MLAB-project/Modules/comm_serial/I2CHUB01A/README.md

[Czech](./README.cs.md)
<!--- module --->
# I2CHUB01A
<!--- Emodule --->

<!--- subtitle ---> I2C (TWI) bus HUB <!--- Esubtitle --->

I2CHUB01A

<!--- description ---> The module allow conecting multiple I2C devices together. It does not consist any configurable IO. It is a simple bus multiplyer.<!--- Edescription --->
