MLAB-project/Modules/human_interface/LEDROBOT/README.cs.md

[English](./README.md)
<!--- module --->
# LEDROBOT
<!--- Emodule --->

<!--- subtitle --->Sloupec LED diod<!--- Esubtitle --->

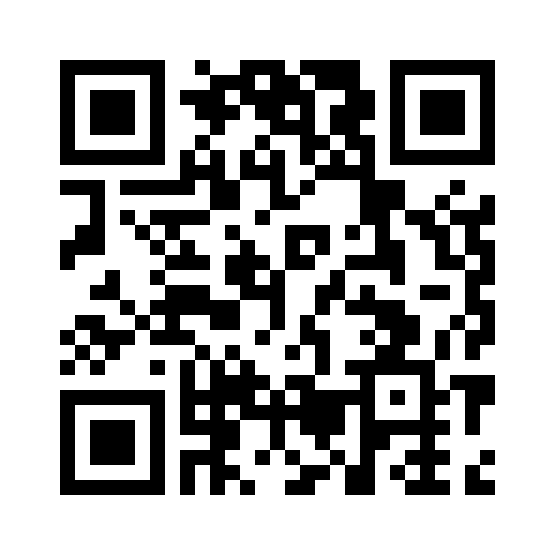
[picture p7: human_interface/LEDROBOT/doc/img/LEDROBOT_QRcode.png]
LEDROBOT


<!--- description --->Modul obsahuje piezo, napětový stabilizátor, vypínač a rozvod 5V napájení.<!--- Edescription --->
