MLAB-project/Modules/human_interface/LEDROBOT/README.md

[Czech](./README.cs.md)
<!--- module --->
# LEDROBOT
<!--- Emodule --->

<!--- subtitle --->Simple robot power control and LED indicator unit <!--- Esubtitle --->

LEDROBOT

<!--- description --->This module contain switch, LEDs, voltage regulator, beeper and 5V power hub.<!--- Edescription --->
