MLAB-project/Modules/power_supply/TPS63000/README.md

[Czech](./README.cs.md)
<!--- module --->
# TPS63000
<!--- Emodule --->

<!--- subtitle ---> UP/DOWN converter <!--- Esubtitle --->

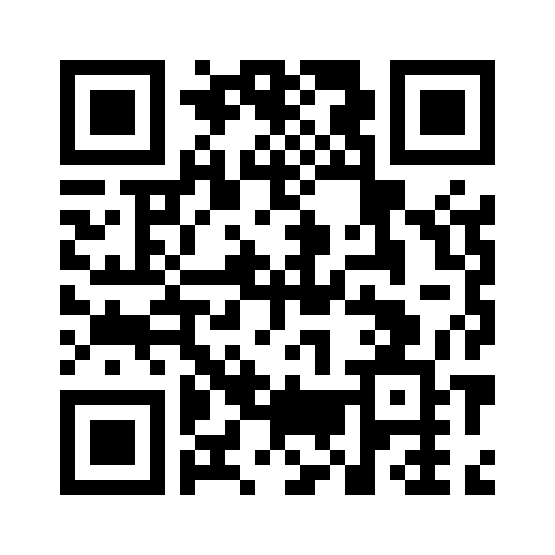
[picture p8: power_supply/TPS63000/doc/img/TPS63000_QRcode.png]
TPS63000


<!--- description ---> High efficiency switched adjustable power unit step-down and step-up in one module.<!--- Edescription --->
