MLAB-project/Modules/power_supply/TPS61200/README.md

[Czech](./README.cs.md)
<!--- module --->
# TPS61200
<!--- Emodule --->

<!--- subtitle ---> UP/DOWN converter <!--- Esubtitle --->

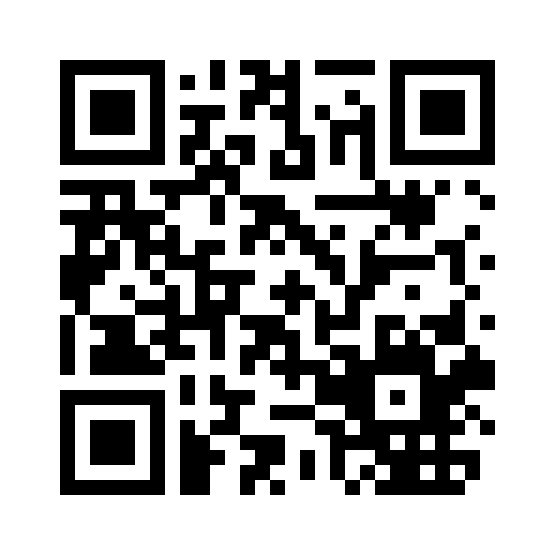
[picture p9: power_supply/TPS61200/doc/img/TPS61200_QRcode.png]
TPS61200


<!--- description ---> Switched adjustable power unit step-down and step-up in one module.<!--- Edescription --->
