MLAB-project/Modules/power_supply/TPS61170/README.md

[Czech](./README.cs.md)
<!--- module --->
# TPS61170
<!--- Emodule --->

<!--- subtitle ---> Step-up converter <!--- Esubtitle --->

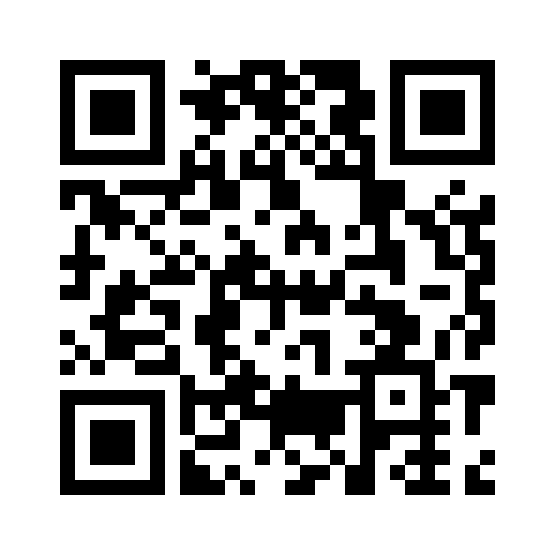
[picture p10: power_supply/TPS61170/doc/img/TPS61170_QRcode.png]
TPS61170


<!--- description ---> Switched adjustable DC/DC power unit.<!--- Edescription --->
