MLAB-project/Modules/power_supply/MAX1797/README.cs.md

[English](./README.md)
<!--- module --->
# MAX1797
<!--- Emodule --->

<!--- subtitle ---> Step-up měnič<!--- Esubtitle --->

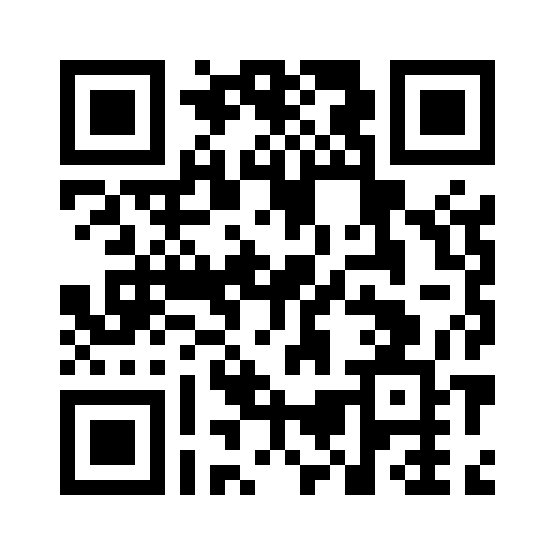
[picture p11: power_supply/MAX1797/doc/img/MAX1797_QRcode.png]
MAX1797


<!--- description ---> Zvyšující spínaný napájecí modul do 5V 1A.<!--- Edescription --->
