MLAB-project/Modules/power_supply/MAX1797/README.md

[Czech](./README.cs.md)
<!--- module --->
# MAX1797
<!--- Emodule --->

<!--- subtitle ---> Step-up converter <!--- Esubtitle --->

MAX1797

<!--- description ---> Switched power unit up to 5V and 1A.<!--- Edescription --->
