MLAB-project/Modules/cpld_fpga/S3AN01A/README.md

<!--- PrjInfo ---> <!--- Please remove this line after manually editing --->
<!--- 00a56be08b96043df9e37d6aff7b6990 --->
<!--- Created:20170112-18:22: ---> 
<!--- Author:Mlab: ---> 
<!--- AuthorEmail:mlab@mlab.cz: ---> 
<!--- Tags:imported: ---> 
<!--- Ust:None: ---> 
<!--- Name:S3AN01A: --->
#S3AN01A 
<!--- LongName --->
Xilinx Spartan 3 XC3S50AN FPGA School Board
<!--- ELongName ---> 

<!--- Lead --->
Replaced by an updated version S3AN01B. <br>

  The school board allows interested people to play with FPGA
  from XILINX. The board contains LED display, some switches
  and push buttons. It has VGA video port, PS/2 ports for
  keyboard and mouse. Because the main chip is not 5V tolerant,
  the board is equipped with 5V tolerant buffers (inputs).
  The board is powered from 5V, internal power supply is included.
  For timing there is one 100MHz crystal oscillator.
<!--- ELead ---> 

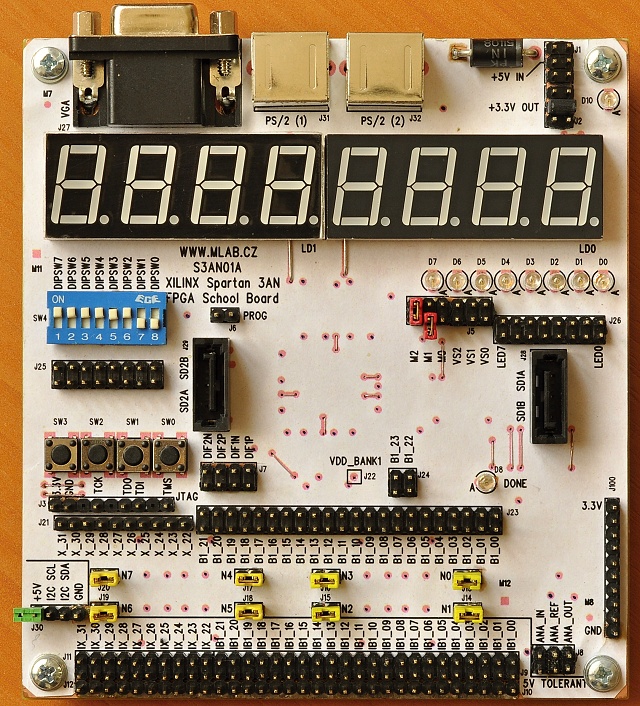
[picture p12: cpld_fpga/S3AN01A/S3AN01A_top_small.jpg]
LeadImg
 

<!--- Description --->
<!--- EDescription --->
<!--- Content --->
<!--- EContent --->
