MLAB-project/Modules/cpld_fpga/S6AN01A/README.md

<!--- PrjInfo ---> <!--- Please remove this line after manually editing --->
<!--- 00a56be08b96043df9e37d6aff7b6990 --->
<!--- Created:20170112-18:22: ---> 
<!--- Author:Mlab: ---> 
<!--- AuthorEmail:mlab@mlab.cz: ---> 
<!--- Tags:imported: ---> 
<!--- Ust:None: ---> 
<!--- Name:S6AN01A: --->
#S6AN01A 
<!--- LongName --->
Xilinx Spartan 6  XC6SLX9T FPGA Developing Board
<!--- ELongName ---> 

<!--- Lead --->
FPGA development module for basic signal and data processing. This breakout board differs from other constructions by high number of differential pairs take out to LVDS or LVPECL connectors.
<!--- ELead ---> 

<!--- Description --->
<!--- EDescription --->
<!--- Content --->
<!--- EContent --->
