MLAB-project/Modules/tdc/GP201A/README.md

<!--- PrjInfo ---> <!--- Please remove this line after manually editing --->
<!--- 00a56be08b96043df9e37d6aff7b6990 --->
<!--- Created:20170112-18:22: ---> 
<!--- Author:Mlab: ---> 
<!--- AuthorEmail:mlab@mlab.cz: ---> 
<!--- Tags:imported: ---> 
<!--- Ust:None: ---> 
<!--- Name:GP201A: --->
#GP201A 
<!--- LongName --->
Basic Time to Digital converter
<!--- ELongName ---> 

<!--- Lead --->
Measure time intervals up to 4us with precision 65ps. Also is capable for measure temperature (with 16bit resolution) if module is connected to temperature sensor such as PT1000.
<!--- ELead ---> 

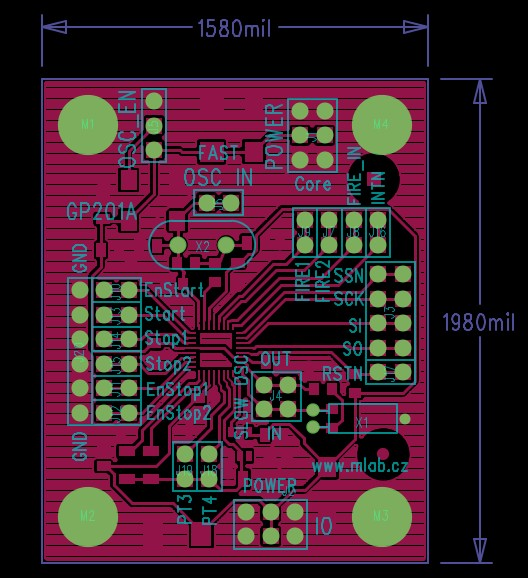
[picture p13: tdc/GP201A/GP201A_top_small.jpg]
LeadImg
 

<!--- Description --->
<!--- EDescription --->
<!--- Content --->
<!--- EContent --->
