MLAB-project/Modules/mechanical/boxes/UNIBOX01A/README.md

<!--- PrjInfo ---> <!--- Please remove this line after manually editing --->
<!--- 00a56be08b96043df9e37d6aff7b6990 --->
<!--- Created:2019-02-25 12:30:32.921918: ---> 
<!--- Author:: ---> 
<!--- AuthorEmail:: ---> 
<!--- Tags:: ---> 
<!--- Ust:: ---> 
<!--- Label --->
<!--- ELabel ---> 
<!--- Name:UNIBOX01A: --->
# UNIBOX01A
<!--- LongName --->
## Permanent device housing box
<!--- ELongName ---> 

<!--- Lead --->
Universal metal module housing box with interchangeable front and back panels. Useful for housing construction of devices created from MLAB modules.
<!--- ELead ---> 

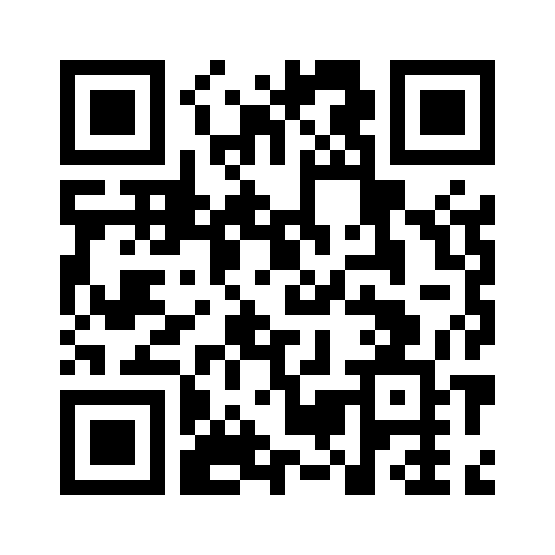
[picture p14: mechanical/boxes/UNIBOX01A/doc/img/UNIBOX01A_QRcode.png]
UNIBOX01A
 

<!--- Description --->
<!--- EDescription --->
<!--- Content --->
<!--- EContent --->
<sub><sup> Generated with [MLABweb](https://github.com/MLAB-project/MLABweb). (2019-02-25)</sup></sub>
