MLAB-project/Modules/mechanical/boxes/UNIBOX03A/README.md

<!--- PrjInfo ---> <!--- Please remove this line after manually editing --->
<!--- 00a56be08b96043df9e37d6aff7b6990 --->
<!--- Created:2019-02-18 14:53:15.430617: ---> 
<!--- Author:: ---> 
<!--- AuthorEmail:: ---> 
<!--- Tags:: ---> 
<!--- Ust:: ---> 
<!--- Label --->
<!--- ELabel ---> 
<!--- Name:UNIBOX03A: --->
# UNIBOX03A
<!--- LongName --->
## ermanent device housing box
<!--- ELongName ---> 

<!--- Lead --->
Universal metal module housing box with interchangeable front and back panels. Useful for housing construction of devices created from MLAB modules. With a pair of sidewalls printable 3D printer. Dimensions 220x160x51.5 mm.
<!--- ELead ---> 

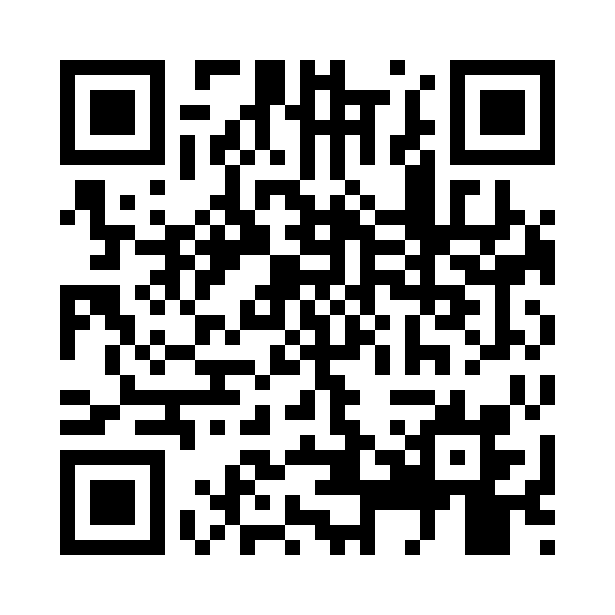
[picture p15: mechanical/boxes/UNIBOX03A/doc/img/UNIBOX03A_QRcode.png]
UNIBOX03A
 

<!--- Description --->
<!--- EDescription --->
<!--- Content --->
<!--- EContent --->
<sub><sup> Generated with [MLABweb](https://github.com/MLAB-project/MLABweb). (2019-02-18)</sup></sub>
