MLAB-project/Modules/mechanical/boxes/UNIBOX04A/README.md

<!--- PrjInfo ---> <!--- Please remove this line after manually editing --->
<!--- 00a56be08b96043df9e37d6aff7b6990 --->
<!--- Created:2019-02-18 14:52:45.538267: ---> 
<!--- Author:: ---> 
<!--- AuthorEmail:: ---> 
<!--- Tags:: ---> 
<!--- Ust:: ---> 
<!--- Label --->
<!--- ELabel ---> 
<!--- Name:UNIBOX04A: --->
# UNIBOX04A
<!--- LongName --->
## ermanent device housing box
<!--- ELongName ---> 

<!--- Lead --->
Universal metal module housing box with interchangeable front and back panels. Useful for housing construction of devices created from MLAB modules. With a pair of sidewalls printable 3D printer. Dimensions 103x120x53 mm.
<!--- ELead ---> 

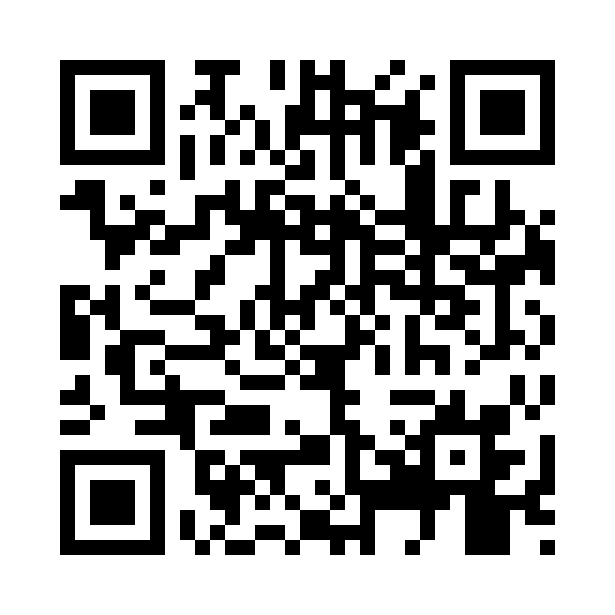
[picture p16: mechanical/boxes/UNIBOX04A/doc/img/UNIBOX04A_QRcode.png]
UNIBOX04A
 

<!--- Description --->
<!--- EDescription --->
<!--- Content --->
<!--- EContent --->
<sub><sup> Generated with [MLABweb](https://github.com/MLAB-project/MLABweb). (2019-02-18)</sup></sub>
