MLAB-project/Modules/mechanical/boxes/UNIBOX04A/README.cs.md

[English](./README.md)
<!--- module --->
# UNIBOX03A
<!--- Emodule --->

<!--- subtitle --->rabička pro permanentní konstrukce<!--- Esubtitle --->

![UNIBOX03A]()

<!--- description --->Univerzální kovová krabička pro zakrytování permanentních konstrukcí z modulů MLAB. S dvojicí tisknutelných bočnic na 3D tiskárně. Rozměry 220x160x51.5 mm. <!--- Edescription --->
