MLAB-project/Modules/mechanical/boxes/BASEBOX01A/README.md

[Czech](./README.cs.md)
<!--- module --->
# BASEBOX01A
<!--- Emodule --->

<!--- subtitle --->3D printable device housing box<!--- Esubtitle --->

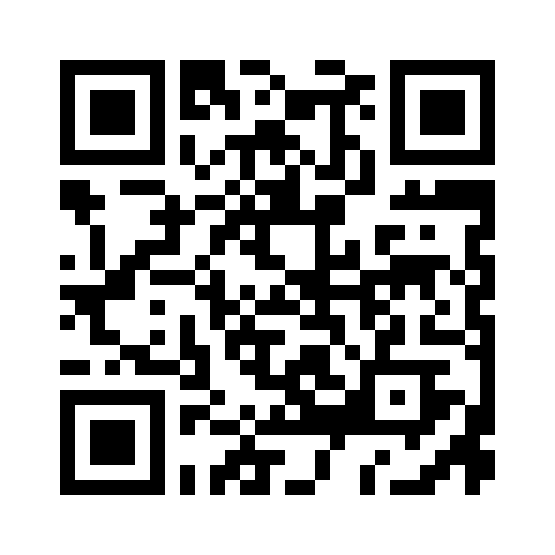
[picture p17: mechanical/boxes/BASEBOX01A/doc/img/BASEBOX01A_QRcode.png]
BASEBOX01A


<!--- description --->The printed plastic parts are sandwiched between standard hole-grid plates which makes the enclosure very rigid. The box sides can be easily customized for individual project needs, or separately exchanged during an instrument development.<!--- Edescription --->
