MLAB-project/Modules/mechanical/boxes/BASEBOX03A/README.md

[Czech](./README.cs.md)
<!--- module --->
# BASEBOX03A
<!--- Emodule --->

<!--- subtitle --->3D printable device housing box<!--- Esubtitle --->

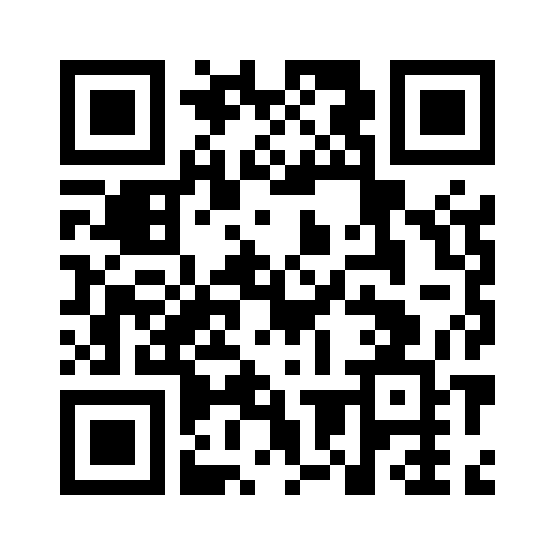
[picture p18: mechanical/boxes/BASEBOX03A/doc/img/BASEBOX03A_QRcode.png]
BASEBOX03A


<!--- description --->The printed plastic parts are sandwiched between standard hole-grid plates which makes the enclosure very rigid. The box sides can be easily customized for individual project needs, or separately exchanged during an instrument development.<!--- Edescription --->
