MLAB-project/Modules/mechanical/boxes/BASEBOX02A/README.md

[Czech](./README.cs.md)
<!--- module --->
# BASEBOX02A
<!--- Emodule --->

<!--- subtitle --->3D printable device housing box<!--- Esubtitle --->

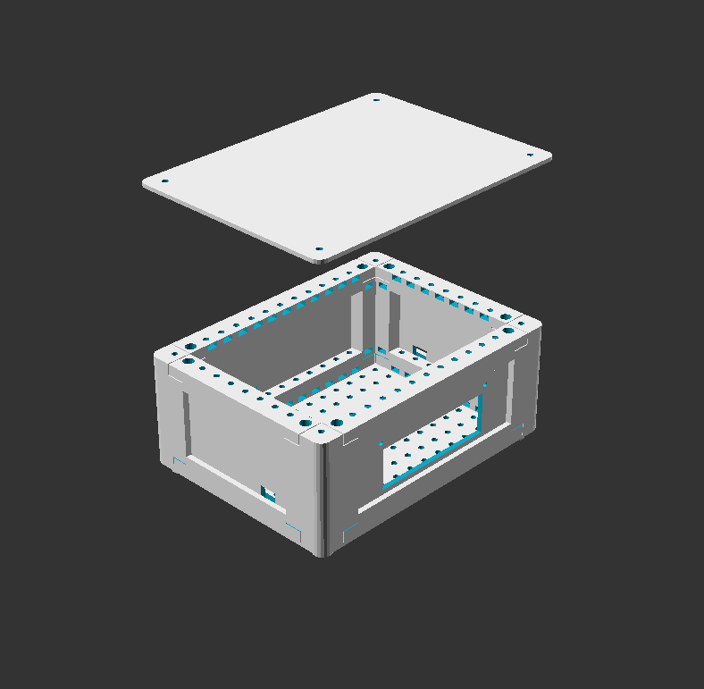
[picture p19: mechanical/boxes/BASEBOX02A/doc/img/Box_view.png]
BASEBOX02A


<!--- description --->The printed plastic parts are sandwiched between standard hole-grid plates which makes the enclosure very rigid. The box sides can be easily customized for individual project needs, or separately exchanged during an instrument development.<!--- Edescription --->
