MLAB-project/Modules/MCU_CPU/ARM/ODROID-XU4/README.md

[Czech](./README.cs.md)
<!--- module --->
# ODROID-XU4
<!--- Emodule --->

<!--- subtitle --->Eight core ARM computer module<!--- Esubtitle --->

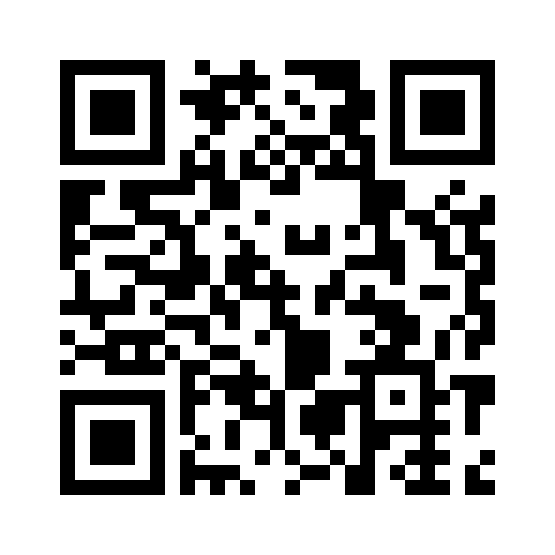
[picture p21: MCU_CPU/ARM/ODROID-XU4/doc/img/ODROID-XU4_QRcode.png]
ODROID-XU4


<!--- description --->Computer module for applications which needs full Linux operating system and lot of computing power. It is suitable for machine control or home automation as example.<!--- Edescription --->
