MLAB-project/Modules/MCU_CPU/ARM/ODROID-C2/README.md

[Czech](./README.cs.md)
<!--- module --->
# ODROID-C2
<!--- Emodule --->

<!--- subtitle --->Four core 64bit ARM computer module<!--- Esubtitle --->

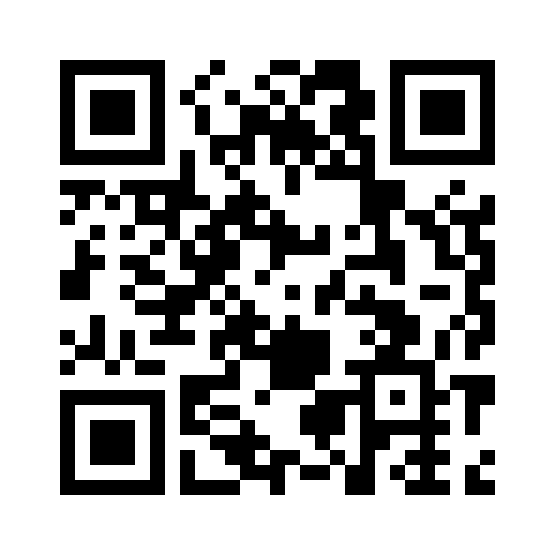
[picture p22: MCU_CPU/ARM/ODROID-C2/doc/img/ODROID-C2_QRcode.png]
ODROID-C2


<!--- description --->Computer module for applications which needs full Linux operating system and lot of computing power. It is suitable for machine control or home automation as example.<!--- Edescription --->
