MLAB-project/Modules/CPLD_FPGA/XILINX_XVC/XVC_FT220X01A/README.md

<!--- PrjInfo ---> <!--- Please remove this line after manually editing --->
<!--- 00a56be08b96043df9e37d6aff7b6990 --->
<!--- Created:20170112-18:22: ---> 
<!--- Author:Mlab: ---> 
<!--- AuthorEmail:mlab@mlab.cz: ---> 
<!--- Tags:imported: ---> 
<!--- Ust:None: ---> 
<!--- Name:XVC_FT220X01A: --->
#XVC_FT220X01A 
<!--- LongName --->
Xilinx Virtual (JTAG) Cable with FTDI FT220X chip
<!--- ELongName ---> 

<!--- Lead --->
XVC JTAG programming cable for downloading and debug projects
  with XILINX FPGA/CPLD device. It is directly supported by ISE
  design software (and Chipscope as well). The design software
  sends commands across network to the computer with this cable
  attached to it and supporting software sends data to JTAG
  interface. This XVC cable is based on a cheap FTDI FT220X chip.
<!--- ELead ---> 

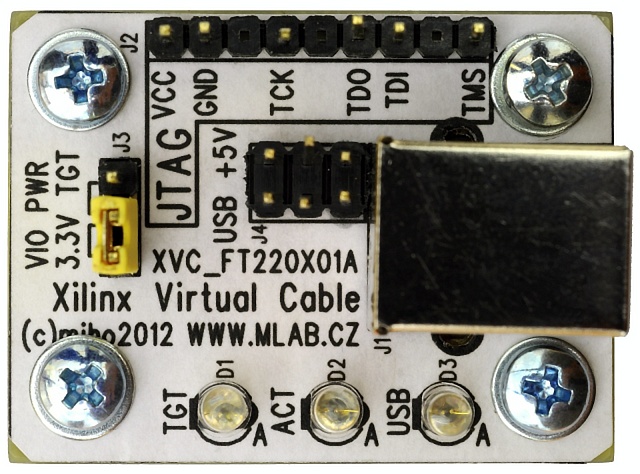
[picture p23: CPLD_FPGA/XILINX_XVC/XVC_FT220X01A/XVC_FT220X01A_Top_Small.JPG]
LeadImg
 

<!--- Description --->
<!--- EDescription --->
<!--- Content --->
<!--- EContent --->
