MLAB-project/Modules/MCU_CPU/ARM/ODROID-U3/README.md

<!--- PrjInfo ---> <!--- Please remove this line after manually editing --->
<!--- 00a56be08b96043df9e37d6aff7b6990 --->
<!--- Created:20170112-18:22: ---> 
<!--- Author:Mlab: ---> 
<!--- AuthorEmail:mlab@mlab.cz: ---> 
<!--- Tags:imported: ---> 
<!--- Ust:[End]: ---> 
<!--- Name:ODROID-U3: --->
#ODROID-U3 
<!--- LongName --->
Four core ARM computer module
<!--- ELongName ---> 

<!--- Lead --->
Computer module for applications which needs full Linux operating system and lot of computing power. It is suitable for machine control or home automation as example.
<!--- ELead ---> 

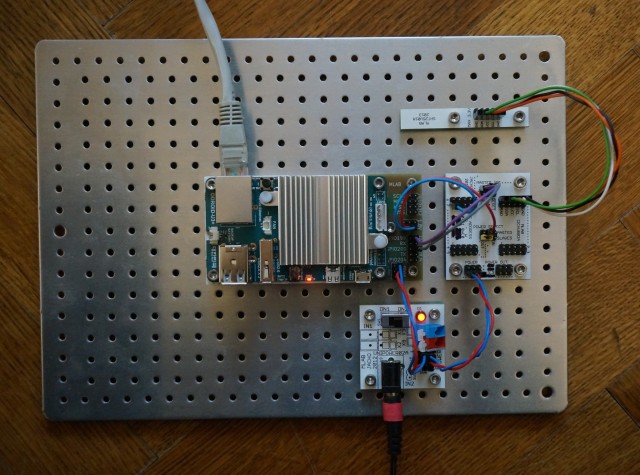
[picture p25: MCU_CPU/ARM/ODROID-U3/ODROIDU3_top_small.jpg]
LeadImg
 

<!--- Description --->
<!--- EDescription --->
<!--- Content --->
<!--- EContent --->
