MLAB-project/Modules/MCU_CPU/ARM/ODroid-X2/README.md

<!--- PrjInfo ---> <!--- Please remove this line after manually editing --->
<!--- 00a56be08b96043df9e37d6aff7b6990 --->
<!--- Created:20170112-18:22: ---> 
<!--- Author:Mlab: ---> 
<!--- AuthorEmail:mlab@mlab.cz: ---> 
<!--- Tags:imported: ---> 
<!--- Ust:[End]: ---> 
<!--- Name:ODroid-X2: --->
#ODroid-X2 
<!--- LongName --->
ARM computer module
<!--- ELongName ---> 

<!--- Lead --->
Computer module for control applications in which computing power is desired. 1.7GHz Quad core ARM Cortex-A9 MPCore, 2GB Memory, Linux operating system.
<!--- ELead ---> 

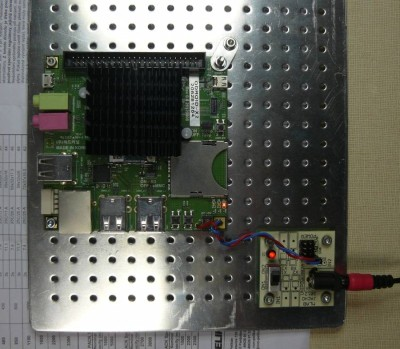
[picture p26: MCU_CPU/ARM/ODroid-X2/ODroid-X2_top_small.jpg]
LeadImg
 

<!--- Description --->
<!--- EDescription --->
<!--- Content --->
<!--- EContent --->
