MLAB-project/Modules/MCU_CPU/ARM/Raspberry/RPi/README.md

<!--- PrjInfo ---> <!--- Please remove this line after manually editing --->
<!--- 00a56be08b96043df9e37d6aff7b6990 --->
<!--- Created:20170112-18:22: ---> 
<!--- Author:Mlab: ---> 
<!--- AuthorEmail:mlab@mlab.cz: ---> 
<!--- Tags:imported: ---> 
<!--- Ust:[End]: ---> 
<!--- Name:RPi: --->
#RPi 
<!--- LongName --->
Raspberry Pi MLAB assimilation
<!--- ELongName ---> 

<!--- Lead --->
Documents and design files describing a mothod how to use classic Raspberries Pi in MLAB prototyping system.
<!--- ELead ---> 

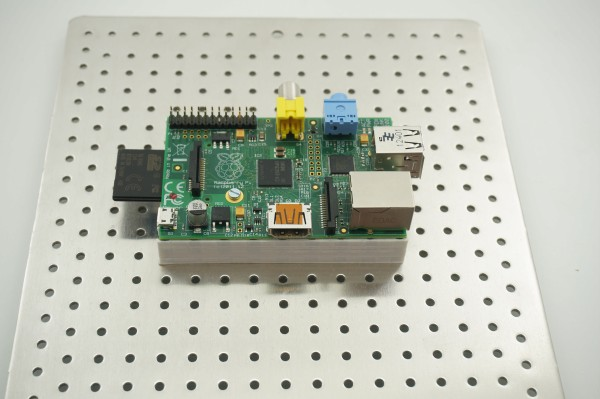
[picture p27: MCU_CPU/ARM/Raspberry/RPi/Raspberry_ALBASE_top_small.jpg]
LeadImg
 

<!--- Description --->
<!--- EDescription --->
<!--- Content --->
<!--- EContent --->
