MLAB-project/Modules/MCU_CPU/ARM/Raspberry/RPi3/README.md

<!--- PrjInfo ---> <!--- Please remove this line after manually editing --->
<!--- 00a56be08b96043df9e37d6aff7b6990 --->
<!--- Created:20170112-18:22: ---> 
<!--- Author:Mlab: ---> 
<!--- AuthorEmail:mlab@mlab.cz: ---> 
<!--- Tags:imported: ---> 
<!--- Ust:[End]: ---> 
<!--- Name:RPi3: --->
#RPi3 
<!--- LongName --->
Raspberry Pi 3 MLAB assimilation
<!--- ELongName ---> 

<!--- Lead --->
Documents and design files describing a mothod how to use classic Raspberry Pi 3 in MLAB prototyping system.
<!--- ELead ---> 

LeadImg 

<!--- Description --->
<!--- EDescription --->
<!--- Content --->
<!--- EContent --->
