MLAB-project/Modules/cpld_fpga/S6AN01A/PrjInfo.txt

[InfoShortDescription.en]
  Xilinx Spartan 6  XC6SLX9T FPGA Developing Board

[InfoShortDescription.cs]
  Vývojový modul s FPGA Xilinx Spartan 6 XC6SLX9T 

[InfoLongDescription.en]
FPGA development module for basic signal and data processing. This breakout board differs from other constructions by high number of differential pairs take out to LVDS or LVPECL connectors. 

[InfoLongDescription.cs]
FPGA vývojová deska pro základní zpracování signálů. Od běžných vývojových desek se odlišuje hlavně zvýšeným množstvím diferenčňích kanálů vyvedených na konektory. 

[End]
