MLAB-project/Modules/CPLD_FPGA/XILINX_XVC/DirInfo.txt

//
// Toto je popisný soubor pro popis obsahu adresáře
//

[InfoShortDescription.en]
  Xilinx Virtual Cable

[InfoShortDescription.cs]
  Xilinx Virtual Cable
  
[InfoLongDescription.en]
  Xilinx Virtual Cable (XVC in short) technology is based on fact
  that the JTAG communication is send across TCP/IP network.
  On the other site there is program which is sending JTAG command
  to the connected interface. Network protocol is documented and
  it is directly supported in ISE and ChipScope development SW.
  So it is easy to integrate own JTAG interface fully integrated
  into development SW.

[InfoLongDescription.cs]
  Xilinx Virtual Cable (ve zkratce XVC) je technologie spočívající
  v tom, že vývojové nástroje přesměrovávají komunikaci s JTAG
  programovacím kabelem přes TCP/IP síť. Na druhé straně sítě
  běží obslužný program, který zajišťuje provádění JTAG příkazů
  prostřednictvím (nějakého) hardwaru připojeného ke vzdálenému systému.
  Síťový protokol je dokumentovaný a jeho podpora je vestavěna
  ve vývojovém balíku ISE pro práci s FPGA a CPLD firmy Xilinx.
  Lze tak snadno realizovat navázání vlastní varianty JTAG rozhraní
  do standardních vývojových nástrojů (ISE i ChipScope).

[SortPreferences]

[End]
