MLAB-project/Modules/MCU_CPU/ARM/DirInfo.txt

//
// Toto je popisný soubor pro popis obsahu adresáře
//

[InfoShortDescription.en]
  Modules for ARM processors

[InfoShortDescription.cs]
  Moduly pro procesory ARM
  
[InfoLongDescription.en]
  Modules for powerful 32-bit Reduced Instruction Set Computer ARM processors.
  
[InfoLongDescription.cs]
  Moduly pro výkonné 32bit RISC procesory ARM.

[SortPreferences]

[End]
