MLAB-project/Modules/power_supply/MAX1797/PrjInfo.txt

//
// Toto je popisný soubor pro popis obsahu adresáře (příklad)
//

[InfoShortDescription.en]
  Step-up converter
  
[InfoShortDescription.cs]
  Step-up měnič

[InfoLongDescription.en]
  Switched power unit up to 5V and 1A.

[InfoLongDescription.cs]
  Zvyšující spínaný napájecí modul do 5V 1A.

[End]
