MLAB-project/Modules/power_supply/TPS61170/PrjInfo.txt

//
// Toto je popisný soubor pro popis obsahu adresáře (příklad)
//

[InfoShortDescription.en]
  Step-up converter
  
[InfoShortDescription.cs]
  Step-up měnič

[InfoLongDescription.en]
  Switched adjustable DC/DC power unit.

[InfoLongDescription.cs]
  Zvyšující DC/DC spínaný napájecí modul.

[End]
