MLAB-project/Modules/power_supply/TPS61200/PrjInfo.txt

//
// Toto je popisný soubor pro popis obsahu adresáře (příklad)
//

[InfoShortDescription.en]
  UP/DOWN converter
  
[InfoShortDescription.cs]
  Zvyšující i znižující měnič

[InfoLongDescription.en]
  Switched adjustable power unit step-down and step-up in one module.

[InfoLongDescription.cs]
  Spínaný napájecí modul automaticky přepíná mezi step-down a step-up režimem.

[End]
