MLAB-project/Modules/power_supply/TPS63000/PrjInfo.txt

//
// Toto je popisný soubor pro popis obsahu adresáře (příklad)
//

[InfoShortDescription.en]
  UP/DOWN converter
  
[InfoShortDescription.cs]
  Zvyšující i znižující měnič

[InfoLongDescription.en]
  High efficiency switched adjustable power unit step-down and step-up in one module.

[InfoLongDescription.cs]
  Vysoce účinný spínaný napájecí modul automaticky přepíná mezi step-down a step-up režimem.

[End]
