MLAB-project/Modules/sensors/MMA6260/PrjInfo.txt

[InfoShortDescription.en]
Simple 2axis analog accelerometer sensor

[InfoShortDescription.cs]
Dvouosý Analogový akcelerometr

[InfoLongDescription.en]

[InfoLongDescription.cs]
Modul dvouosého akcelerometru s analogovým výstupem a integrovaným napěťovým stabilizátorem. Možnost přímého připojení k mikroporocesoru.
[End]
