MLAB-project/Modules/human_interface/LEDROBOT/PrjInfo.txt

//
// This is a project description file.
//

[InfoShortDescription.en]
Simple robot power control and LED indicator unit 
  
[InfoShortDescription.cs]
Sloupec LED diod

[InfoLongDescription.en]
This module contain switch, LEDs, voltage regulator, beeper and 5V power hub.

[InfoLongDescription.cs]
Modul obsahuje piezo, napětový stabilizátor, vypínač a rozvod 5V napájení.

[End]
