MLAB-project/Modules/sensors/barometr/PrjInfo.txt

[InfoShortDescription.en]
Barometric sensor

[InfoShortDescription.cs]
Snímač atmosférického tlaku

[InfoLongDescription.en]

[InfoLongDescription.cs]
Malý digitální barometr s čipem MS5534A.
[End]
