MLAB-project/Modules/sensors/G-metr/PrjInfo.txt

[InfoShortDescription.en]
Simple 1axis analog accelerometer sensor

[InfoShortDescription.cs]
Jednoosý Analogový akcelerometr

[InfoLongDescription.en]

[InfoLongDescription.cs]
Modul alcelerometru s analogovým výstupem napájení 5V. Možnost přímého připojení k mikroporocesoru.
[End]
