MLAB-project/Modules/power_sw/NFET2x2/PrjInfo.txt

//
// This is a project description file.
//

[InfoShortDescription.en]
2x2NFET Power Driver
  
[InfoShortDescription.cs]
2x2NFET výkonový budič

[InfoLongDescription.en]
There are 4 NFETs switching to earth. Inductive load is allowed.

[InfoLongDescription.cs]
Modul slouží jako čtyřnásobný výkonový budič se spínáním do
země. Spínaná zátěž může mít indukční charakter.

[End]
