MLAB-project/Modules/MCU_CPU/PIC/DirInfo.txt

//
// Toto je popisný soubor pro popis obsahu adresáře
//

[InfoShortDescription.en]
  Microchip PIC Processors

[InfoShortDescription.cs]
  Procesory Microchip PIC
  
[InfoLongDescription.en]
  Modules for Microchip PIC Processors. They are low power
  devices.
  
[InfoLongDescription.cs]
  Moduly pro oblíbené procesory PIC od firmy Microchip.
  Procesory PIC se vyznačují nízkou spotřebou.

[SortPreferences]

[End]
