MLAB-project/Modules/Measuring/TTLPROBE01A/info.cs.txt

Logická sonda slouží k zobrazování logických stavů H a L a neurčitého stavu X TTL logiky na třech LED. Logická sonda zobrazuje krátké impulsy na vstupu tak, aby byly viditelné.
