MLAB-project/Modules/MCU_CPU/ARM/ODROID-C2/PrjInfo.txt

[InfoShortDescription.en]
Four core 64bit ARM computer module

[InfoShortDescription.cs]
Počítač se čtyřjádrovým 64bit ARM procesorem

[InfoLongDescription.en]
Computer module for applications which needs full Linux operating system and lot of computing power. It is suitable for machine control or home automation as example.

[InfoLongDescription.cs]
Počítač s nízkou spotřebou vhodný pro kontrolní a řídící aplikace, kde je potřebný velký výpočetní výkon a plnohodnotný operační systém Linux. Je vhodný například pro řízení strojů, nebo automatizaci domácnosti.

[InfoBuyUST]

[End]
