MLAB-project/Modules/MCU_CPU/x86/Galileo/PrjInfo.txt

[InfoShortDescription.en]
Intel Galileo breakout frame

[InfoShortDescription.cs]
Intel Galileo breakout frame

[InfoLongDescription.en]

[InfoLongDescription.cs]

[End]
