MLAB-project/Modules/MCU_CPU/ARM/ODroid-X2/PrjInfo.txt

[InfoShortDescription.en]
ARM computer module

[InfoShortDescription.cs]
Počítač s ARM

[InfoLongDescription.en]
Computer module for control applications in which computing power is desired. 1.7GHz Quad core ARM Cortex-A9 MPCore, 2GB Memory, Linux operating system.
 
[InfoLongDescription.cs]
Počítač s nízkou spotřebou vhodný pro kontrolní a řídící aplikace, kde je potřebný velký výpočetní výkon. Čtyřjádrový ARM Cortex-A9 MPCore 1.7GHz, 2GB operační paměti, Ubuntu.

[InfoBuyUST]

[End]
