MLAB-project/Modules/CPLD_FPGA/XILINX_XVC/XVC_FT220X02A/PrjInfo.txt

//
// Toto je popisný soubor pro popis obsahu adresáře (příklad)
//

[InfoShortDescription.en]
  Xilinx Virtual (JTAG) Cable with FTDI FT220X chip
  
[InfoShortDescription.cs]
  Xilinx Virtual (JTAG) Cable s obvodem FTDI FT220X

[InfoLongDescription.en]
  XVC JTAG programming cable for downloading and debug projects
  with XILINX FPGA/CPLD device. It is directly supported by ISE
  design software (and Chipscope as well). The design software
  sends commands across network to the computer with this cable
  attached to it and supporting software sends data to JTAG
  interface. This XVC cable is based on a cheap FTDI FT220X chip.

[InfoLongDescription.cs]
  XVC JTAG programovací kabel pro nahrávání konfigurace a ladění
  zařízení s obvody FPGA/CPLD firmy XILINX. Návrhový systém ISE
  komunikuje po síti s obslužným programem, který přijaté JTAG
  příkazy odesílá prostřednictvím obvodu FTDI FT220X do obvodu
  XILINX.

[InfoBuyUST]
http://www.ust.cz/shop/product_info.php?products_id=237

[End]
