MLAB-project/Modules/MCU_CPU/ARM/Raspberry/RPi3/PrjInfo.txt

[InfoShortDescription.en]
Raspberry Pi 3 MLAB assimilation

[InfoShortDescription.cs]
Klasický počítač Raspberry Pi 3

[InfoLongDescription.en]
Documents and design files describing a mothod how to use classic Raspberry Pi 3 in MLAB prototyping system.

[InfoLongDescription.cs]
Dokumenty a zdrojové soubory popisující způsob, jak používat klasické Rasperry Pi ve stavebnici MLAB. 

[InfoBuyUST]

[End]
