MLAB-project/Modules/MCU_CPU/ARM/Raspberry/RPi/PrjInfo.txt

[InfoShortDescription.en]
Raspberry Pi MLAB assimilation

[InfoShortDescription.cs]
Klasický počítač Raspberry Pi

[InfoLongDescription.en]
Documents and design files describing a mothod how to use classic Raspberries Pi in MLAB prototyping system.

[InfoLongDescription.cs]
Dokumenty a zdrojové soubory popisující způsob, jak používat klasické Rasperry Pi ve stavebnici MLAB. 

[InfoBuyUST]

[End]
