MLAB-project/Modules/human_interface/LEDROBOT/doc/LEDrobot.cs.pdf

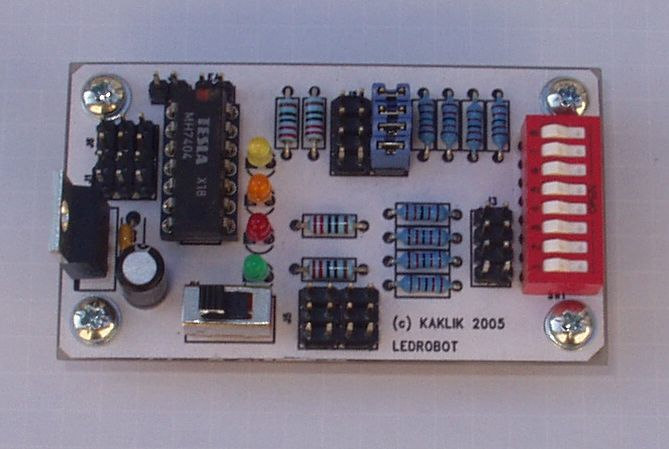
[picture p34: figure]

LEDrobot.doc / 2005-05-31 / kaklik | 1 / 3
LEDrobot | MLAB

### Modul pro napájení a jednoduchou indikaci stavu robota.Umožuje výb-

### r program v procesoru, pipojení piezo reproduktoru a ty

LED diod.

# 1. Technické parametry

Parametr | Hodnota | Poznámka
Napájení | +5V až +12V
Odebíraný proud | Max 1,5 A | Pes stabilizátor.
Vstupní úrovn- | TTL | LED svítí v log. 1
Výstupní úrovn- | TTL
Rozm-ry | 71x41x25mm

LEDrobot | MLAB

# 2. Popis konstrukce

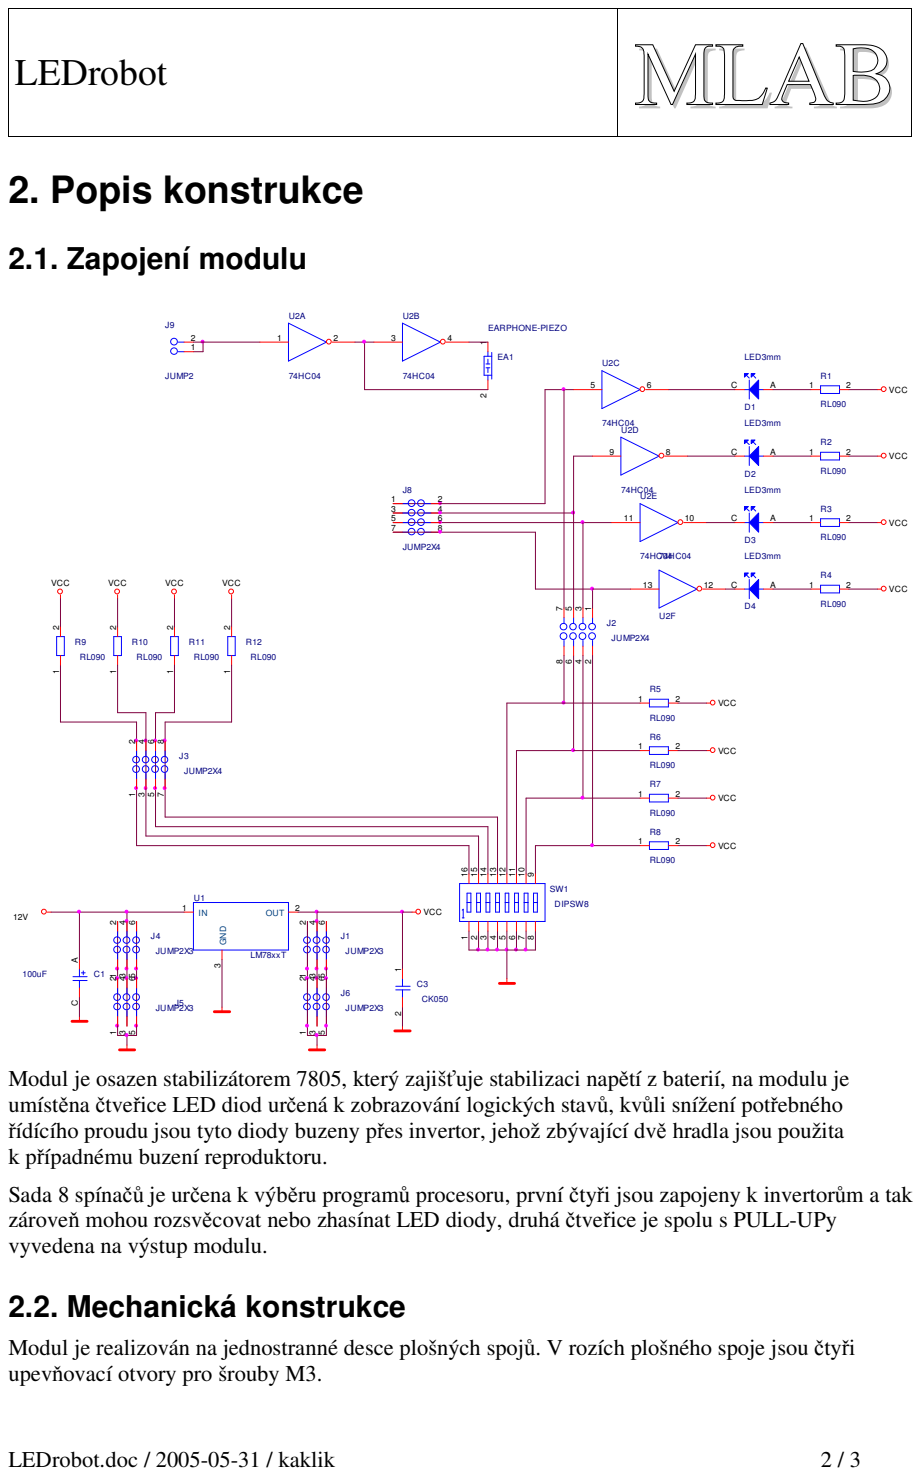
[picture p35: page 2]

Modul je osazen stabilizátorem 7805, který zajišuje stabilizaci nap-
umíst-
ídícího proudu jsou tyto diody buzeny pes invertor, jehož zbývající dv-
k pípadnému buzení reproduktoru.
Sada 8 spína je urena k výb-
zárove mohou rozsv-
vyvedena na výstup modulu.
2.2. Mechanická konstrukce
Modul je realizován na jednostranné desce plošných spoj. V rozích plošného spoje jsou tyi
upevovací otvory pro šrouby M3.

tí z baterií, na modulu je

na tveice LED diod urená k zobrazování logických stav, kvli snížení potebného

ru program procesoru, první tyi jsou zapojeny k invertorm a tak

covat nebo zhasínat LED diody, druhá tveice je spolu s PULL-UPy

LEDrobot | MLAB

# 3. Osazení a oživení

## 3.1. Osazení a seznam souástek

Modul se osazuje standardním zpsobem, od nejnižších souástek po nejvyšší.

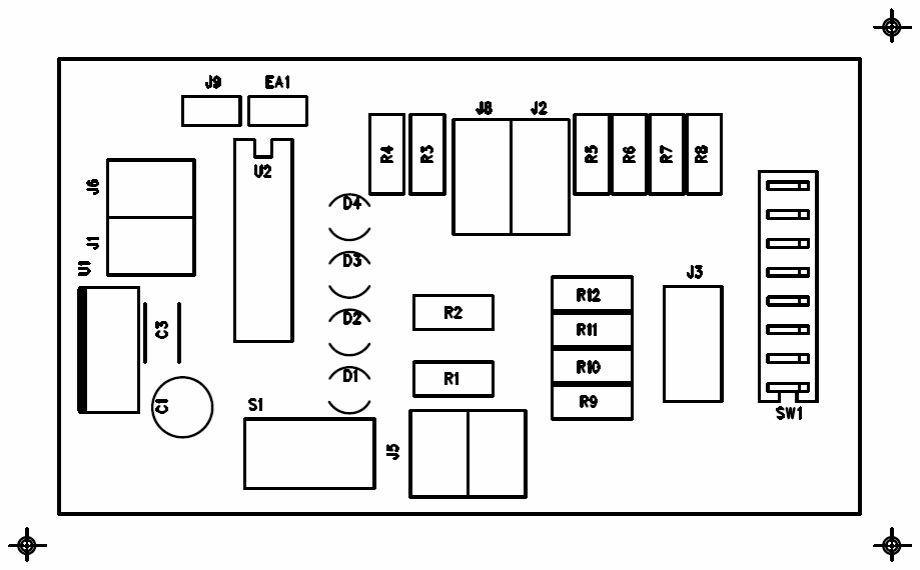
[picture p36: figure]

C1 | 100uF
C3 | 100nF
D1,D2,D3,D4 | LED3mm
EA1 | EARPHONE-PIEZO
J1,J4,J5,J6 | JUMP2X3
J2,J3,J8 | JUMP2X4
J9 | JUMP2
R1,R2,R3,R4,R5,R6,R7,R8, | 22k
R9,R10,R11,R12 | 220
SW1 | DIPSW8
U1 | LM7805
U2 | 74HC04

## 3.2. Oživení

Pokud jsou použity fungující souástky a spoje jsou správn-

provedené bude modul fungovat napoprvé. Pro jistotu je vhodné pi prvním zapnutí použít regulovatelný zdroj a pi postupném zvyšování napájecího nap-

tí zkontrolovat, zda je spoteba v rozumných mezích.
