MLAB-project/Modules/sensors/MMA6260/hw/cam_ama/V1.pdf

C:\PADS Projects\Accelerometer\MMA6260\MMA6260+11173 LDO\V1 (Current screen) Scale=1.00 Mon Jun 18 10:57:34 2007
