MLAB-project/Modules/power_supply/TPS63000/README.cs.md

[English](./README.md)
<!--- module --->
# TPS63000
<!--- Emodule --->

<!--- subtitle ---> Zvyšující i znižující měnič<!--- Esubtitle --->

TPS63000

<!--- description ---> Vysoce účinný spínaný napájecí modul automaticky přepíná mezi step-down a step-up režimem.<!--- Edescription --->
