MLAB-project/Modules/power_supply/TPS61200/README.cs.md

[English](./README.md)
<!--- module --->
# TPS61200
<!--- Emodule --->

<!--- subtitle ---> Zvyšující i znižující měnič<!--- Esubtitle --->

TPS61200

<!--- description ---> Spínaný napájecí modul automaticky přepíná mezi step-down a step-up režimem.<!--- Edescription --->
