MLAB-project/Modules/power_supply/TPS61170/README.cs.md

[English](./README.md)
<!--- module --->
# TPS61170
<!--- Emodule --->

<!--- subtitle ---> Step-up měnič<!--- Esubtitle --->

TPS61170

<!--- description ---> Zvyšující DC/DC spínaný napájecí modul.<!--- Edescription --->
