MLAB-project/Modules/mechanical/boxes/SHTBOX01A/README.md

<!--- PrjInfo ---> <!--- Please remove this line after manually editing --->
<!--- 00a56be08b96043df9e37d6aff7b6990 --->
<!--- Created:2019-02-18 15:01:06.729157: ---> 
<!--- Author:: ---> 
<!--- AuthorEmail:: ---> 
<!--- Tags:: ---> 
<!--- Ust:: ---> 
<!--- Label --->
<!--- ELabel ---> 
<!--- Name:SHTBOX01A: --->
# SHTBOX01A
<!--- LongName --->
## SHTBOX01A
<!--- ELongName ---> 

<!--- Lead --->
None
<!--- ELead ---> 

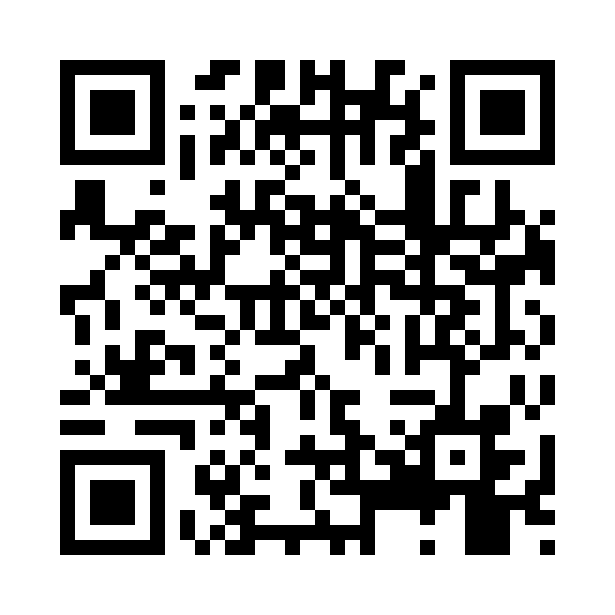
[picture p57: mechanical/boxes/SHTBOX01A/doc/img/SHTBOX01A_QRcode.png]
SHTBOX01A
 

<!--- Description --->
<!--- EDescription --->
<!--- Content --->
<!--- EContent --->
<sub><sup> Generated with [MLABweb](https://github.com/MLAB-project/MLABweb). (2019-02-18)</sup></sub>
