MLAB-project/Modules/mechanical/boxes/UNIBOX01A/README.cs.md

[English](./README.md)
<!--- module --->
# UNIBOX01A
<!--- Emodule --->

<!--- subtitle --->Krabička pro permanentní konstrukce<!--- Esubtitle --->

UNIBOX01A

<!--- description --->Univerzální kovová krabička pro zakrytování permanentních konstrukcí z modulů MLAB. <!--- Edescription --->
