MLAB-project/Modules/mechanical/boxes/BASEBOX01A/README.cs.md

[English](./README.md)
<!--- module --->
# BASEBOX01A
<!--- Emodule --->

<!--- subtitle --->3D tisknutelná krabička pro permanentní konstrukce<!--- Esubtitle --->

BASEBOX01A

<!--- description --->Univerzální krabička tisknutelná 3D tiskárnou pro zakrytování permanentních konstrukcí z modulů MLAB. <!--- Edescription --->
