MLAB-project/Modules/mechanical/boxes/AWSBOX01A/README.cs.md

[English](./README.md)
<!--- module --->
# AWSBOX01A
<!--- Emodule --->

<!--- subtitle --->AWSBOX01A<!--- Esubtitle --->

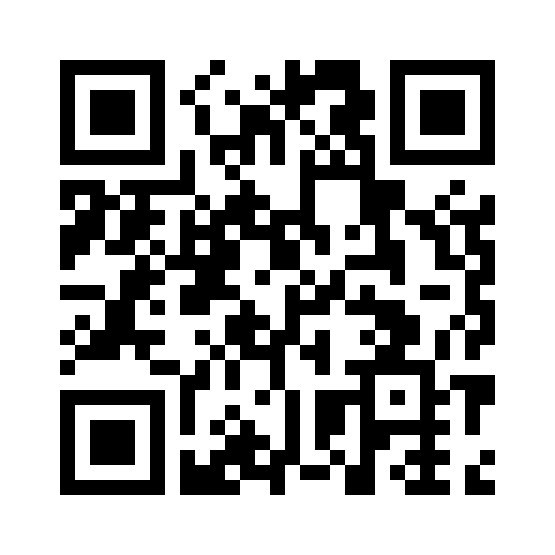
[picture p58: mechanical/boxes/AWSBOX01A/doc/img/AWSBOX01A_QRcode.png]
AWSBOX01A


<!--- description --->None<!--- Edescription --->
