MLAB-project/Modules/mechanical/boxes/BASEBOX03A/README.cs.md

[English](./README.md)
<!--- module --->
# BASEBOX03A
<!--- Emodule --->

<!--- subtitle --->3D tisknutelná krabička pro permanentní konstrukce<!--- Esubtitle --->

BASEBOX03A

<!--- description --->Univerzální krabička tisknutelná 3D tiskárnou pro zakrytování permanentních konstrukcí z modulů MLAB. <!--- Edescription --->
