MLAB-project/Modules/mechanical/boxes/BASEBOX02A/README.cs.md

[English](./README.md)
<!--- module --->
# BASEBOX02A
<!--- Emodule --->

<!--- subtitle --->3D tisknutelná krabička pro permanentní konstrukce<!--- Esubtitle --->

BASEBOX02A

<!--- description --->Univerzální krabička tisknutelná 3D tiskárnou pro zakrytování permanentních konstrukcí z modulů MLAB.<!--- Edescription --->
