MLAB-project/Modules/MCU_CPU/ARM/ODROID-XU4/README.cs.md

[English](./README.md)
<!--- module --->
# ODROID-XU4
<!--- Emodule --->

<!--- subtitle --->Počítač se osmi-jádrovým ARM procesorem<!--- Esubtitle --->

ODROID-XU4

<!--- description --->Počítač s nízkou spotřebou vhodný pro kontrolní a řídící aplikace, kde je potřebný velký výpočetní výkon a plnohodnotný operační systém Linux. Je vhodný například pro řízení strojů, nebo automatizaci domácnosti.<!--- Edescription --->
