MLAB-project/Modules/MCU_CPU/ARM/ODROID-C2/README.cs.md

[English](./README.md)
<!--- module --->
# ODROID-C2
<!--- Emodule --->

<!--- subtitle --->Počítač se čtyřjádrovým 64bit ARM procesorem<!--- Esubtitle --->

ODROID-C2

<!--- description --->Počítač s nízkou spotřebou vhodný pro kontrolní a řídící aplikace, kde je potřebný velký výpočetní výkon a plnohodnotný operační systém Linux. Je vhodný například pro řízení strojů, nebo automatizaci domácnosti.<!--- Edescription --->
