MLAB-project/Modules/MCU_CPU/ARM/ODROID-C1/README.cs.md

[English](./README.md)
<!--- module --->
# ODROID-C1
<!--- Emodule --->

<!--- subtitle --->Počítač se čtyřjádrovým ARM procesorem<!--- Esubtitle --->

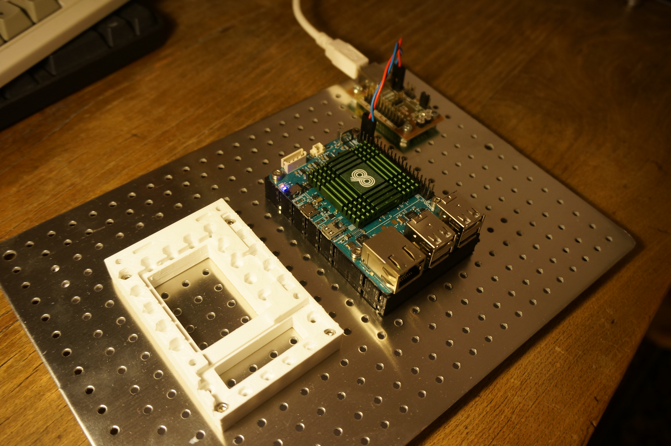
[picture p59: MCU_CPU/ARM/ODROID-C1/doc/img/ODROID-C1_top_big.jpg]
ODROID-C1


<!--- description --->Počítač s nízkou spotřebou vhodný pro kontrolní a řídící aplikace, kde je potřebný velký výpočetní výkon a plnohodnotný operační systém Linux. Je vhodný například pro řízení strojů, nebo automatizaci domácnosti.<!--- Edescription --->
