MLAB-project/Modules/CPLD_FPGA/XILINX_XVC/XVC_SOFTWARE/README.md

<!--- PrjInfo ---> <!--- Please remove this line after manually editing --->
<!--- 00a56be08b96043df9e37d6aff7b6990 --->
<!--- Created:20170112-18:22: ---> 
<!--- Author:Mlab: ---> 
<!--- AuthorEmail:mlab@mlab.cz: ---> 
<!--- Tags:imported: ---> 
<!--- Ust:None: ---> 
<!--- Name:XVC_SOFTWARE: --->
#XVC_SOFTWARE 
<!--- LongName --->
Xilinx Virtual Cable Sofware (program mlab_xvcd)
<!--- ELongName ---> 

<!--- Lead --->
The mlab_xvcd program converts JTAG commands received across TCP/IP 
  network via XVC protocol to outputs of the programming
  cable (module) which is based on FTDI's USB chips like
  popular FT232R, FT220X etc.
  Used XVC protocol is directly supported by XILINX development
  tools (both configuration tool IMPACT and debugging 
  embedded logic analyzer ChipScope Analyzer).
<!--- ELead ---> 

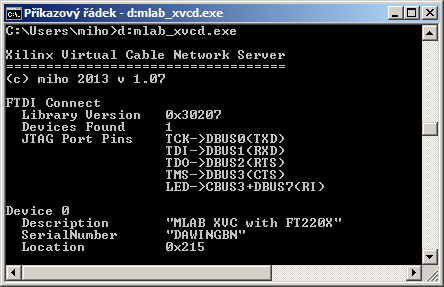
[picture p60: CPLD_FPGA/XILINX_XVC/XVC_SOFTWARE/XVC_SOFTWARE_Small.png]
LeadImg
 

<!--- Description --->
<!--- EDescription --->
<!--- Content --->
<!--- EContent --->
