MLAB-project/Modules/MCU_CPU/AVR/Text_ATosc/README.md

<!--- PrjInfo ---> <!--- Please remove this line after manually editing --->
<!--- 00a56be08b96043df9e37d6aff7b6990 --->
<!--- Created:20170112-18:22: ---> 
<!--- Author:Mlab: ---> 
<!--- AuthorEmail:mlab@mlab.cz: ---> 
<!--- Tags:imported: ---> 
<!--- Ust:None: ---> 
<!--- Name:Text_ATosc: --->
#Text_ATosc 
<!--- LongName --->
External oscillator for ATmega
<!--- ELongName ---> 

<!--- Lead --->
When you have mistakenly switched external oscillator for ATmega 
  processor you can't do anything but connect external oscillator. 
  This is how to unlock locked processor.
<!--- ELead ---> 

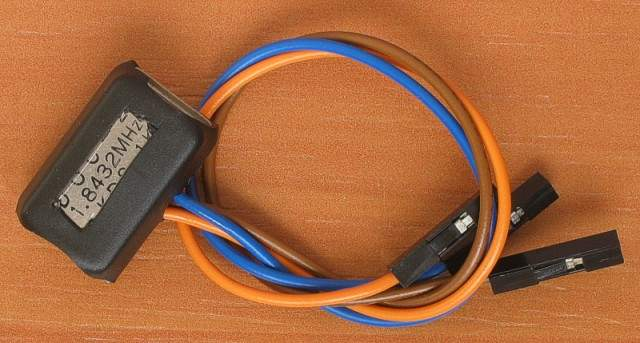
[picture p61: MCU_CPU/AVR/Text_ATosc/Osc_top_small.jpg]
LeadImg
 

<!--- Description --->
<!--- EDescription --->
<!--- Content --->
<!--- EContent --->
