MLAB-project/Modules/MCU_CPU/x86/Galileo/README.md

<!--- PrjInfo ---> <!--- Please remove this line after manually editing --->
<!--- 00a56be08b96043df9e37d6aff7b6990 --->
<!--- Created:20170112-18:22: ---> 
<!--- Author:Mlab: ---> 
<!--- AuthorEmail:mlab@mlab.cz: ---> 
<!--- Tags:imported: ---> 
<!--- Ust:None: ---> 
<!--- Name:Galileo: --->
#Galileo 
<!--- LongName --->
Intel Galileo breakout frame
<!--- ELongName ---> 

<!--- Lead --->

<!--- ELead ---> 

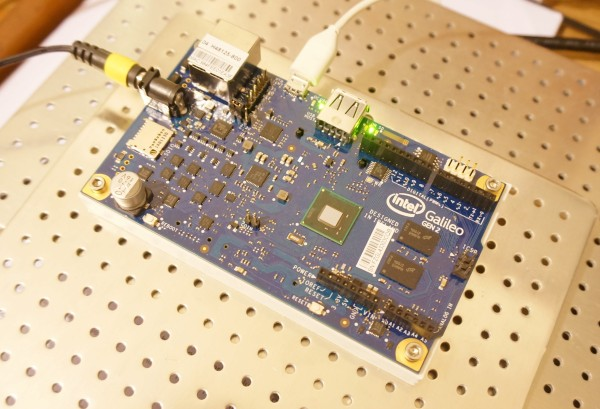
[picture p62: MCU_CPU/x86/Galileo/Intel_Galileo_top_small.jpg]
LeadImg
 

<!--- Description --->
<!--- EDescription --->
<!--- Content --->
<!--- EContent --->
