MLAB-project/Modules/power_supply/TPS61200/sch/TPS61200.pdf

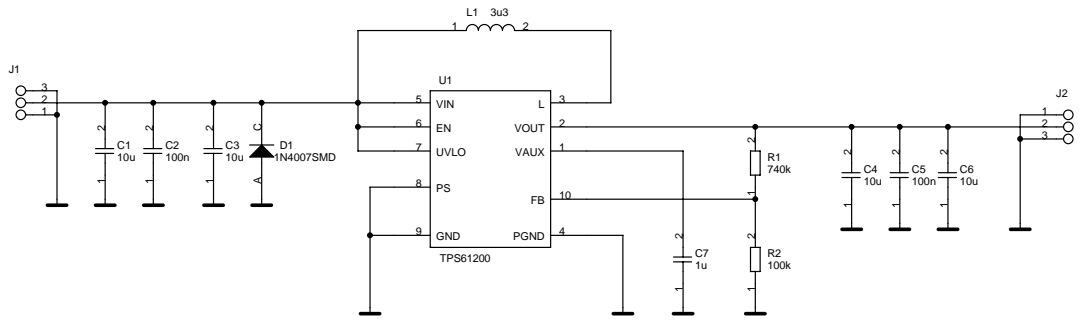
[picture p74: page 1]

Size A4 | Document Number TPS61200 | Rev 1.0

Date: Tuesday, August 18, 2009 | Sheet 1 of 1

E

D

C

B

A

5 | 4 | 3 | 2 | 1
