MLAB-project/Modules/power_supply/TPS63000/sch/TPS63000.pdf

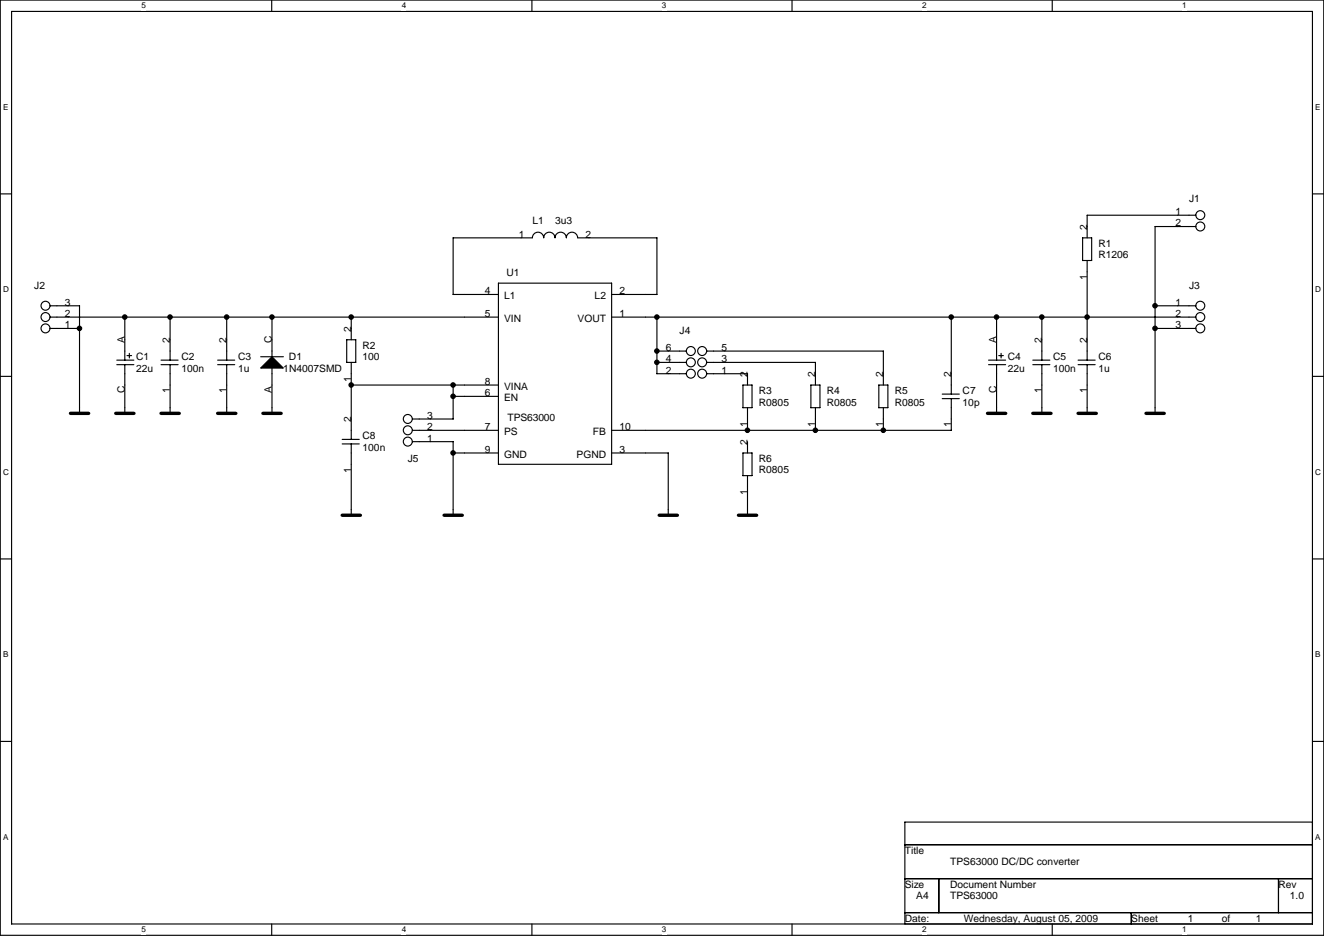
[picture p75: page 1]

Size A4 | Document Number TPS63000 | Rev 1.0

Date: Wednesday, August 05, 2009 | Sheet 1 of 1

E

D

C

B

A

5 | 4 | 3 | 2 | 1
