MLAB-project/Modules/human_interface/LEDROBOT/hw/cam_ama/LEDROBOT_V2_AMA2.pdf

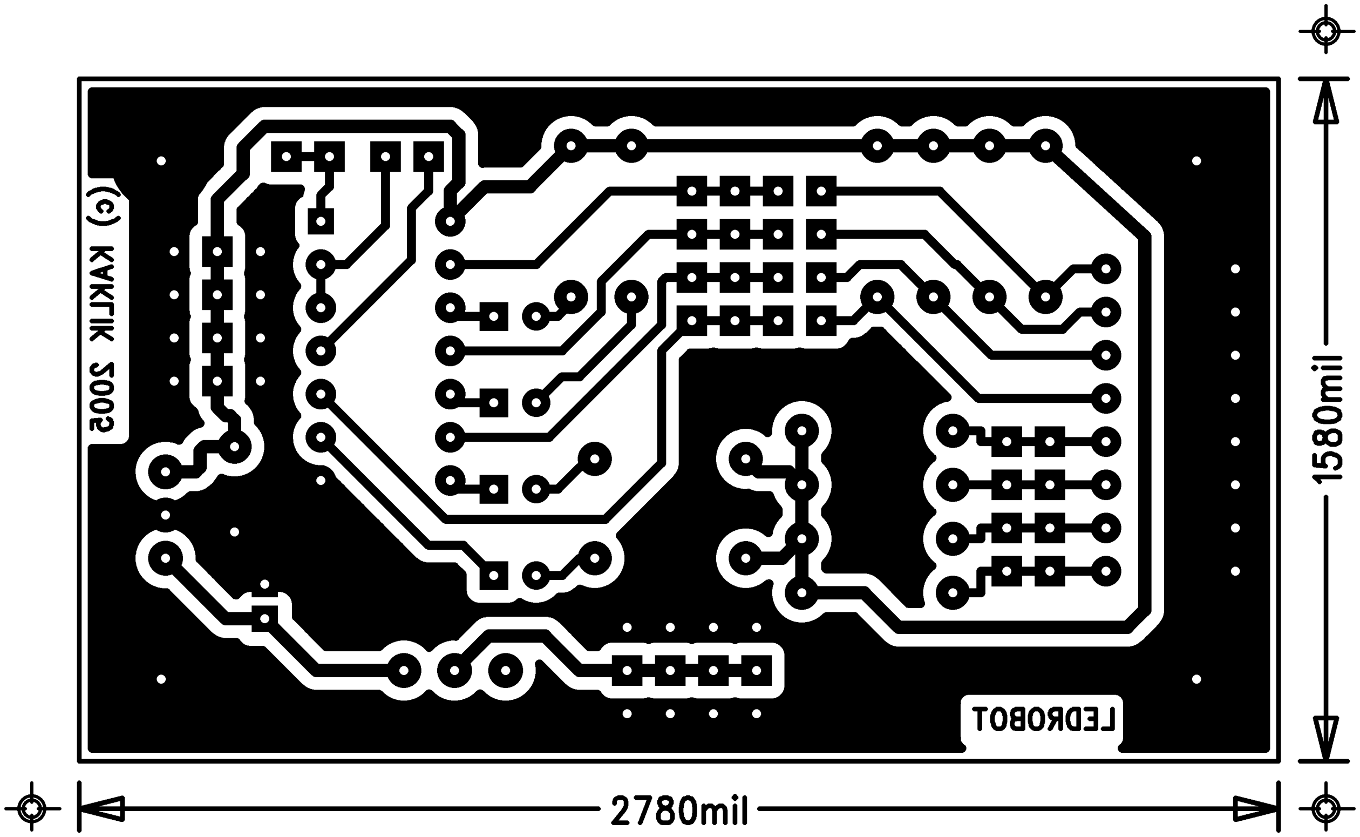
[picture p83: figure]
