MLAB-project/Modules/human_interface/LEDROBOT/hw/cam_ama/LEDROBOT_V2_REAL2.pdf

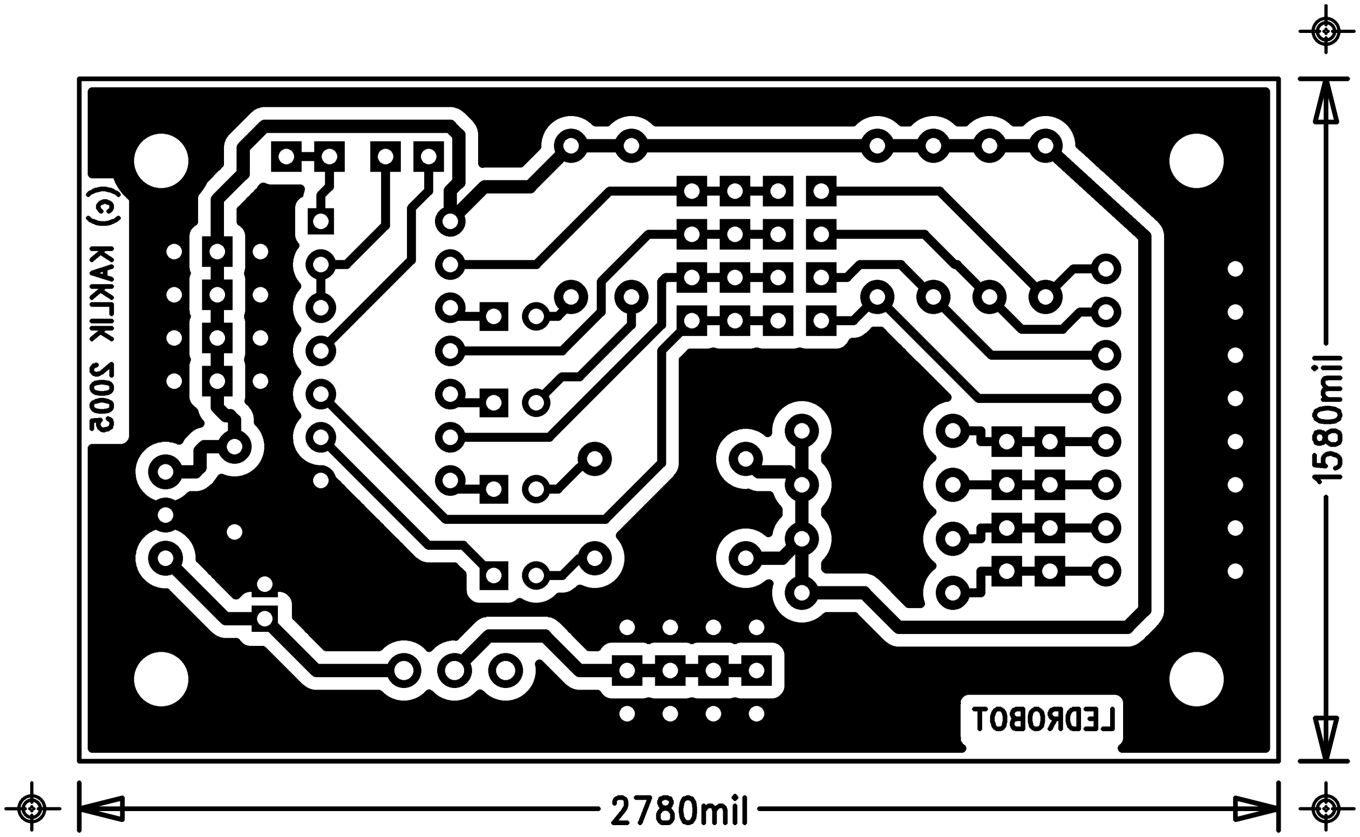
[picture p84: figure]
