MLAB-project/Modules/CPLD_FPGA/DirInfo.txt

//
// Toto je popisný soubor pro popis obsahu adresáře
//

[InfoShortDescription.en]
  Modules with CPLD or FPGA

[InfoShortDescription.cs]
  Moduly s obvody CPLD nebo FPGA
  
[InfoLongDescription.en]
  Modules for work with CPLD (Complex Programmable 
  Logic Devices) or FPGA (Field Programmable Logic).
  CPLDs are bigger brothers of well known GAL devices.
  FPGA chips contain logic and routing resources
  spread across the whole chip.

[InfoLongDescription.cs]
  Moduly pro práci s obvody programovatelné logiky
  CPLD (Complex Logical Devices) nebo FPGA (Field 
  Programmable Logic). Obvody CPLD jsou
  většími bratry obvodů GAL, Obvody FPGA mají
  rozprostřenou logiku a propojení na celém čipu.

[SortPreferences]

[End]
