MLAB-project/Modules/tdc/GP201A/PrjInfo.txt

[InfoShortDescription.en]
Basic Time to Digital converter 

[InfoShortDescription.cs]
Základní časově digitální převodník.

[InfoLongDescription.en]
Measure time intervals up to 4us with precision 65ps. Also is capable for measure temperature (with 16bit resolution) if module is connected to temperature sensor such as PT1000. 

[InfoLongDescription.cs]
Měří časové intervaly do 4us s rozlišeením 65ps. Po připojení teplotního čidla, jako například PT1000 umožňuje také měřit teplotu s 16ti bitovým rozlišením.
[End]
