MLAB-project/Modules/audio/audio_small.jpg

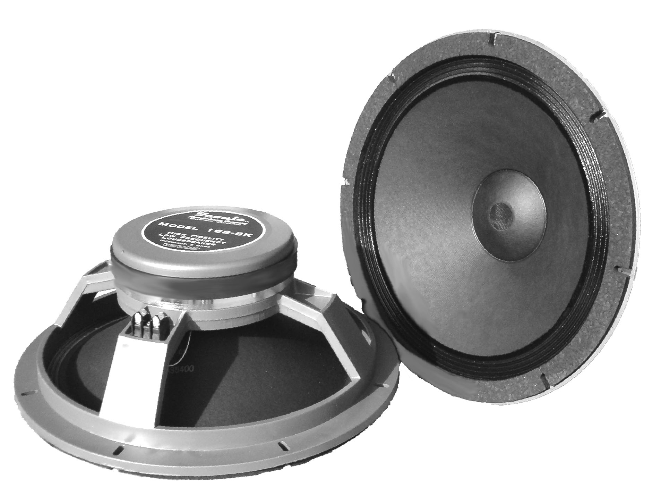
audio/audio_small.jpg
