MLAB-project/Modules/clock/clock_small.jpg

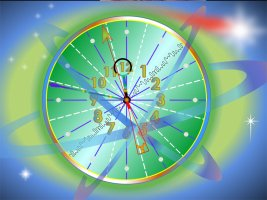
clock/clock_small.jpg
