MLAB-project/Modules/comm_serial/serial_small.jpg

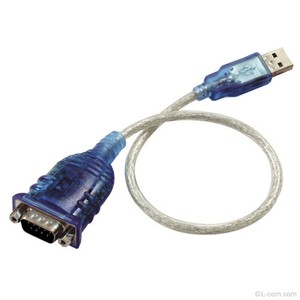
comm_serial/serial_small.jpg
