MLAB-project/Modules/CPLD_FPGA/cpld_small.jpg

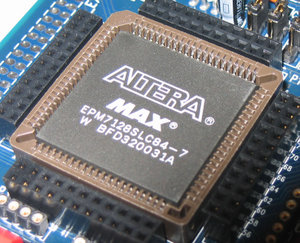
CPLD_FPGA/cpld_small.jpg
