MLAB-project/Modules/CPLD_FPGA/XILINX_XVC/XVC_FT220X01A/doc/html/XVC_FT220X01A.cs_soubory/image002.png

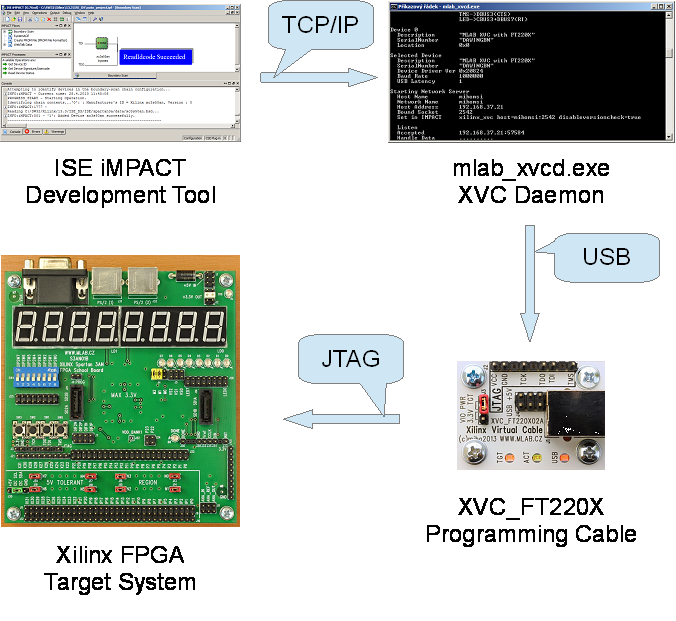
CPLD_FPGA/XILINX_XVC/XVC_FT220X01A/doc/html/XVC_FT220X01A.cs_soubory/image002.png
