MLAB-project/Modules/CPLD_FPGA/XILINX_XVC/XVC_FT220X01A/doc/img/XVC_FT220X01A_Bot_small.jpg

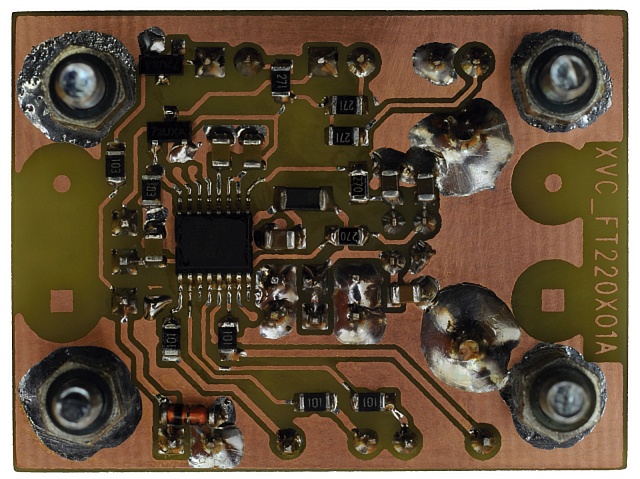
CPLD_FPGA/XILINX_XVC/XVC_FT220X01A/doc/img/XVC_FT220X01A_Bot_small.jpg
