MLAB-project/Modules/CPLD_FPGA/XILINX_XVC/XVC_FT220X02A/doc/html/XVC_FT220X02A.cs_soubory/image005.png

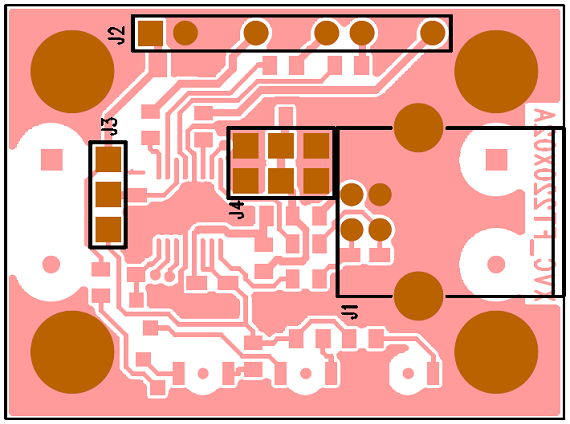
CPLD_FPGA/XILINX_XVC/XVC_FT220X02A/doc/html/XVC_FT220X02A.cs_soubory/image005.png
