MLAB-project/Modules/CPLD_FPGA/XILINX_XVC/XVC_FT220X02A/doc/img/XVC_FT220X02A_Bot_small.jpg

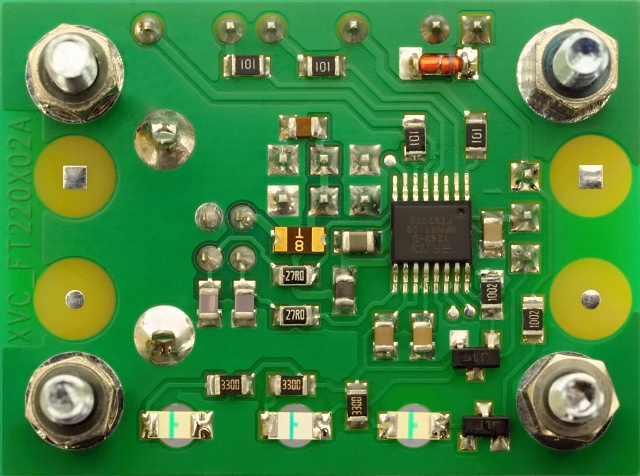
CPLD_FPGA/XILINX_XVC/XVC_FT220X02A/doc/img/XVC_FT220X02A_Bot_small.jpg
