MLAB-project/Modules/human_interface/joystick_small.jpg

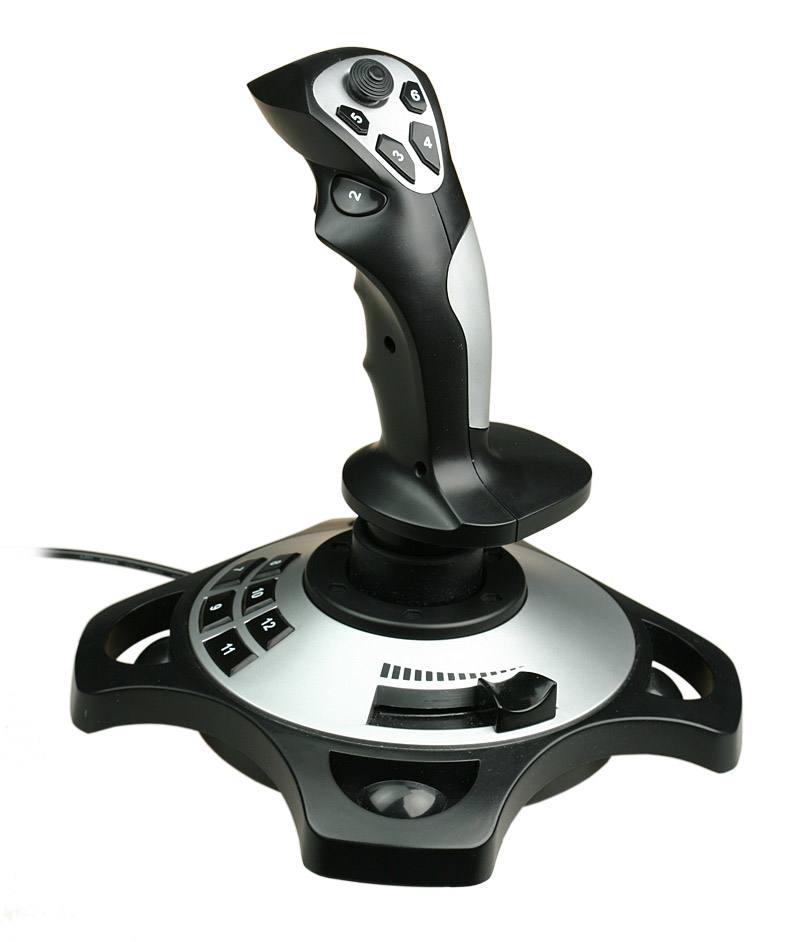
human_interface/joystick_small.jpg
