MLAB-project/Modules/human_interface/LEDROBOT/doc/img/LEDrobot_small.jpg

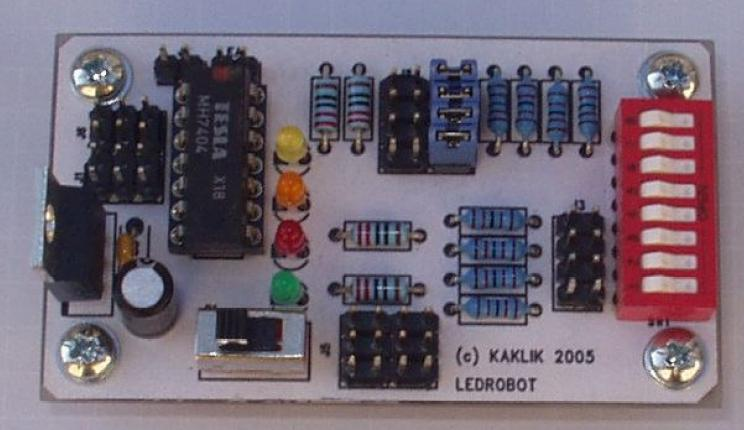
human_interface/LEDROBOT/doc/img/LEDrobot_small.jpg
