MLAB-project/Modules/human_interface/LEDROBOT/doc/src/P5260001.jpg

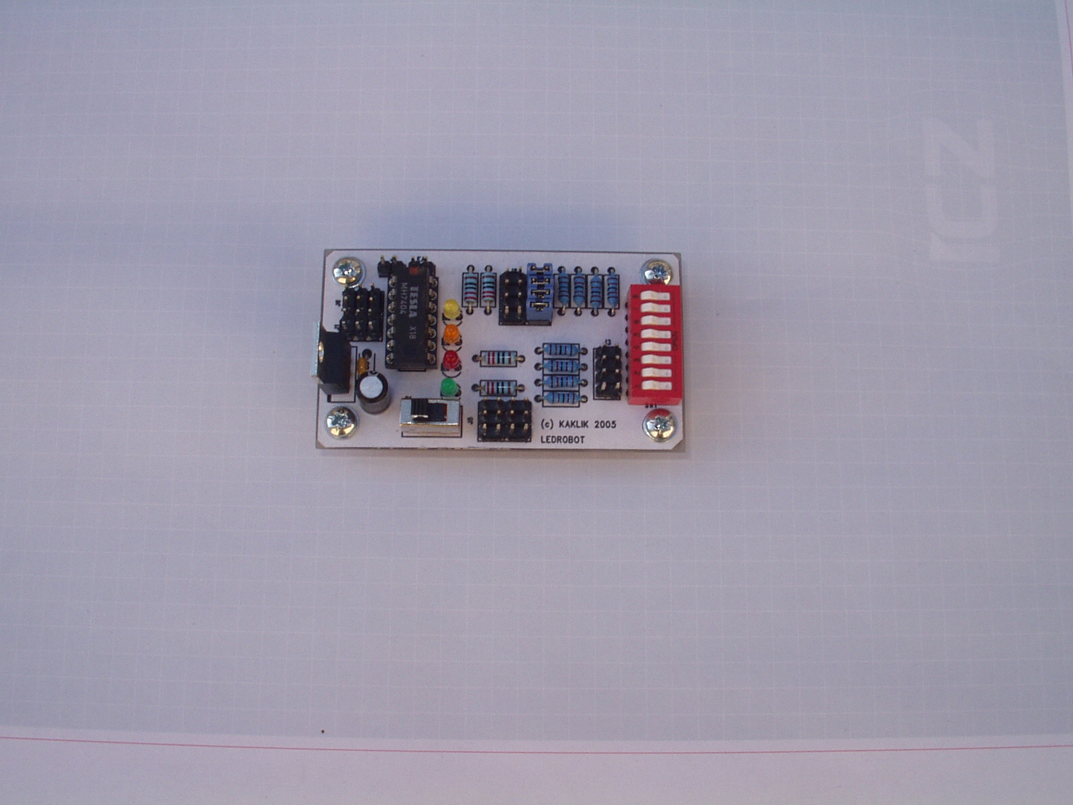
human_interface/LEDROBOT/doc/src/P5260001.jpg
