MLAB-project/Modules/IR/irda_small.jpg

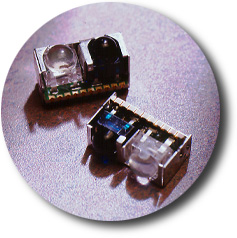
IR/irda_small.jpg
