MLAB-project/Modules/MCU_CPU/ARM/ARM_small.jpg

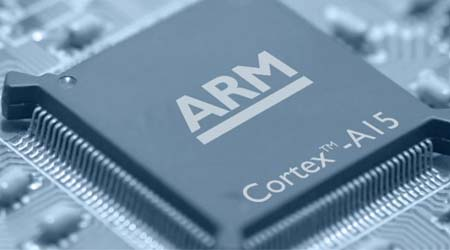
MCU_CPU/ARM/ARM_small.jpg
