MLAB-project/Modules/MCU_CPU/ARM/ODROID-C1/doc/img/flir/FLIR0233.jpg

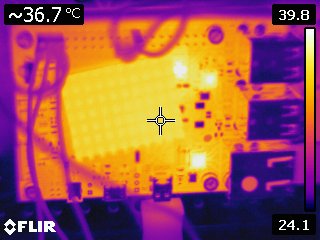
MCU_CPU/ARM/ODROID-C1/doc/img/flir/FLIR0233.jpg
