MLAB-project/Modules/MCU_CPU/ARM/ODROID-C1/doc/img/flir/FLIR0236.jpg

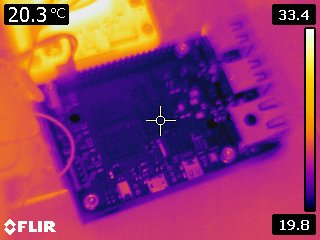
MCU_CPU/ARM/ODROID-C1/doc/img/flir/FLIR0236.jpg
