MLAB-project/Modules/MCU_CPU/ARM/ODROID-C1/doc/img/flir/FLIR0238.jpg

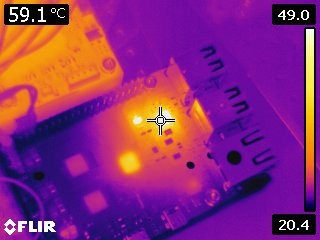
MCU_CPU/ARM/ODROID-C1/doc/img/flir/FLIR0238.jpg
