MLAB-project/Modules/MCU_CPU/ARM/ODROID-U3/doc/img/ODROIDU3_MLAB_adapter_model.png

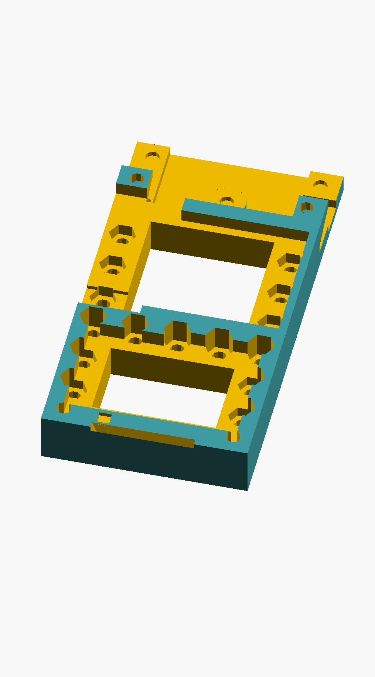
MCU_CPU/ARM/ODROID-U3/doc/img/ODROIDU3_MLAB_adapter_model.png
