MLAB-project/Modules/MCU_CPU/ARM/ODROID-U3/doc/img/ODROIDU3_MLAB_I2C_connection.jpg

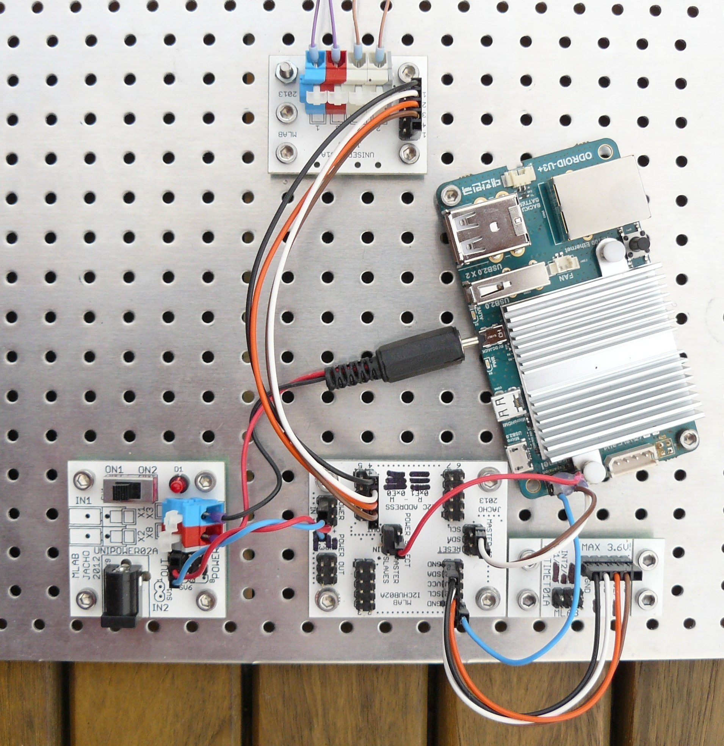
MCU_CPU/ARM/ODROID-U3/doc/img/ODROIDU3_MLAB_I2C_connection.jpg
