MLAB-project/Modules/MCU_CPU/ARM/ODroid-X2/doc/img/ODROID-X2_I2C.jpg

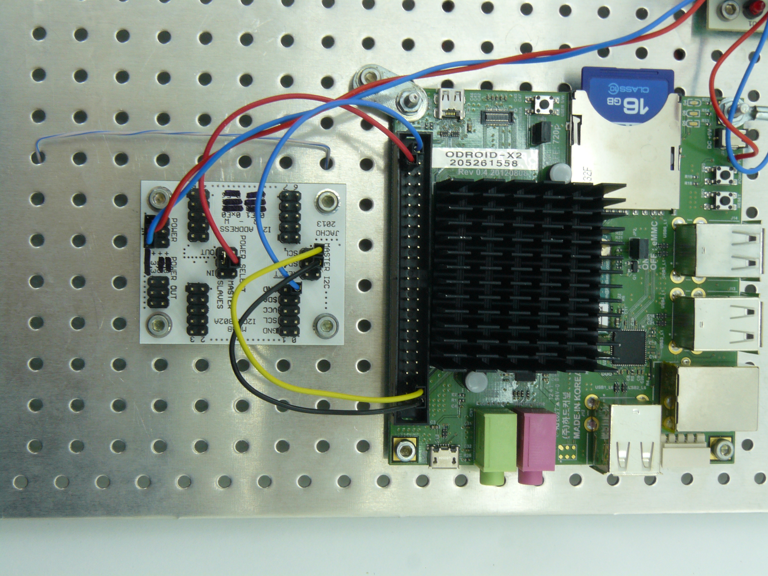
MCU_CPU/ARM/ODroid-X2/doc/img/ODROID-X2_I2C.jpg
