MLAB-project/Modules/MCU_CPU/ARM/ODROID-XU4/doc/img/ODROID-XU4_breakout_frame_big.jpg

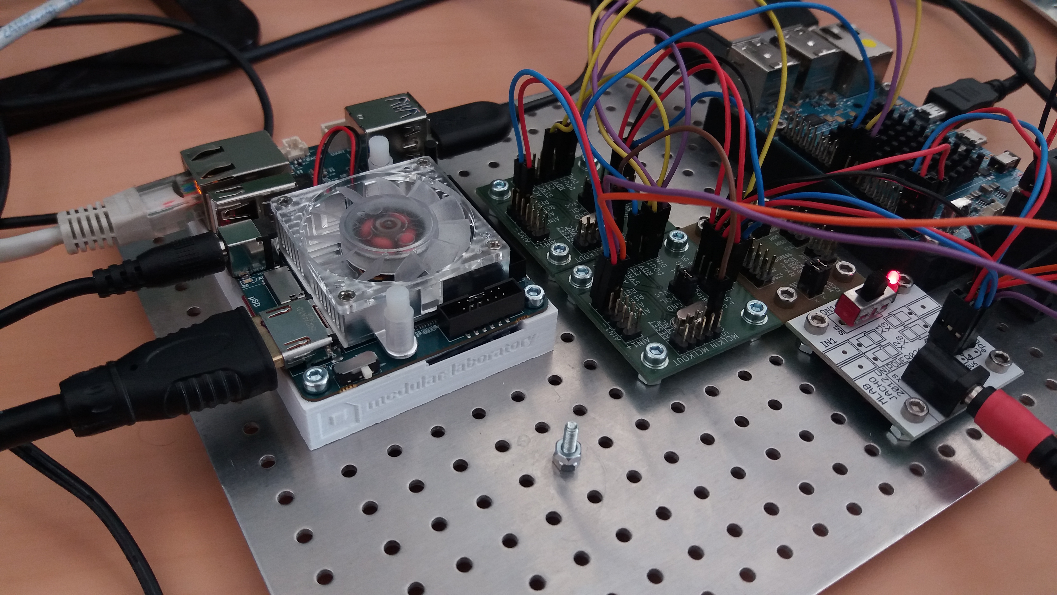
MCU_CPU/ARM/ODROID-XU4/doc/img/ODROID-XU4_breakout_frame_big.jpg
