MLAB-project/Modules/MCU_CPU/ARM/Raspberry/RPi3/doc/img/raspberry_pi_B+.jpg

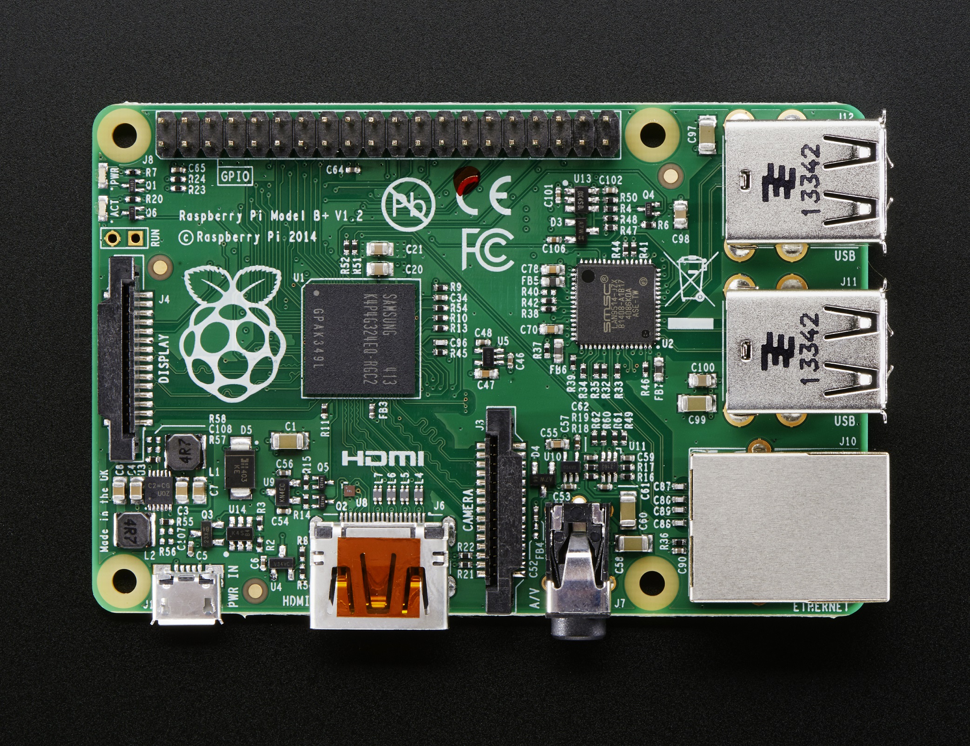
MCU_CPU/ARM/Raspberry/RPi3/doc/img/raspberry_pi_B+.jpg
