MLAB-project/Modules/MCU_CPU/ARM/Raspberry/RPi3/doc/img/raspberry_pi_breakout_frame.png

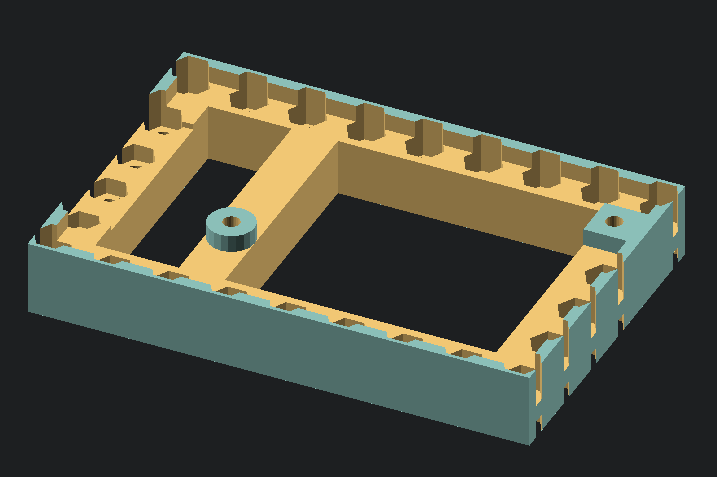
MCU_CPU/ARM/Raspberry/RPi3/doc/img/raspberry_pi_breakout_frame.png
