MLAB-project/Modules/MCU_CPU/AVR/avr_small.jpg

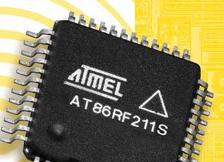
MCU_CPU/AVR/avr_small.jpg
