MLAB-project/Modules/MCU_CPU/AVR/NGW100/doc/img/P1130278.jpg

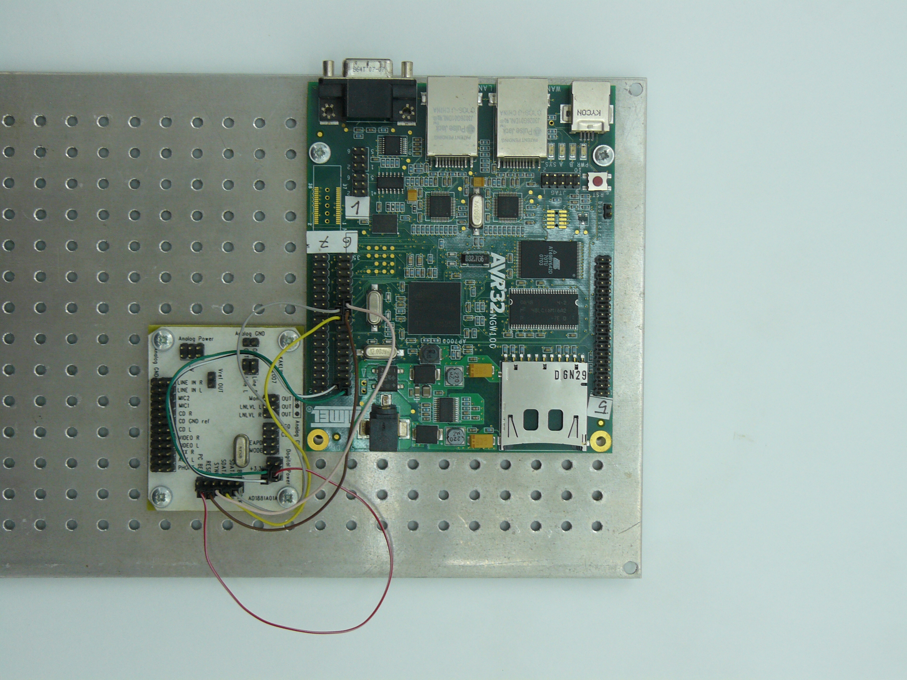
MCU_CPU/AVR/NGW100/doc/img/P1130278.jpg
