MLAB-project/Modules/MCU_CPU/AVR/NGW100/doc/img/P1130279.jpg

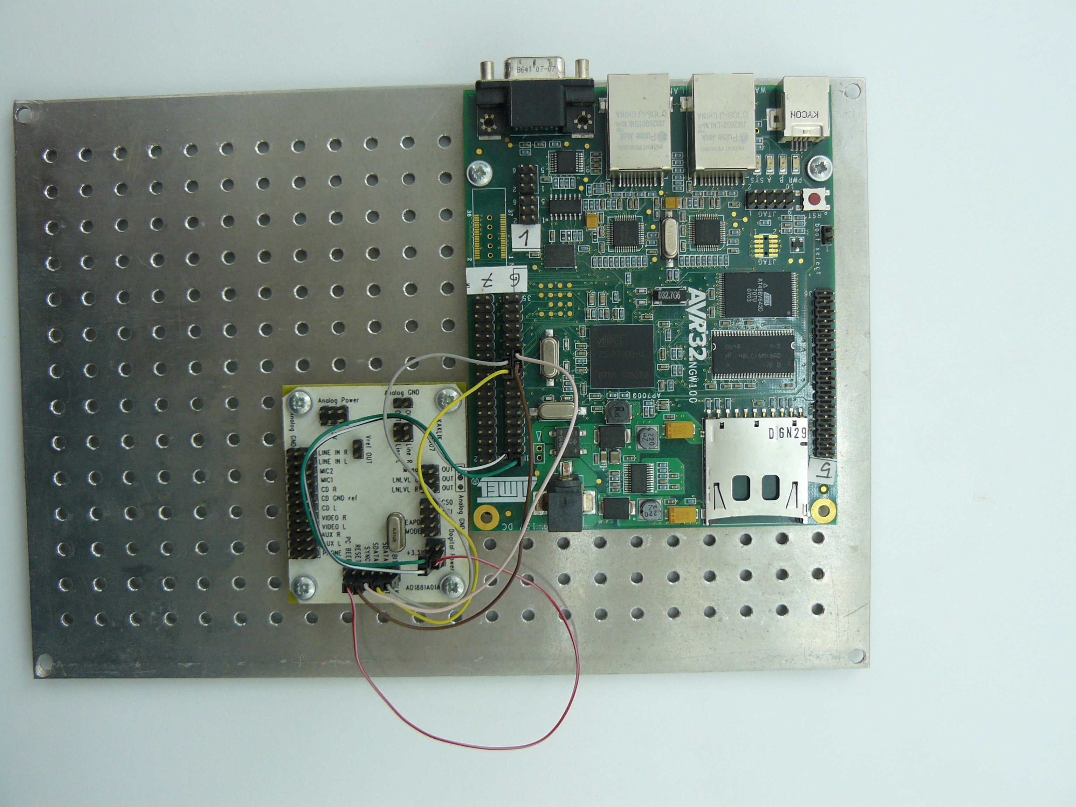
MCU_CPU/AVR/NGW100/doc/img/P1130279.jpg
