MLAB-project/Modules/MCU_CPU/AVR/Text_ATosc/doc/html/OscATmega_files/image002.png

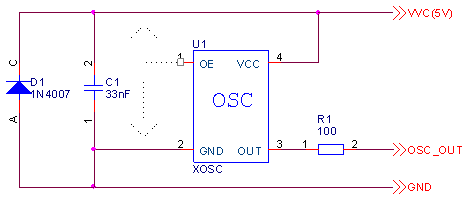
MCU_CPU/AVR/Text_ATosc/doc/html/OscATmega_files/image002.png
