MLAB-project/Modules/MCU_CPU/AVR/Text_ATosc/doc/html/OscATmega_files/image005.jpg

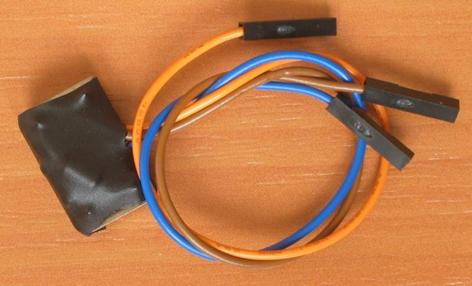
MCU_CPU/AVR/Text_ATosc/doc/html/OscATmega_files/image005.jpg
