MLAB-project/Modules/MCU_CPU/PIC/pic_small.jpg

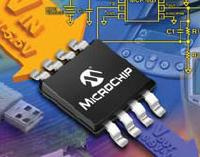
MCU_CPU/PIC/pic_small.jpg
