MLAB-project/Modules/mechanical/boxes/BASEBOX01A/doc/img/Box_bottom_view.png

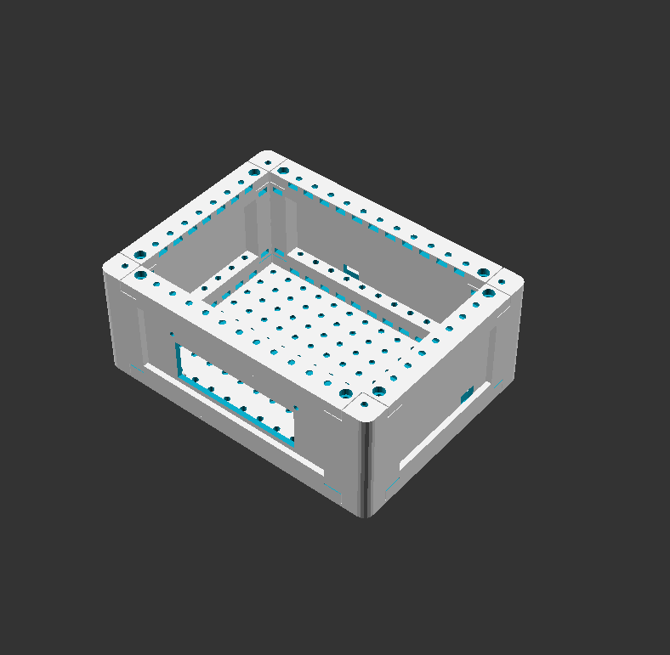
mechanical/boxes/BASEBOX01A/doc/img/Box_bottom_view.png
