MLAB-project/Modules/mechanical/boxes/BASEBOX02A/doc/img/BASEBOX02A_small.png

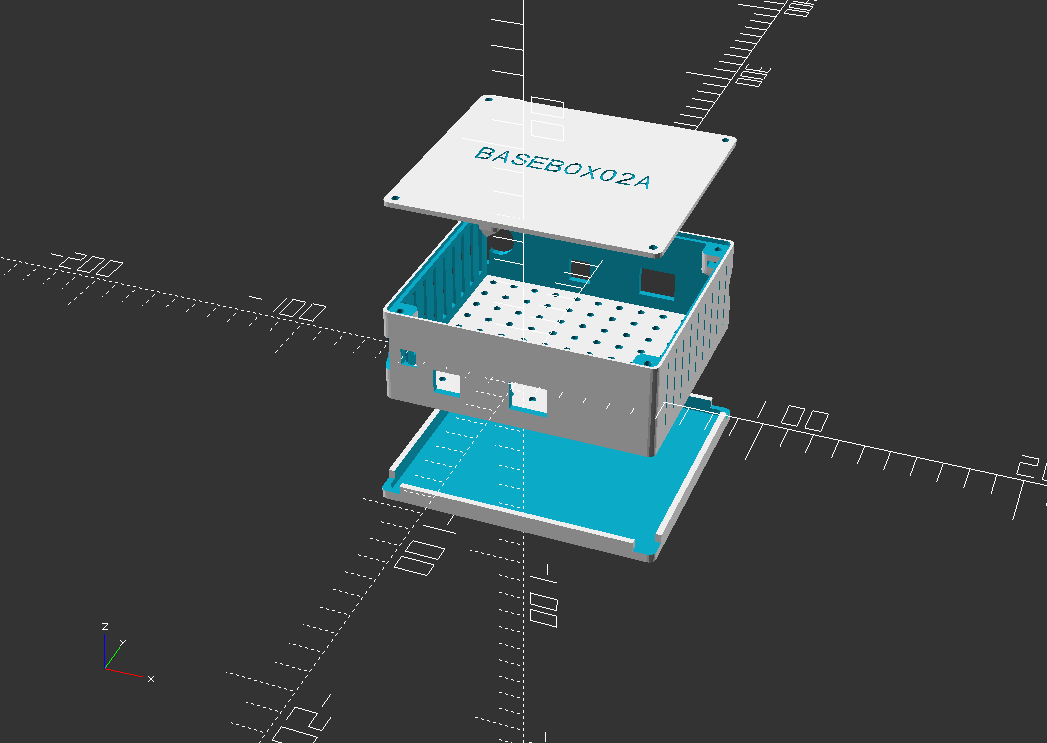
mechanical/boxes/BASEBOX02A/doc/img/BASEBOX02A_small.png
