MLAB-project/Modules/mechanical/boxes/BASEBOX03A/doc/img/BASEBOX03A_small.png

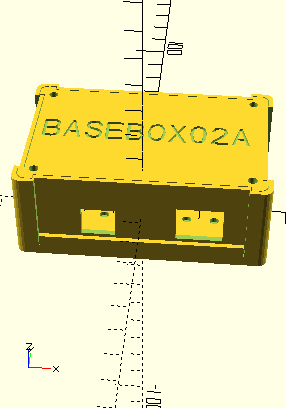
mechanical/boxes/BASEBOX03A/doc/img/BASEBOX03A_small.png
