MLAB-project/Modules/mechanical/boxes/Mechanical_small.jpg

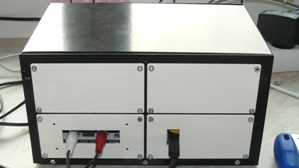
mechanical/boxes/Mechanical_small.jpg
