MLAB-project/Modules/mechanical/boxes/UNIBOX01A/data/Untitled-Scanned-01.jpg

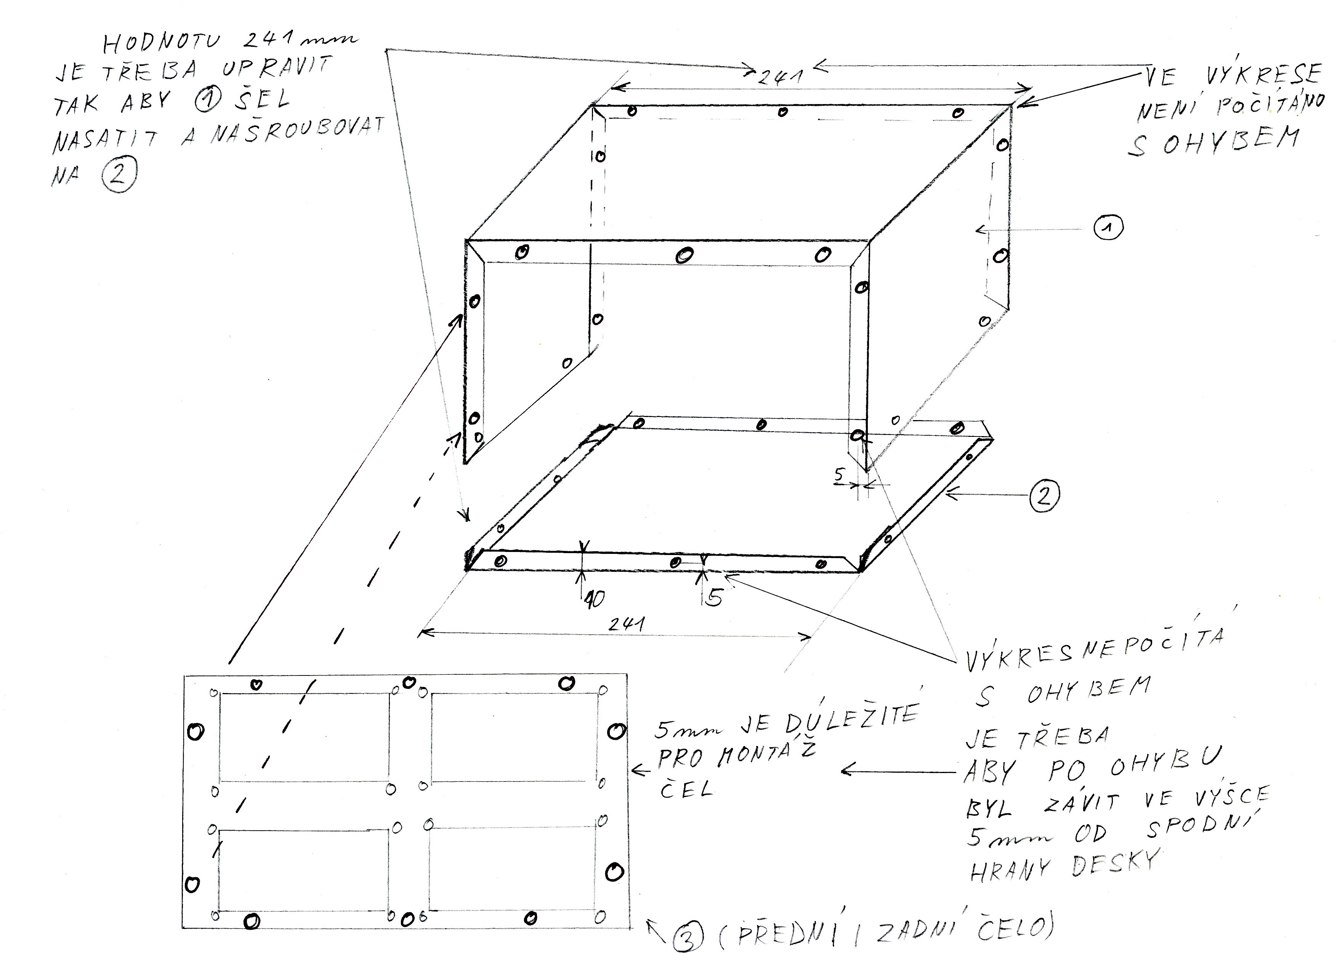
mechanical/boxes/UNIBOX01A/data/Untitled-Scanned-01.jpg
