MLAB-project/Modules/mechanical/boxes/UNIBOX01A/data/Untitled-Scanned-02.jpg

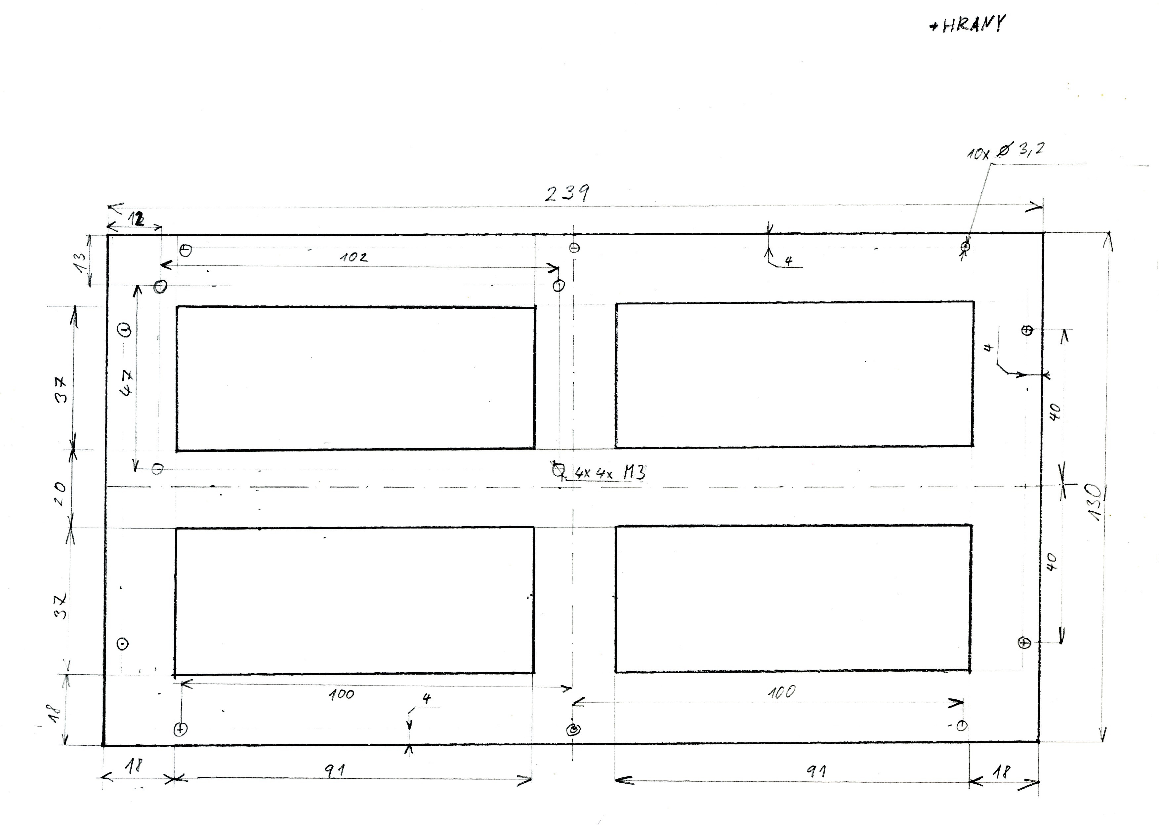
mechanical/boxes/UNIBOX01A/data/Untitled-Scanned-02.jpg
