MLAB-project/Modules/mechanical/boxes/UNIBOX01A/data/Untitled-Scanned-03.jpg

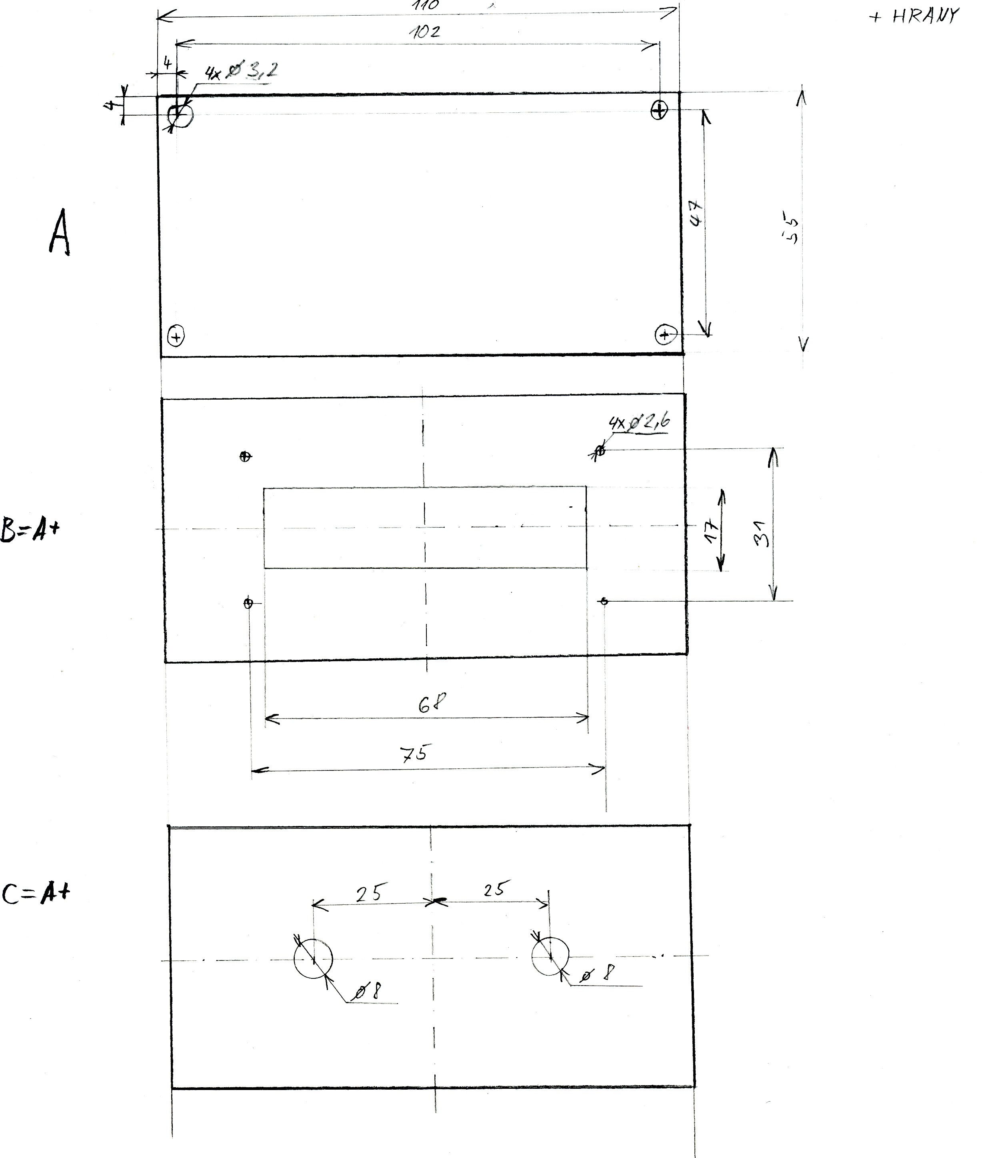
mechanical/boxes/UNIBOX01A/data/Untitled-Scanned-03.jpg
