MLAB-project/Modules/mechanical/boxes/UNIBOX01A/data/Untitled-Scanned-04.jpg

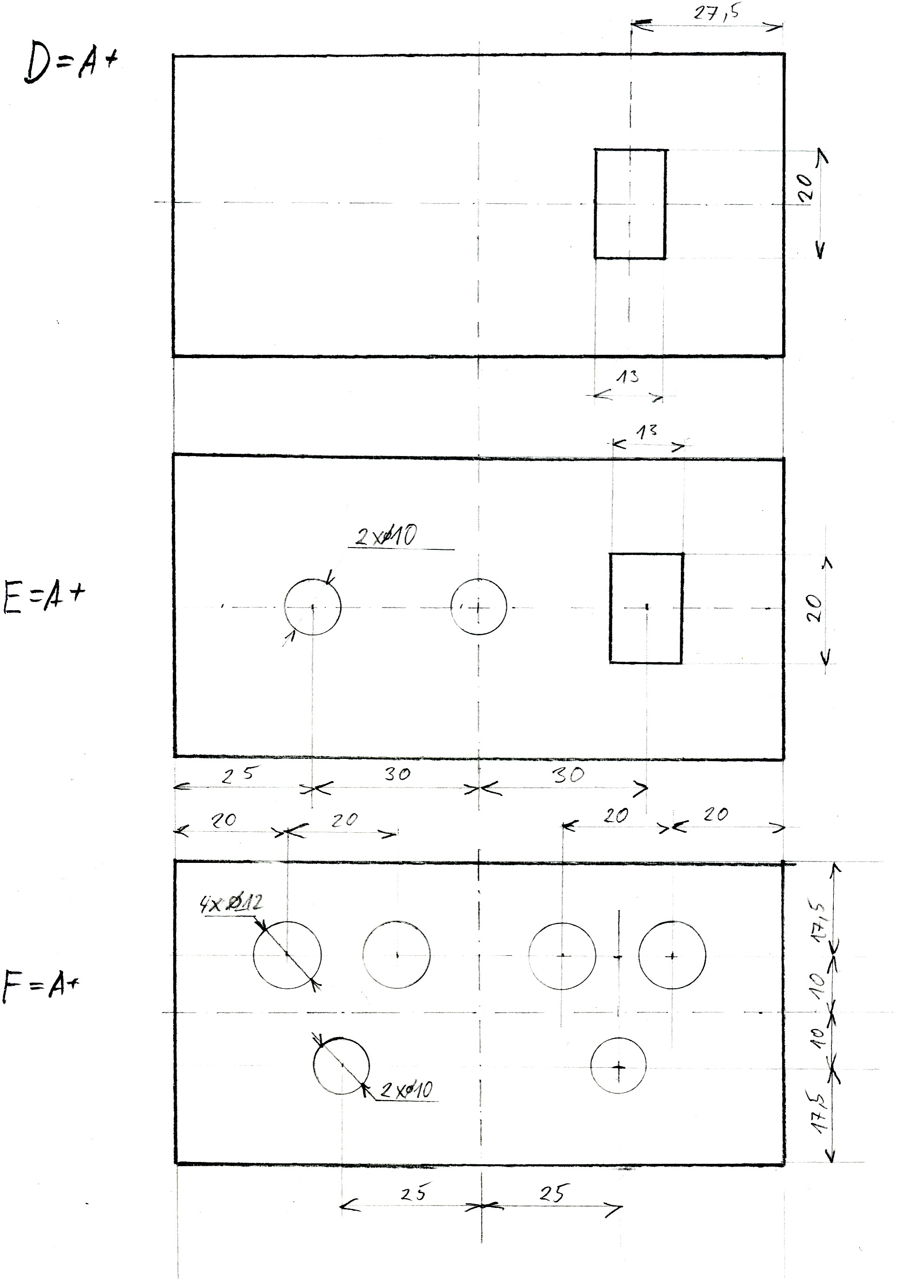
mechanical/boxes/UNIBOX01A/data/Untitled-Scanned-04.jpg
