MLAB-project/Modules/mechanical/boxes/UNIBOX01A/data/Untitled-Scanned-05.jpg

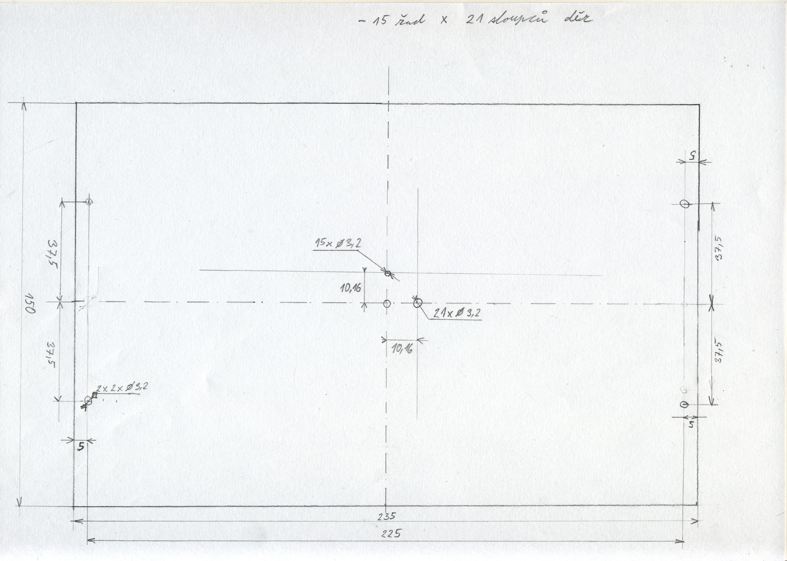
mechanical/boxes/UNIBOX01A/data/Untitled-Scanned-05.jpg
