MLAB-project/Modules/mechanical/boxes/UNIBOX01A/data/Untitled-Scanned-06.jpg

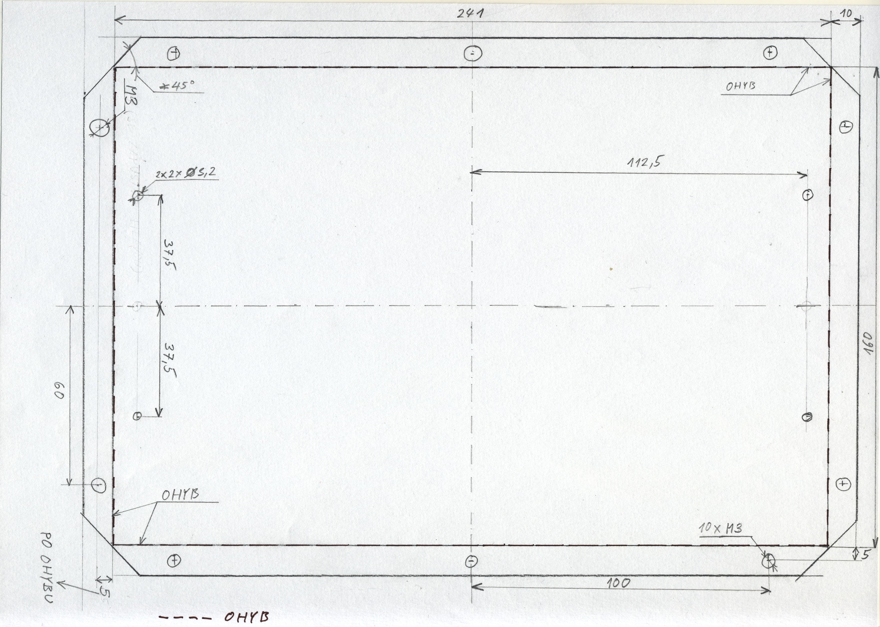
mechanical/boxes/UNIBOX01A/data/Untitled-Scanned-06.jpg
