MLAB-project/Modules/mechanical/boxes/UNIBOX01A/data/Untitled-Scanned-08.jpg

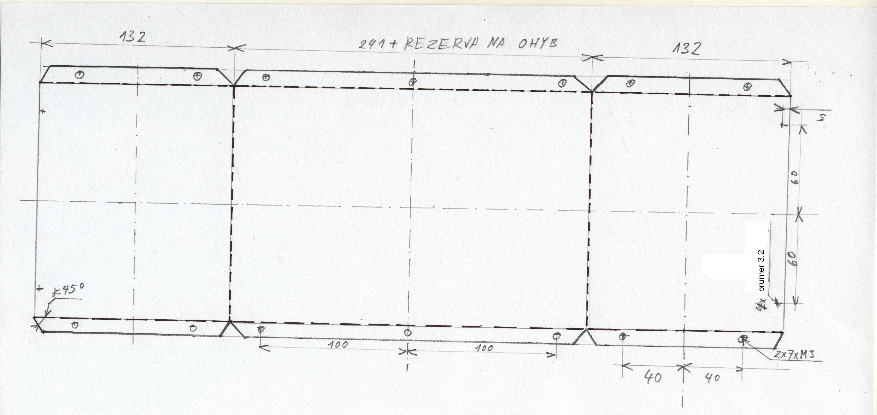
mechanical/boxes/UNIBOX01A/data/Untitled-Scanned-08.jpg
