MLAB-project/Modules/mechanical/boxes/UNIBOX01A/doc/img/UNIBOX01A_big.jpg

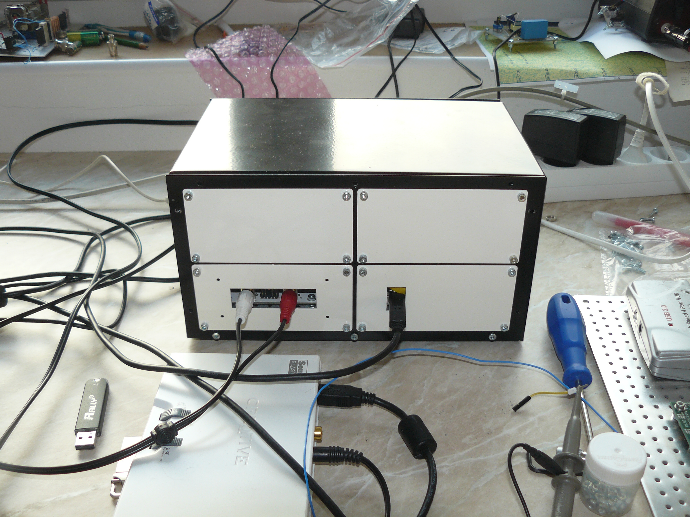
mechanical/boxes/UNIBOX01A/doc/img/UNIBOX01A_big.jpg
