MLAB-project/Modules/mechanical/LCDholder/doc/img/LCD_16x2_panel_small.jpg

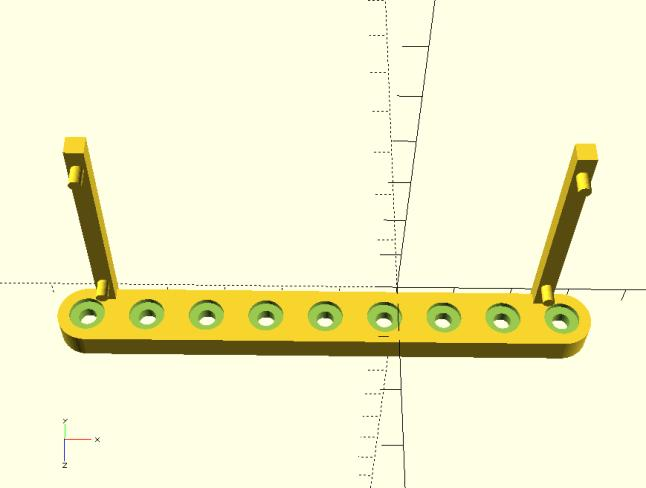
mechanical/LCDholder/doc/img/LCD_16x2_panel_small.jpg
