MLAB-project/Modules/mechanical/PLBASE1113/DOC/img/PLBASE1115_Top_Small.jpg

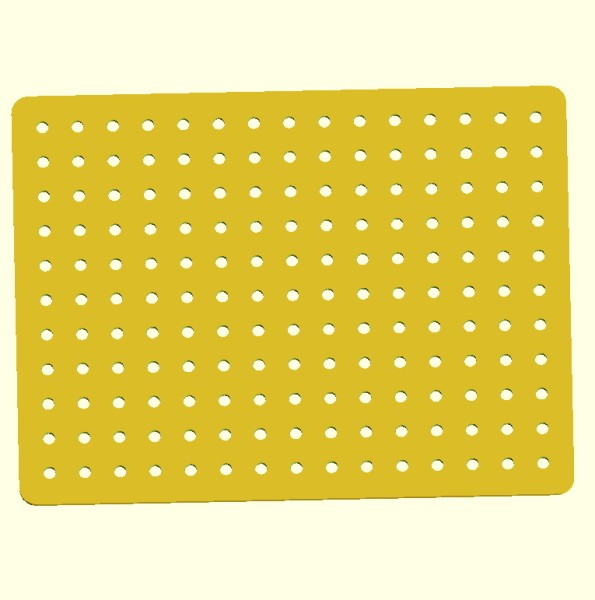
mechanical/PLBASE1113/DOC/img/PLBASE1115_Top_Small.jpg
