MLAB-project/Modules/memory/Memory_small.jpg

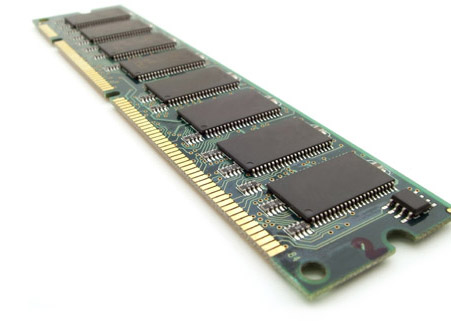
memory/Memory_small.jpg
