MLAB-project/Modules/motor_drivers/IR2302/doc/hb13.png

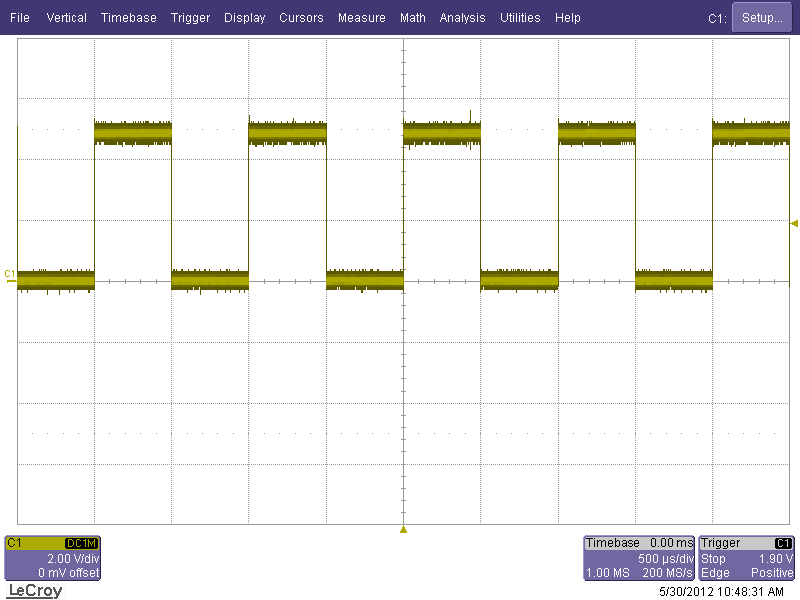
motor_drivers/IR2302/doc/hb13.png
