MLAB-project/Modules/motor_drivers/IR2302/doc/hb14.png

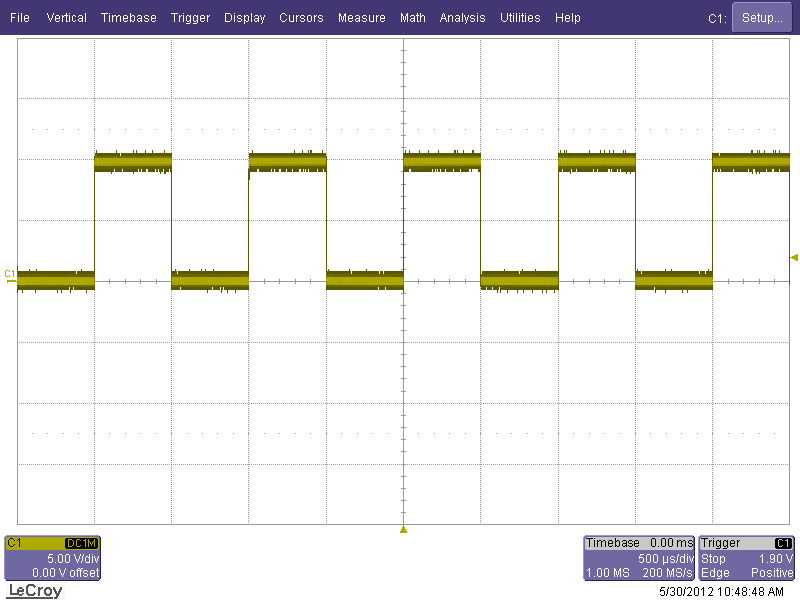
motor_drivers/IR2302/doc/hb14.png
