MLAB-project/Modules/motor_drivers/IR2302/doc/hb36.png

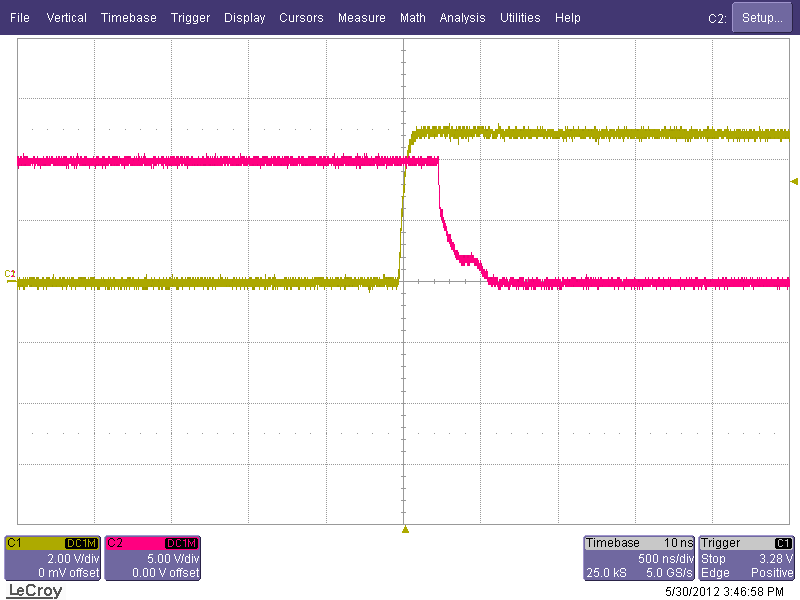
motor_drivers/IR2302/doc/hb36.png
