MLAB-project/Modules/motor_drivers/IR2302/doc/hb37.png

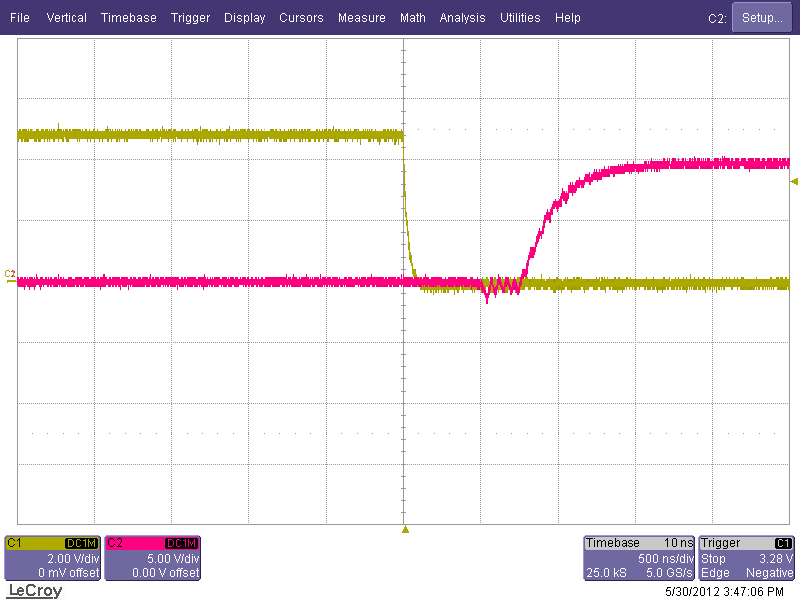
motor_drivers/IR2302/doc/hb37.png
