MLAB-project/Modules/motor_drivers/IR2302/doc/hb41.png

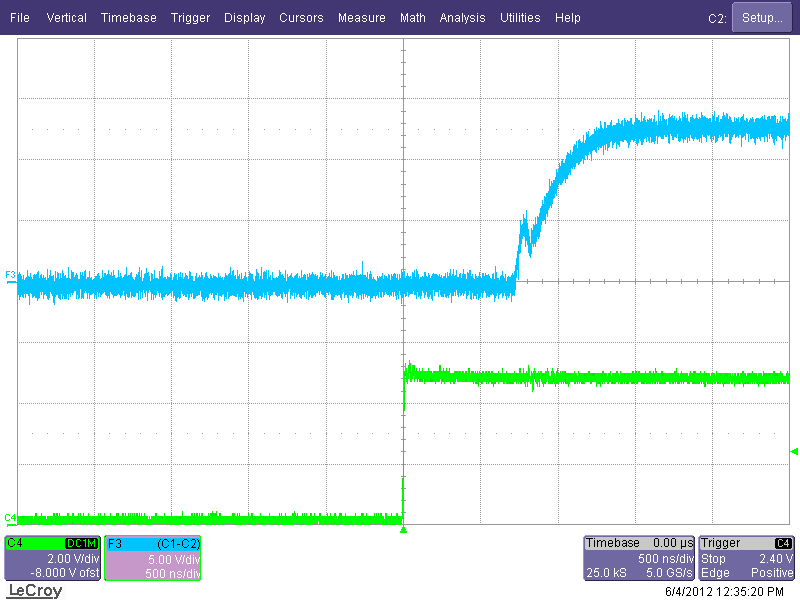
motor_drivers/IR2302/doc/hb41.png
