MLAB-project/Modules/motor_drivers/IR2302/doc/hb42.png

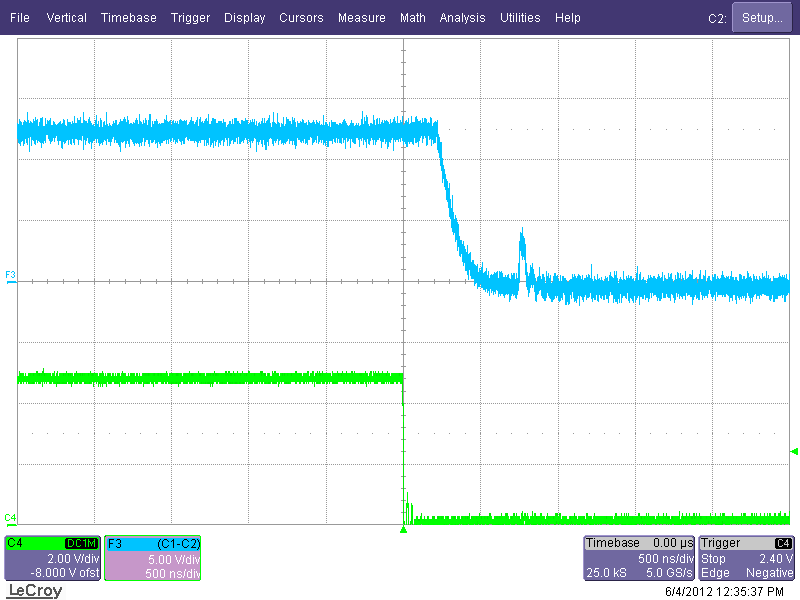
motor_drivers/IR2302/doc/hb42.png
