MLAB-project/Modules/motor_drivers/IR2302/doc/hb43.png

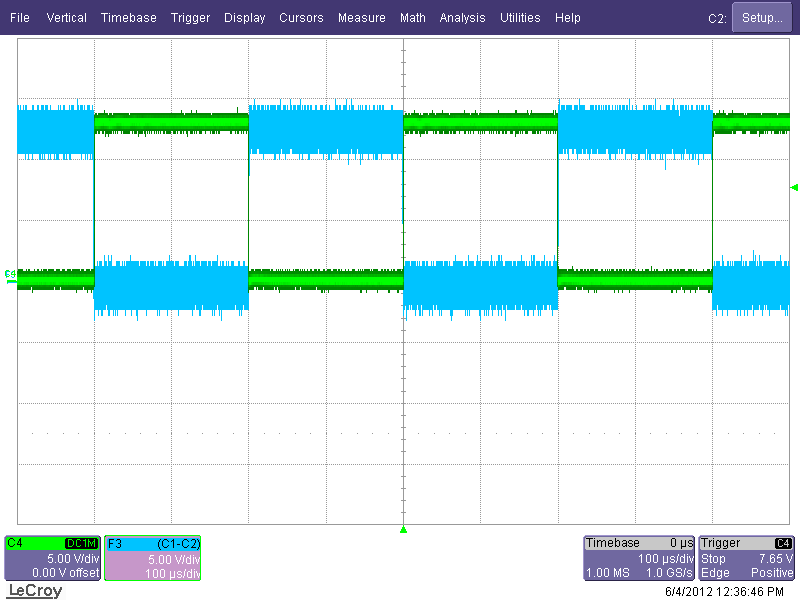
motor_drivers/IR2302/doc/hb43.png
