MLAB-project/Modules/motor_drivers/IR2302/doc/hb44.png

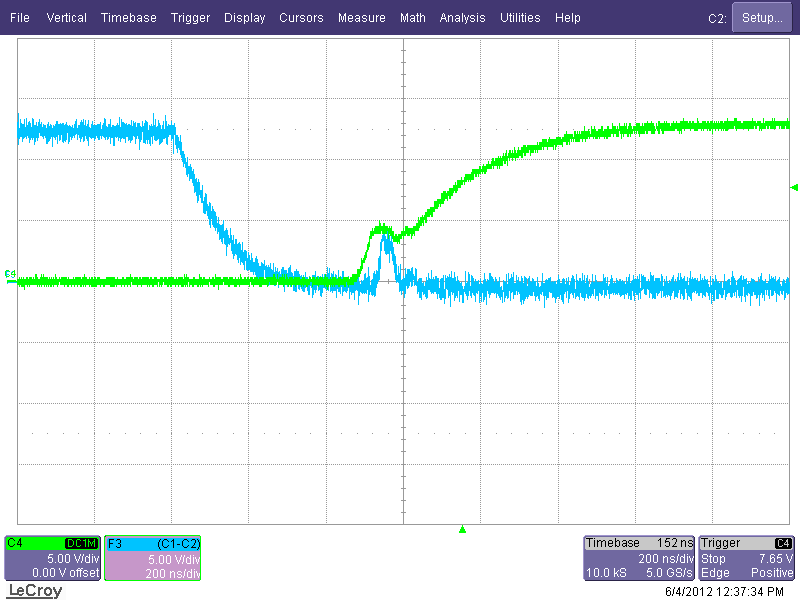
motor_drivers/IR2302/doc/hb44.png
