MLAB-project/Modules/motor_drivers/IR2302/doc/hb45.png

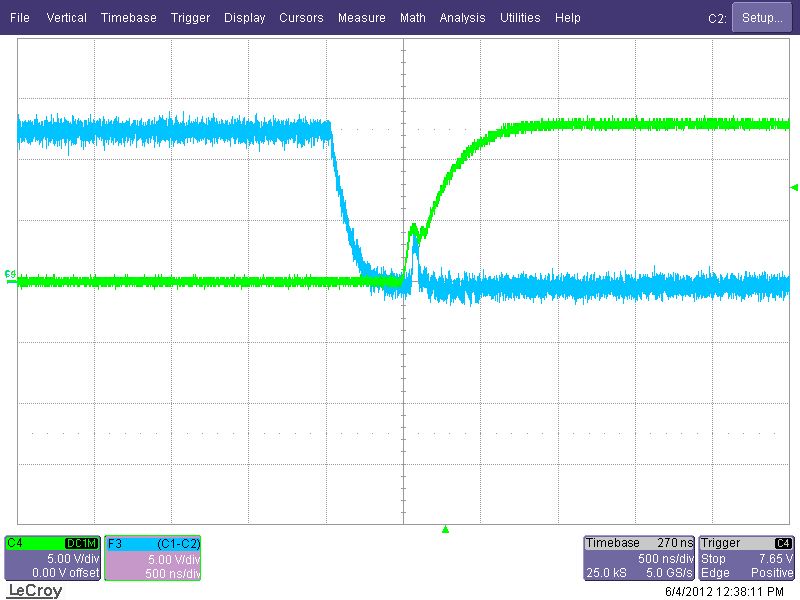
motor_drivers/IR2302/doc/hb45.png
