MLAB-project/Modules/motor_drivers/IR2302/doc/hb46.png

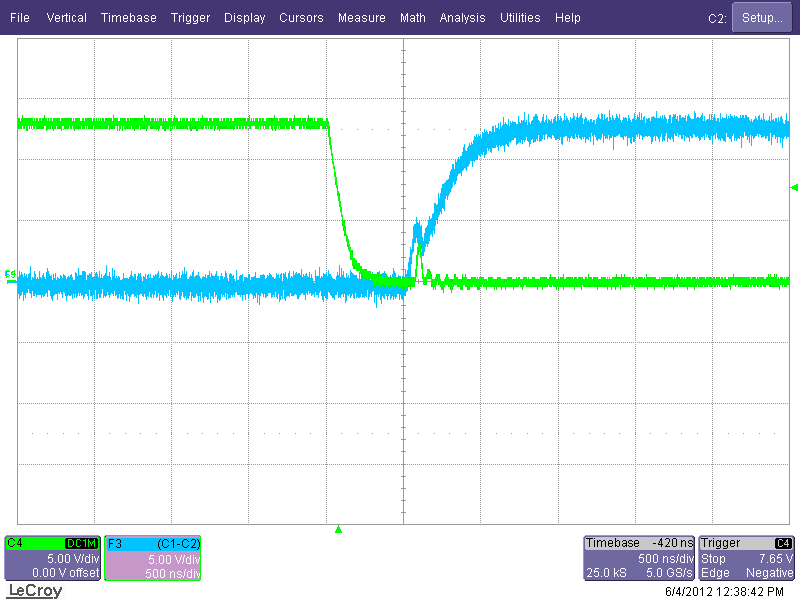
motor_drivers/IR2302/doc/hb46.png
