MLAB-project/Modules/motor_drivers/IR2302/doc/hb47.png

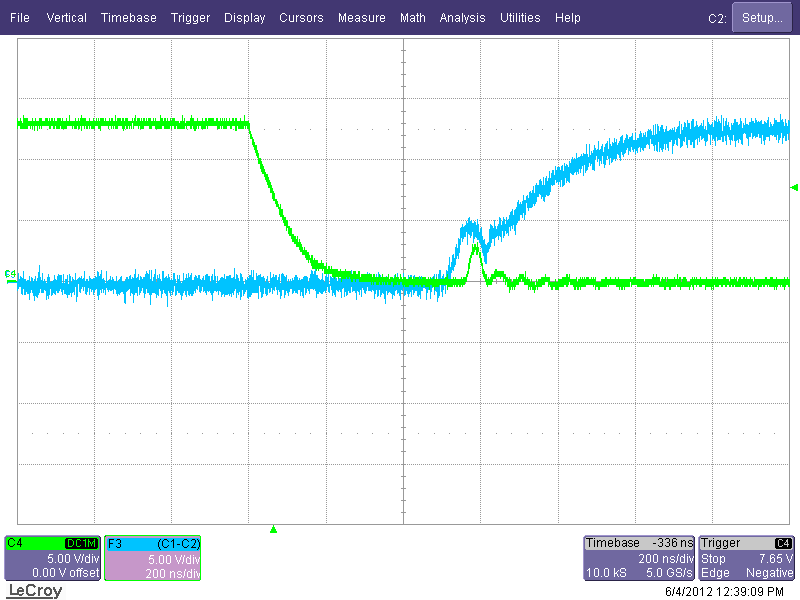
motor_drivers/IR2302/doc/hb47.png
