MLAB-project/Modules/motor_drivers/stepper_small.jpg

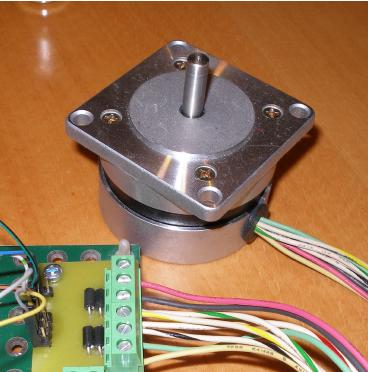
motor_drivers/stepper_small.jpg
