MLAB-project/Modules/op_amps/opamp_small.jpg

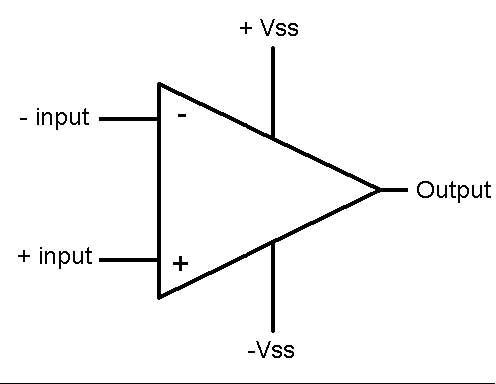
op_amps/opamp_small.jpg
