MLAB-project/Modules/power_supply/Supply_small.jpg

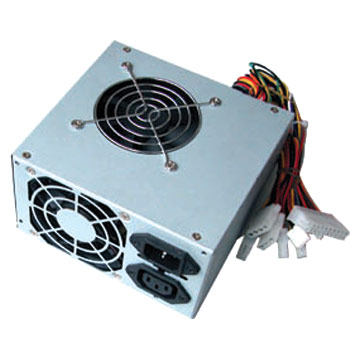
power_supply/Supply_small.jpg
