MLAB-project/Modules/power_sw/fet_small.jpg

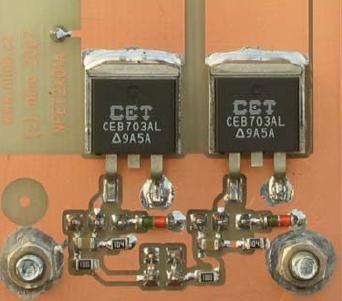
power_sw/fet_small.jpg
