MLAB-project/Modules/power_sw/NFET2x2/doc/img/NFET_small.jpg

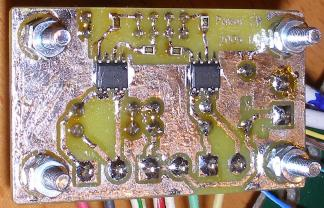
power_sw/NFET2x2/doc/img/NFET_small.jpg
