MLAB-project/Modules/RF/RC_small.jpg

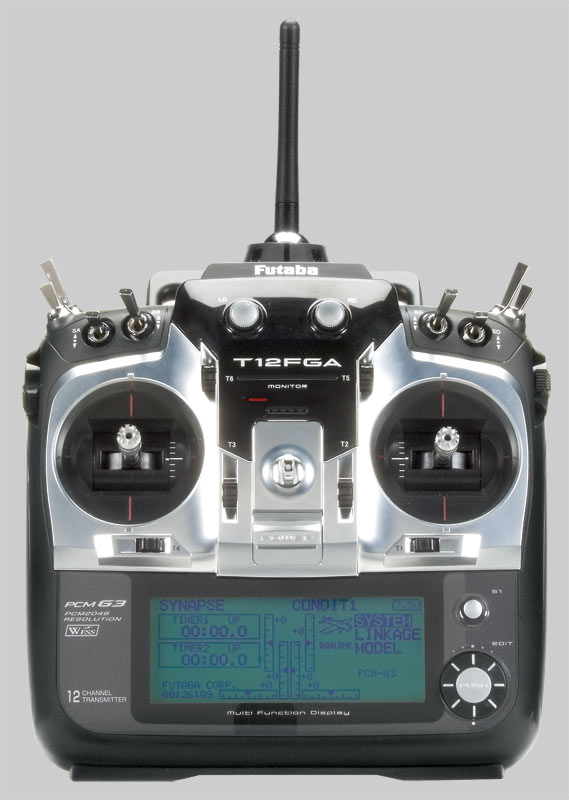
RF/RC_small.jpg
