MLAB-project/Modules/sensors/Sensors_small.jpg

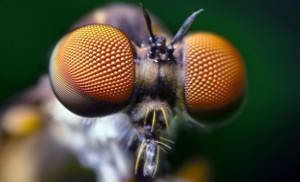
sensors/Sensors_small.jpg
