MLAB-project/Modules/TDC/TDC_small.jpg

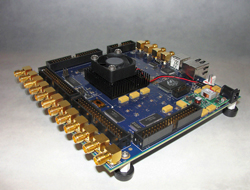
TDC/TDC_small.jpg
