MLAB-project/Modules/translators/TXB0108_small.jpg

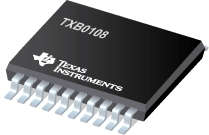
translators/TXB0108_small.jpg
