MLAB-project/Modules/mechanical/LCDholder/cad/LCD_16x2_box.stl

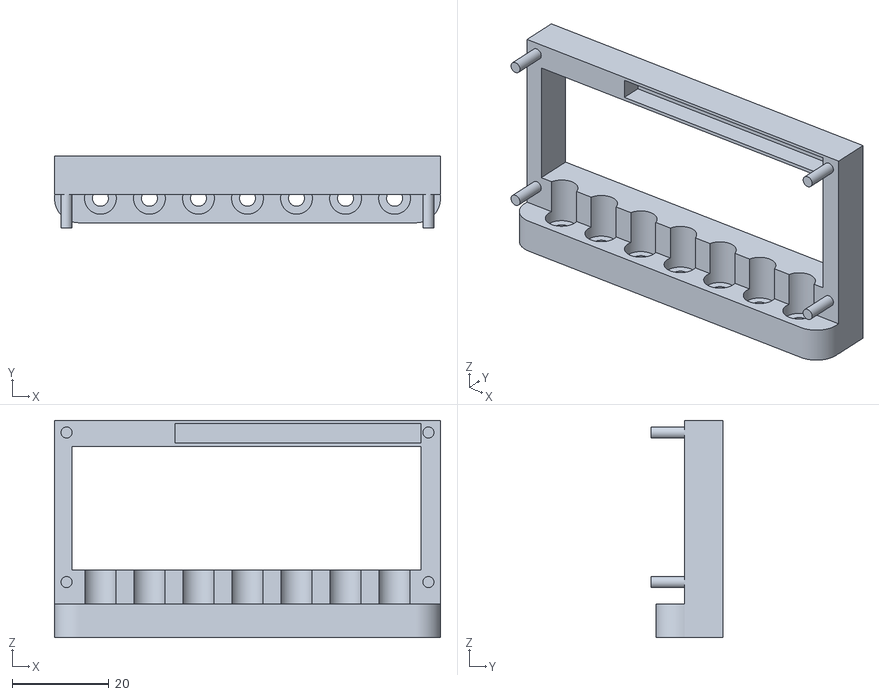
[picture p175: CAD file, 2015-11-15]
mechanical/LCDholder/cad/LCD_16x2_box.stl
80.0 x 15.0 x 45.0
