MLAB-project/Modules/mechanical/PLBASE1113/CAD/PLBASE1113.stl

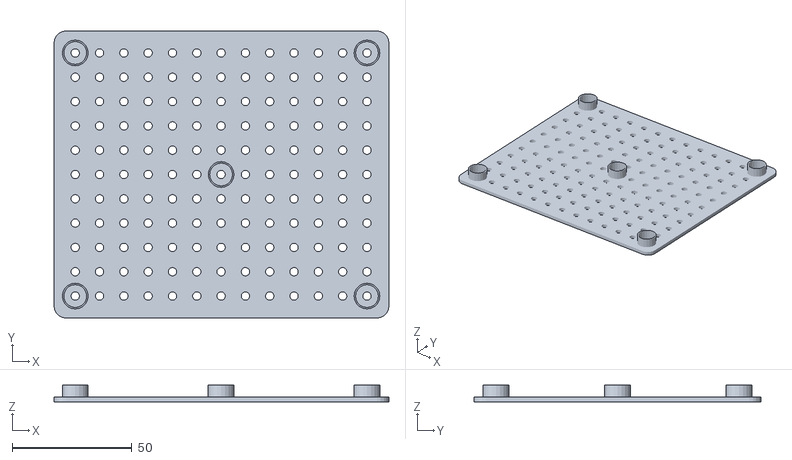
[picture p176: CAD file, 2017-08-24]
mechanical/PLBASE1113/CAD/PLBASE1113.stl
140.0 x 120.0 x 7.00
