MLAB-project/Modules/mechanical/PLBASE1115/CAD/PLBASE1115.stl

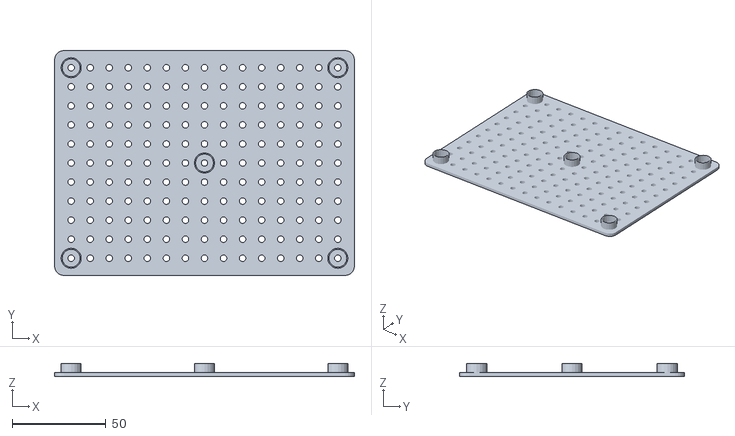
[picture p177: CAD file, 2017-08-24]
mechanical/PLBASE1115/CAD/PLBASE1115.stl
160.0 x 120.0 x 7.00
