MLAB-project/Modules/mechanical/PLBASE1515/cad/PLBASE1515.stl

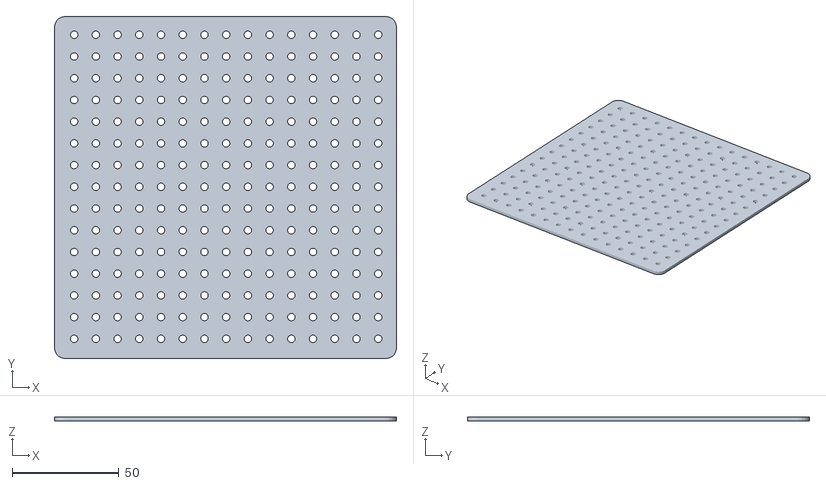
[picture p178: CAD file, 2015-12-07]
mechanical/PLBASE1515/cad/PLBASE1515.stl
160.0 x 160.0 x 2.10
