MLAB-project/Modules/Mechanical/WINDGAUGE02A/AMF/P_WINDGAUGE02A_L01.stl

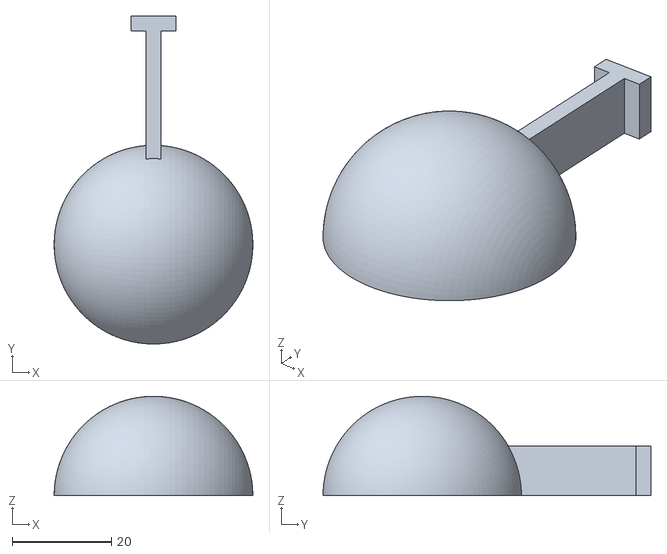
[picture p179: CAD file, 2016-03-07]
Mechanical/WINDGAUGE02A/AMF/P_WINDGAUGE02A_L01.stl
40.0 x 66.0 x 20.0
