MLAB-project/Modules/mechanical/WINDGAUGE03A/amf/WINDGAUGE_R03.stl

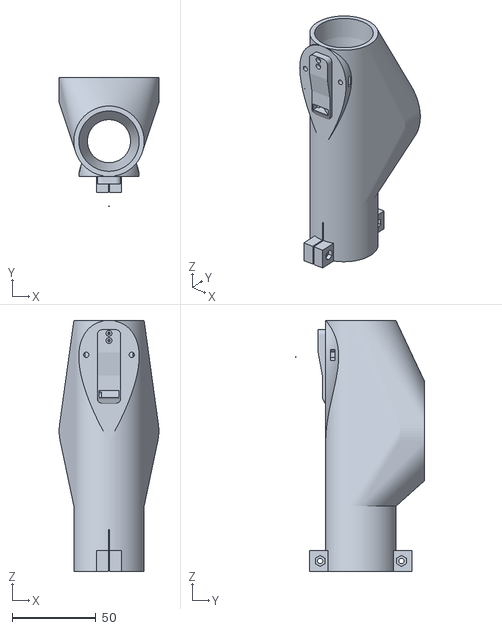
[picture p180: CAD file, 2020-03-23]
mechanical/WINDGAUGE03A/amf/WINDGAUGE_R03.stl
59.6 x 77.0 x 150.0
