MLAB-project/Modules/PowerSupply/TPS63060V01A/CAD/3x4MLAB_frame.stl

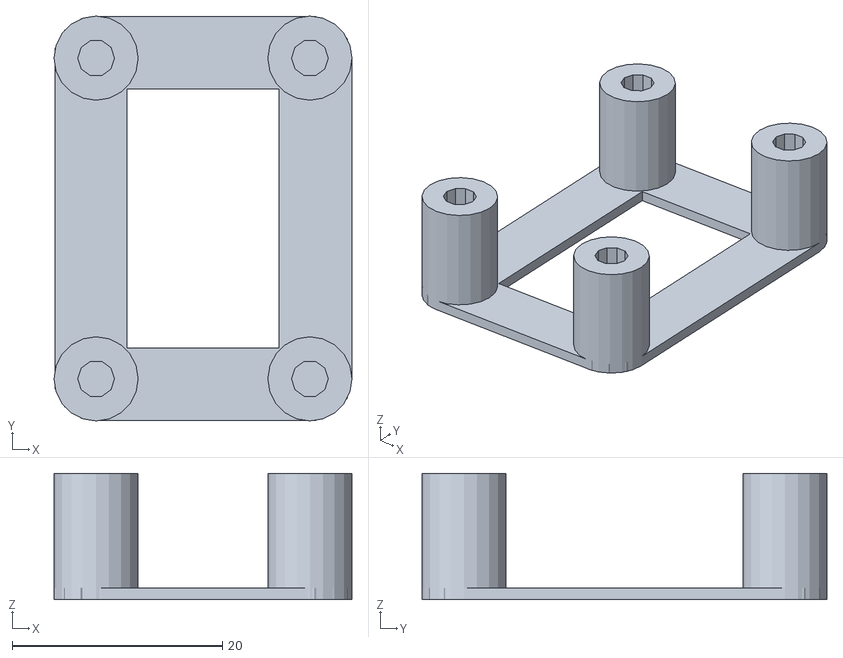
[picture p181: CAD file, 2015-11-26]
PowerSupply/TPS63060V01A/CAD/3x4MLAB_frame.stl
28.3 x 38.5 x 12.0
