MLAB-project/Modules/universal/MESA7I90HD/amf/MESA7I90HD_MLAB_breakout_frame.stl

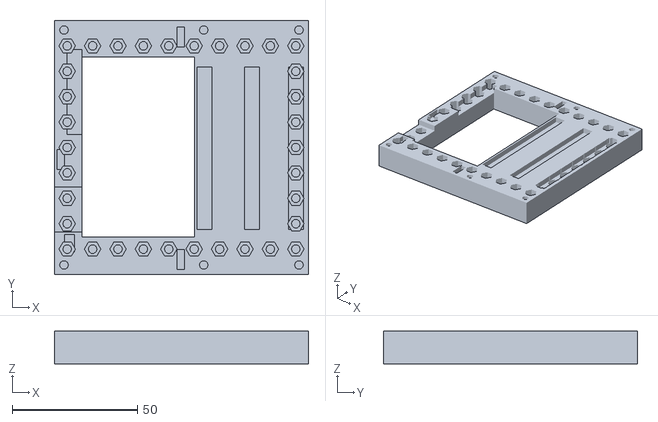
[picture p182: CAD file, 2016-03-07]
universal/MESA7I90HD/amf/MESA7I90HD_MLAB_breakout_frame.stl
101.6 x 101.6 x 13.0
