MLAB-project/Modules/mechanical/boxes/AWSBOX01A/amf/P_AWSBOX01A_D01.stl

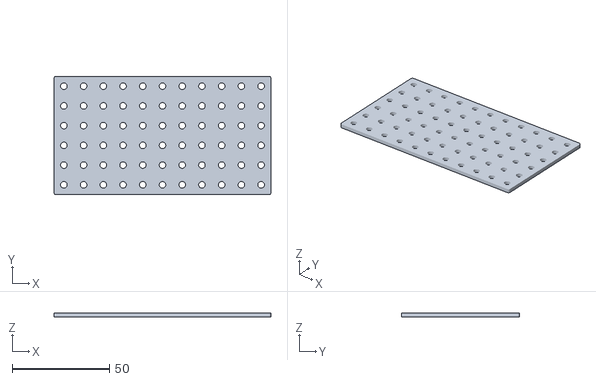
[picture p183: CAD file, 2016-12-23]
mechanical/boxes/AWSBOX01A/amf/P_AWSBOX01A_D01.stl
111.8 x 61.0 x 2.10
