MLAB-project/Modules/mechanical/boxes/BASEBOX02A/amf/BASEBOX02A.stl

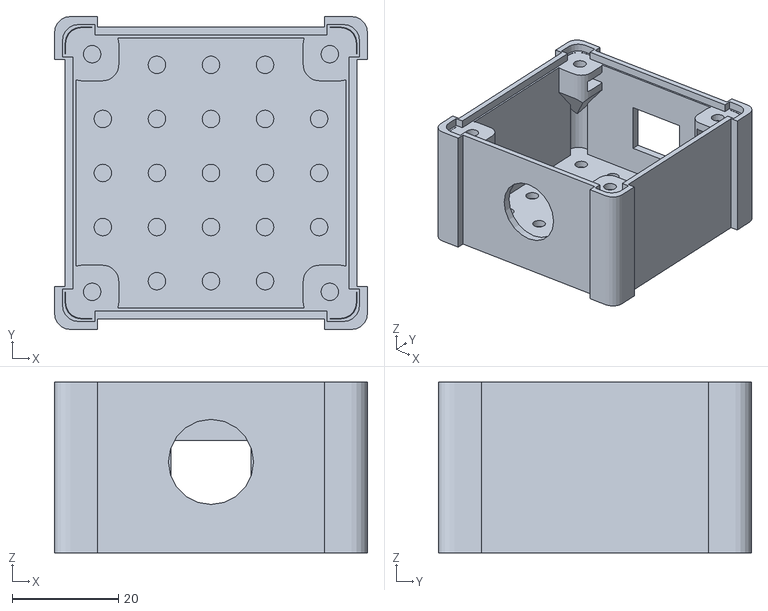
[picture p184: CAD file, 2016-04-14]
mechanical/boxes/BASEBOX02A/amf/BASEBOX02A.stl
58.8 x 58.8 x 32.1
