MLAB-project/Modules/mechanical/boxes/SHTBOX01A/amf/P_SHTBOX01A_D02.stl

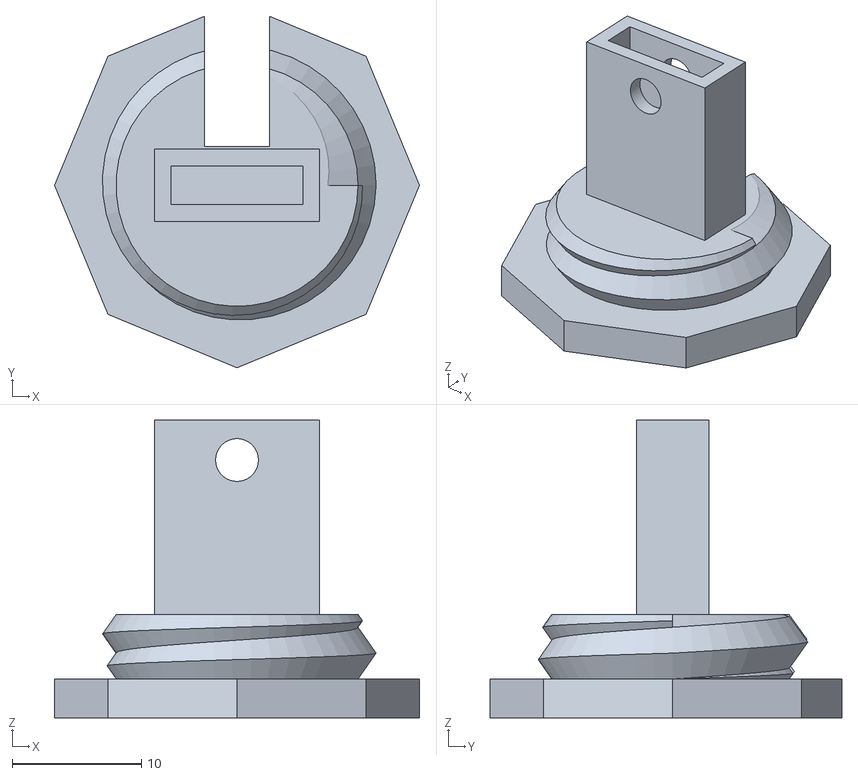
[picture p185: CAD file, 2017-02-09]
mechanical/boxes/SHTBOX01A/amf/P_SHTBOX01A_D02.stl
28.2 x 27.2 x 23.0
