MLAB-project/Modules/mechanical/LCDholder/cad/LCD_16x2_box_modifier.stl

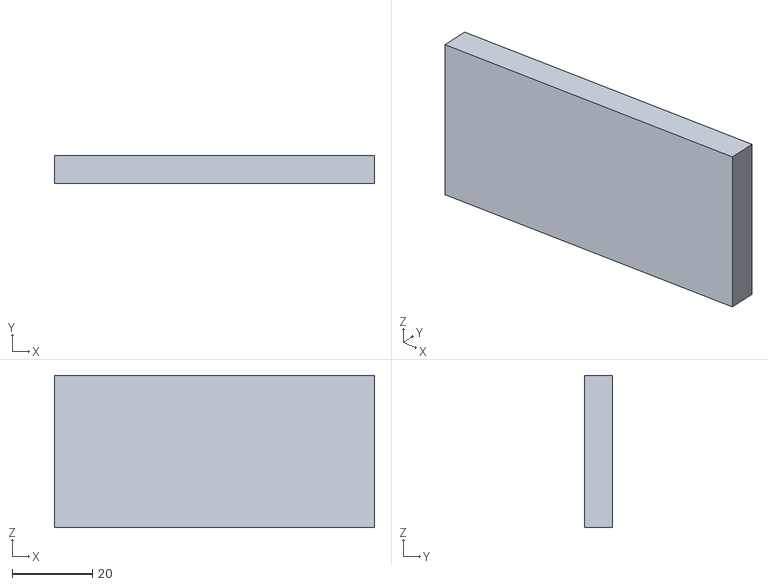
[picture p186: CAD file, 2015-11-15]
mechanical/LCDholder/cad/LCD_16x2_box_modifier.stl
80.0 x 7.00 x 38.0
