MLAB-project/Modules/mechanical/WINDGAUGE03A/amf/P_WINDGAUGE03A_R03.stl

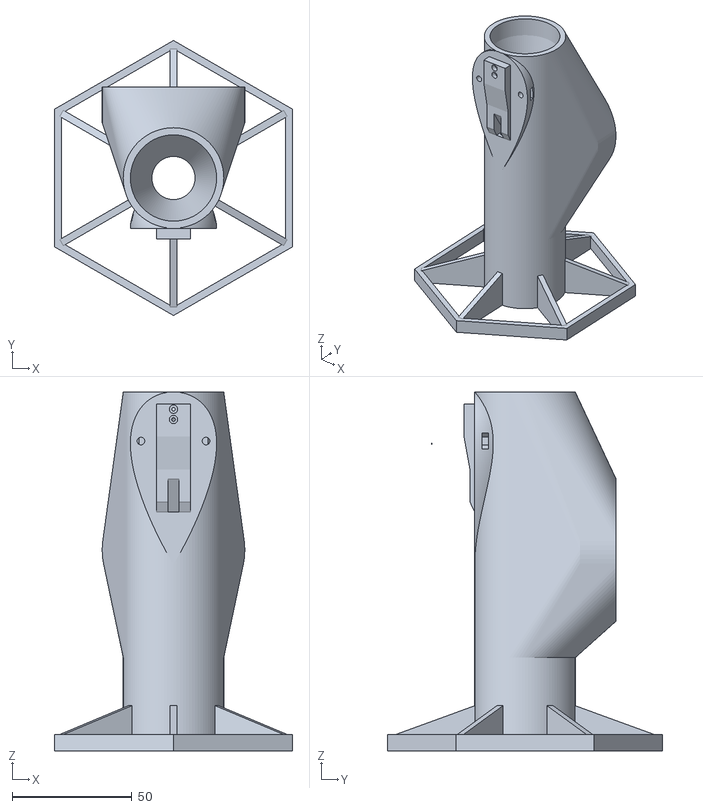
[picture p187: CAD file, 2019-05-01]
mechanical/WINDGAUGE03A/amf/P_WINDGAUGE03A_R03.stl
99.5 x 114.9 x 150.0
