MLAB-project/Modules/mechanical/boxes/AWSBOX01A/amf/P_AWSBOX01A_D02_2.stl

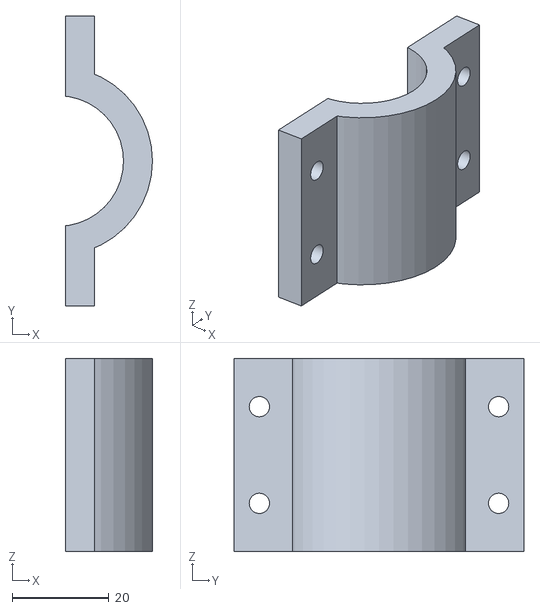
[picture p188: CAD file, 2016-12-23]
mechanical/boxes/AWSBOX01A/amf/P_AWSBOX01A_D02_2.stl
18.0 x 60.0 x 40.0
