MLAB-project/Modules/mechanical/LCDholder/cad/LCD_16x2_panelA.stl

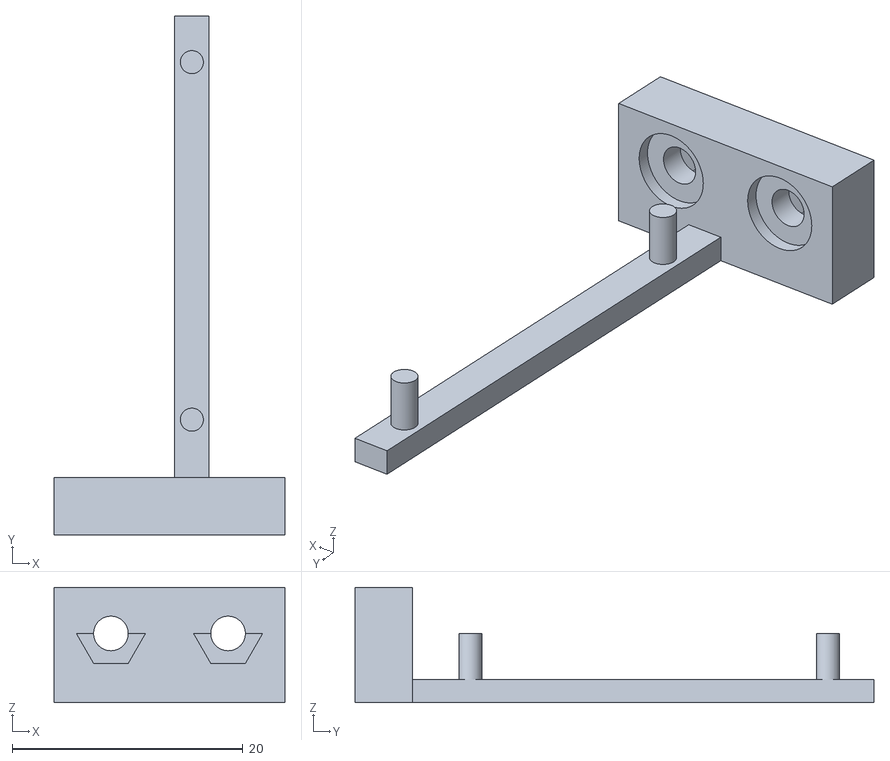
[picture p189: CAD file, 2015-10-07]
mechanical/LCDholder/cad/LCD_16x2_panelA.stl
20.0 x 45.0 x 10.0
