MLAB-project/Modules/mechanical/LCDholder/cad/LCD_16x2_panel.stl

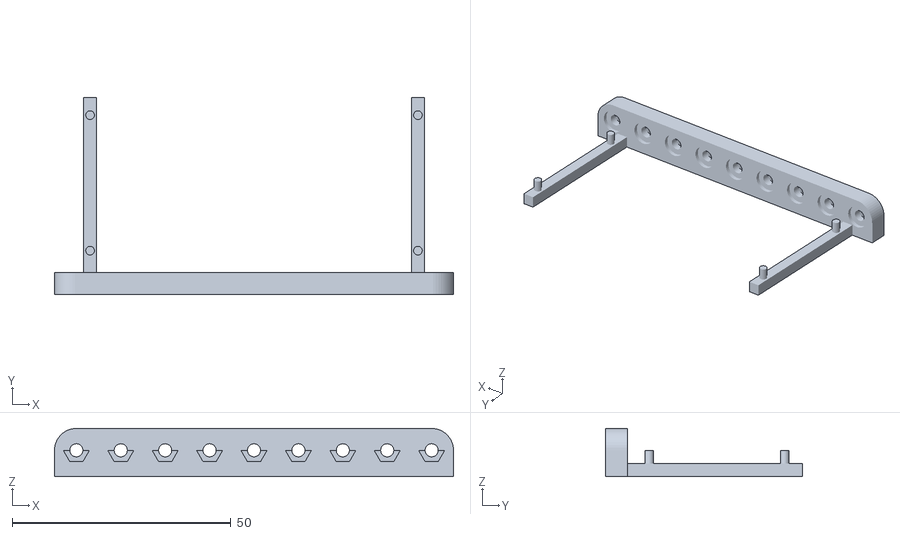
[picture p190: CAD file, 2015-10-07]
mechanical/LCDholder/cad/LCD_16x2_panel.stl
91.3 x 45.0 x 11.0
