MLAB-project/Modules/mechanical/boxes/SHTBOX01A/cad/configuration.scad

$fn=40; // model faces resolution.




S01_sila_materialu=1.3; //sila výztuhy

D05_vyska_drzaku_senzoru=15;
D05_prumer_zavitu=23;
D05_vyska_podstavce=8;
D05_vyska_zavitu=5;
D05_sirka_otvoru_na_kabel=5;

D05_vyska_senzoru= 42; //42


D05_sirka_zuzene_casti=10.8; //vnitřní
D05_vyska_zuzene_casti=16;
D05_vyska_kuzelu=10;


D05_vzdalenost_otvoru_od_hrany=2;
D05_prumer_otvoru=2;
D05_pocet_otvoru=8;













tolerance_zavitu=0.75; //tolerance s poloměru
