MLAB-project/Modules/mechanical/boxes/UNIBOX03A/cad/configuration.scad

//UNIBOX03A
//------------------------------------------------------------
///*

rozmer_x=165;
rozmer_y=51.13;
sila=1.5;

roztec_srouby_x=155.52;
roztec_srouby_y=43.53;
prumer_sroubu=2;
zakulaceni_hrany=5.4;

roztec_der=10.16;
pocet_der_osa_x=15;
