MLAB-project/Modules/mechanical/boxes/UNIBOX04A/cad/configuration.scad

//UNIBOX04A
//------------------------------------------------------------
///*

rozmer_x=103;
rozmer_y=53;
sila=1.5;

roztec_srouby_x=95.02;
roztec_srouby_y=45;
prumer_sroubu=2;
zakulaceni_hrany=5.4;

roztec_der=10.16;
pocet_der_osa_x=8;
