MLAB-project/Modules/mechanical/WINDGAUGE03A/cad/print_data/P_WINDGAUGE01A_R03.scad

$fn=100; // model faces resolution.
include <../configuration.scad>
use <../SRC/WINDGAUGE_R03.scad>

translate([0,0,0])
    WINDGAUGE01A_R03();

            
