MLAB-project/Modules/mechanical/WINDGAUGE03A/cad/print_data/P_WINDGAUGE01A_R04.scad

$fn=100; // model faces resolution.
include <../configuration.scad>

use <../SRC/WINDGAUGE_R04.scad>

//neni potřeba
    translate([0,0,0])
        rotate([0,0, 0])
            WINDGAUGE01A_R04 ();   
