MLAB-project/Modules/mechanical/WINDGAUGE03A/cad/print_data/P_WINDGAUGE01A_S01.scad

$fn=100; // model faces resolution.
include <../configuration.scad>

use <../SRC/WINDGAUGE_S01.scad>


translate([0,0,0])
    WINDGAUGE01A_S01();
