MLAB-project/Modules/mechanical/WINDGAUGE03A/cad/print_data/P_WINDGAUGE01A_S02.scad

$fn=100; // model faces resolution.
include <../configuration.scad>

use <../SRC/WINDGAUGE_S02.scad>
use <../SRC/lib/polyScrewThread_r1.scad>


PI=3.141592;

translate([0,0,S01_vyska])
    rotate([180,0, 0])
        WINDGAUGE01A_S02();   
