MLAB-project/Modules/mechanical/boxes/BASEBOX01A/cad/configuration/otvory_conf.scad

//Konfigurace pro otvory

//1A) - LCD 2x16
//vzdalenost der
vzdalenost_der_x = 75;
vzdalenost_der_y = 31;
prumer_otvoru = 2.7;
prumer_sloupku = 5;

//ramecek LCD
ramecek_x = 72;
ramecek_y = 26;

//vyska ramecku LCD
ramecek_vyska = 5;
