MLAB-project/Modules/tdc/GP201A/TODO.txt

-Zrusit kalibracni odpory na desce a vyvect vsechny na hrebinek.
