MLAB-project/Modules/power_supply/MAX1797/pcb/V1.pdf

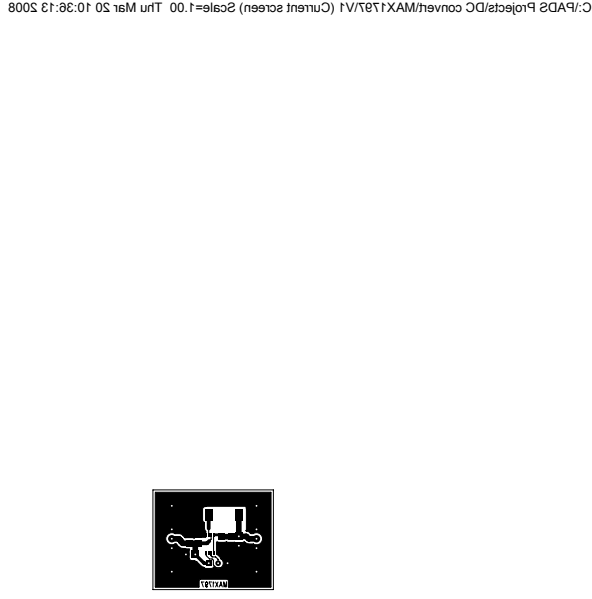
[picture p191: page 1]

C:\PADS Projects\DC convert\MAX1797\V1 (Current screen) Scale=1.00 Thu Mar 20 10:36:13 2008
