MLAB-project/Modules/power_supply/TPS61170/pcb/V2.pdf

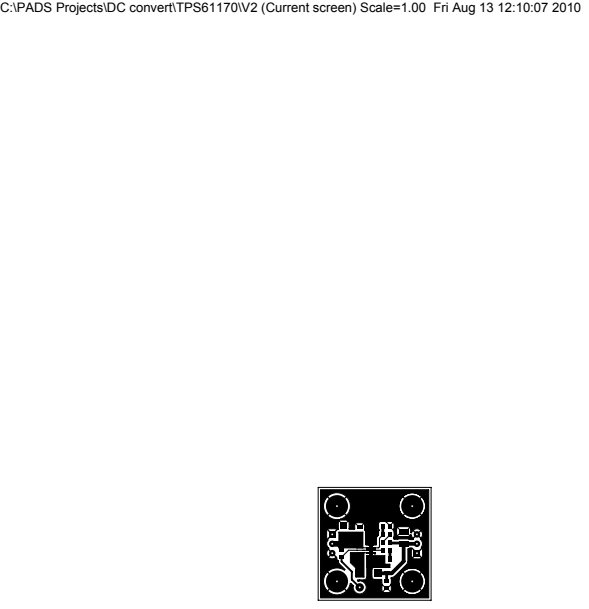
[picture p192: page 1]

C:\PADS Projects\DC convert\TPS61170\V2 (Current screen) Scale=1.00 Fri Aug 13 12:10:07 2010
