MLAB-project/Modules/power_supply/TPS61200/pcb/V2.pdf

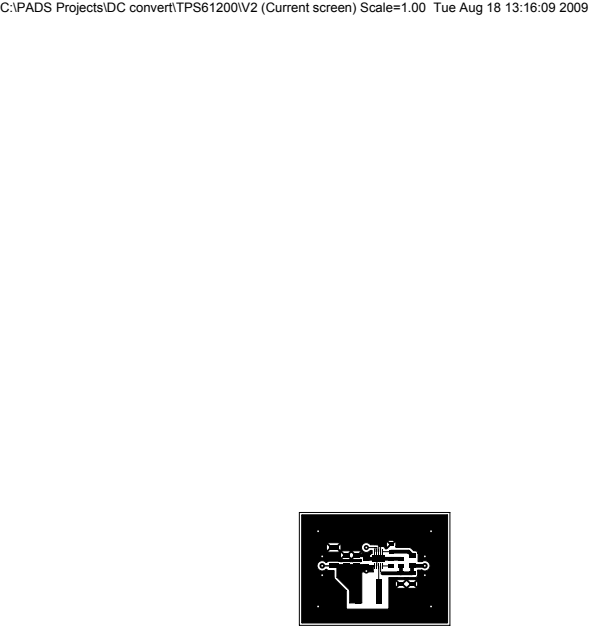
[picture p193: page 1]

C:\PADS Projects\DC convert\TPS61200\V2 (Current screen) Scale=1.00 Tue Aug 18 13:16:09 2009
