MLAB-project/Modules/power_supply/TPS63000/pcb/V2.pdf

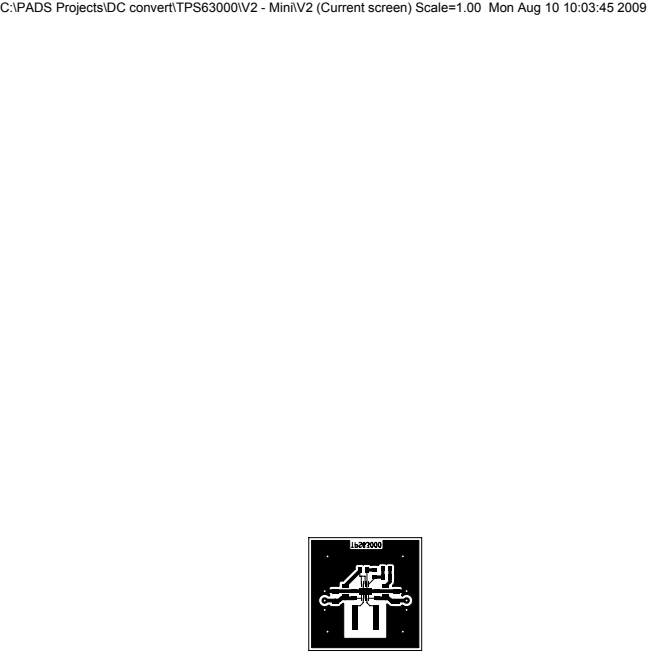
[picture p194: page 1]

C:\PADS Projects\DC convert\TPS63000\V2 - Mini\V2 (Current screen) Scale=1.00 Mon Aug 10 10:03:45 2009
