MLAB-project/Modules/power_sw/NFET2x2/sch/schema.pdf

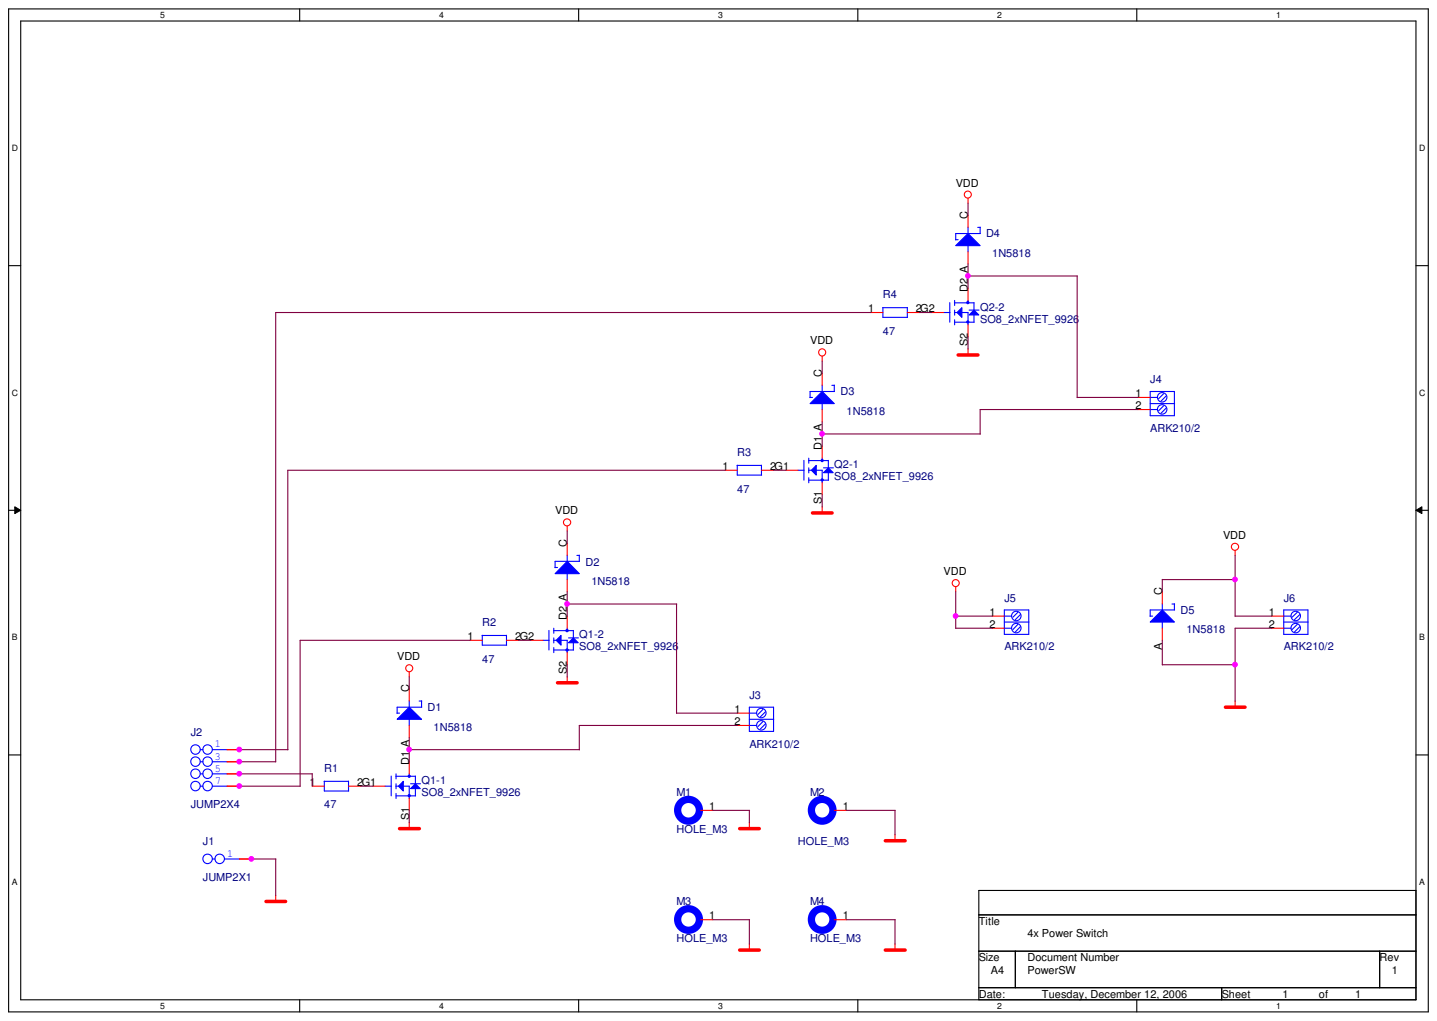
[picture p195: page 1]

Size A4 | Document Number PowerSW | Rev 1

Date: Tuesday, December 12, 2006 | Sheet 1 of 1
