MLAB-project/Modules/human_interface/LEDROBOT/sch/LEDROBOT_SCH.pdf

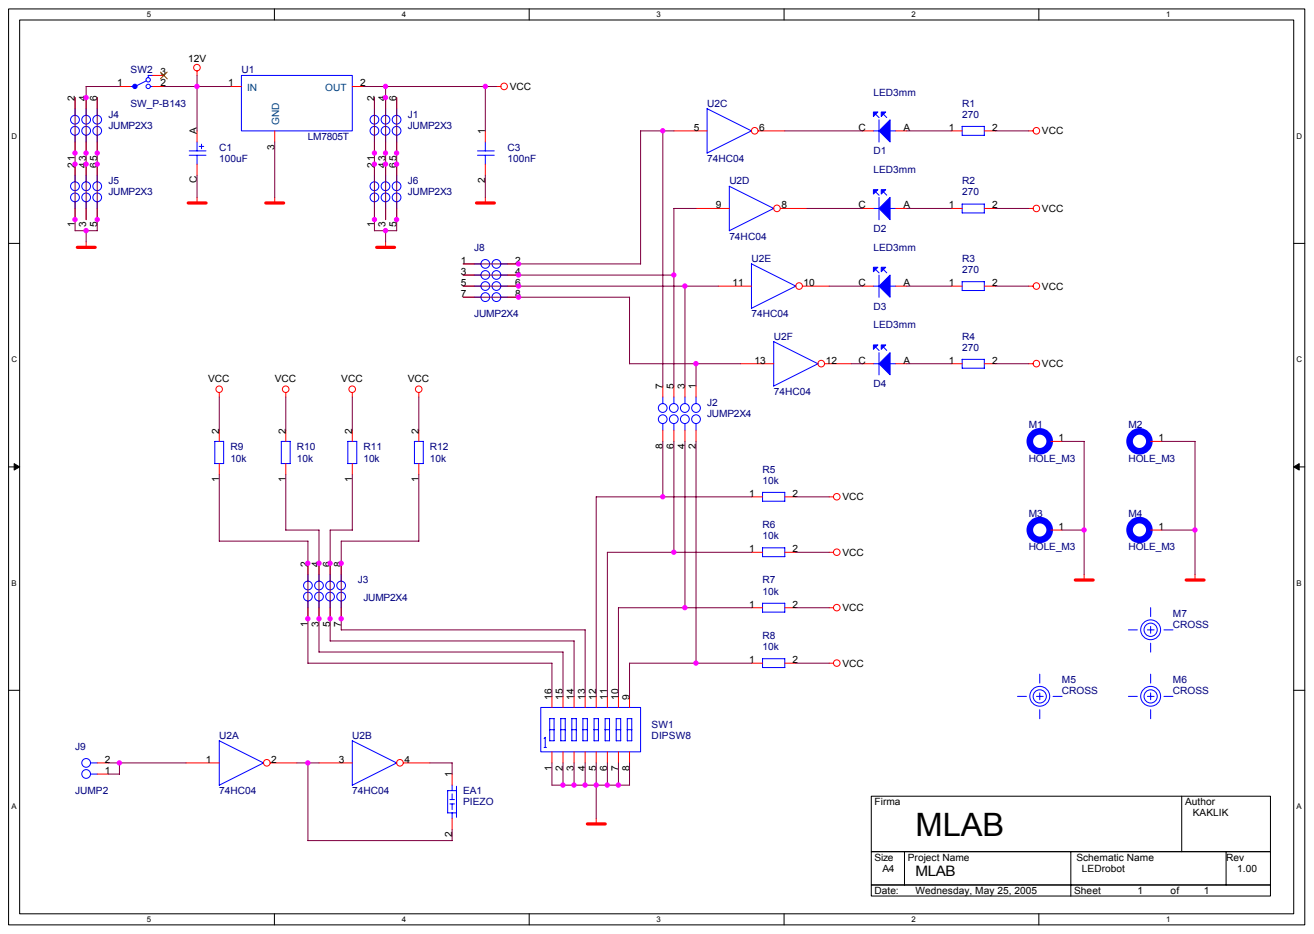
[picture p196: page 1]

12V SW2 U1 3 | | U2C 5 6 | LED3mm R1 270 D1 LED3mm D2 | VCC

Size A4 | Project Name MLAB | Schematic Name LEDrobot | Rev 1.00

Date: Wednesday, May 25, 2005 | | Sheet 1 of 1
