MLAB-project/Modules/sensors/G-metr/sch/Gmetr_sch.pdf

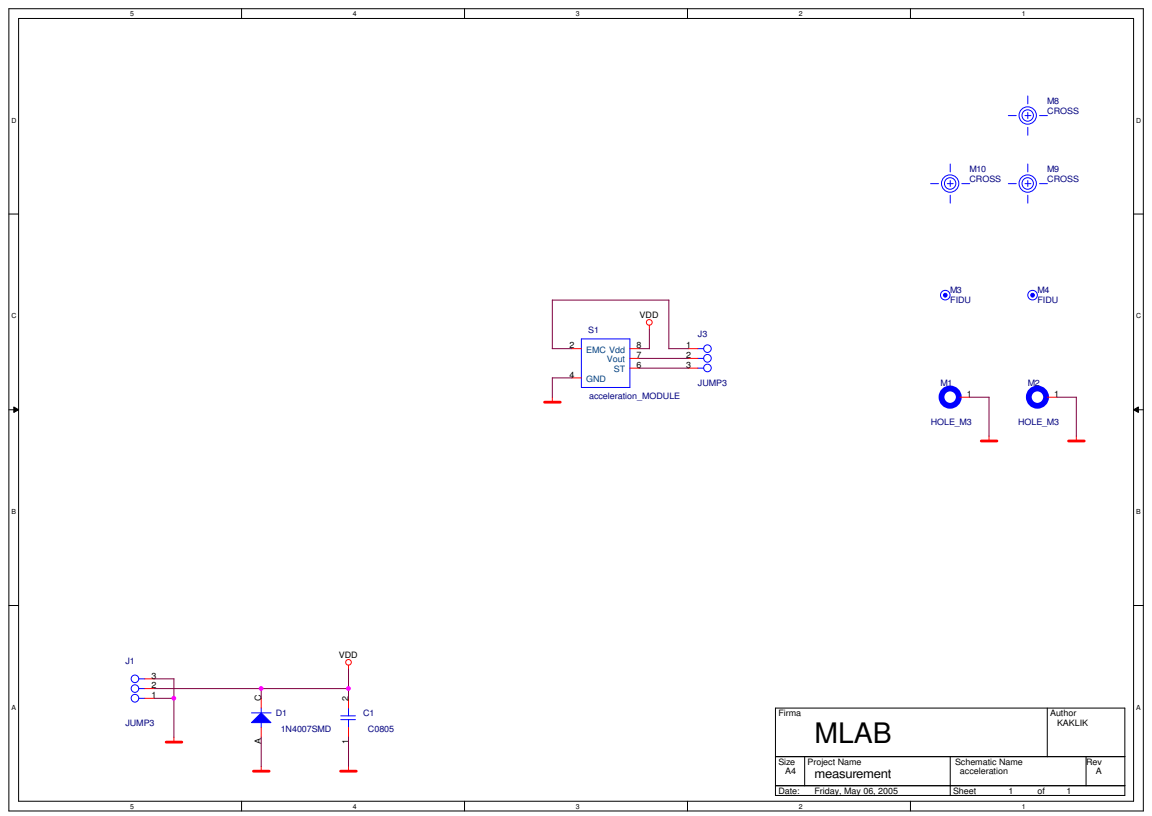
[picture p197: page 1]
VDD; HOLE; M8 CROSS; M3 FIDU; M9 CROSS; D1 1N4007SMD; M4 FIDU; M10 CROSS; JUMP3; acceleration; MODULE; 8 EMC; GND; Vout; Vdd

Firma MLAB | Author KAKLIK

Size A4 | Project Name measurement | Schematic Name acceleration | Rev A

Date: Friday, May 06, 2005 | | Sheet 1 of 1

5 | 4 | 3 | 2 | 1
