MLAB-project/Modules/CPLD_FPGA/XILINX_XVC/XVC_FT220X02A/sch/XVC_FT220X02A_SCH.pdf

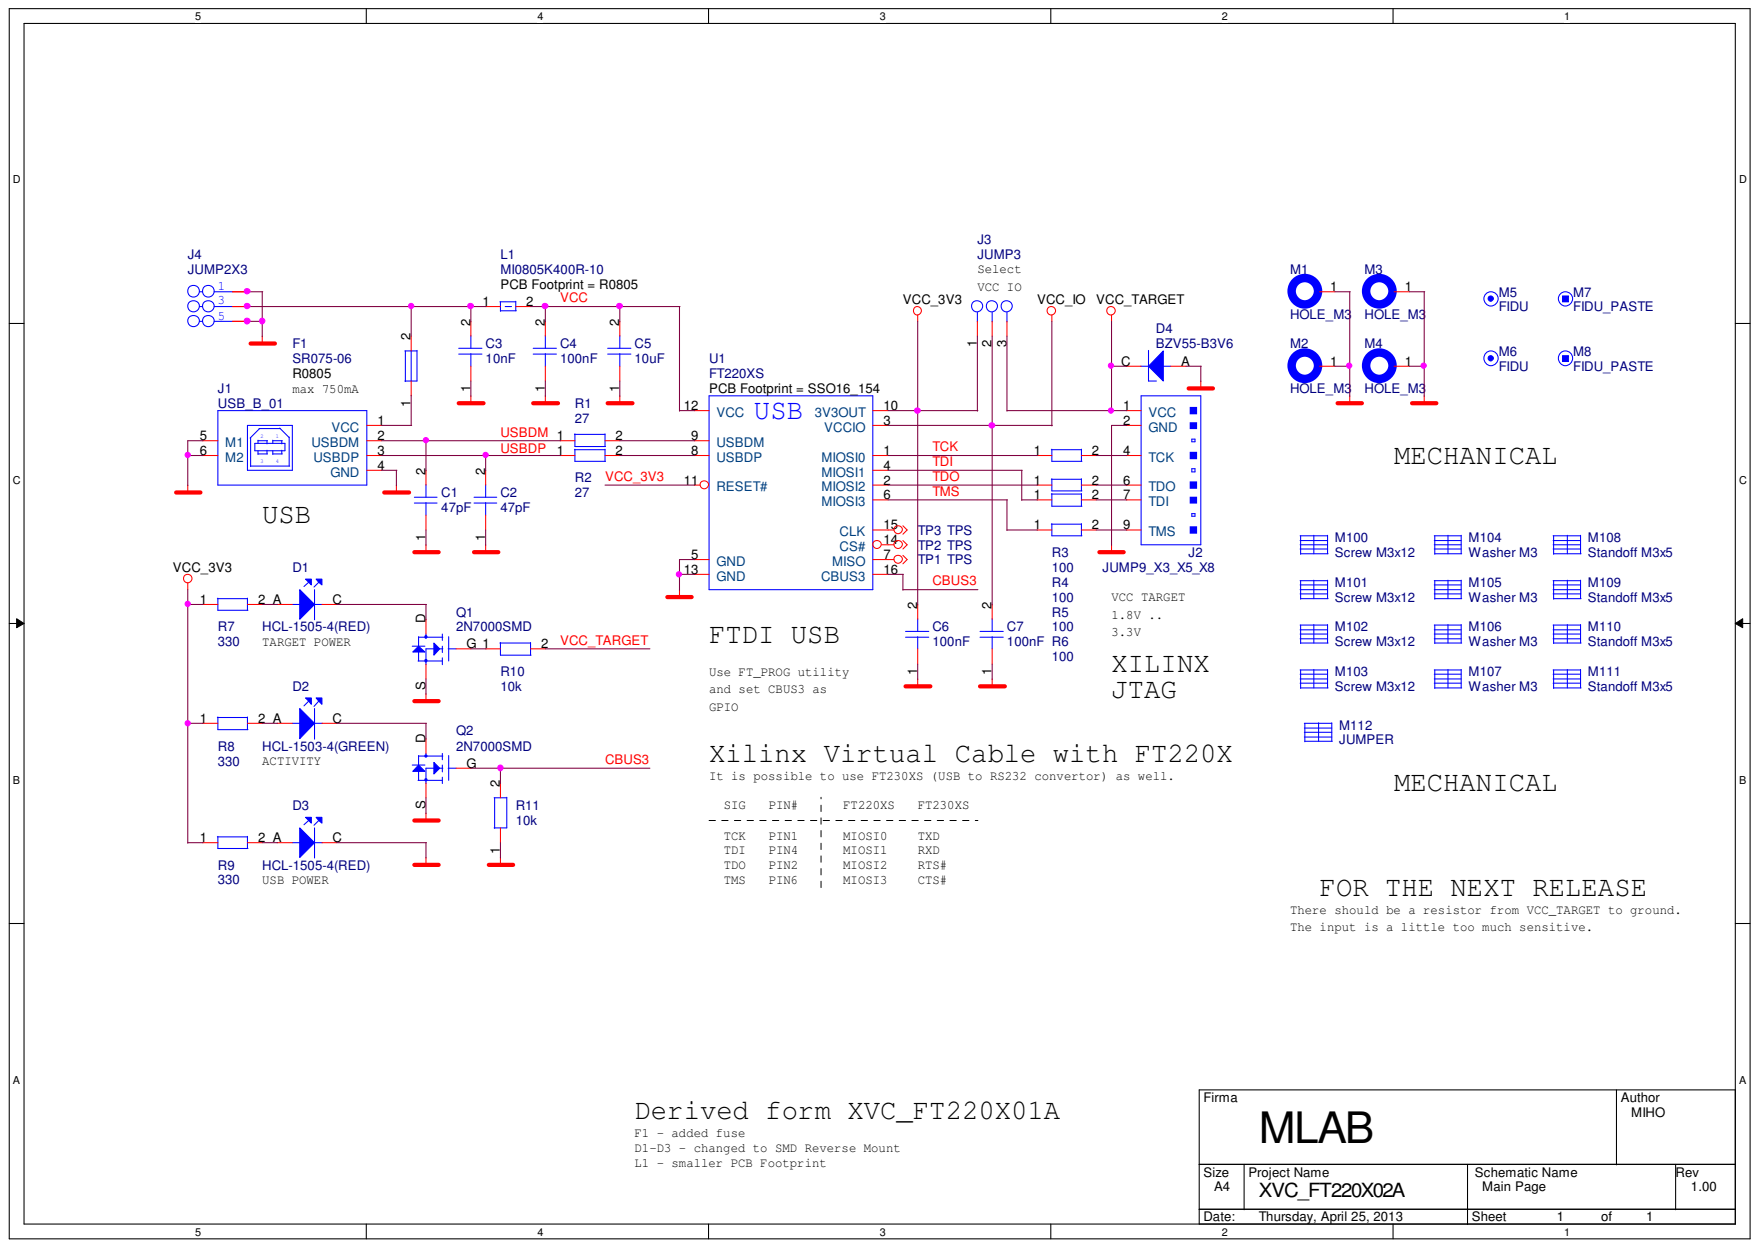
[picture p198: page 1]

1 | TCK | | 4

4 | | 5 | | 4 | TDI | | 6

2 | TDO
6 | TMS | | 1 | | 2 | 7

Use FT_PROG utility
and set CBUS3 as
GPIO
Xilinx Virtual Cable with FT220X

It is possible to use FT230XS (USB to RS232 convertor) as well.

FOR THE NEXT RELEASE

There should be a resistor from VCC_TARGET to ground.
The input is a little too much sensitive.

Firma MLAB | Author MIHO

F1 - added fuse
D1-D3 - changed to SMD Reverse Mount
L1 - smaller PCB Footprint

Size A4 | Project Name XVC_FT220X02A | Schematic Name Main Page | Rev 1.00

Date: Thursday, April 25, 2013 | | Sheet 1 of 1
