MLAB-project/Modules/CPLD_FPGA/XILINX_XVC/XVC_FT220X01A/sch/XVC_FT220X01A_SCH.pdf

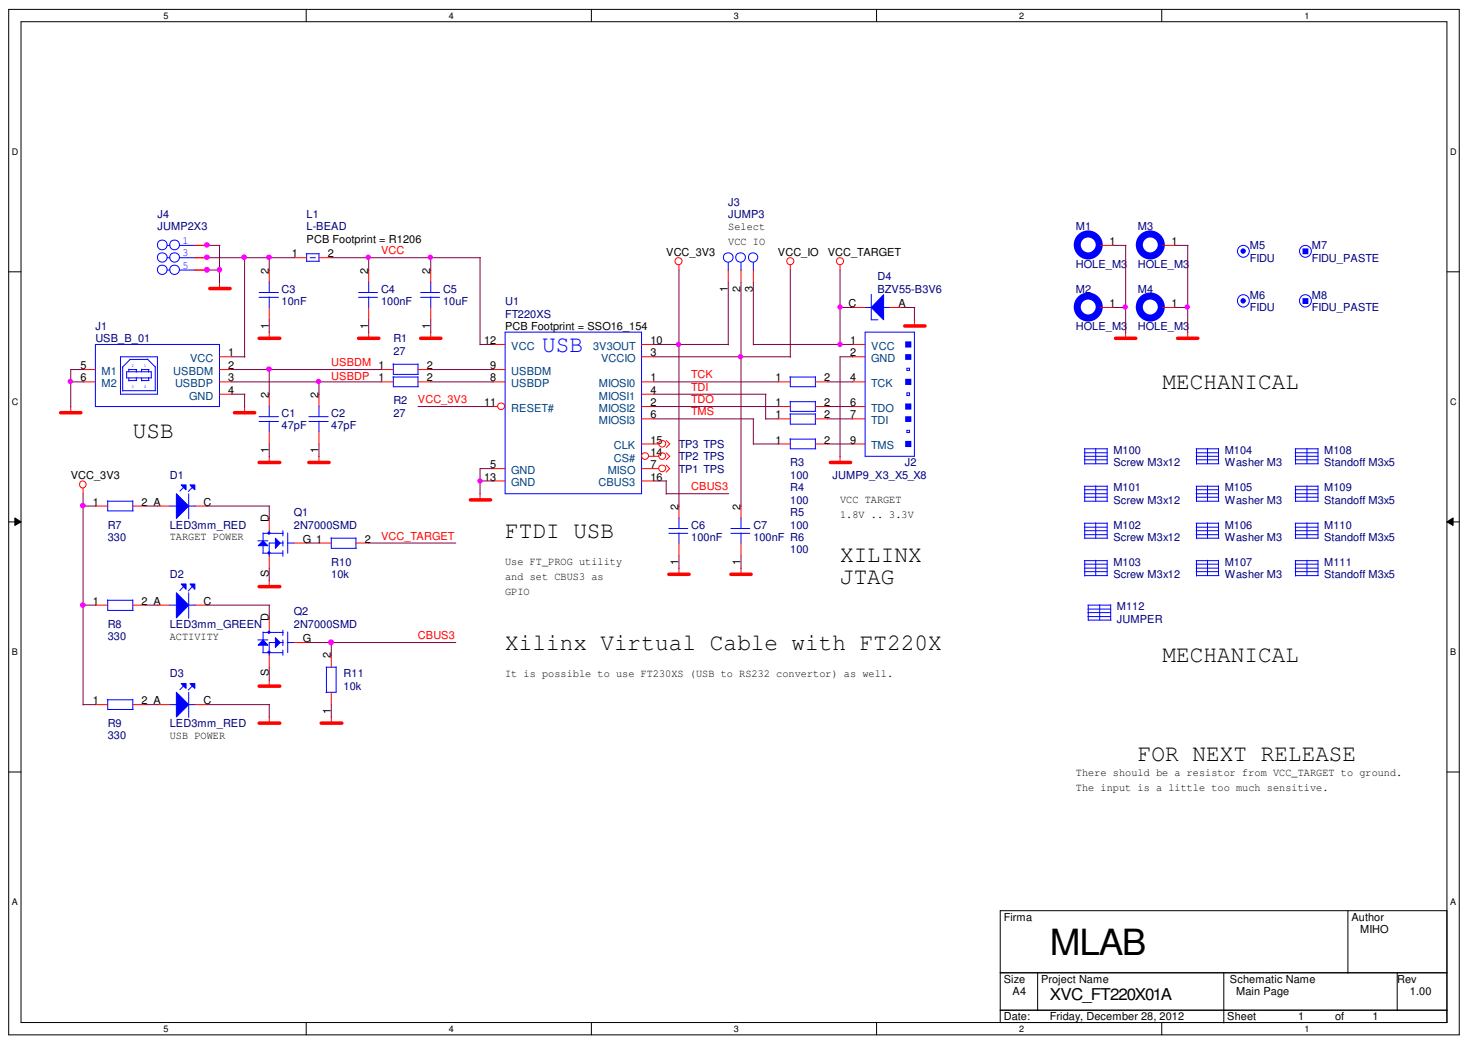
[picture p199: page 1]

4 | | 5 | | 4 | TDI | | 6

2 | TDO
6 | TMS | | 1 | | 2 | 7

Xilinx Virtual Cable with FT220X

It is possible to use FT230XS (USB to RS232 convertor) as well.

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

Firma MLAB | Author MIHO

Size A4 | Project Name XVC_FT220X01A | Schematic Name Main Page | Rev 1.00

Date: Friday, December 28, 2012 | | Sheet 1 of 1
