MLAB-project/Modules/MCU_CPU/ARM/ODroid-X2/sch/Exynos4412CPUMudule_REV0.2.pdf

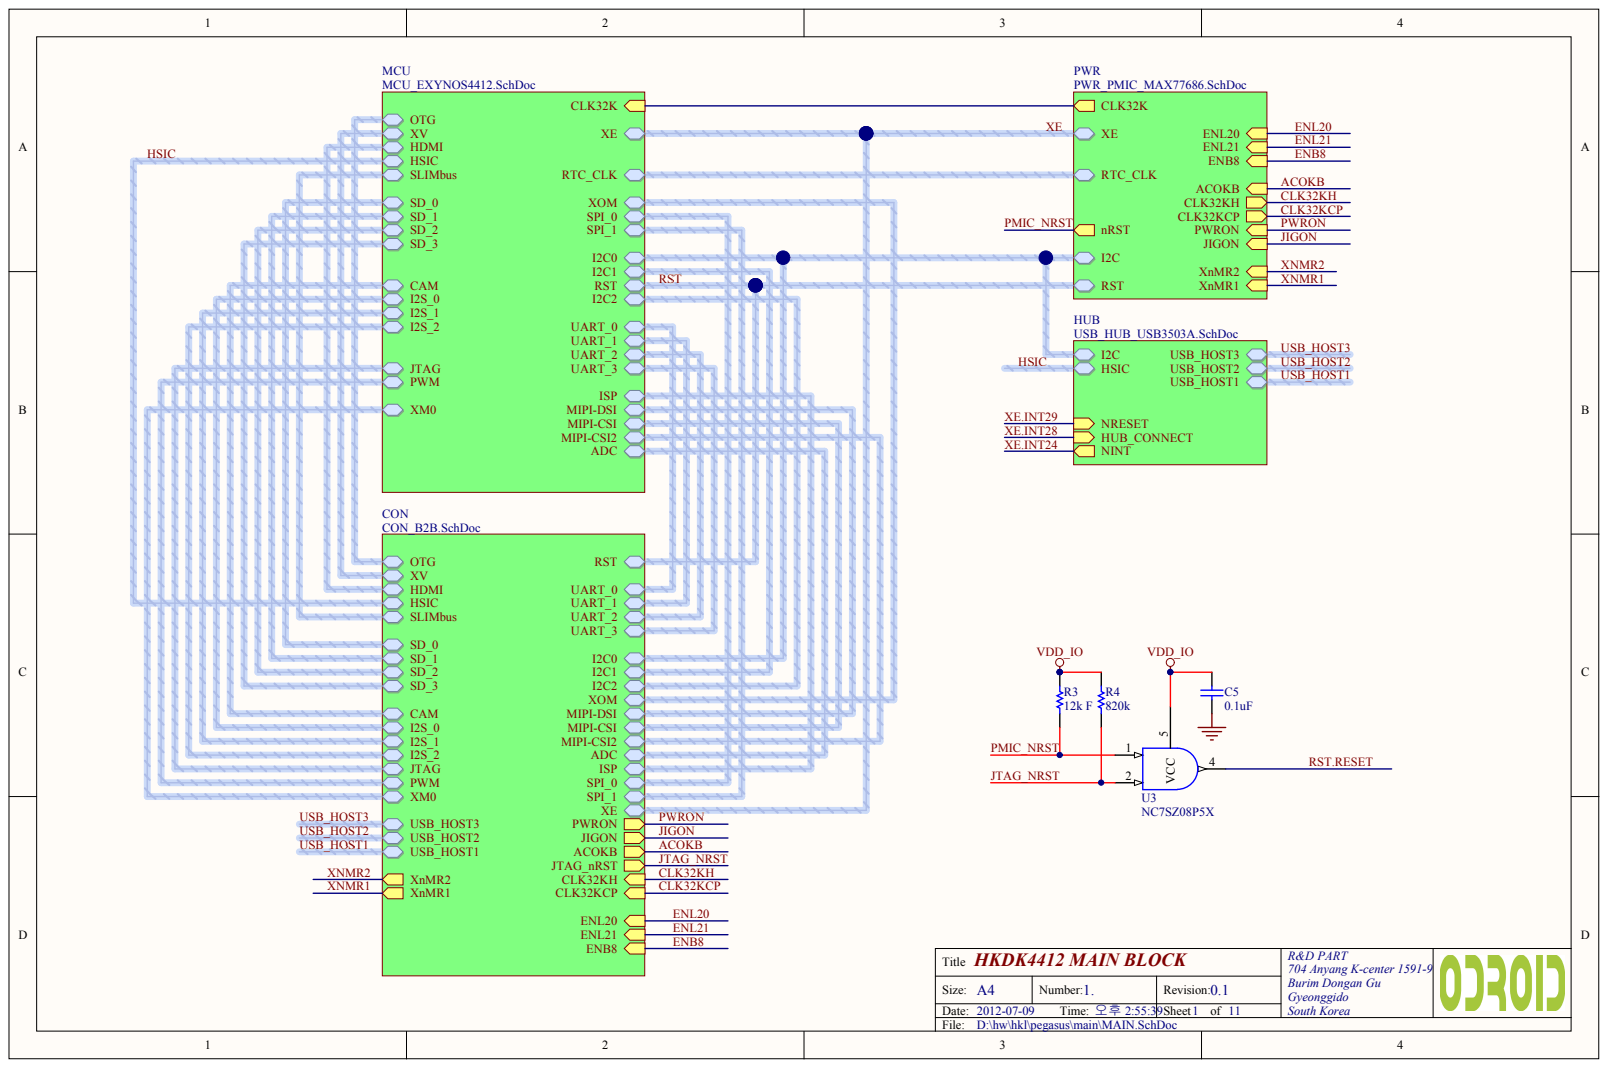
[picture p200: page 1]

HKDK4412 MAIN BLOCK Title | R&D PART 704 Anyang K-center 1591-9 Burim Dongan Gu Gyeonggido South Korea

A4 Size: | 1. 0.1 Number: | Revision:
Date: 2012-07-09 Time: 오후 2:55:39 | | Sheet of 11

D:\hw\hkl\pegasus\main\MAIN.SchDoc

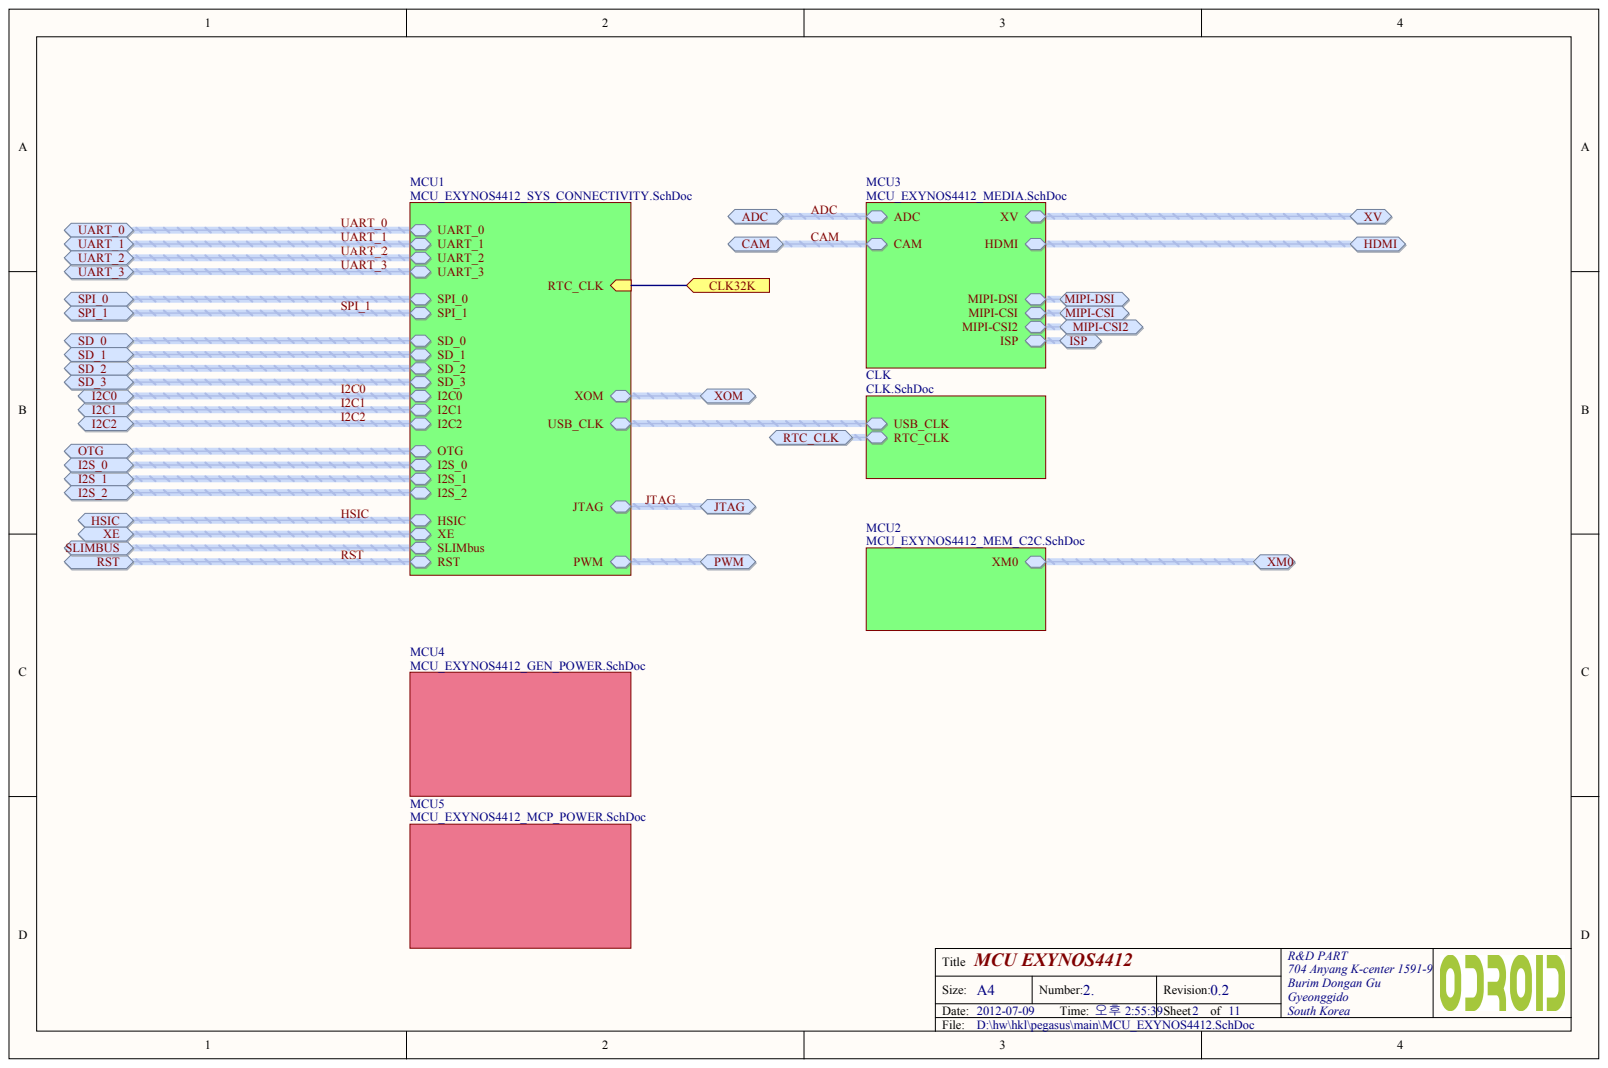
[picture p201: page 2]

MCU EXYNOS4412 Title | R&D PART 704 Anyang K-center 1591-9 Burim Dongan Gu Gyeonggido

A4 Size: | 2. 0.2 Number: | Revision:

2012-07-09 Time: 오후 2:55:39 | | Sheet of

D:\hw\hkl\pegasus\main\MCU_EXYNOS4412.SchDoc

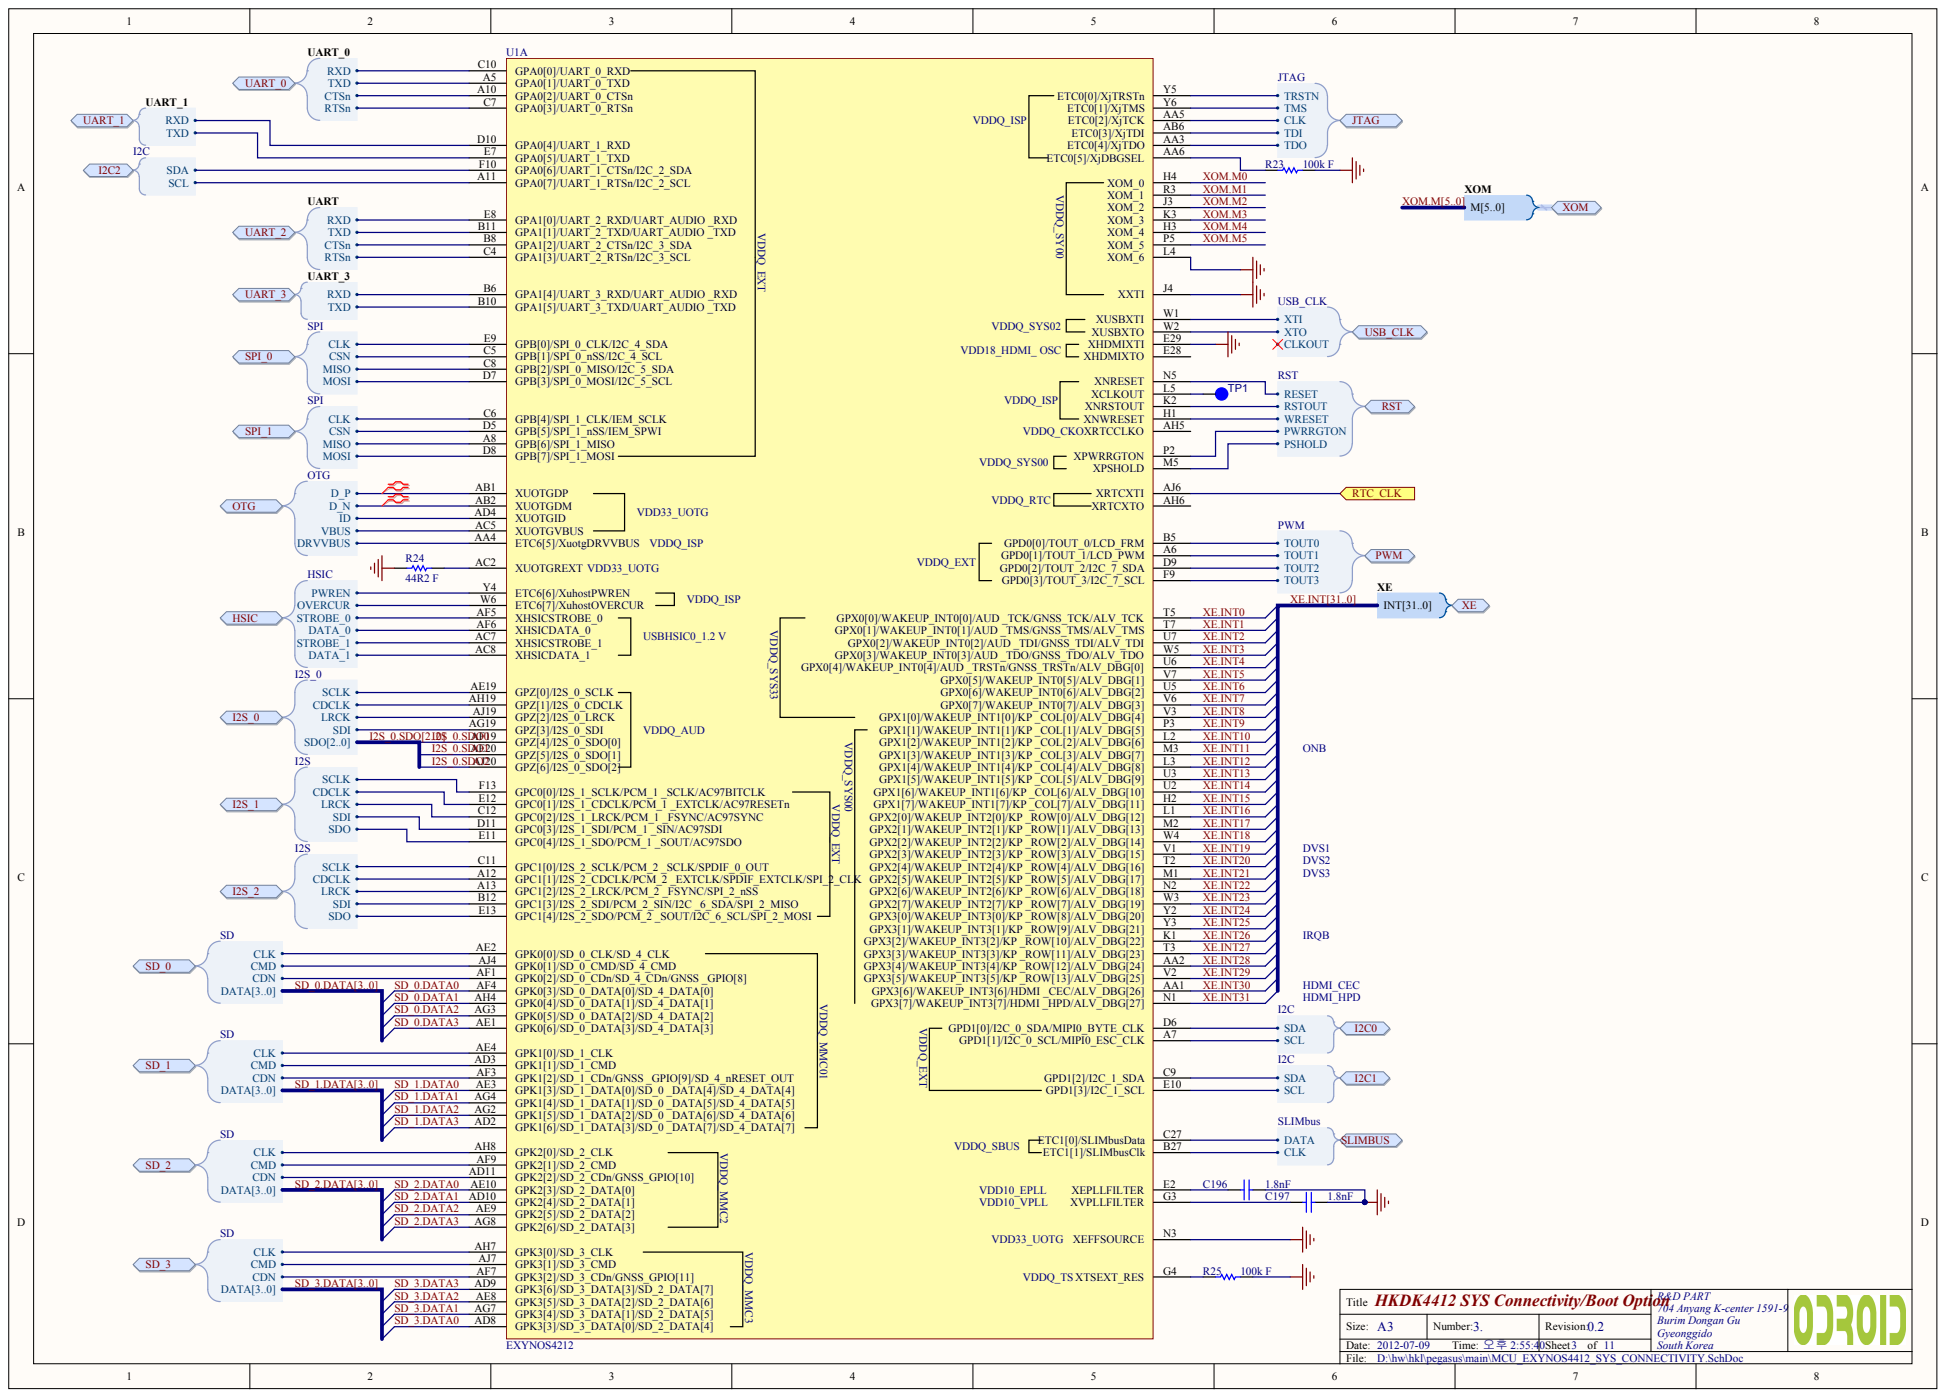
[picture p202: page 3]

XE.INT0 XE.INT1 XE.INT2 XE.INT3 XE.INT4 XE.INT5 XE.INT6 XE.INT7 XE.INT8 XE.INT9 XE.INT10 XE.INT11 XE.INT12 XE.INT13 XE.INT14 XE.INT15 XE.INT16 XE.INT17 XE.INT18 XE.INT19 XE.INT20 XE.INT21 XE.INT22 XE.INT23 XE.INT24 XE.INT25 XE.INT26 XE.INT27 XE.INT28 XE.INT29 XE.INT30 XE.INT31

Ti t l e | R& D PART 704 Anyang K-center 1591-9 Buri m Dongan G u Gyeonggido

Size: A | Number: | Revision:

me: | | Sheet of

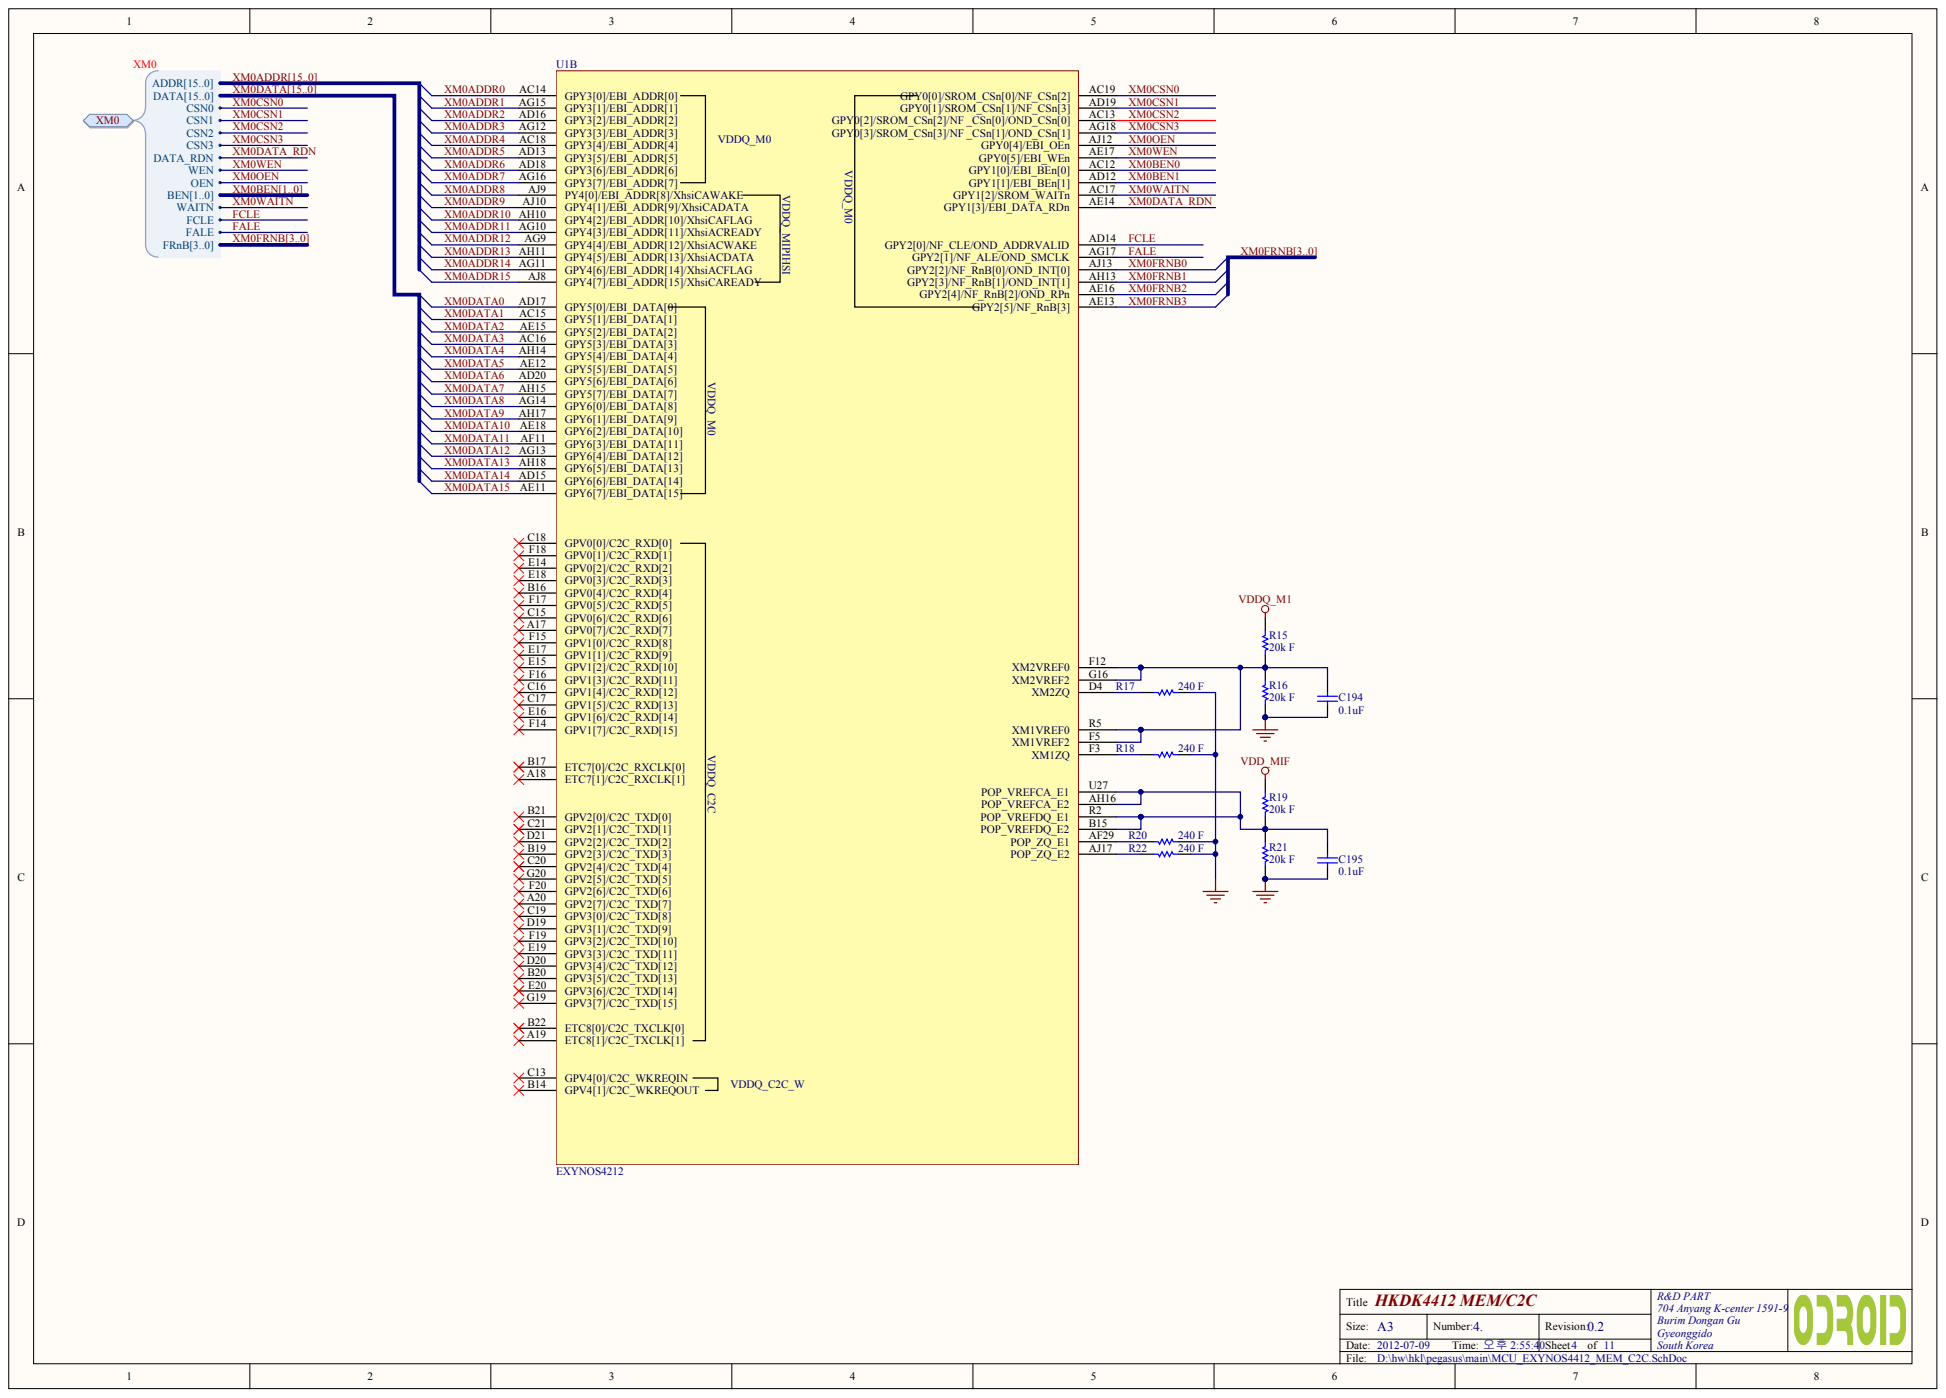
[picture p203: page 4]

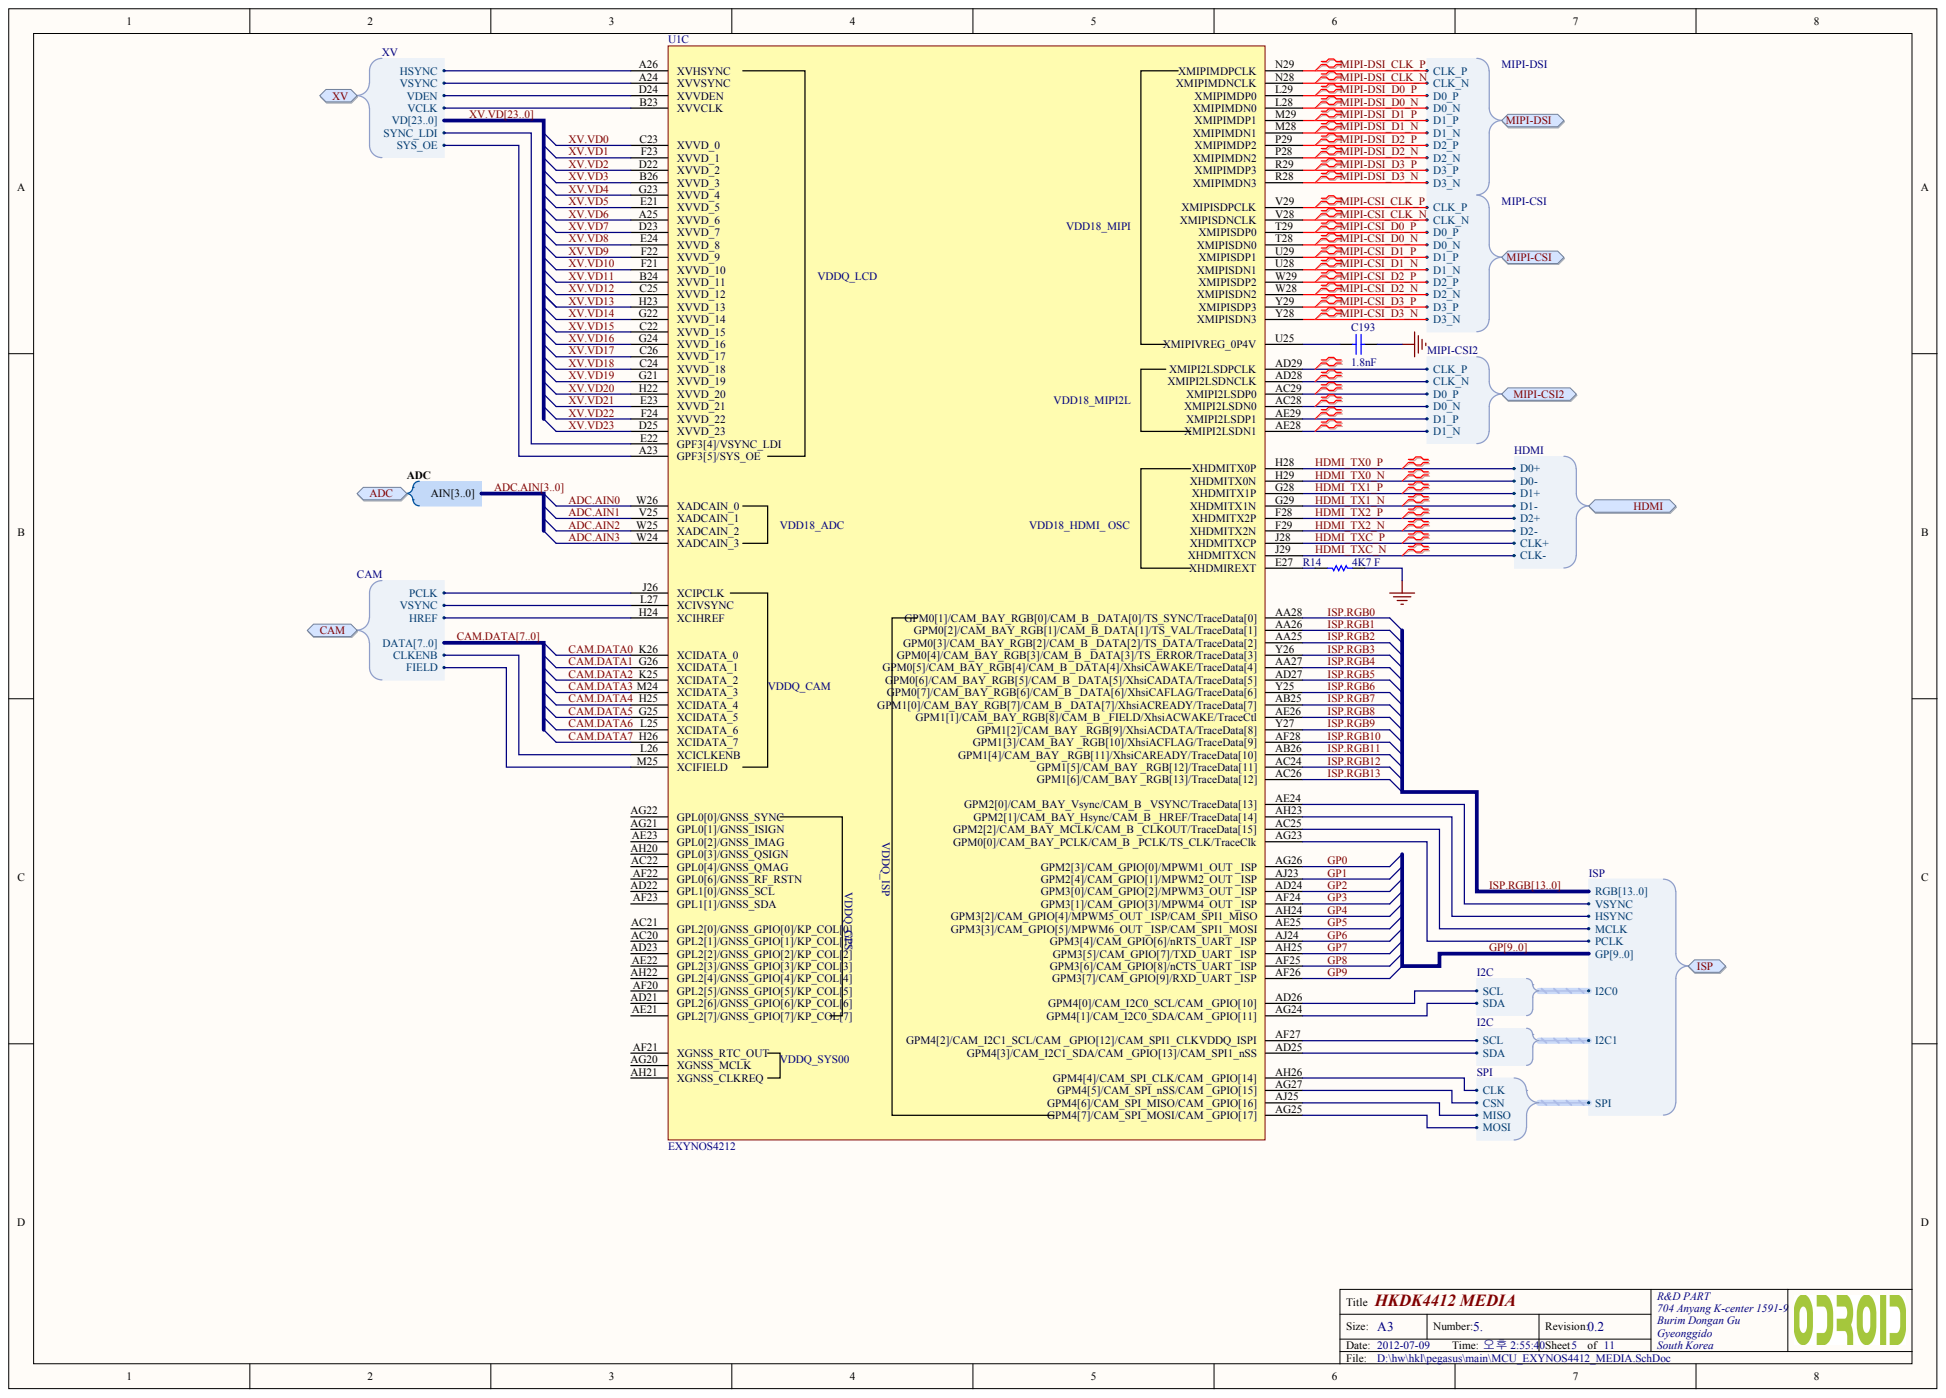
[picture p204: page 5]

CAM. D ATA | 1
CAM. D ATA | 2 3 4 5 6 7

A H24
AE25
AJ24

A G27
AJ25
A G25

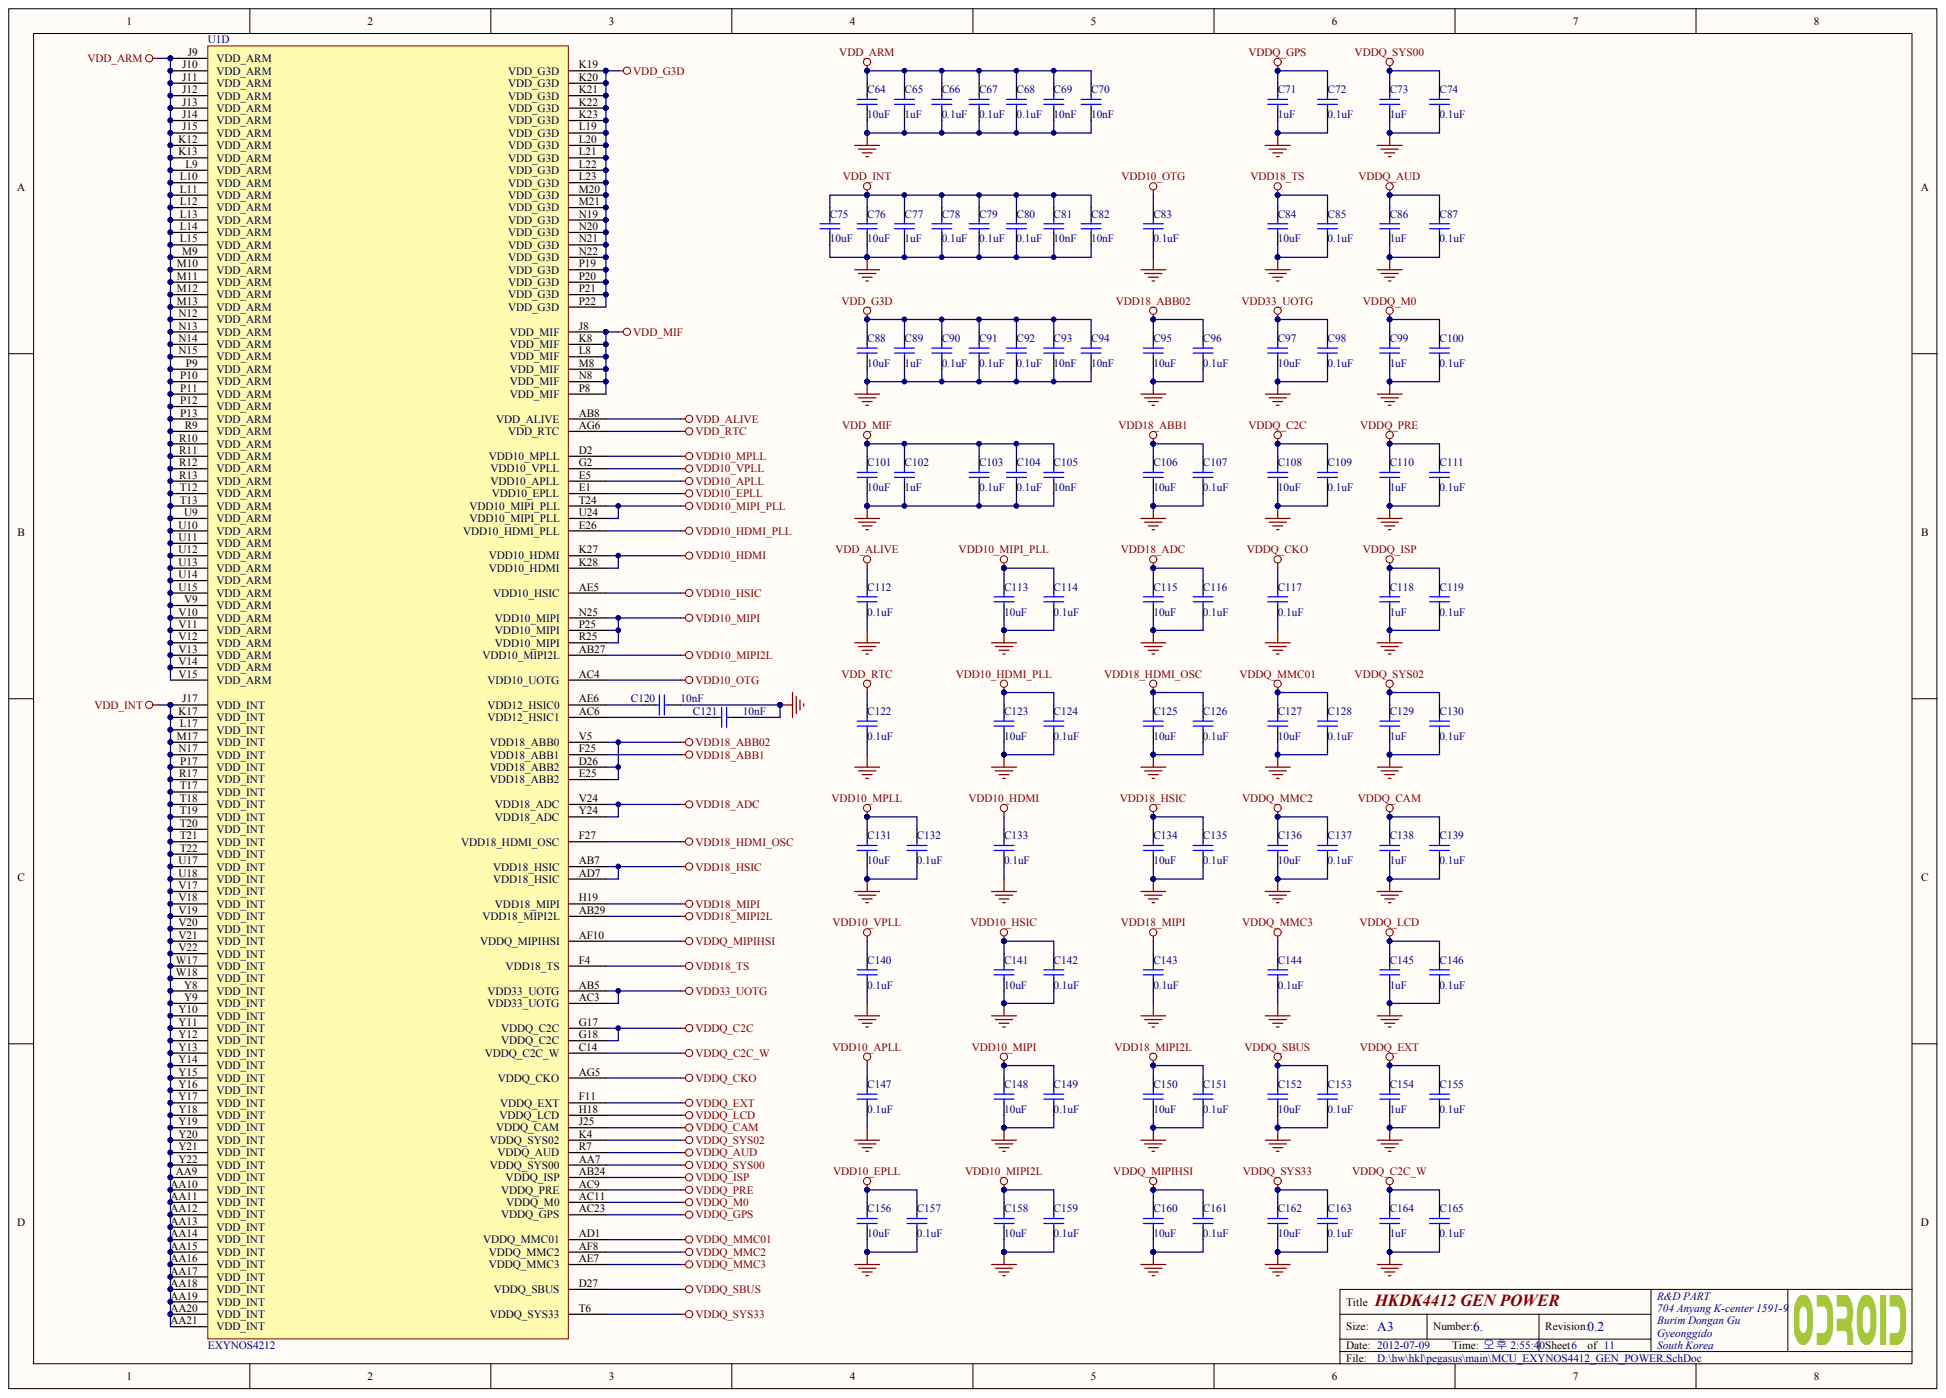
[picture p205: page 6]

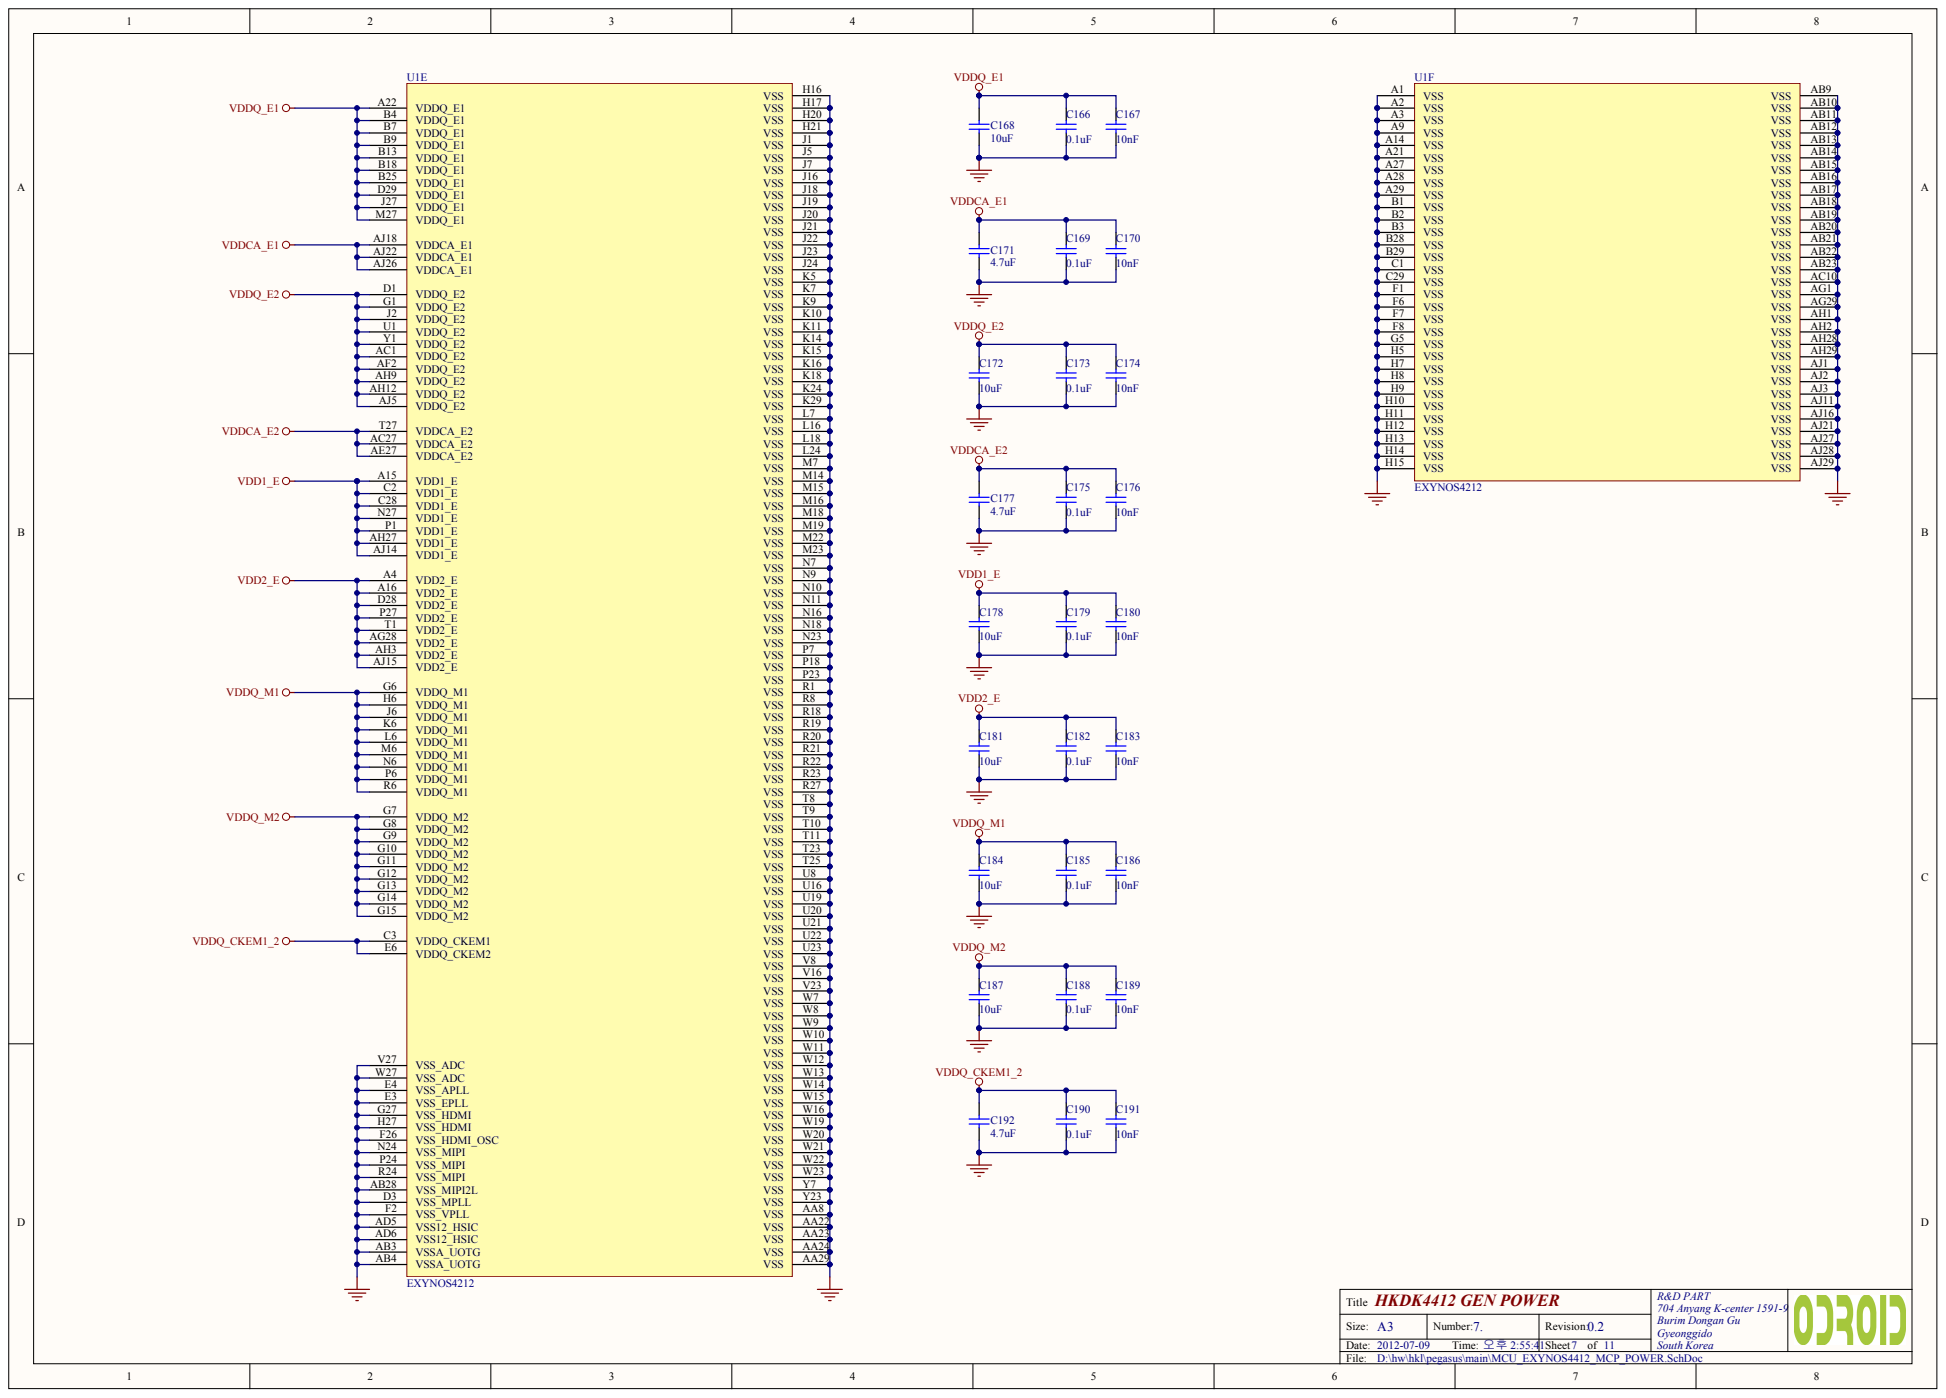
[picture p206: page 7]

A14 | AB13
A21 | AB14

A28 | AB16
A29 | AB17

A G28
A H 3

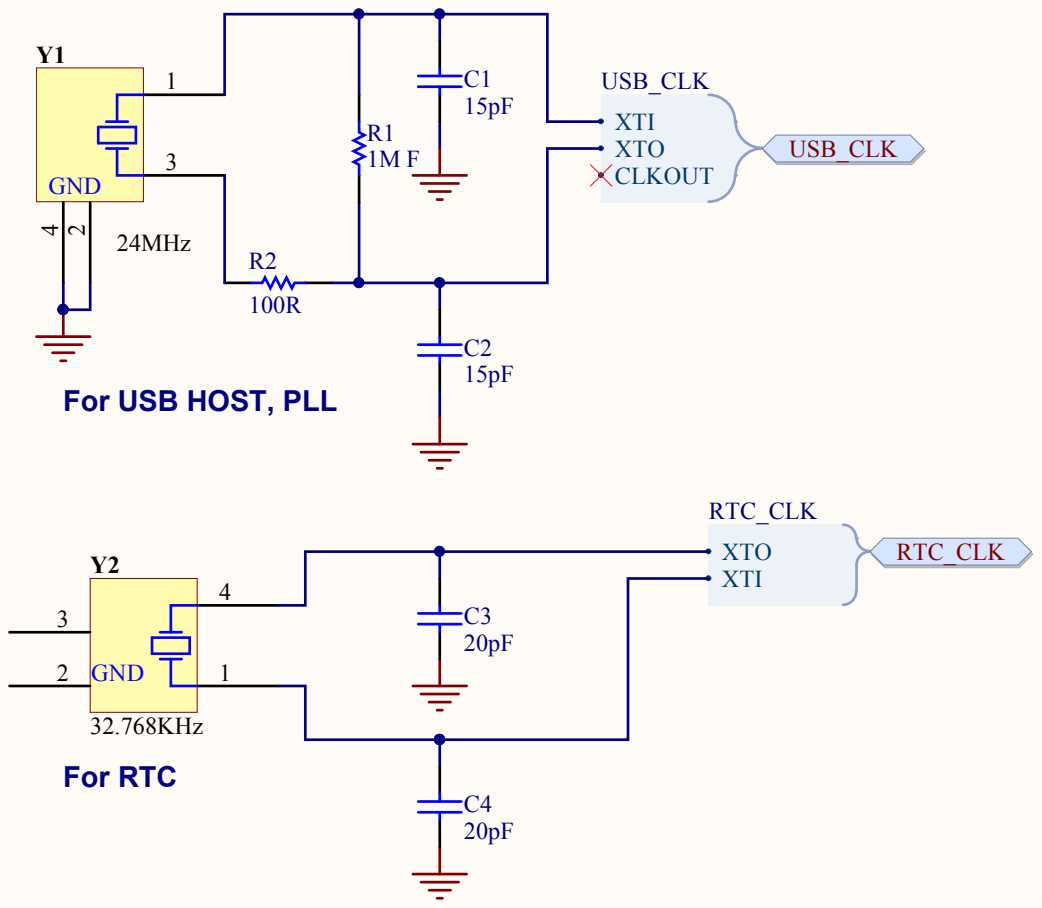
[picture p207: page 8]

For USB HOST, PLL

CLK Title | R&D PART 704 Anyang K-center 1591-9 Burim Dongan Gu Gyeonggido

A4 Size: | 8. 0.2 Number: | Revision:

2012-07-09 Time: 오후 2:55:41 | | Sheet of

D:\hw\hkl\pegasus\main\CLK.SchDoc

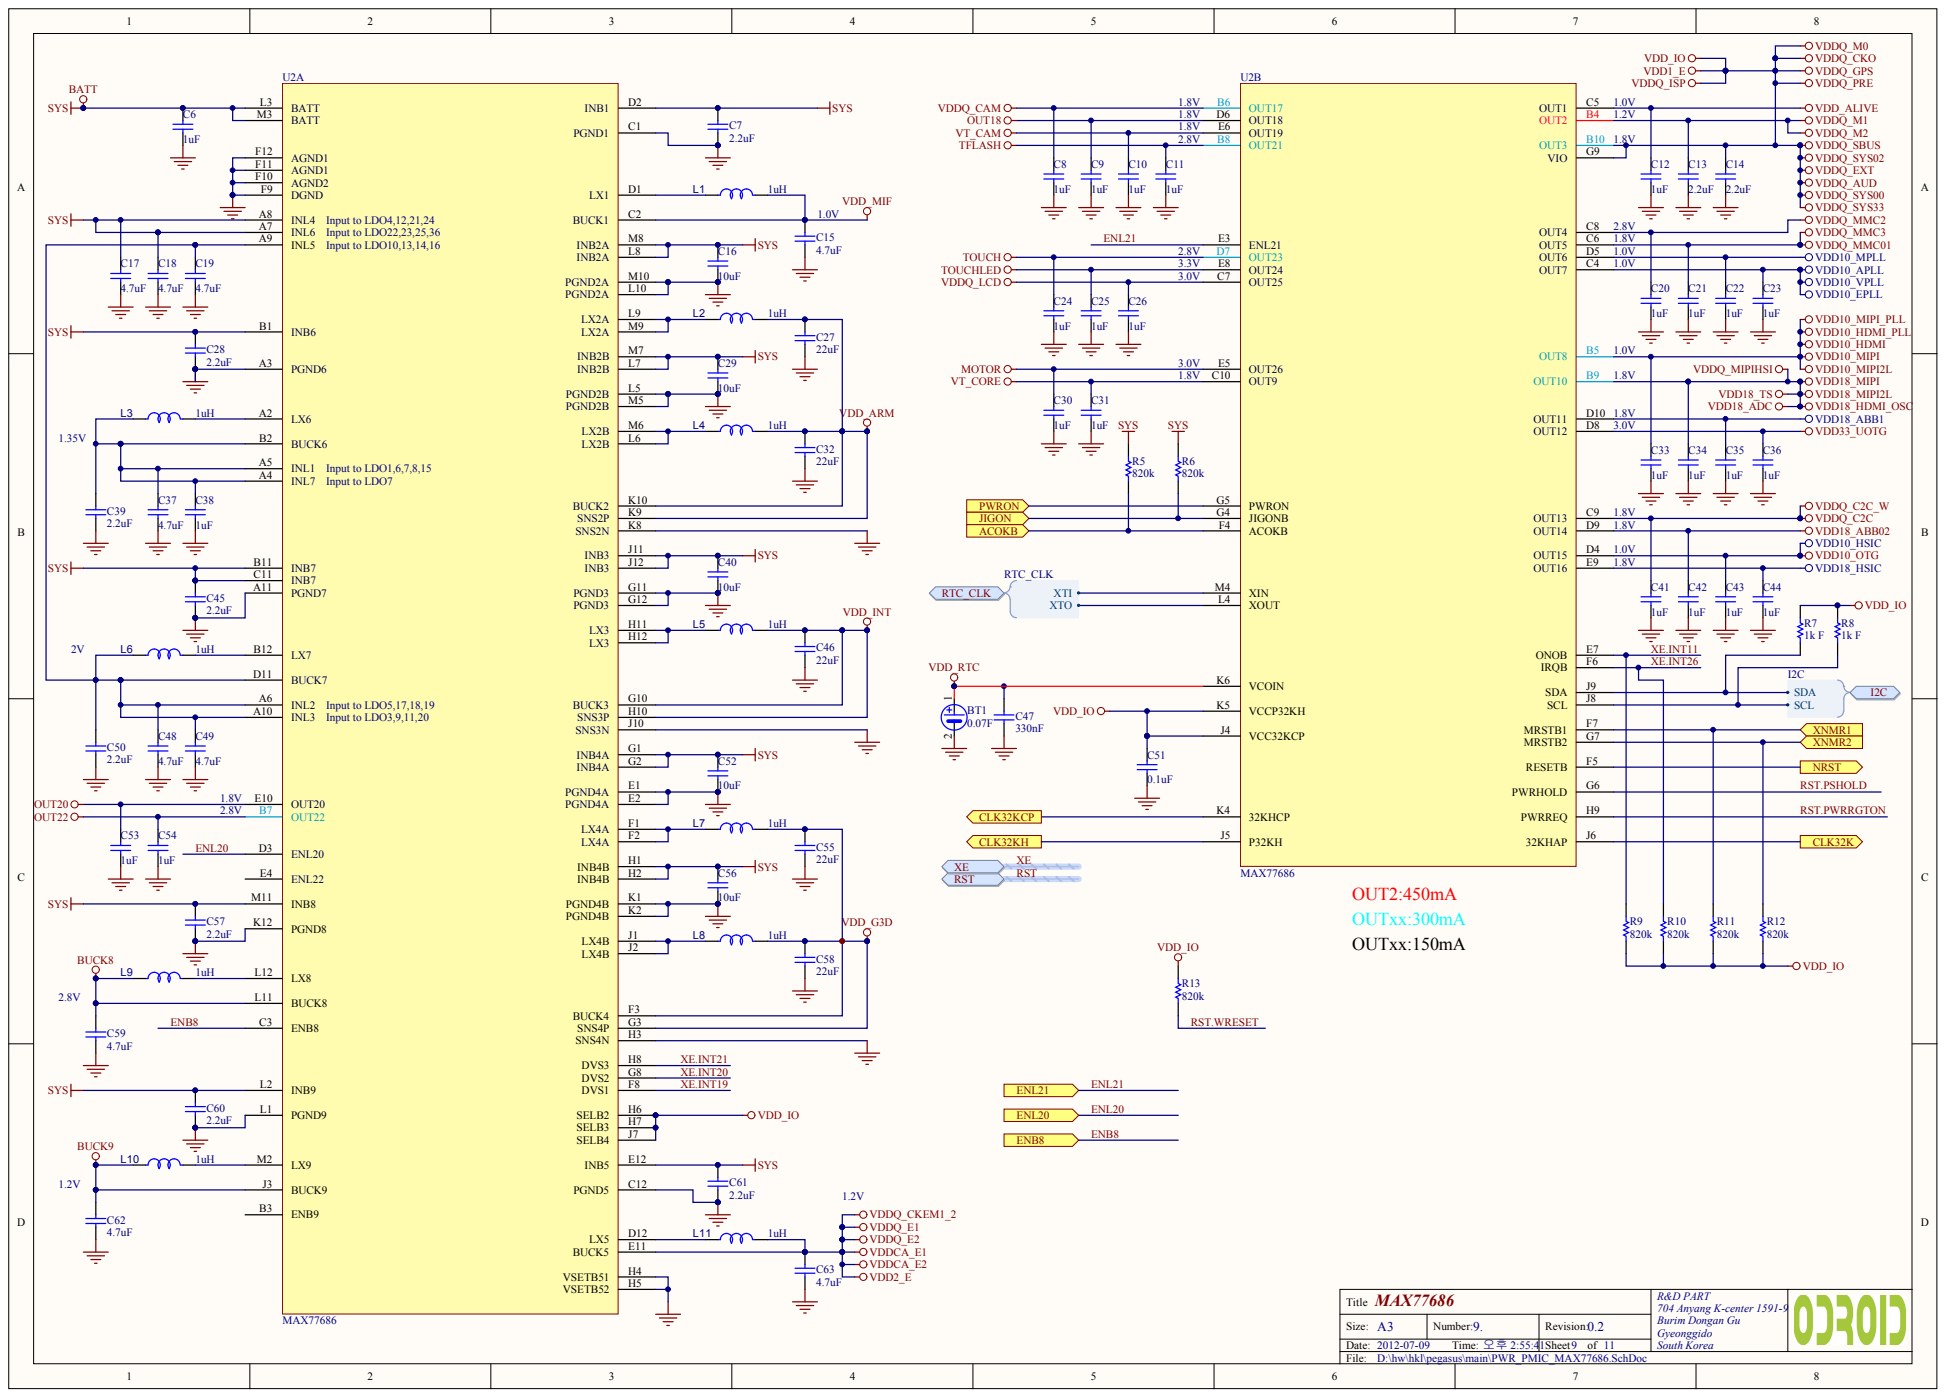
[picture p208: page 9]

1.8V | | 1.8V
2.8V

ENL21 E3 OUT26 E5 OUT19 E6 OUT24 E8 | C12 | C14

3.3V | | 1.0V
3.0V | | C20 | C22

A 6
A10 | H10

VCC32KCP J4 | SD

INB8 M11 | K 1

H 4

MAX77686

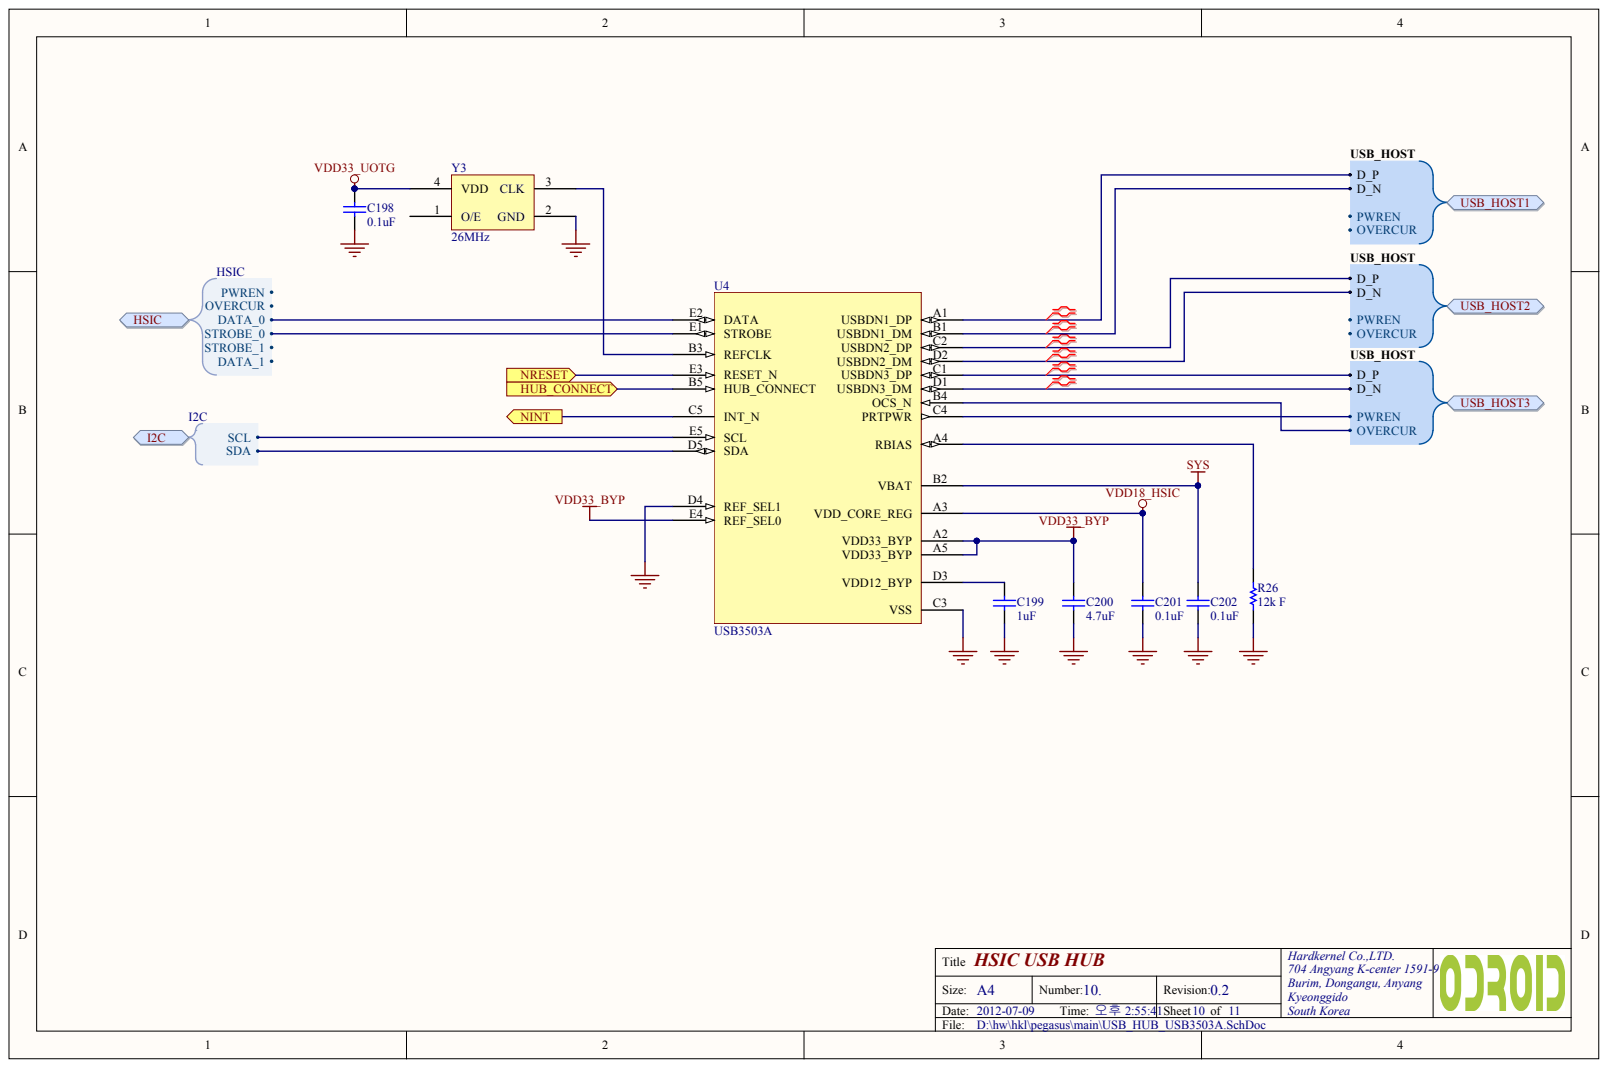
[picture p209: page 10]

HSIC USB HUB Title | Hardkernel Co.,LTD. 704 Angyang K-center 1591-9 Burim, Dongangu, Anyang Kyeonggido

A4 Size: | 10. 0.2 Number: | Revision:

2012-07-09 Time: 오후 2:55:41 | | Sheet of

D:\hw\hkl\pegasus\main\USB_HUB_USB3503A.SchDoc

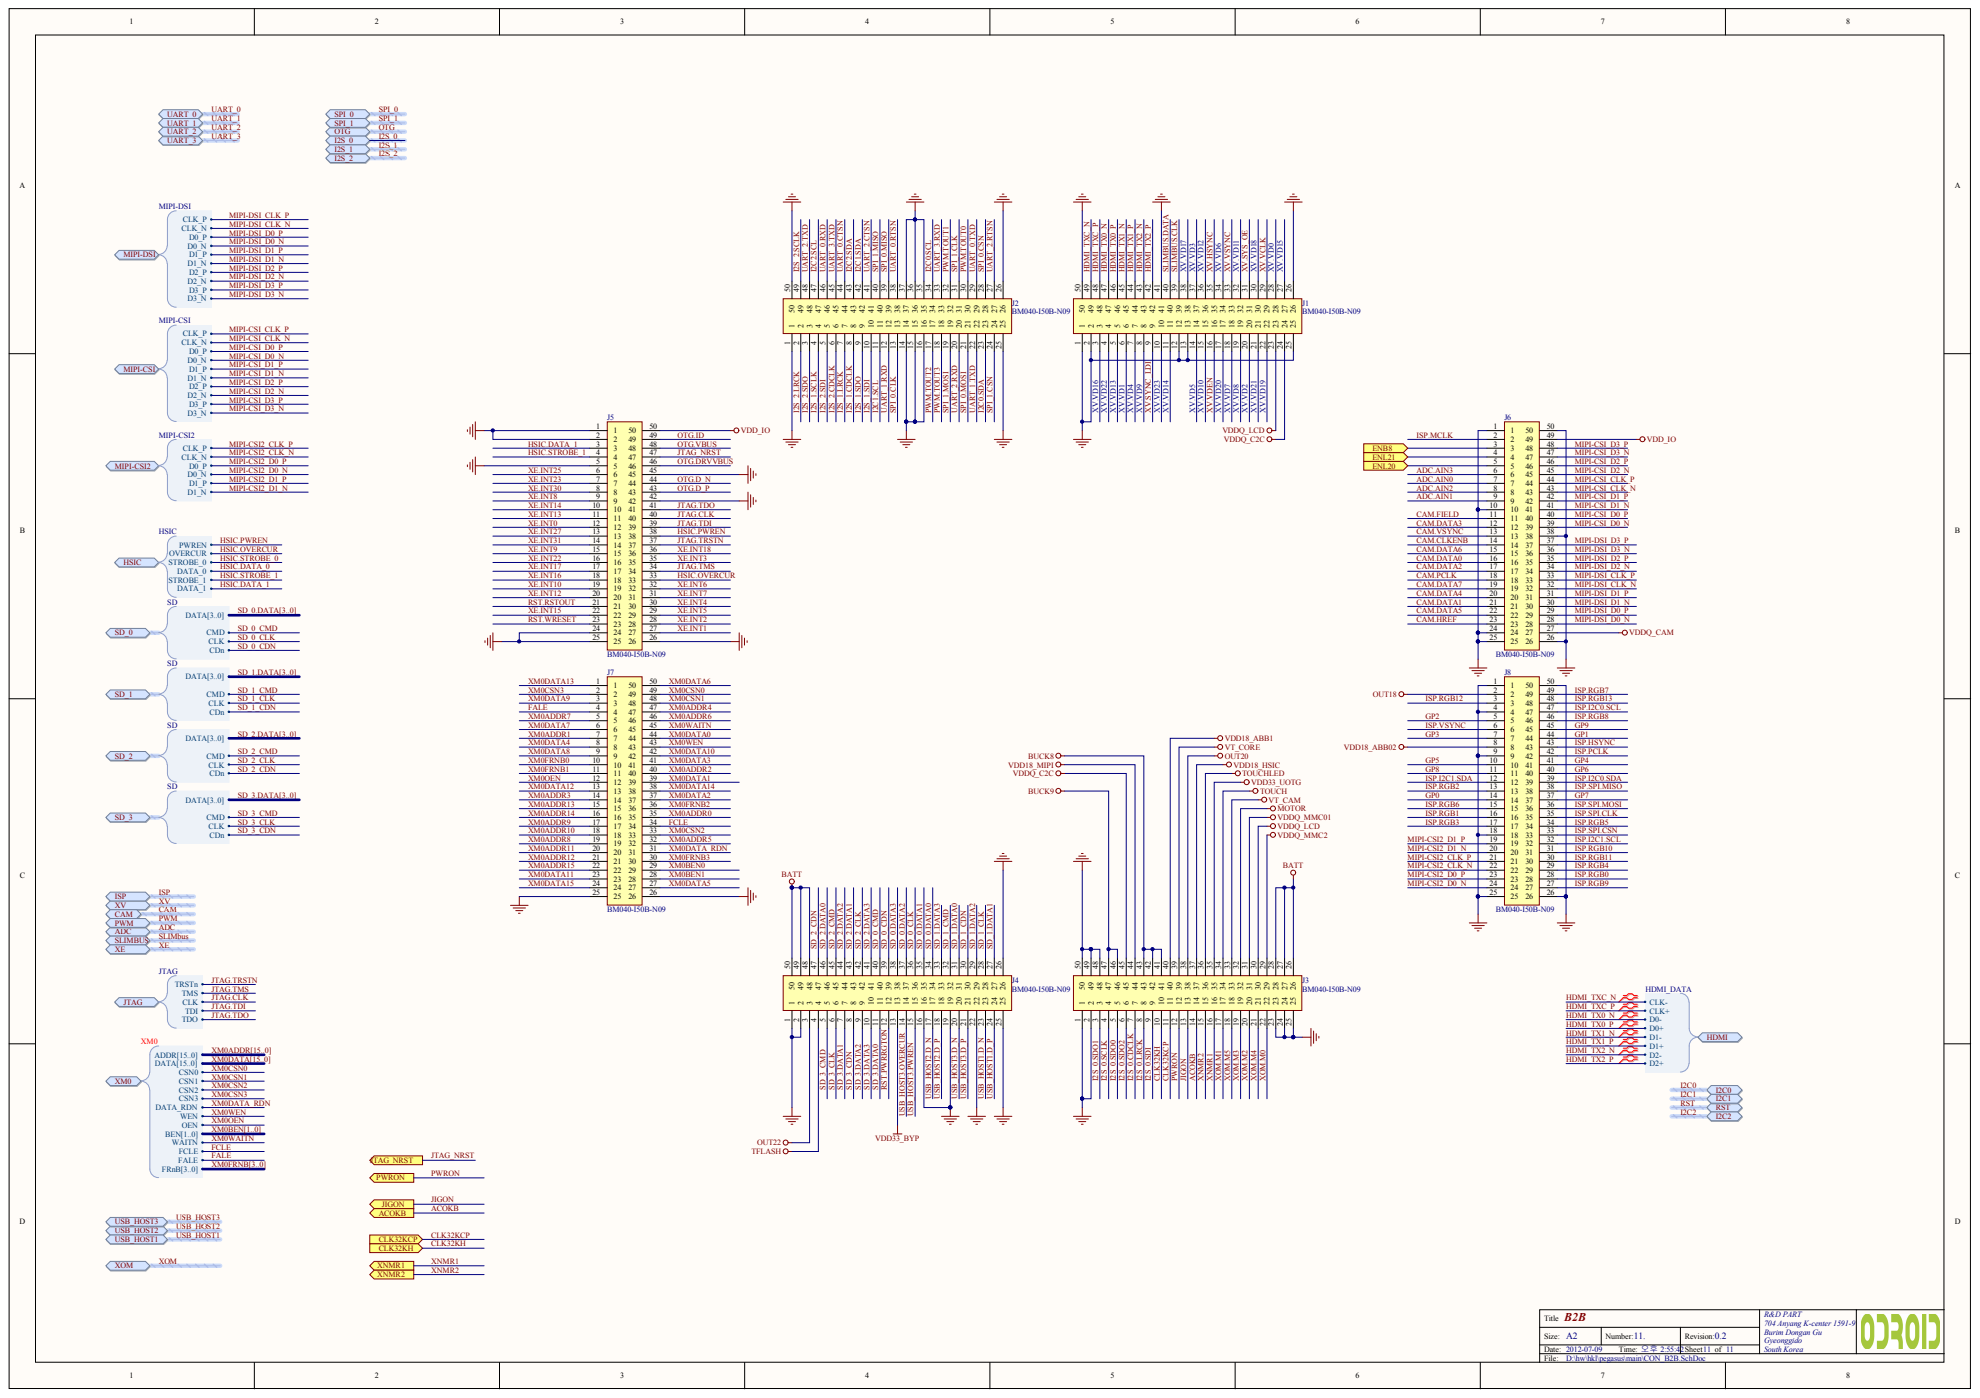
[picture p210: page 11]

T i B2B | R&D PA R T 4 A nya ng K-cen ter 1 1-9 B r i m D o nga n G Gyeo ngg i do So th Ko rea

A2 | 11. 0.2 | Rev i s i o n :
9 오후 2 2-0 7-0 T ime: : : | | Sheet o f
