MLAB-project/Modules/MCU_CPU/ARM/ODroid-X2/sch/ODROID-X_EMMC_BD_rev0.1.pdf

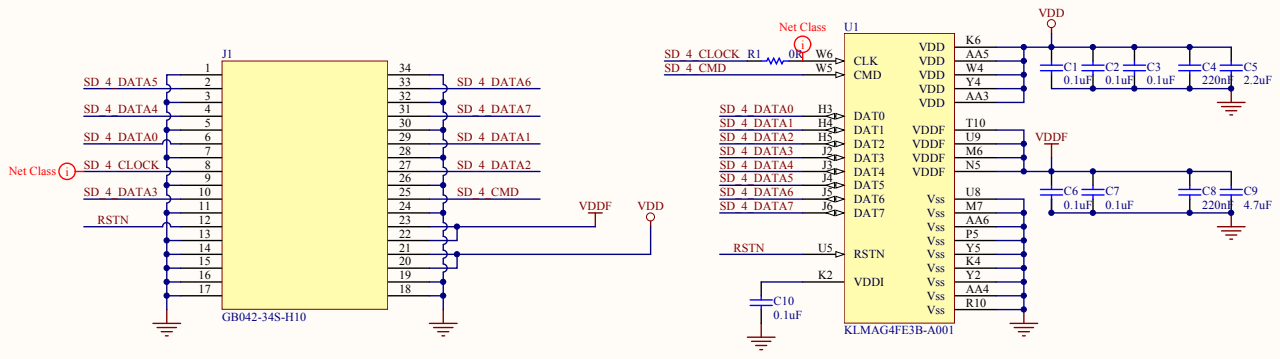
[picture p211: page 1]

12 | 23
13 | 22
14 | 21

16 | 19
17 | 18

eMMC Board Title | R&D PART 704 Anyang K-center 1591-9 Burim Dongan Gu Gyeonggido South Korea

A4 Size: | 1 Number: | 0.1 Revision:

2011-12-27 Time: 10:20:52 | | Sheet 1 of 1

C:\work_altium\hardkernel\hw\hkl\pegasus\emmc-bd\EMMC.SchDoc
