MLAB-project/Modules/MCU_CPU/ARM/ODroid-X2/sch/ODROID-X_LCD_Board_Rev0.2.pdf

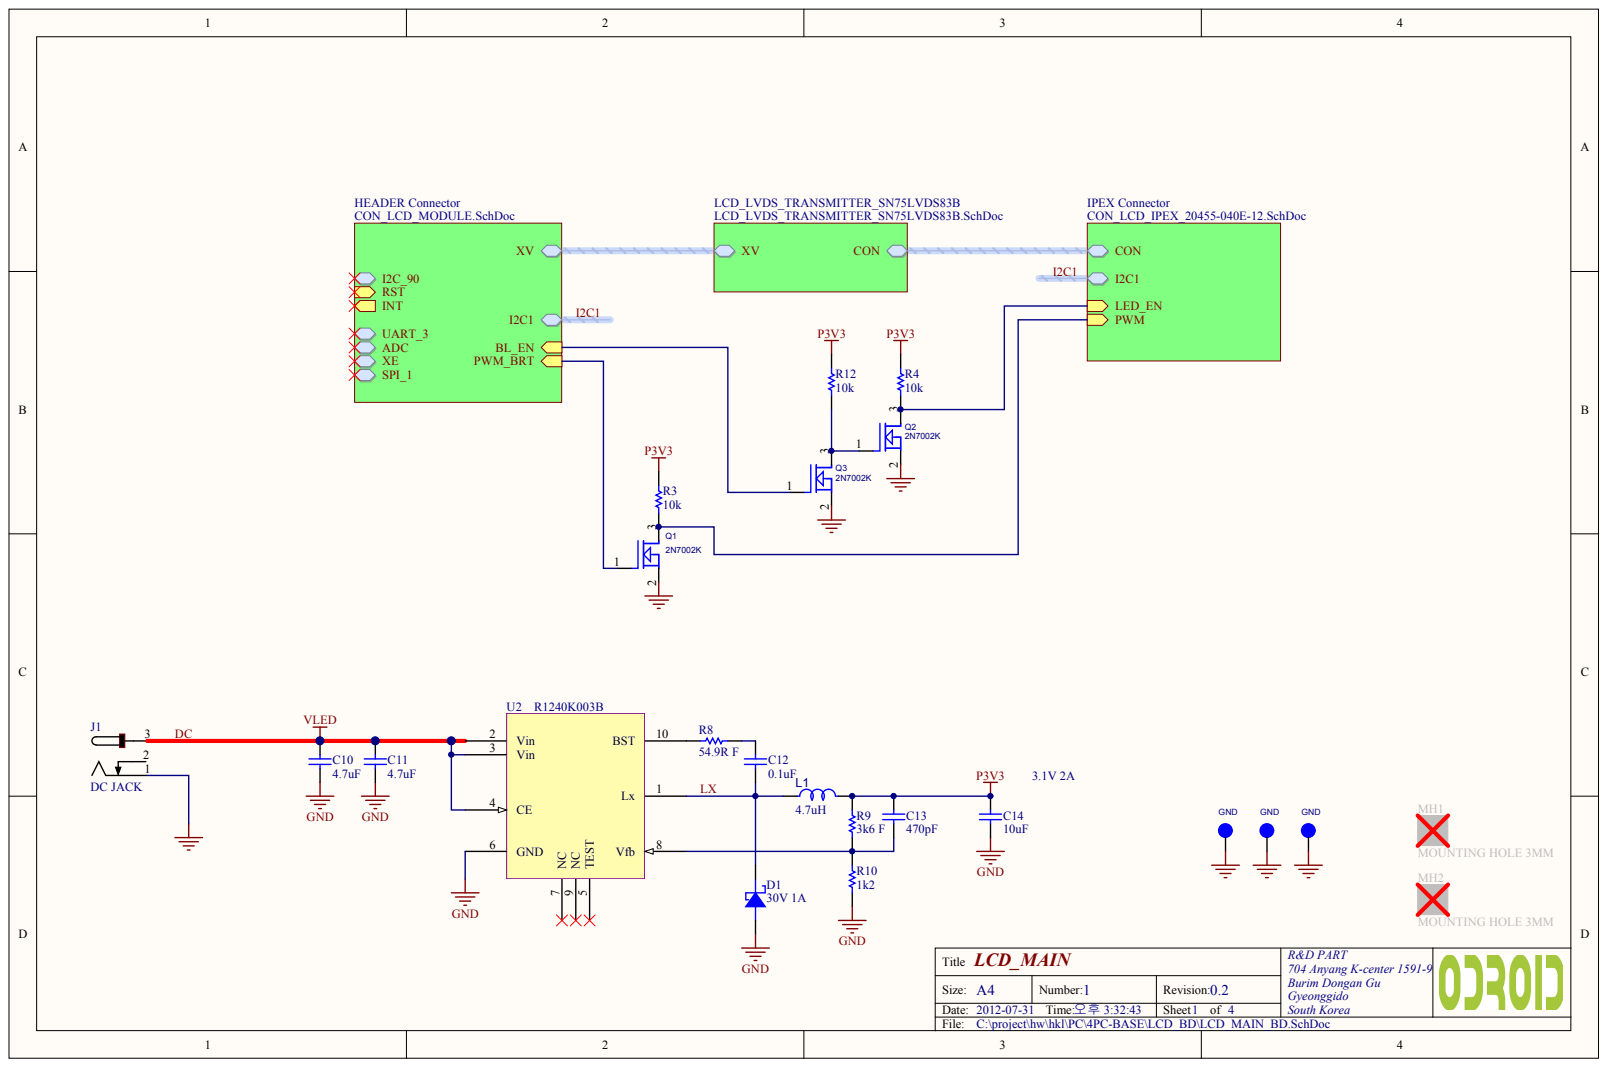
[picture p212: page 1]

LCD_MAIN Title | R&D PART 704 Anyang K-center 1591-9 Burim Dongan Gu Gyeonggido South Korea

A4 Size: | 1 Number: | 0.2 Revision:
2012-07-31 오후 3:32:43 Date: Time: | | Sheet of 4

C:\project\hw\hkl\PC\4PC-BASE\LCD_BD\LCD_MAIN_BD.SchDoc

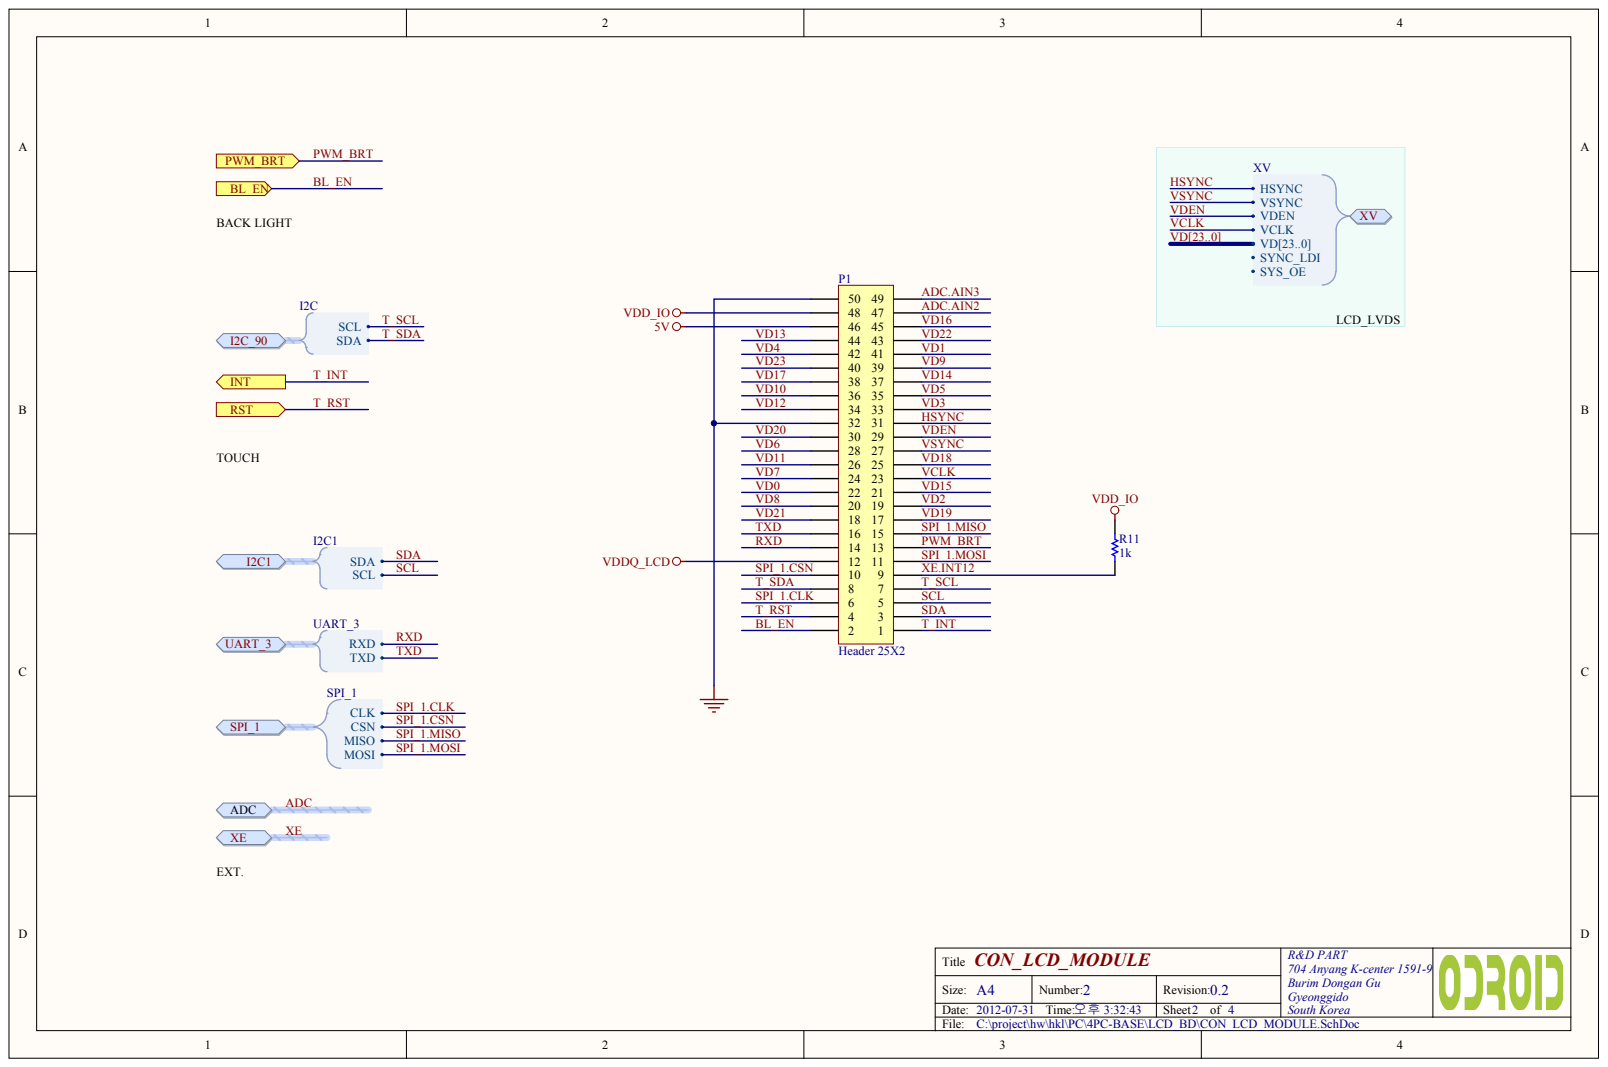
[picture p213: page 2]

Title | R&D PART 704 Anyang K-center 1591-9 Burim Dongan Gu Gyeonggido

A4 Size: | Number: | Revision:

C:\project\hw\hkl\PC\4PC-BASE\LCD_BD\CON_LCD_MODULE.SchDoc

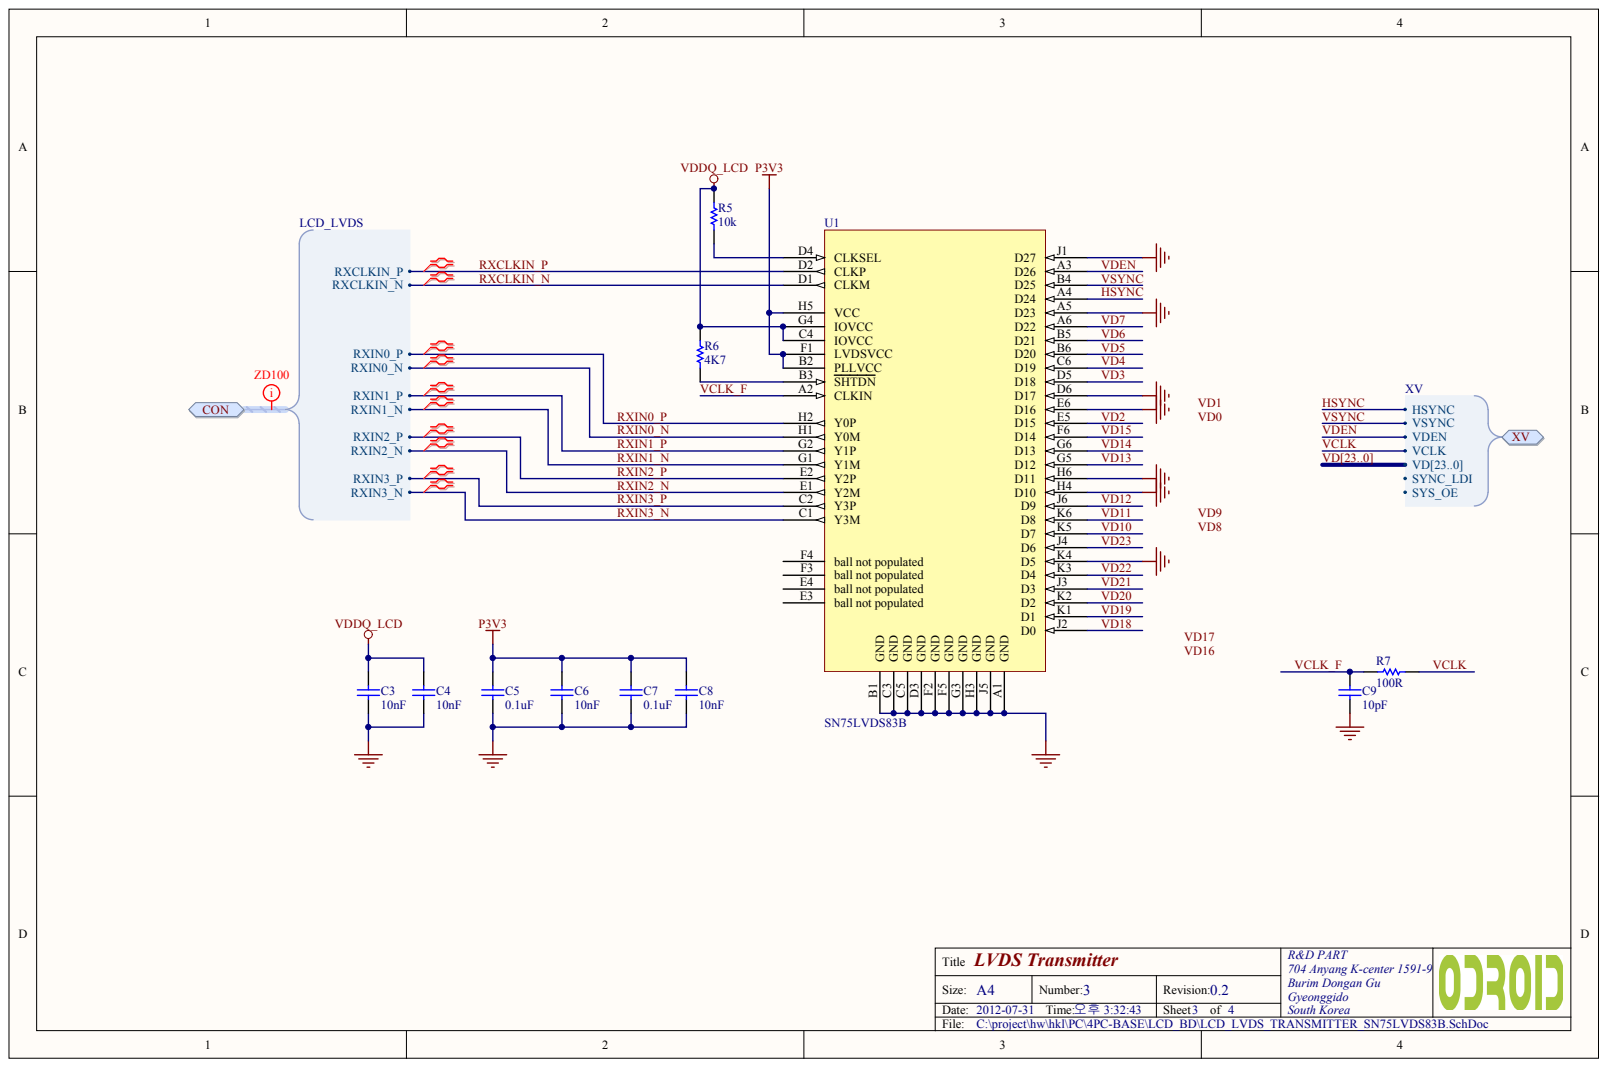
[picture p214: page 3]

CLKM D1 CLKP D2

VCC H5

R6 | | | IOVCC C4

4K7 | PLLVCC B2

SHTDN B3

RXIN0_N
RXIN1_P

RXIN1_N | Y1M G1 Y1P G2

RXIN2_P | Y2M E1 Y2P E2
RXIN2_N
RXIN3_P | Y3M C1 Y3P C2
RXIN3_N

Title | R&D PART 704 Anyang K-center 1591-9 Burim Dongan Gu Gyeonggido

A4 Size: | Number: | Revision:

C:\project\hw\hkl\PC\4PC-BASE\LCD_BD\LCD_LVDS_TRANSMITTER_SN75LVDS83B.SchDoc

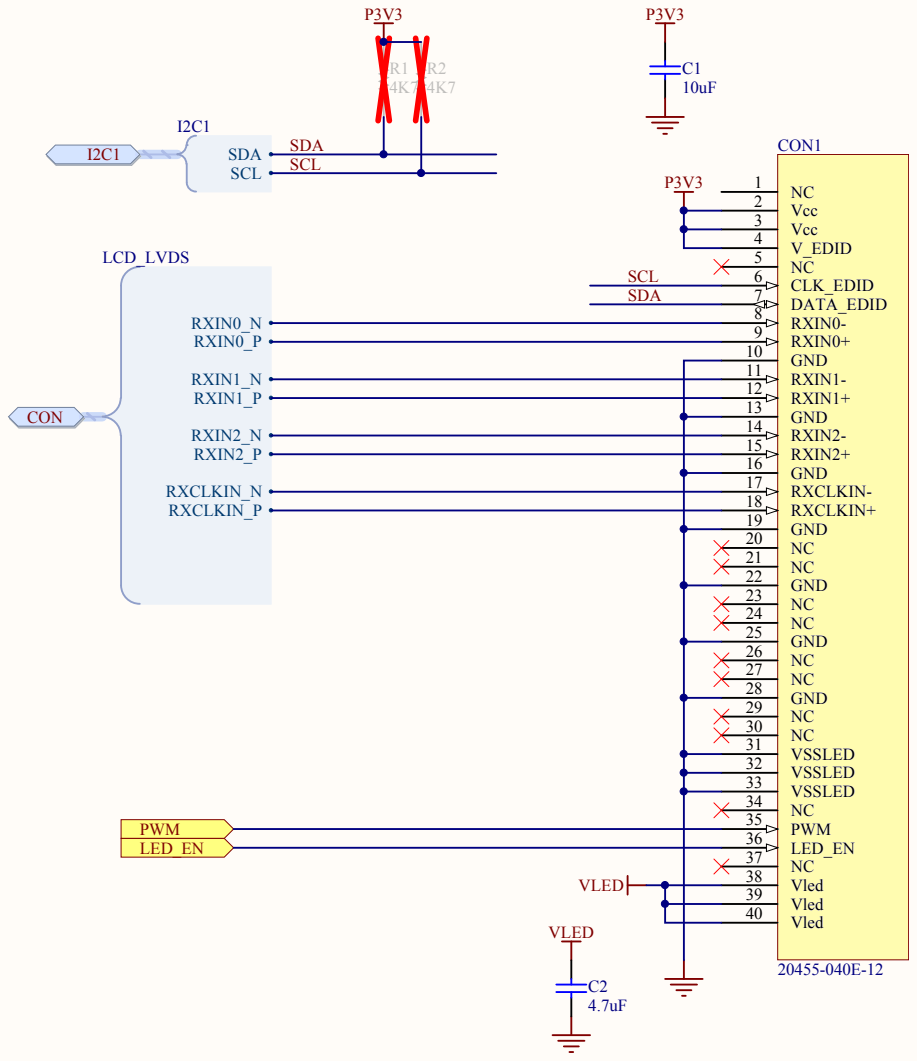
[picture p215: page 4]

RXIN1- 11 RXIN1+ 12 GND 13

RXIN2- 14 RXIN2+ 15 GND 16

RXCLKIN- 17 RXCLKIN+ 18 GND 19

VSSLED 32

CON_LCD Title | R&D PART 704 Anyang K-center 1591-9 Burim Dongan Gu Gyeonggido

A4 Size: | 4 Number: | 0.2 Revision:

C:\project\hw\hkl\PC\4PC-BASE\LCD_BD\CON_LCD_IPEX_20455-040E-12.SchDoc
