MLAB-project/Modules/MCU_CPU/ARM/ODroid-X2/sch/ODROID-X_UART_Board.pdf

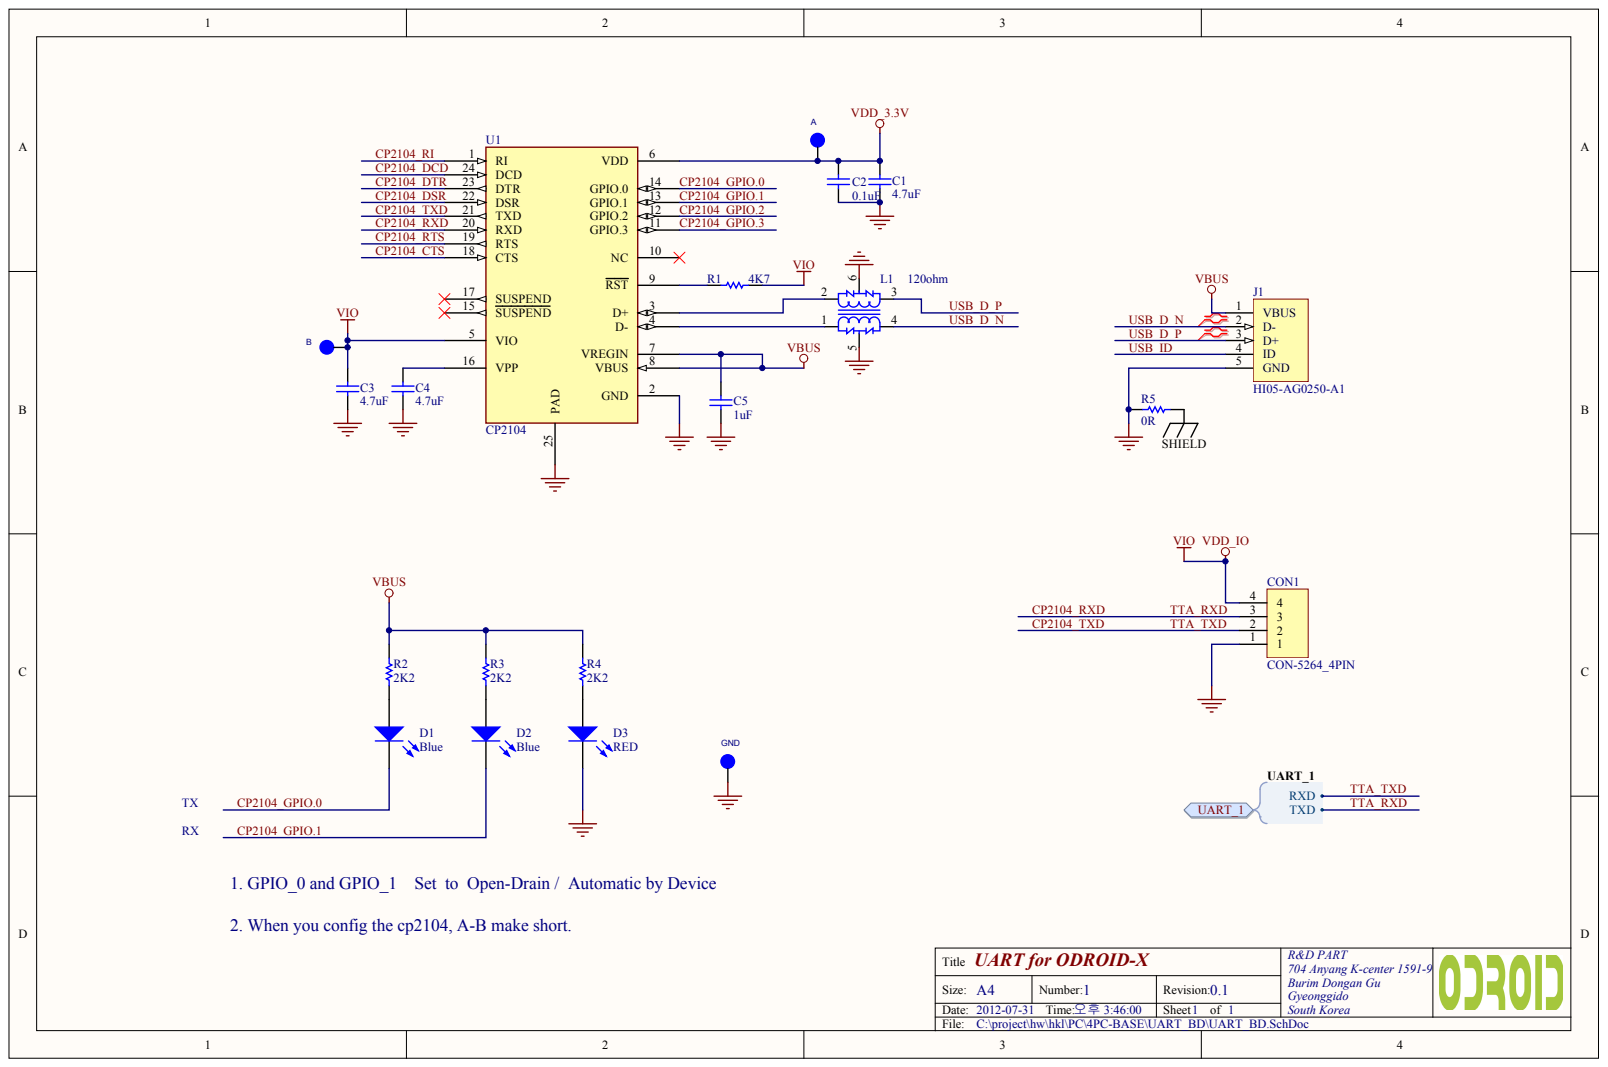
[picture p216: page 1]

1. GPIO_0 and GPIO_1 Set to Open-Drain / Automatic by Device

2. When you config the cp2104, A-B make short.

UART for ODROID-X Title | R&D PART 704 Anyang K-center 1591-9 Burim Dongan Gu Gyeonggido South Korea

A4 Size: | 1 Number: | 0.1 Revision:
2012-07-31 오후 3:46:00 Date: Time: | | Sheet 1 of 1

C:\project\hw\hkl\PC\4PC-BASE\UART_BD\UART_BD.SchDoc
