MLAB-project/Modules/power_sw/NFET2x2/hw/cam_ama/V2.pdf

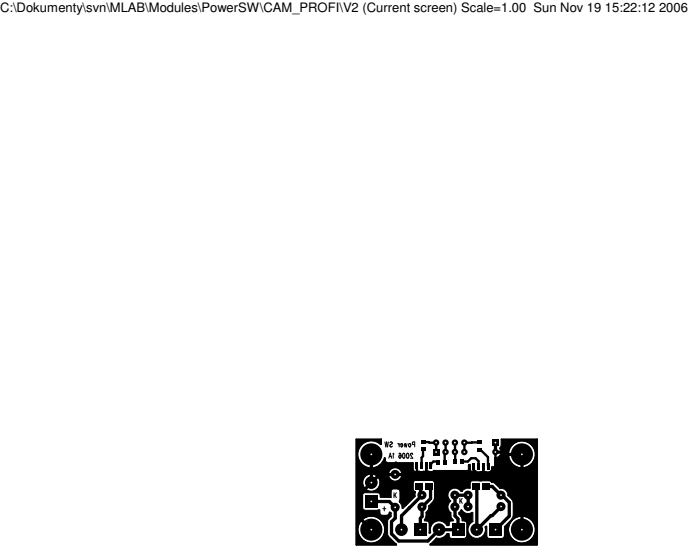
[picture p217: page 1]

C:\Dokumenty\svn\MLAB\Modules\PowerSW\CAM_PROFI\V2 (Current screen) Scale=1.00 Sun Nov 19 15:22:12 2006
