MLAB-project/Modules/mechanical/boxes/UNIBOX01A/hw/cam_profi/UNIBOX01A-FPxx/UNIBOX01-FPAC.pdf

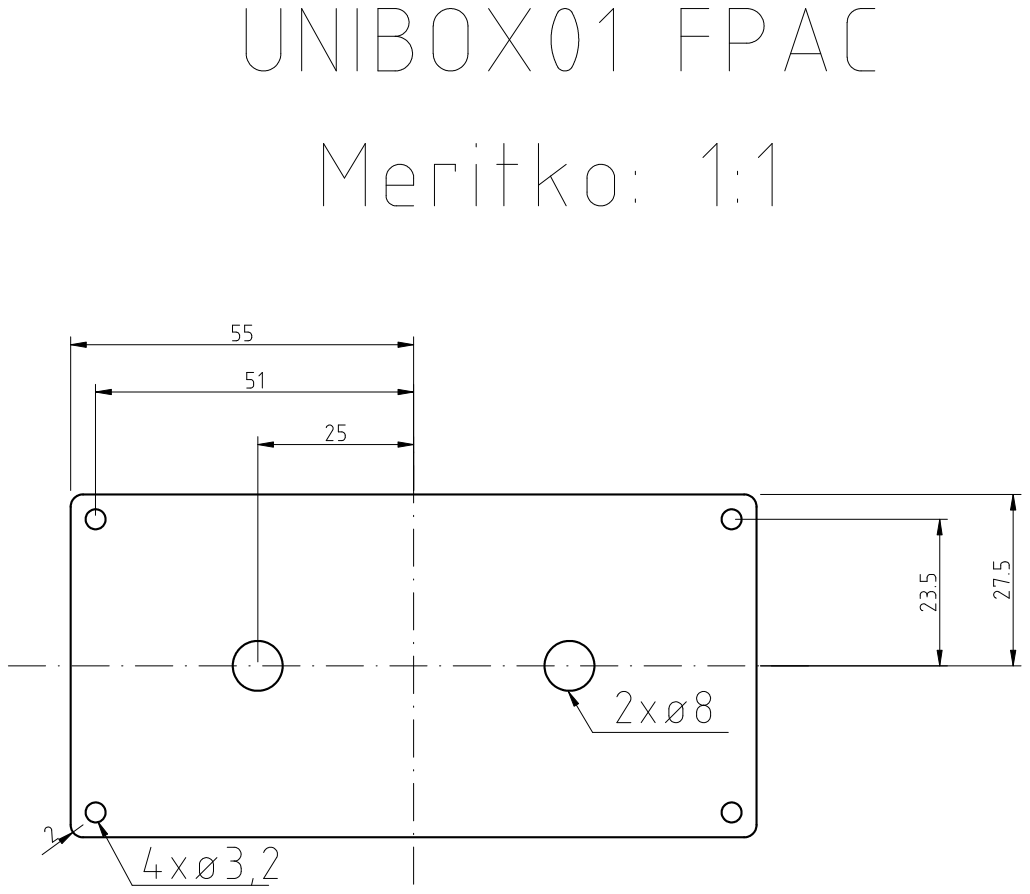
[picture p225: page 1]
