MLAB-project/Modules/mechanical/boxes/UNIBOX01A/hw/cam_profi/UNIBOX01A-FPxx/UNIBOX01-FPAD.pdf

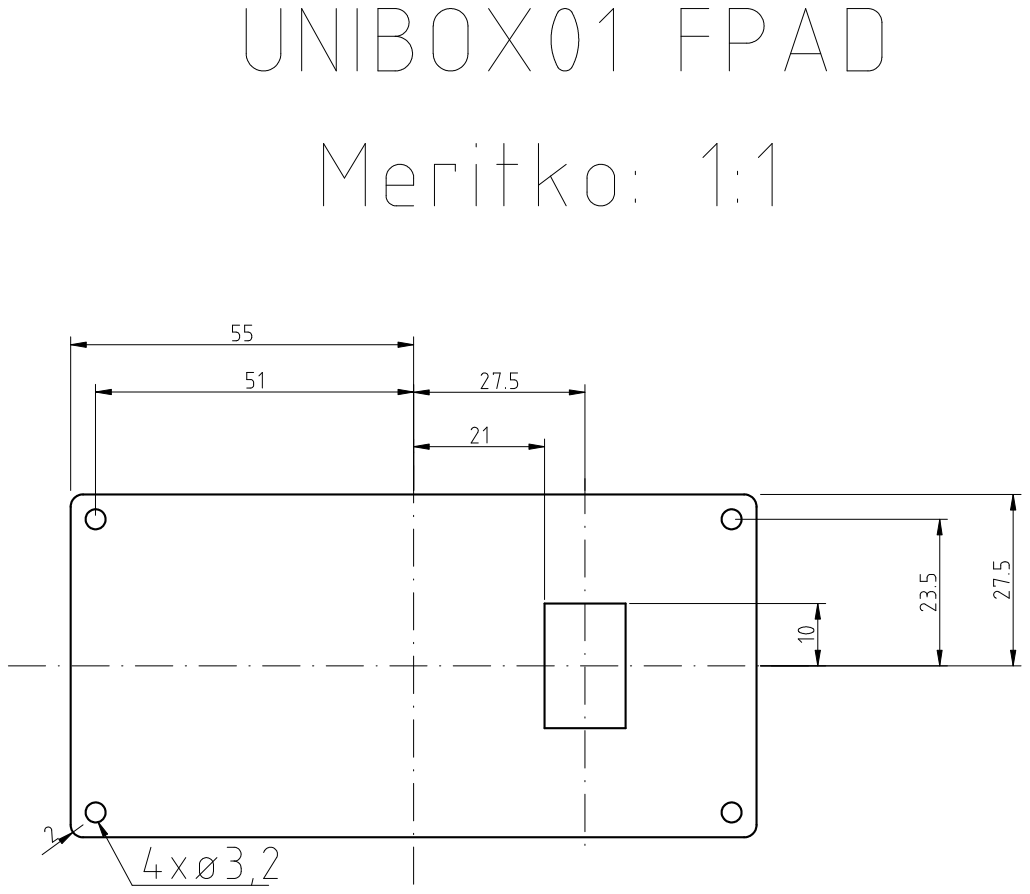
[picture p226: page 1]
