MLAB-project/Modules/mechanical/boxes/UNIBOX01A/hw/cam_profi/UNIBOX01A-FPxx/UNIBOX01-FPAE.pdf

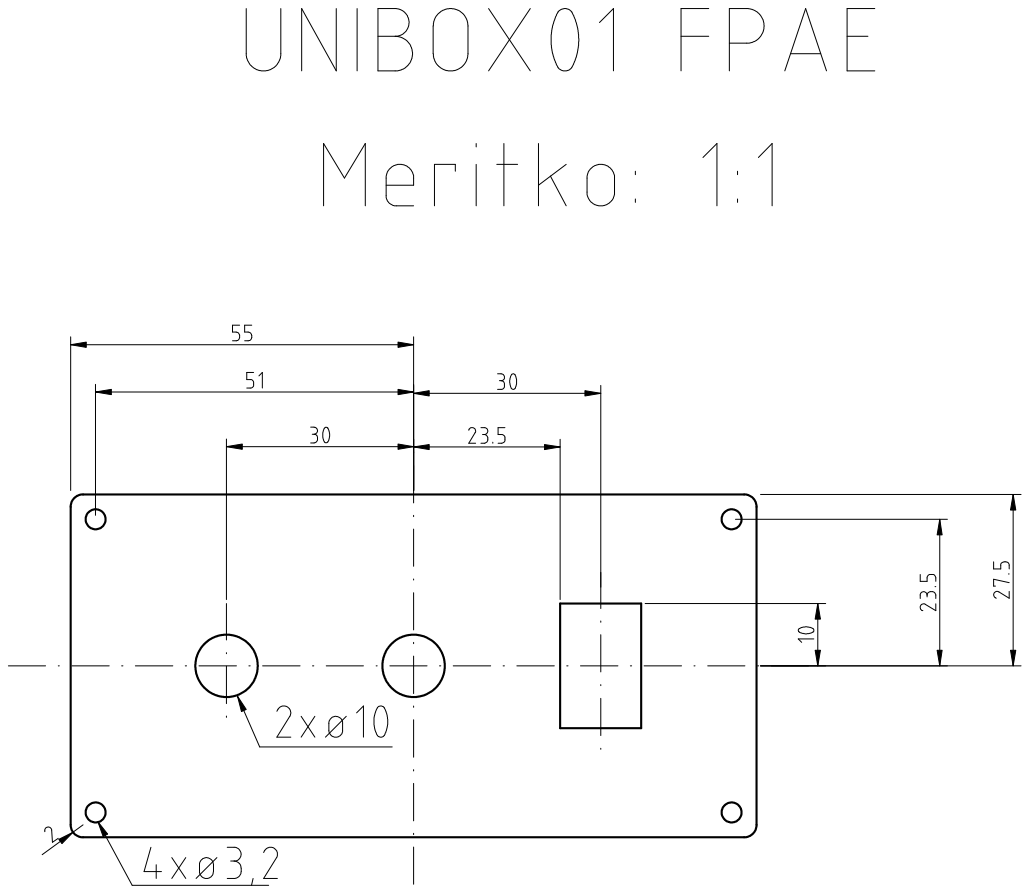
[picture p227: page 1]
