MLAB-project/Modules/mechanical/boxes/UNIBOX01A/hw/cam_profi/UNIBOX01A-FPxx/UNIBOX01-FPAF.pdf

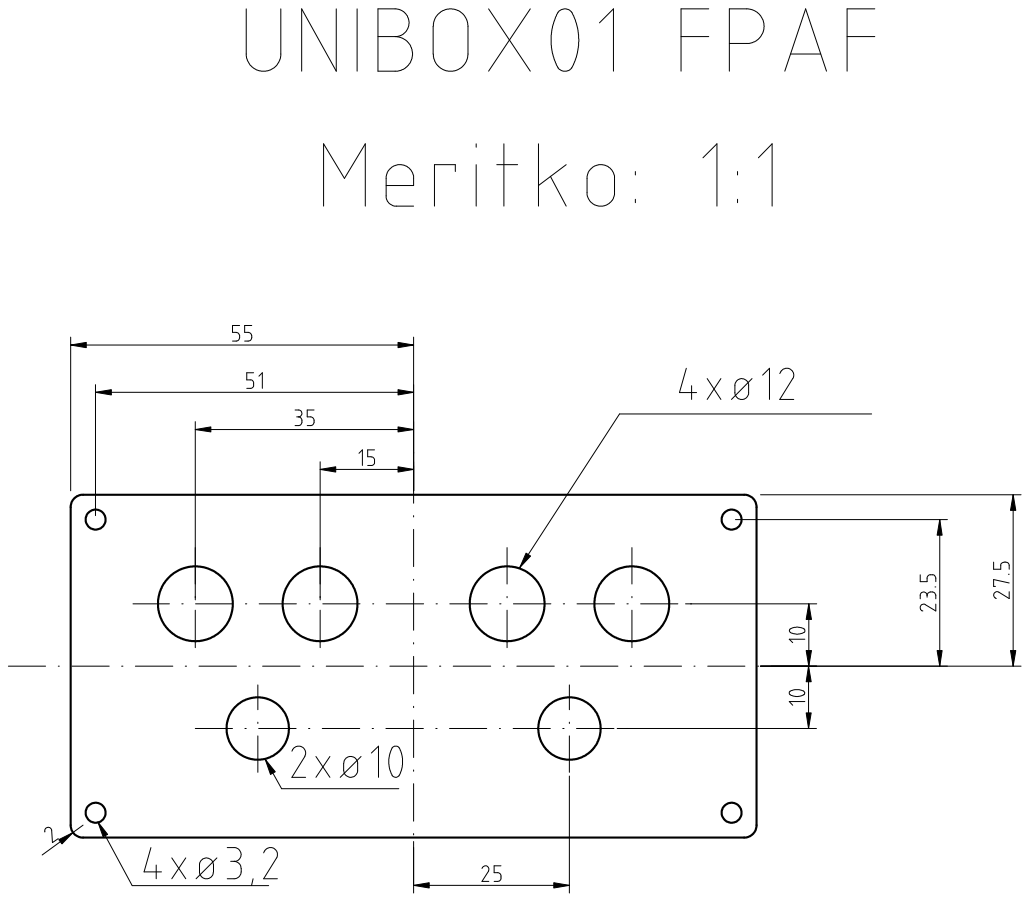
[picture p228: page 1]
