MLAB-project/Modules/mechanical/boxes/UNIBOX01A/hw/cam_profi/UNIBOX01A-FPxx/UNIBOX01-FPAG.pdf

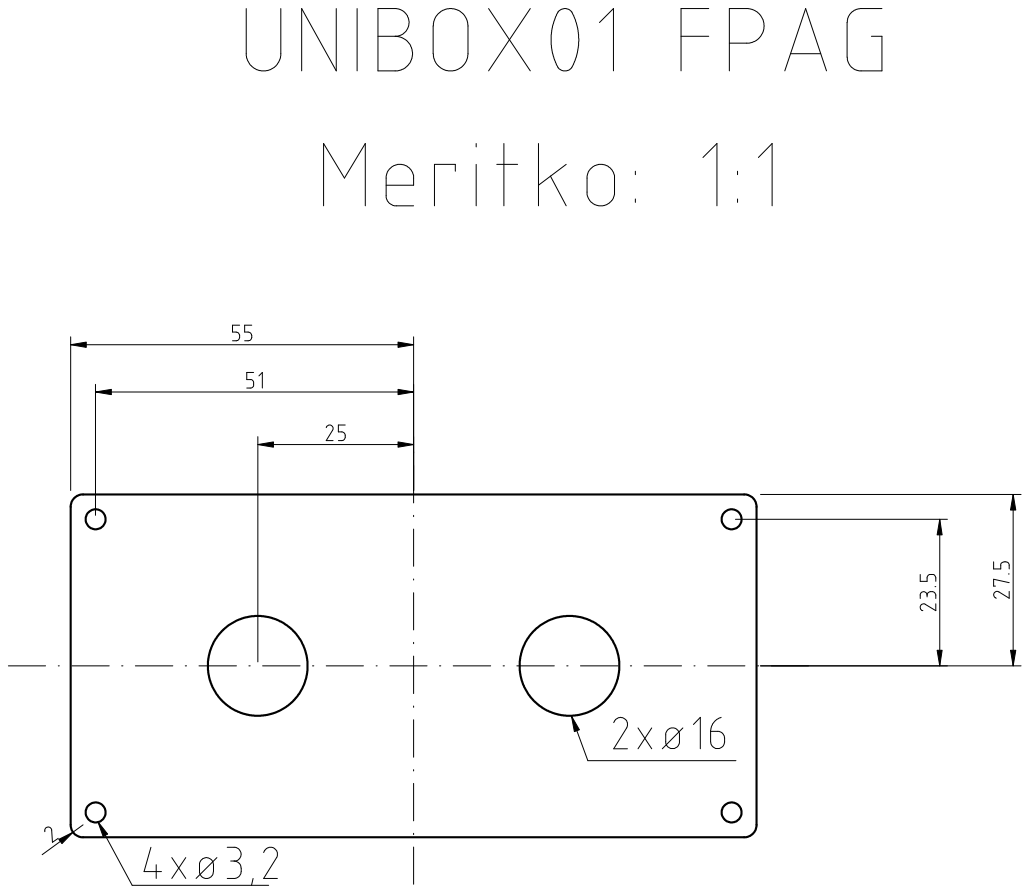
[picture p229: page 1]
