MLAB-project/Modules/motor_drivers/IR2302/sch/IR2302.pdf

5

4

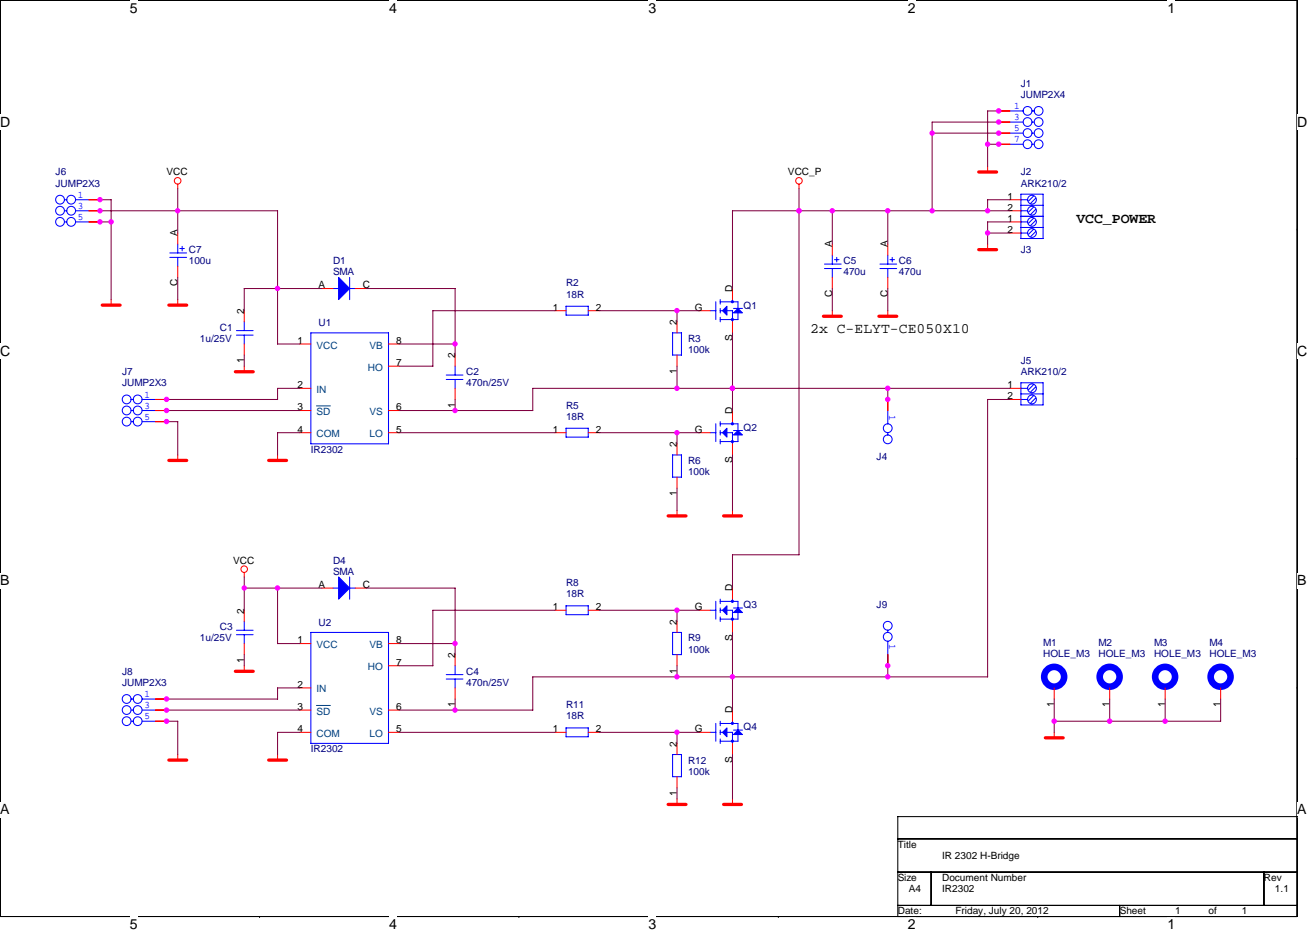
[picture p233: page 1]

Size A4 | Document Number IR2302 | Rev 1.1

Date: Friday, July 20, 2012 | Sheet 1 of 1
