MLAB-project/Modules/power_supply/MAX1797/pcb/osazovak.pdf

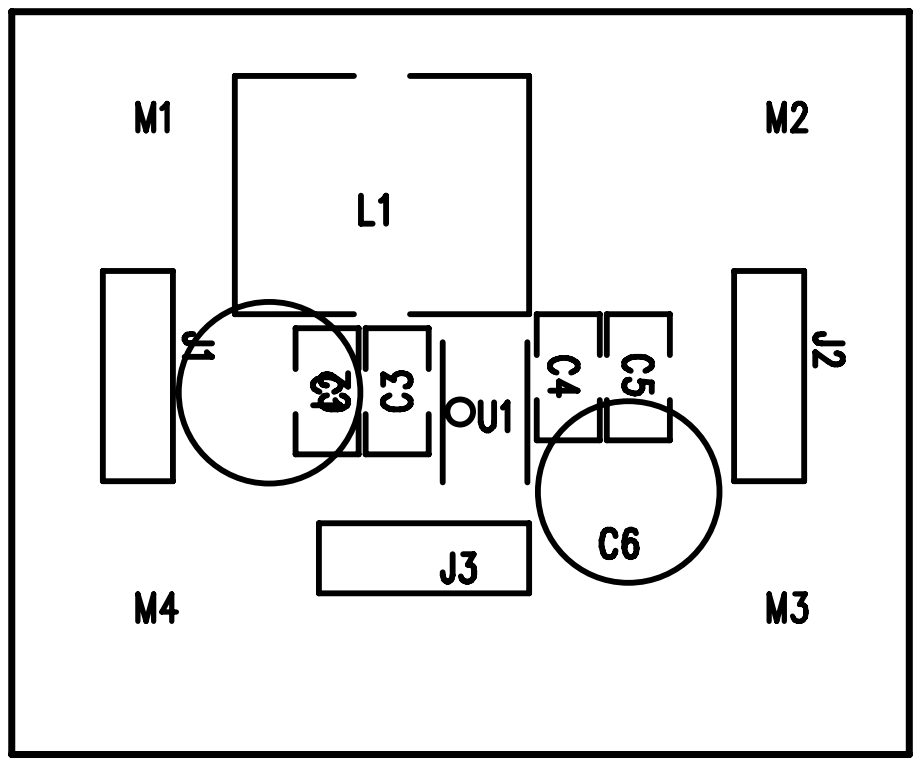
[picture p234: page 1]
