MLAB-project/Modules/power_supply/MAX1797/sch/MAX1797.pdf

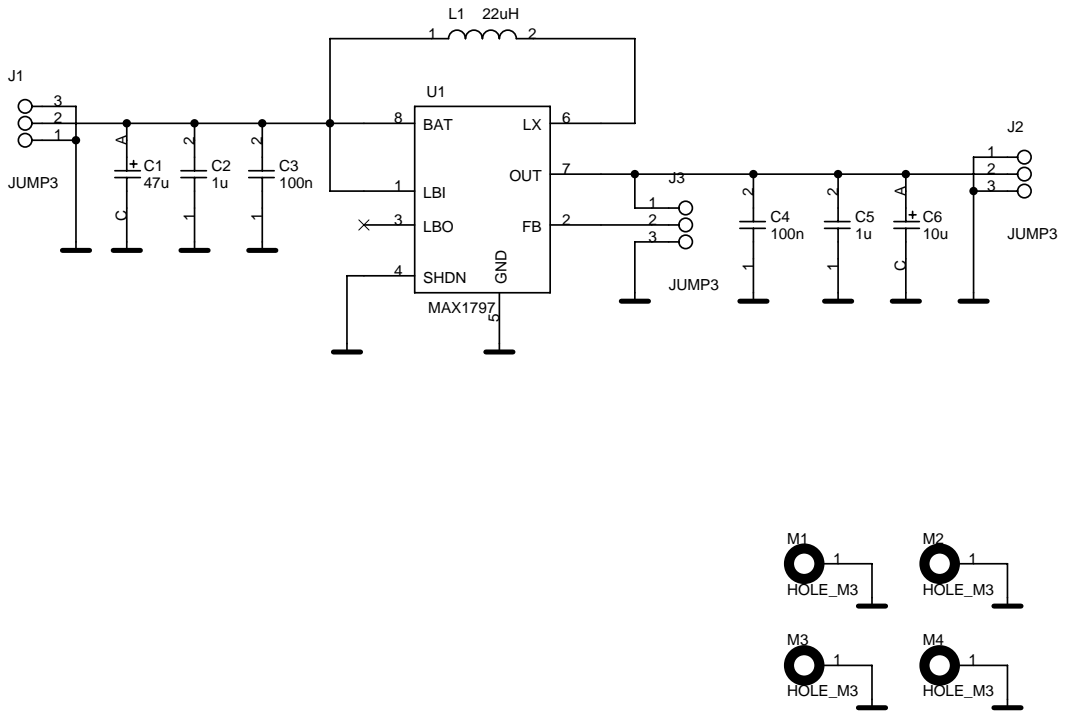
[picture p235: page 1]

Size A4 | Document Number MAX1797 | Rev 1.0

Date: Tuesday, March 18, 2008 | Sheet 1 of 1
