MLAB-project/Modules/power_supply/TPS61170/pcb/osazovak.pdf

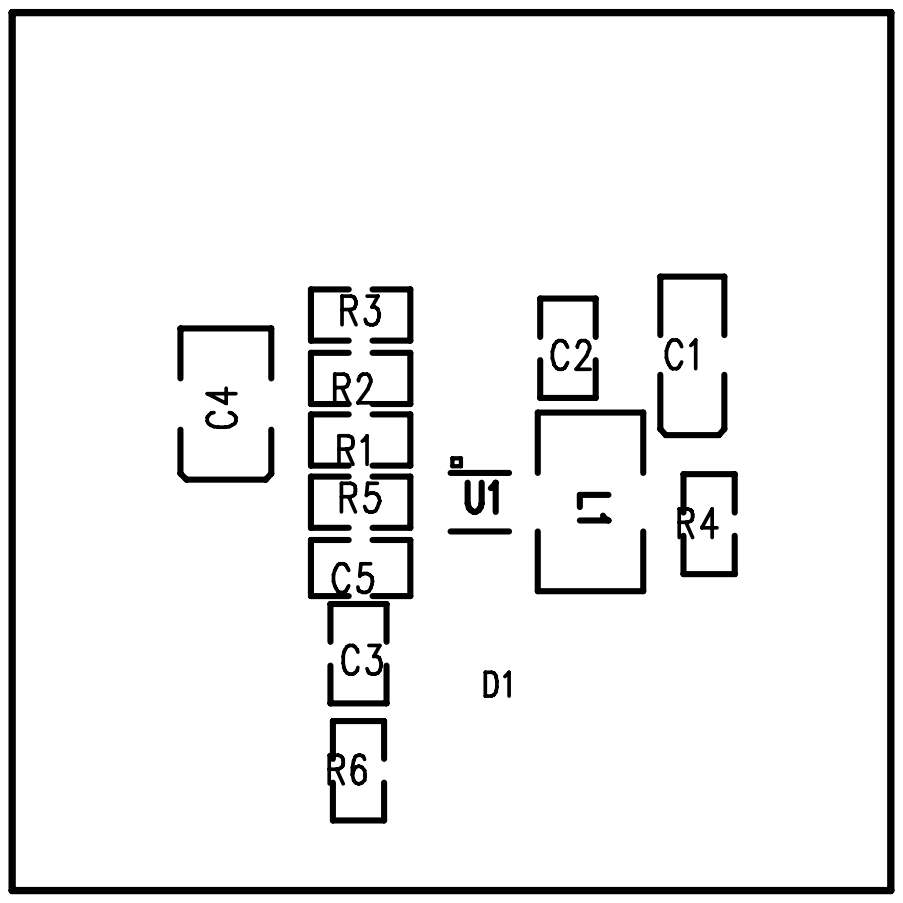
[picture p236: page 1]
