MLAB-project/Modules/power_supply/TPS61170/pcb/potisk.pdf

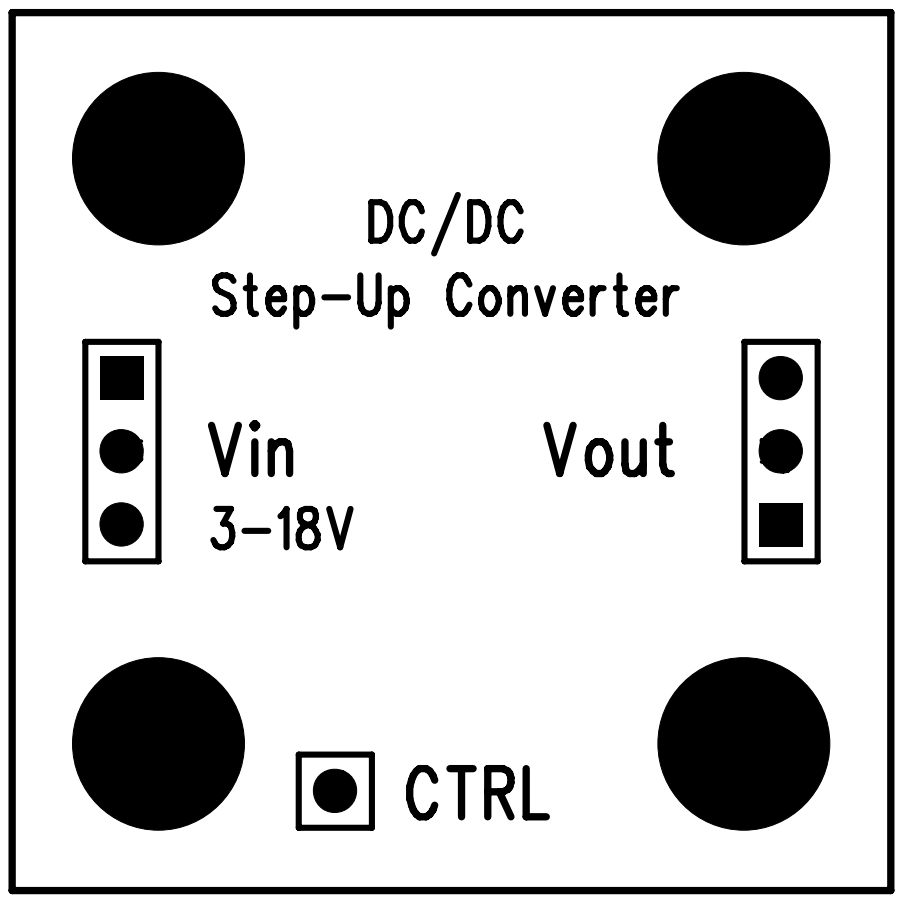
[picture p237: page 1]
