MLAB-project/Modules/power_supply/TPS61170/pcb/vrtani.pdf

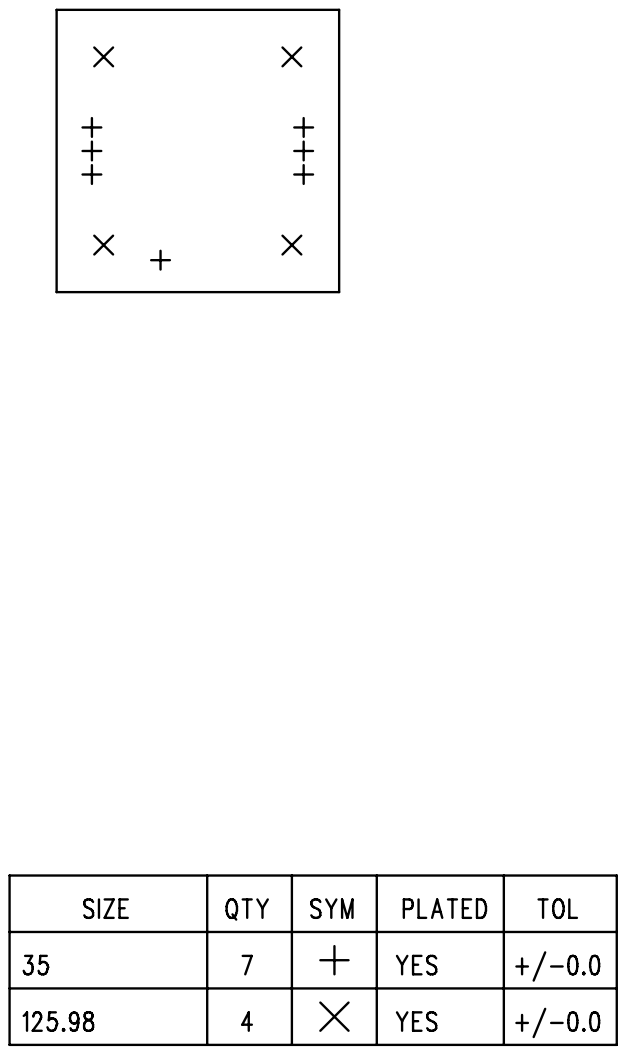
[picture p238: page 1]
