MLAB-project/Modules/power_supply/TPS61170/sch/TPS61170.pdf

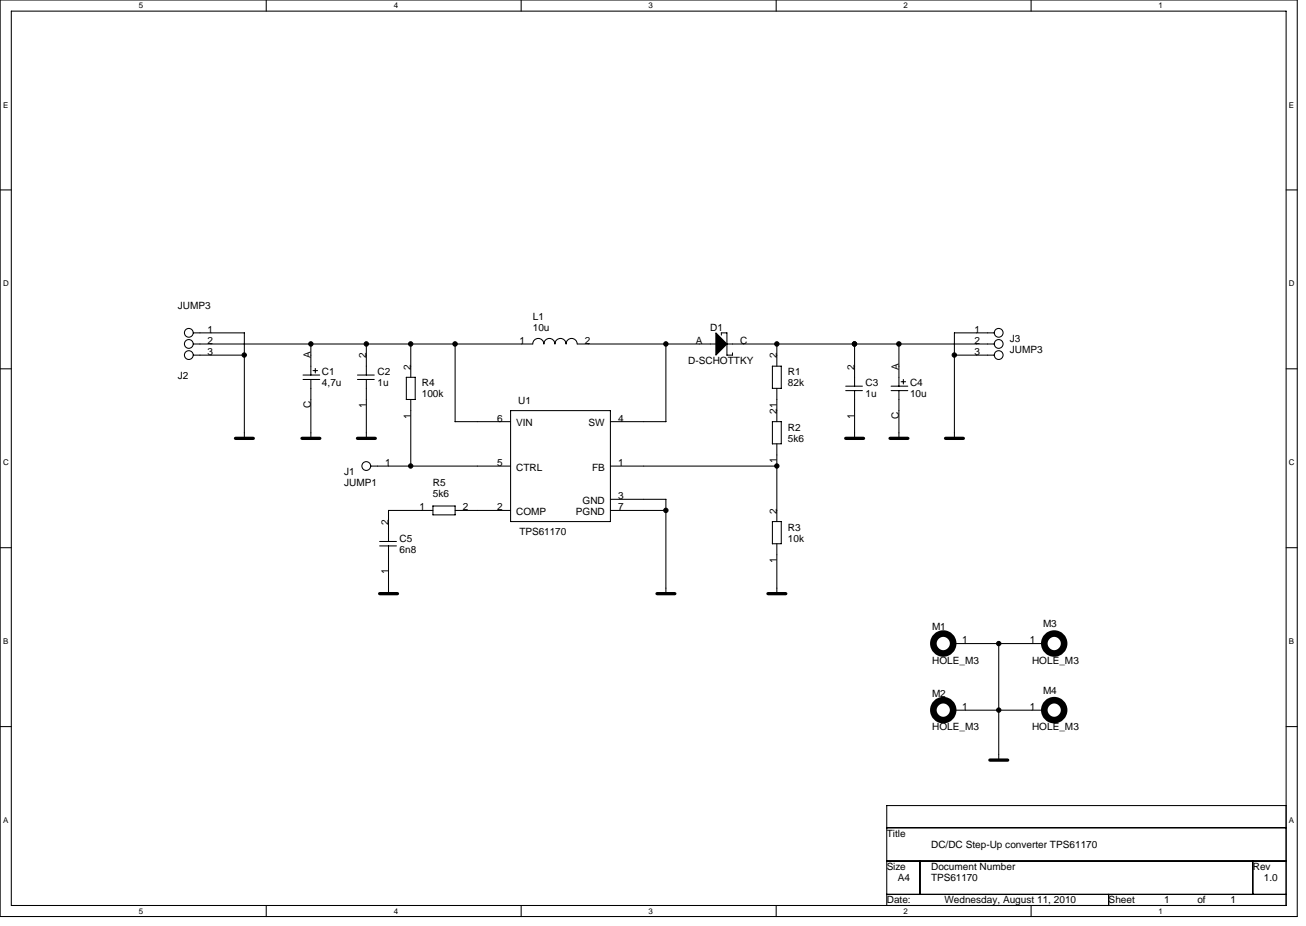
[picture p239: page 1]

DC/DC Step-Up converter TPS61170

Size A4 | Document Number TPS61170 | Rev 1.0

Date: Wednesday, August 11, 2010 | Sheet 1 of 1
