MLAB-project/Modules/power_supply/TPS61200/pcb/osazovak BOT.pdf

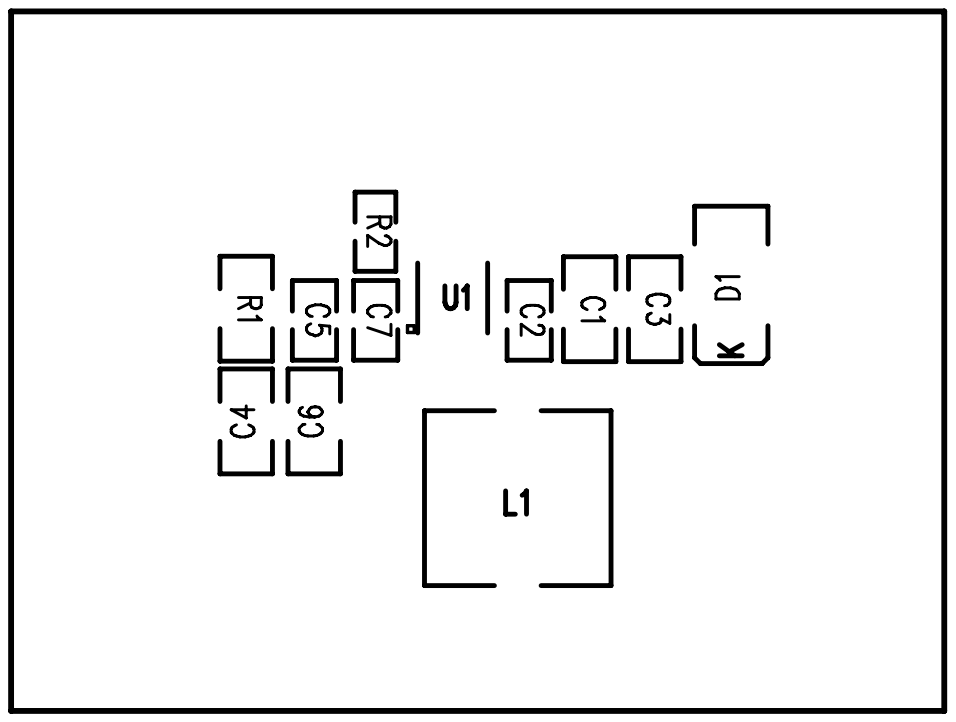
[picture p240: page 1]
