MLAB-project/Modules/power_supply/TPS61200/pcb/potisk.pdf

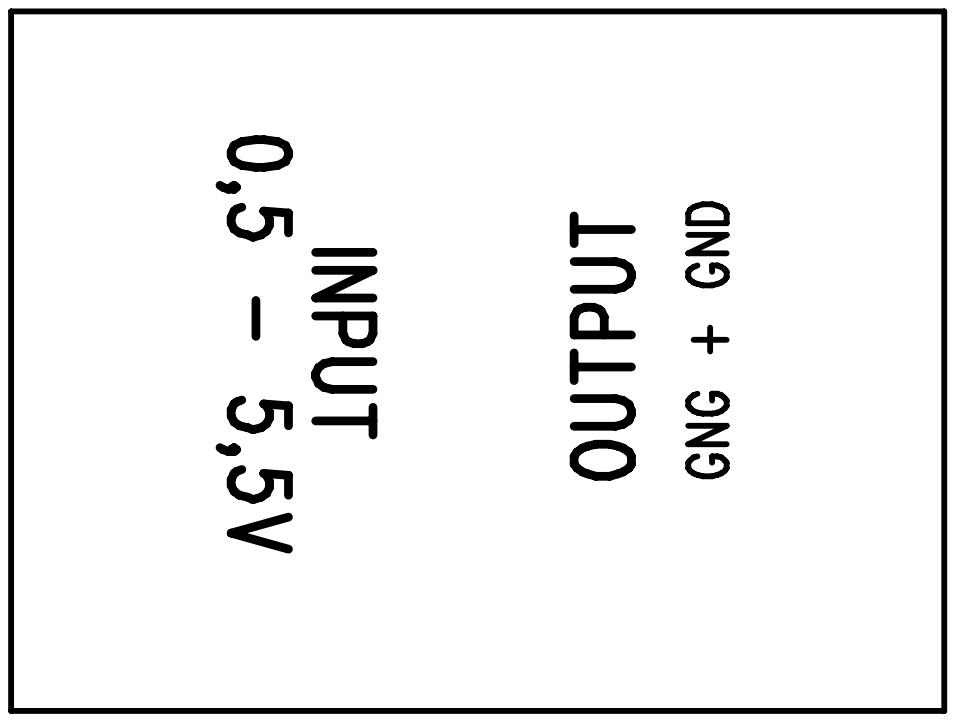
[picture p241: page 1]
