MLAB-project/Modules/power_supply/TPS61200/pcb/vrtani.pdf

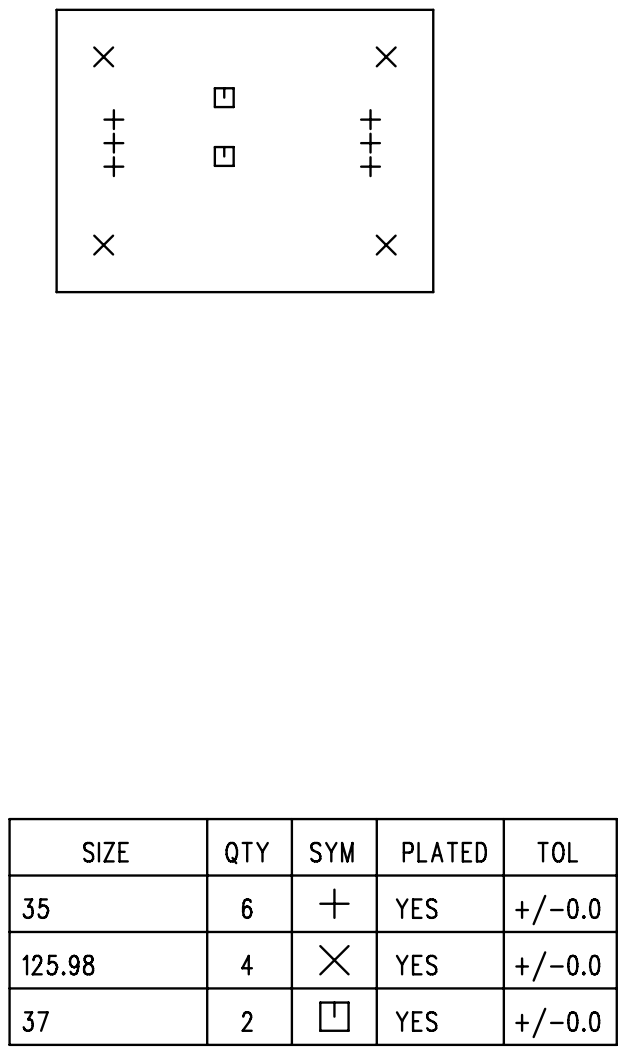
[picture p242: page 1]
