MLAB-project/Modules/power_supply/TPS63000/pcb/osazovak BOT.pdf

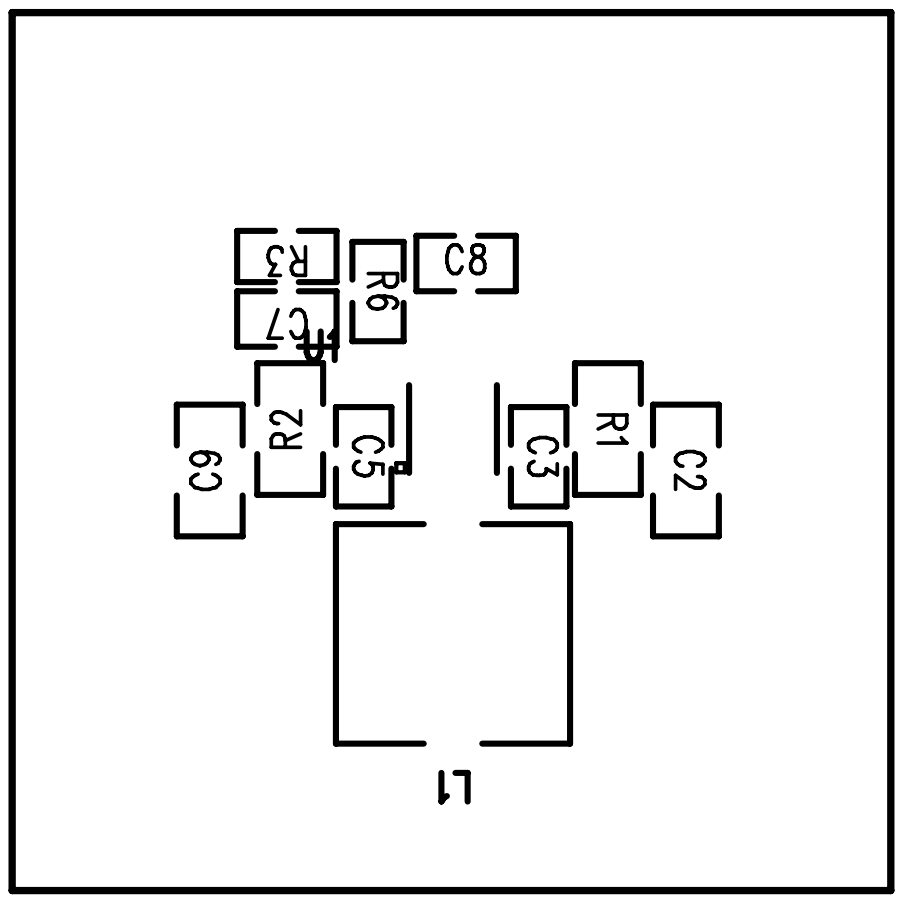
[picture p243: page 1]
