MLAB-project/Modules/power_supply/TPS63000/pcb/potisk.pdf

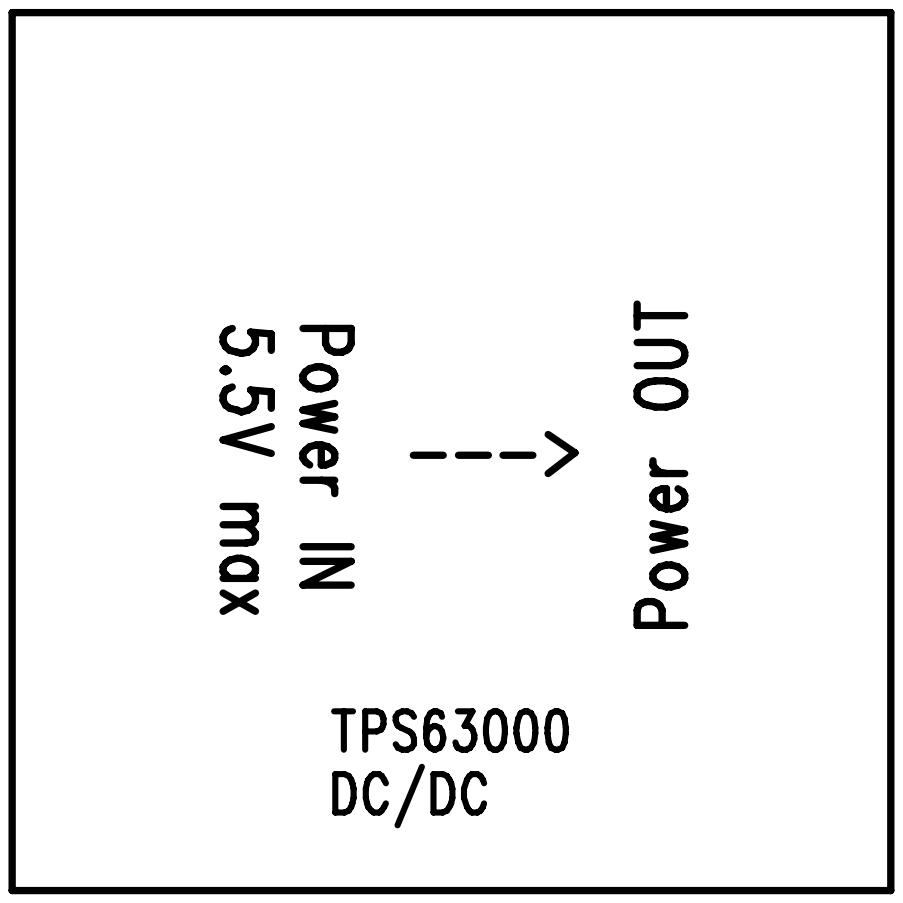
[picture p244: page 1]
