MLAB-project/Modules/sensors/MMA6260/sch/MMA6260Q.pdf

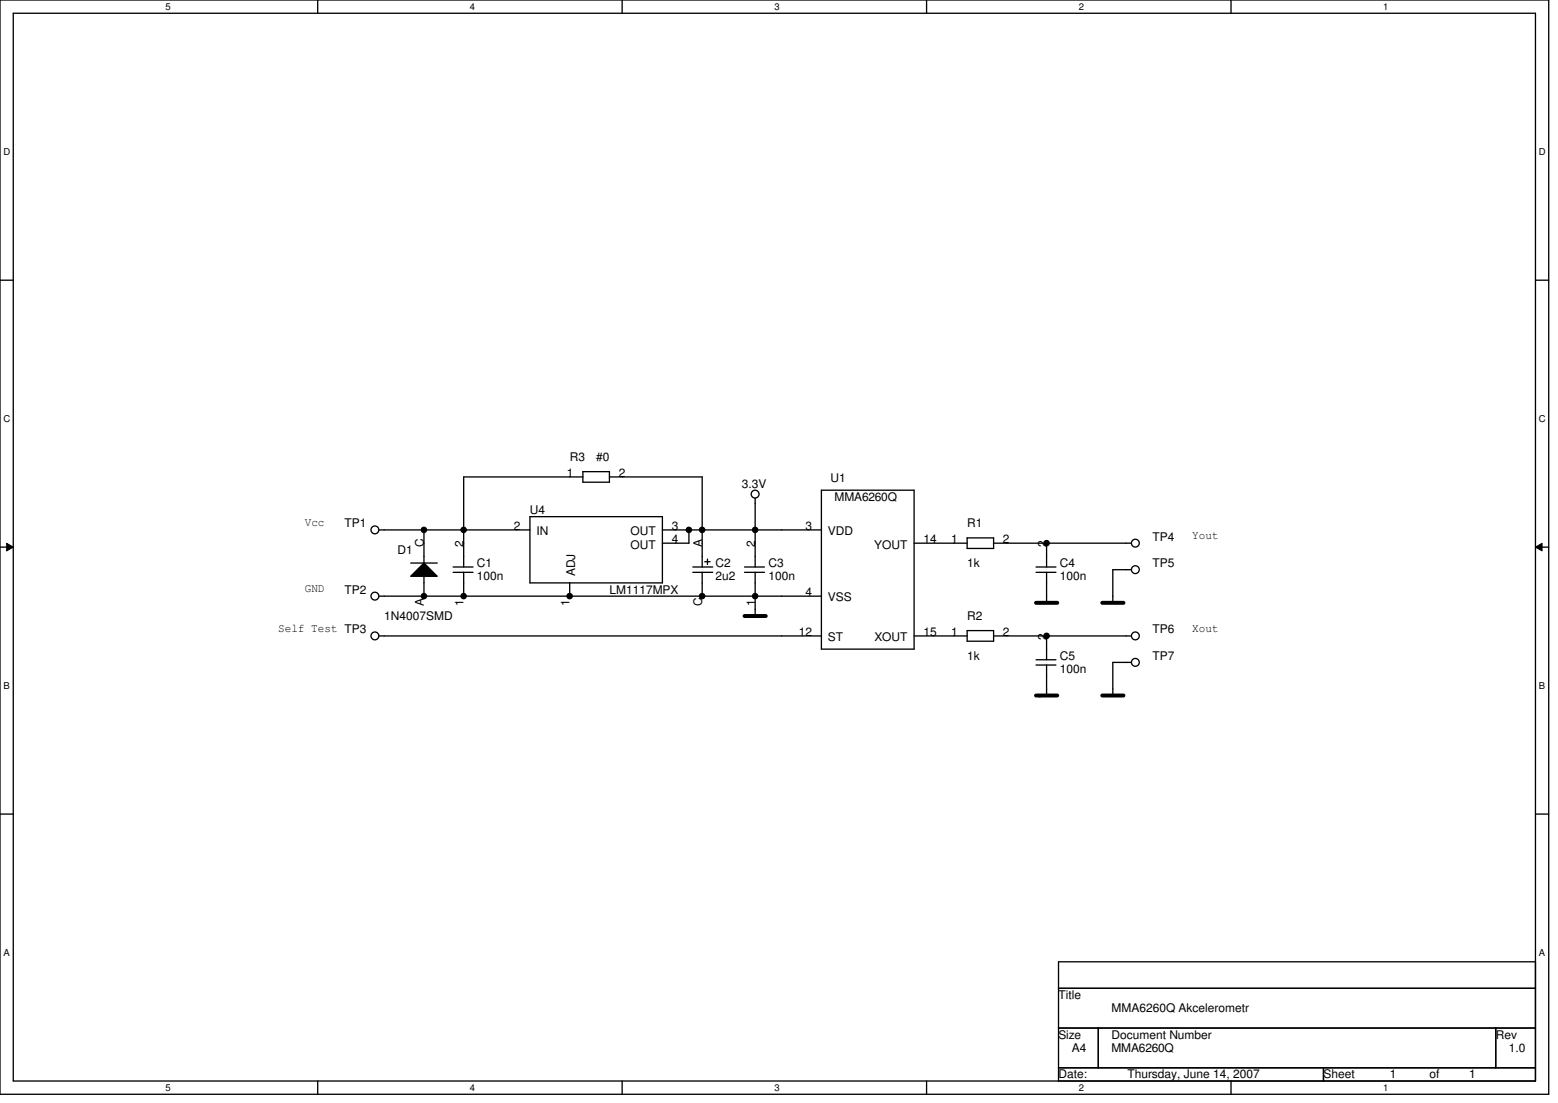
[picture p245: page 1]

Size A4 | Document Number MMA6260Q | Rev 1.0

Date: Thursday, June 14, 2007 | Sheet 1 of 1
