MLAB-project/Modules/comm_serial/I2CHUB01A/sch/I2CHUB01A_SCH.pdf

5

4

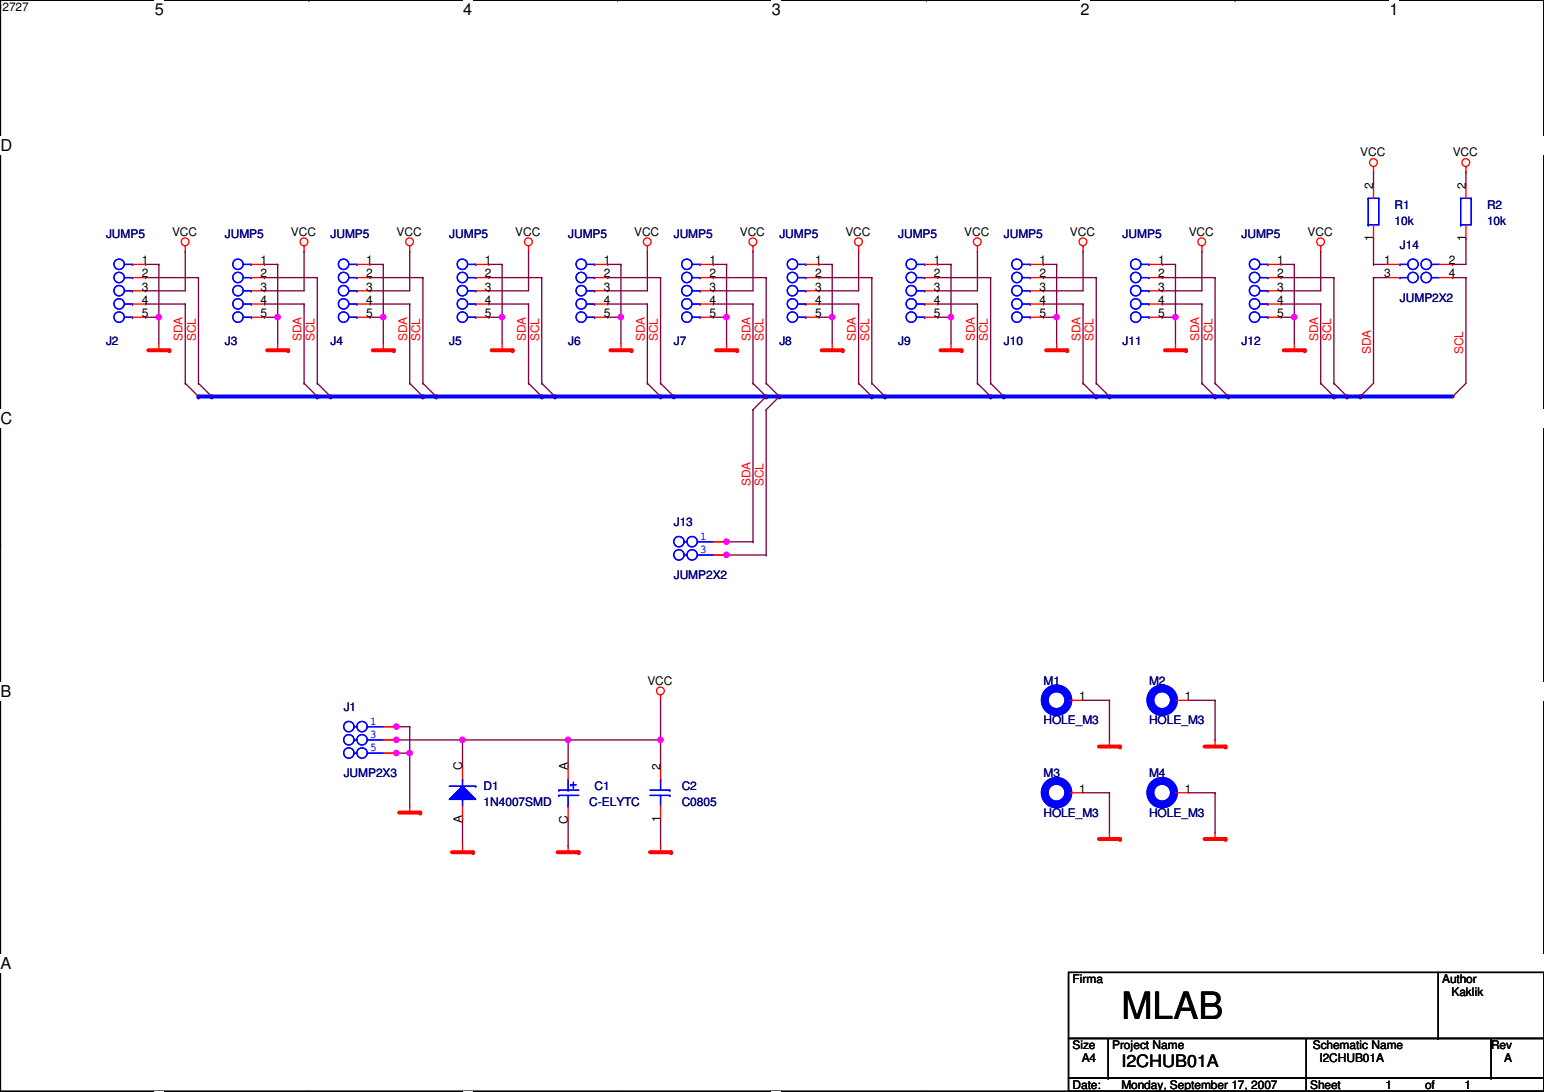
[picture p246: page 1]
