MLAB-project/Modules/MCU_CPU/ARM/ODroid-X2/sch/ODROID-X_BASE_Rev0.4.pdf

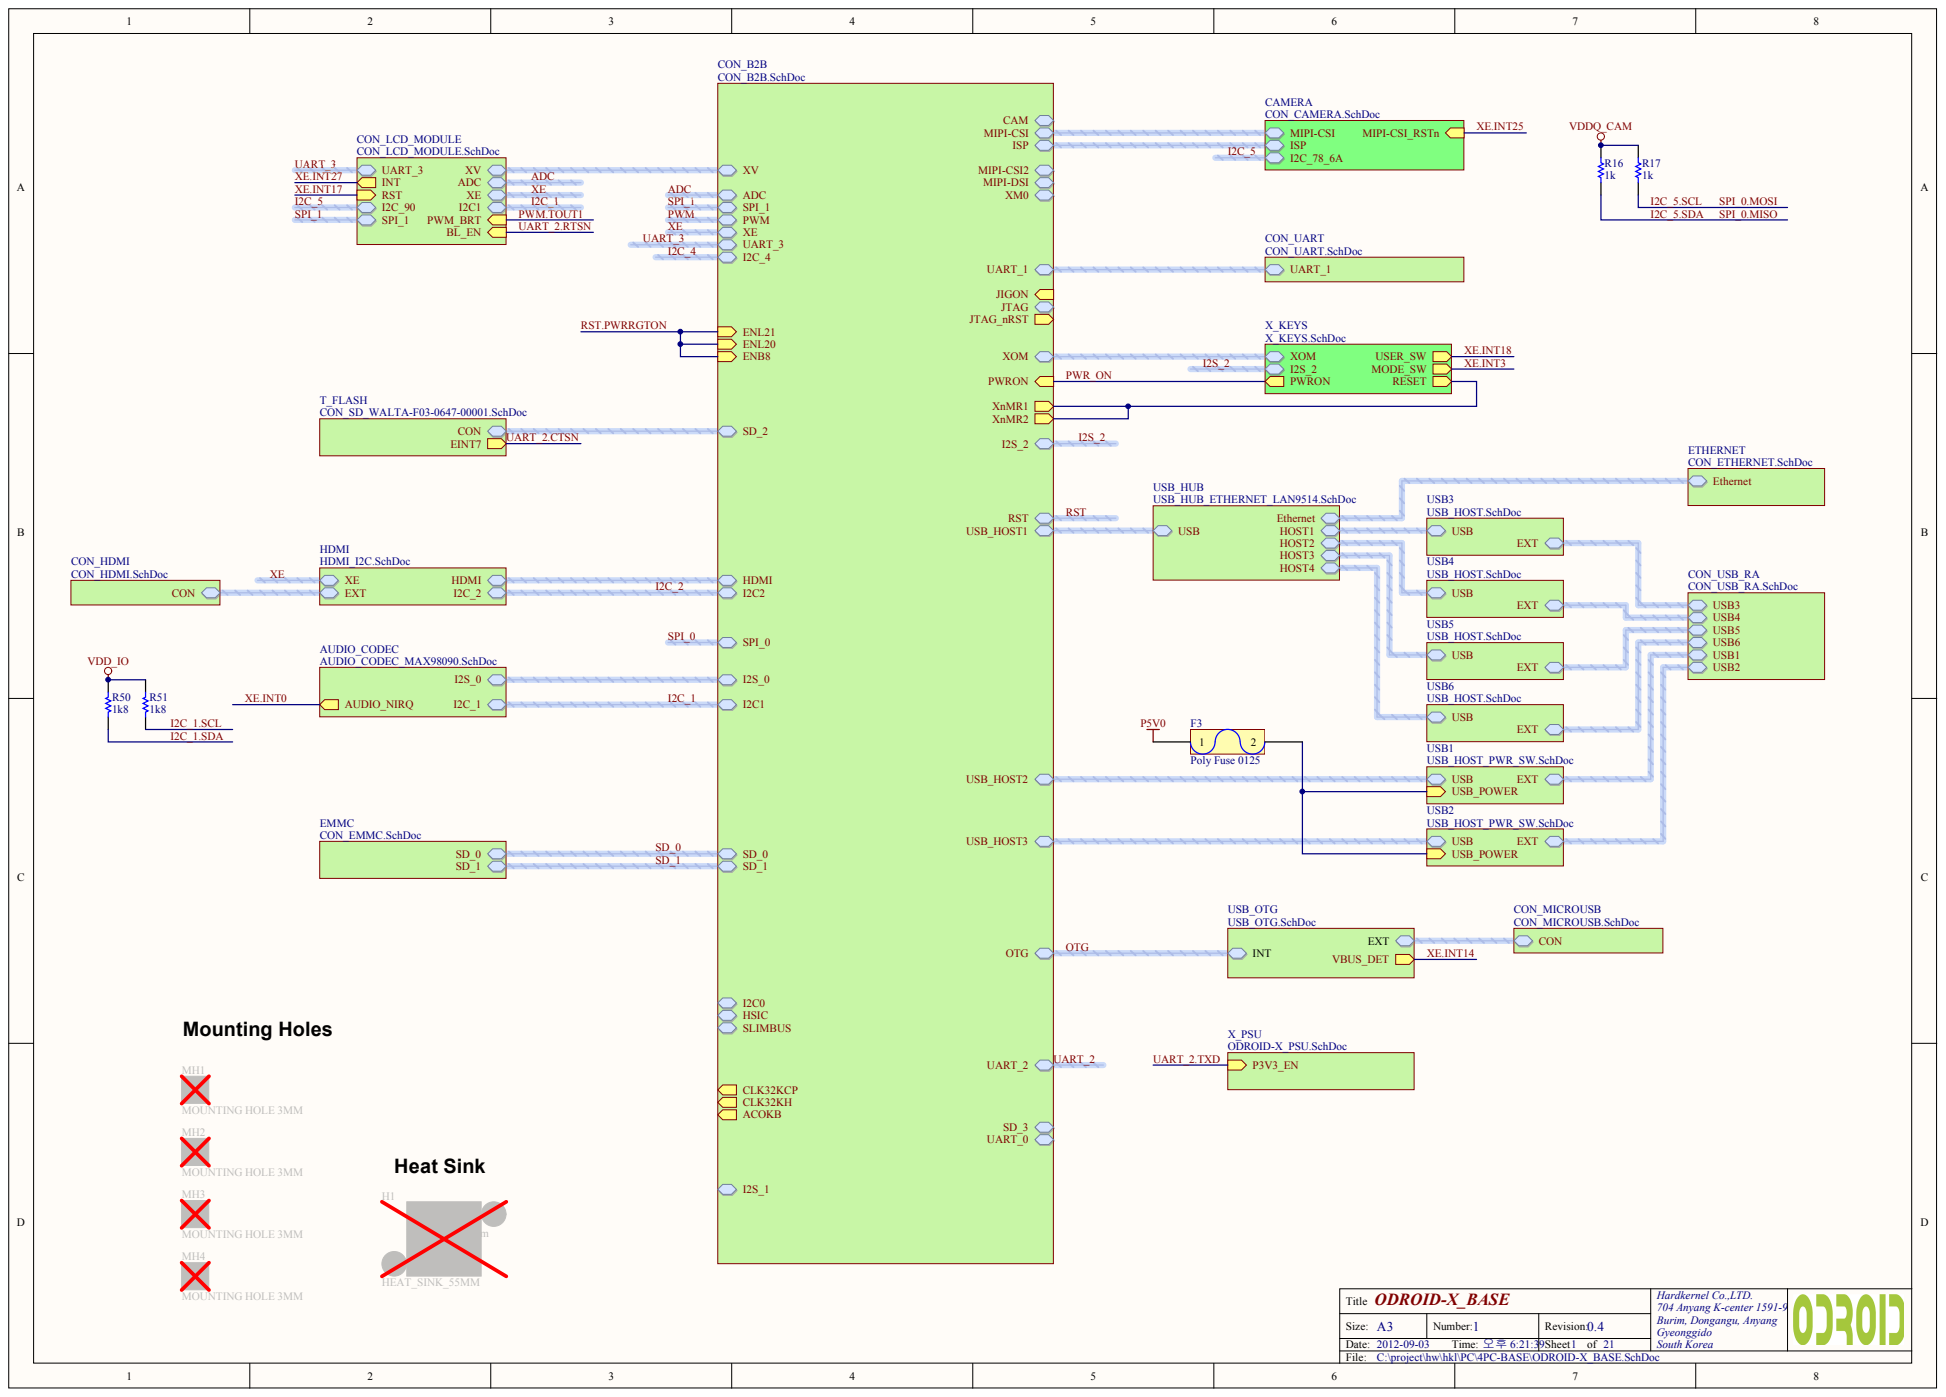
[picture p247: page 1]

ODROID-X_BASE Title | Hardkernel Co.,LTD. 704 Anyang K-center 1591-9 Burim, Dongangu, Anyang Gyeonggido South Korea

Size: A3 | Number: 1 | Revision: 0.4
2012-09-03 오후 6:21:39 Date: Time: | | Sheet of 21

C:\project\hw\hkl\PC\4PC-BASE\ODROID-X_BASE.SchDoc

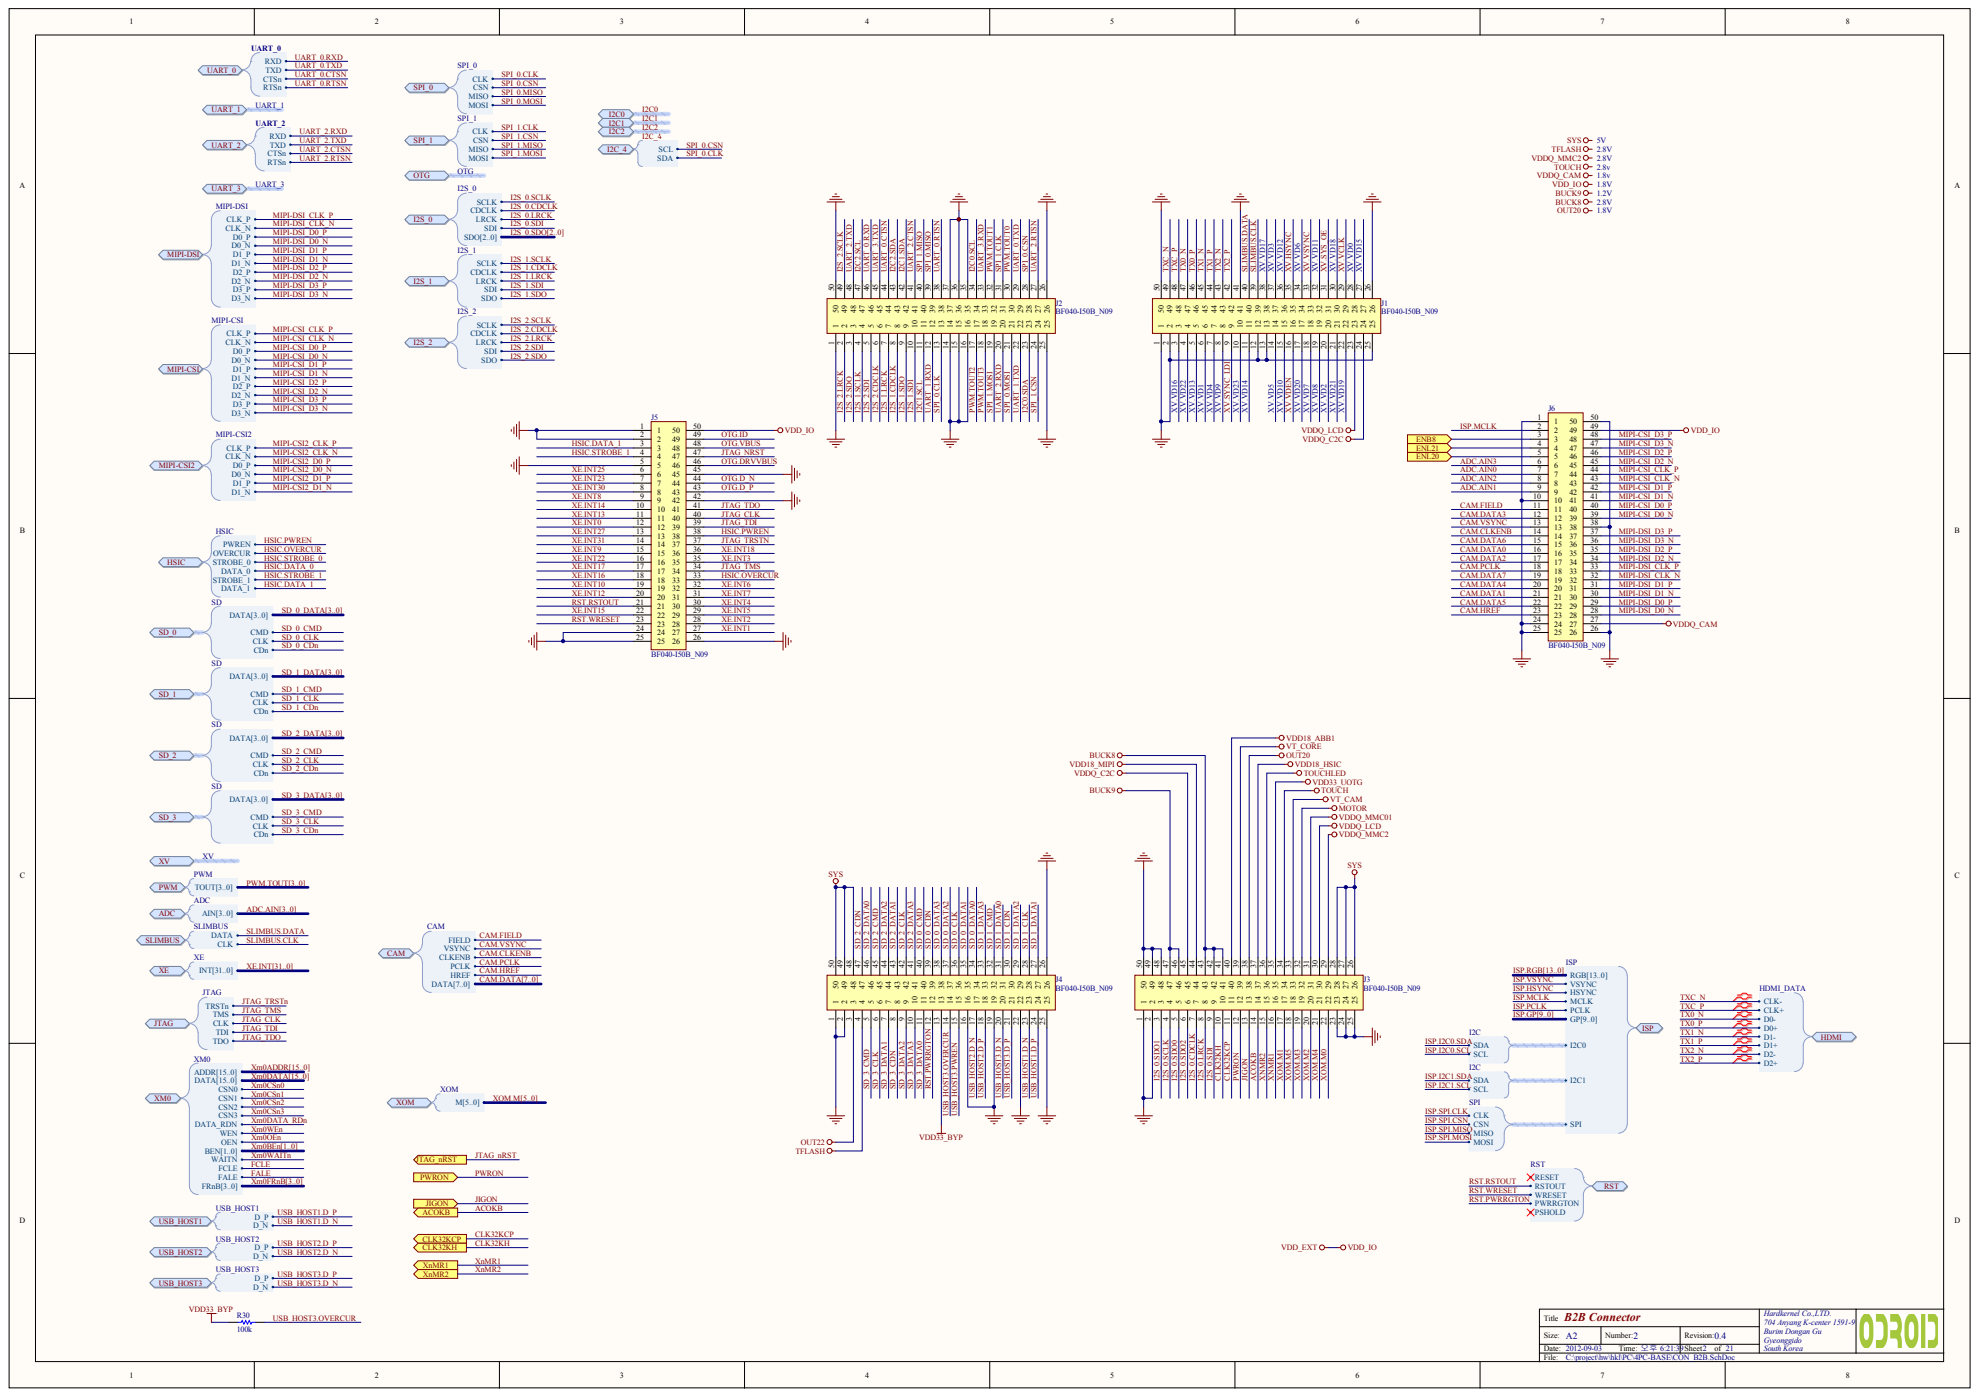
[picture p248: page 2]

Title B2B Connector | Hardkernel Co.,LTD. 704 Anyang K-center 1591-9 Burim Dongan Gu Gyeonggido

Size: A2 | Number: 2 | Revision: 0.4

C:\project\hw\hkl\PC\4PC-BASE\CON_B2B.SchDoc

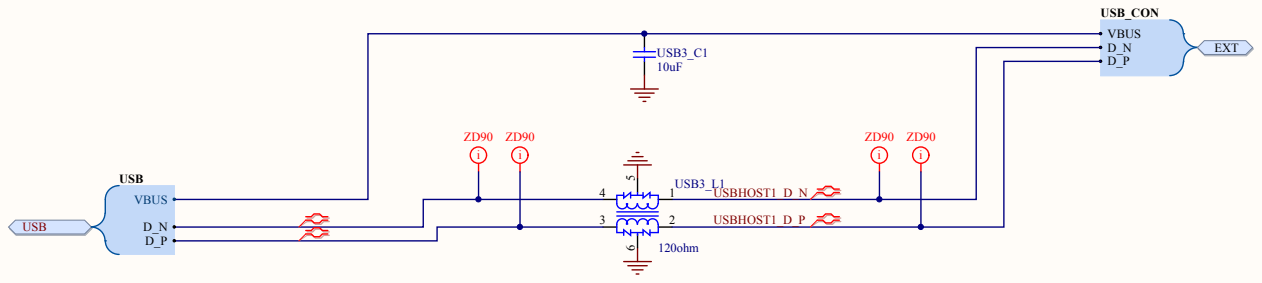
[picture p249: page 3]

USB HOST Title | Hardkernel Co.,LTD. 1-605 Shinan Metrokhan 1115 Dalandong, Dongangu, Anyang Gyeonggido

A4 Size: | 3 Number: | 0.4 Revision:

C:\project\hw\hkl\PC\4PC-BASE\USB_HOST.SchDoc

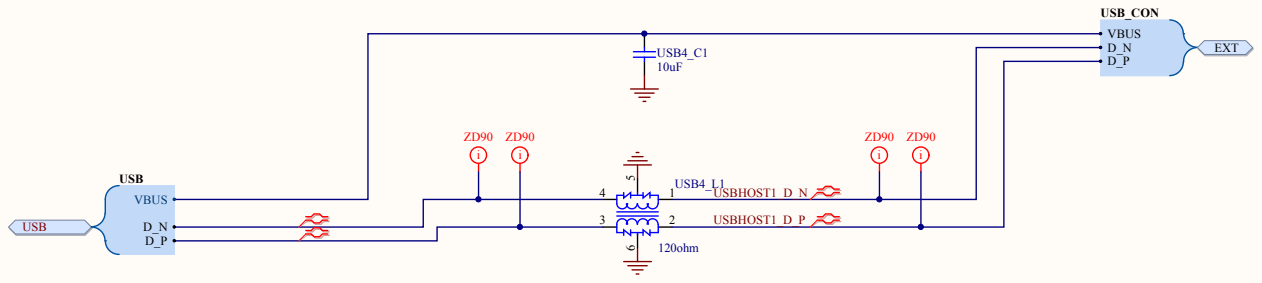
[picture p250: page 4]

USB HOST Title | Hardkernel Co.,LTD. 1-605 Shinan Metrokhan 1115 Dalandong, Dongangu, Anyang Gyeonggido

A4 Size: | 3 Number: | 0.4 Revision:

C:\project\hw\hkl\PC\4PC-BASE\USB_HOST.SchDoc

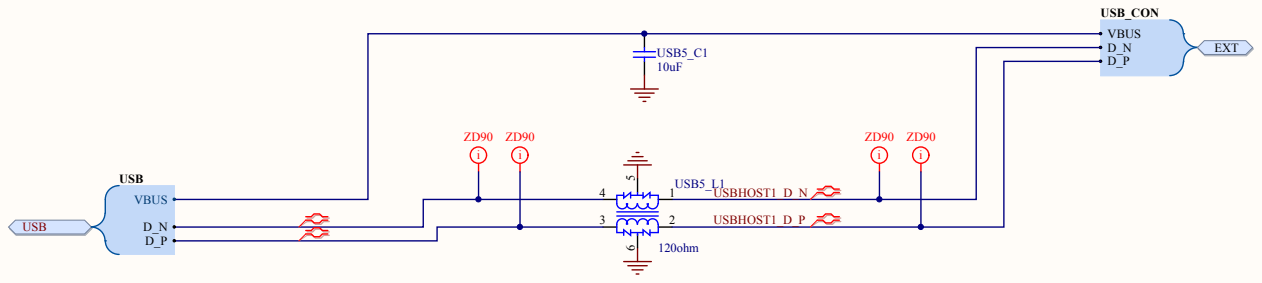
[picture p251: page 5]

USB HOST Title | Hardkernel Co.,LTD. 1-605 Shinan Metrokhan 1115 Dalandong, Dongangu, Anyang Gyeonggido

A4 Size: | 3 Number: | 0.4 Revision:

C:\project\hw\hkl\PC\4PC-BASE\USB_HOST.SchDoc

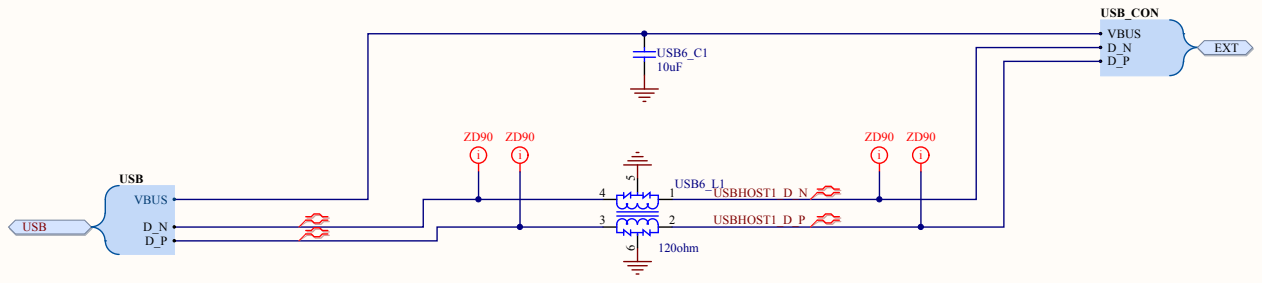
[picture p252: page 6]

USB HOST Title | Hardkernel Co.,LTD. 1-605 Shinan Metrokhan 1115 Dalandong, Dongangu, Anyang Gyeonggido

A4 Size: | 3 Number: | 0.4 Revision:

C:\project\hw\hkl\PC\4PC-BASE\USB_HOST.SchDoc

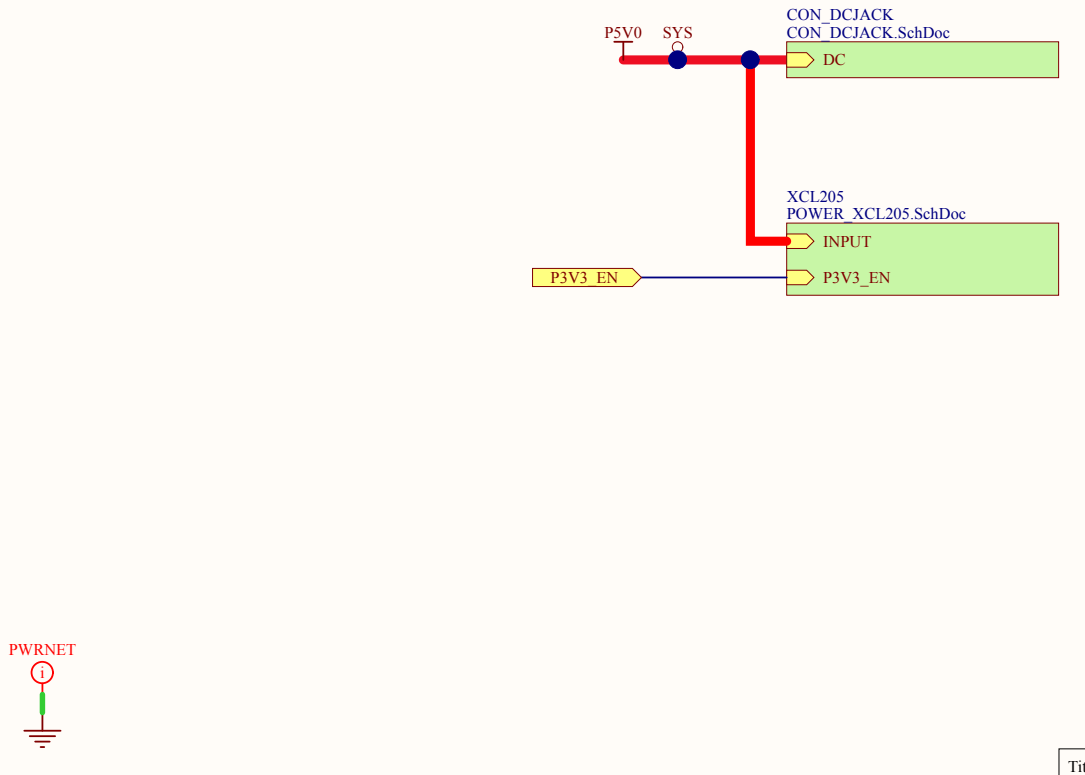
[picture p253: page 7]

POWER Title | Hardkernel Co.,LTD. 1-605 Shinan Metrokhan 1115 Dalandong, Dongangu, Anyang Gyeonggido

A4 Size: | 4 Number: | 0.4 Revision:

C:\project\hw\hkl\PC\4PC-BASE\ODROID-X_PSU.SchDoc

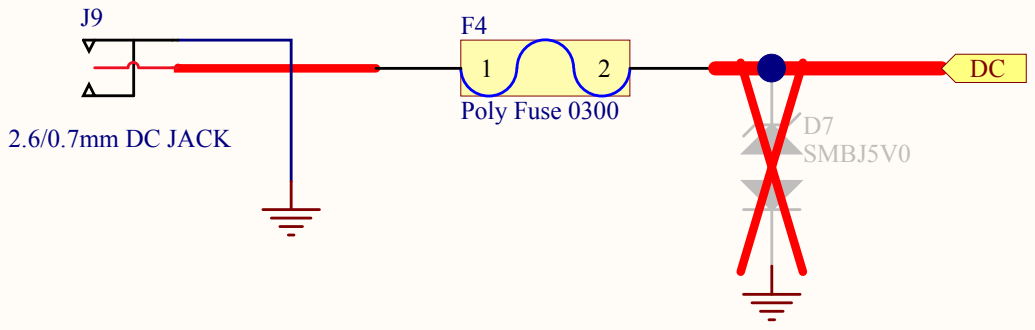
[picture p254: page 8]

DC Jack Title | Hardkernel Co.,LTD. 704 Anyang K-center 1591-9 Burim, Dongangu, Anyang Gyeonggido

A4 Size: | 5 Number: | 0.4 Revision:

C:\project\hw\hkl\PC\4PC-BASE\CON_DCJACK.SchDoc

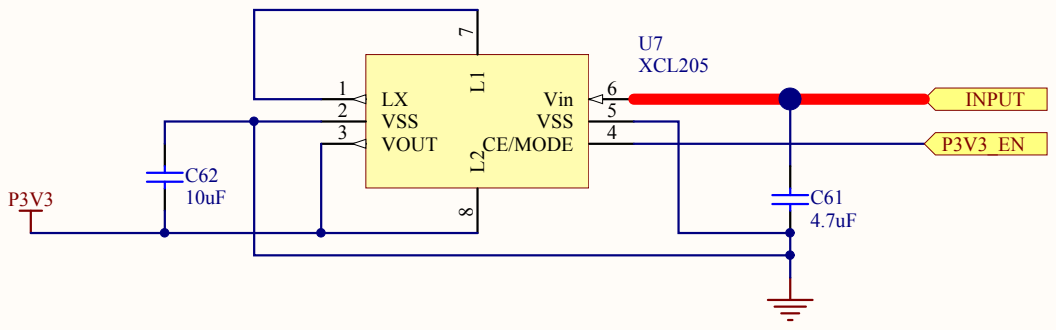
[picture p255: page 9]

Title | Hardkernel Co.,LTD. 704 Anyang K-center 1591-9 Burim, Dongangu, Anyang Gyeonggido

A4 Size: | Number: | Revision:

C:\project\hw\hkl\PC\4PC-BASE\POWER_XCL205.SchDoc

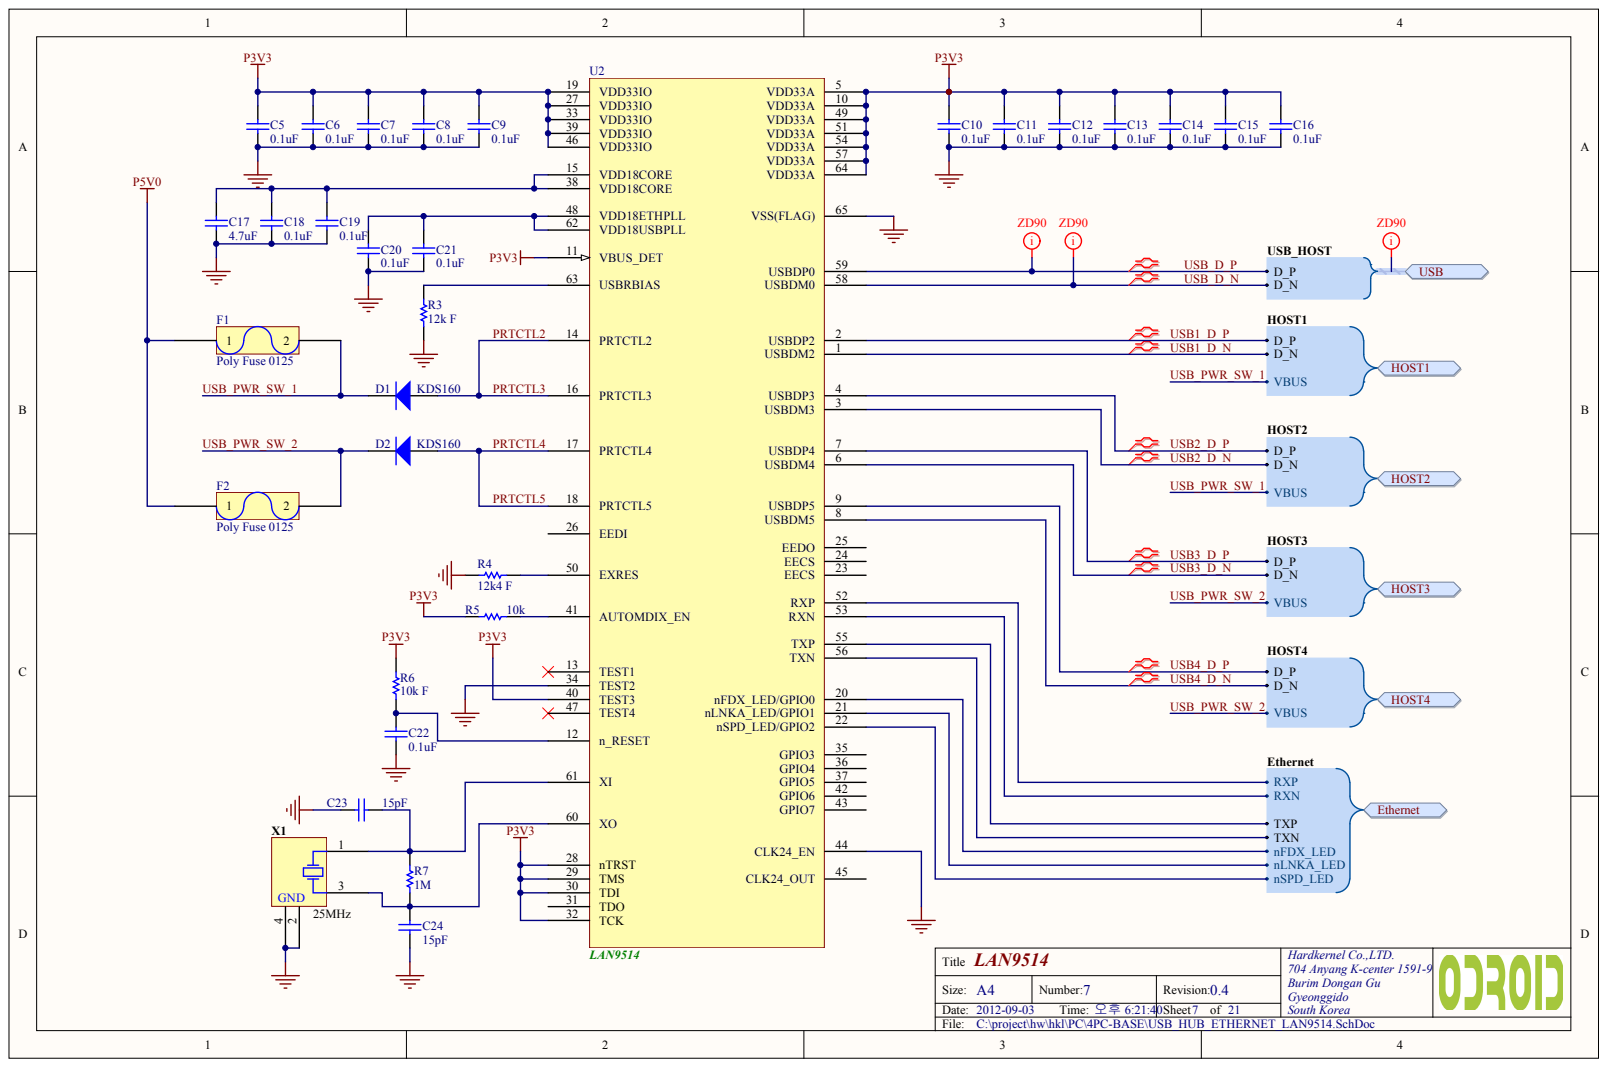
[picture p256: page 10]

PRTCTL4 17 | 3

7 | USB2_D_P

PRTCTL5 | | PRTCTL5 18 | 6 | USB2_D_N

9 | USB_PWR_SW_1

USB4_D_P

TEST2 34 | USB4_D_N

TEST4 47 | | USB_PWR_SW_2

C22 | | n_RESET 12

TMS 29
TDI 30

GND

LAN9514 Title | Hardkernel Co.,LTD. 704 Anyang K-center 1591-9 Burim Dongan Gu Gyeonggido

A4 Size: | 7 Number: | 0.4 Revision:

C:\project\hw\hkl\PC\4PC-BASE\USB_HUB_ETHERNET_LAN9514.SchDoc

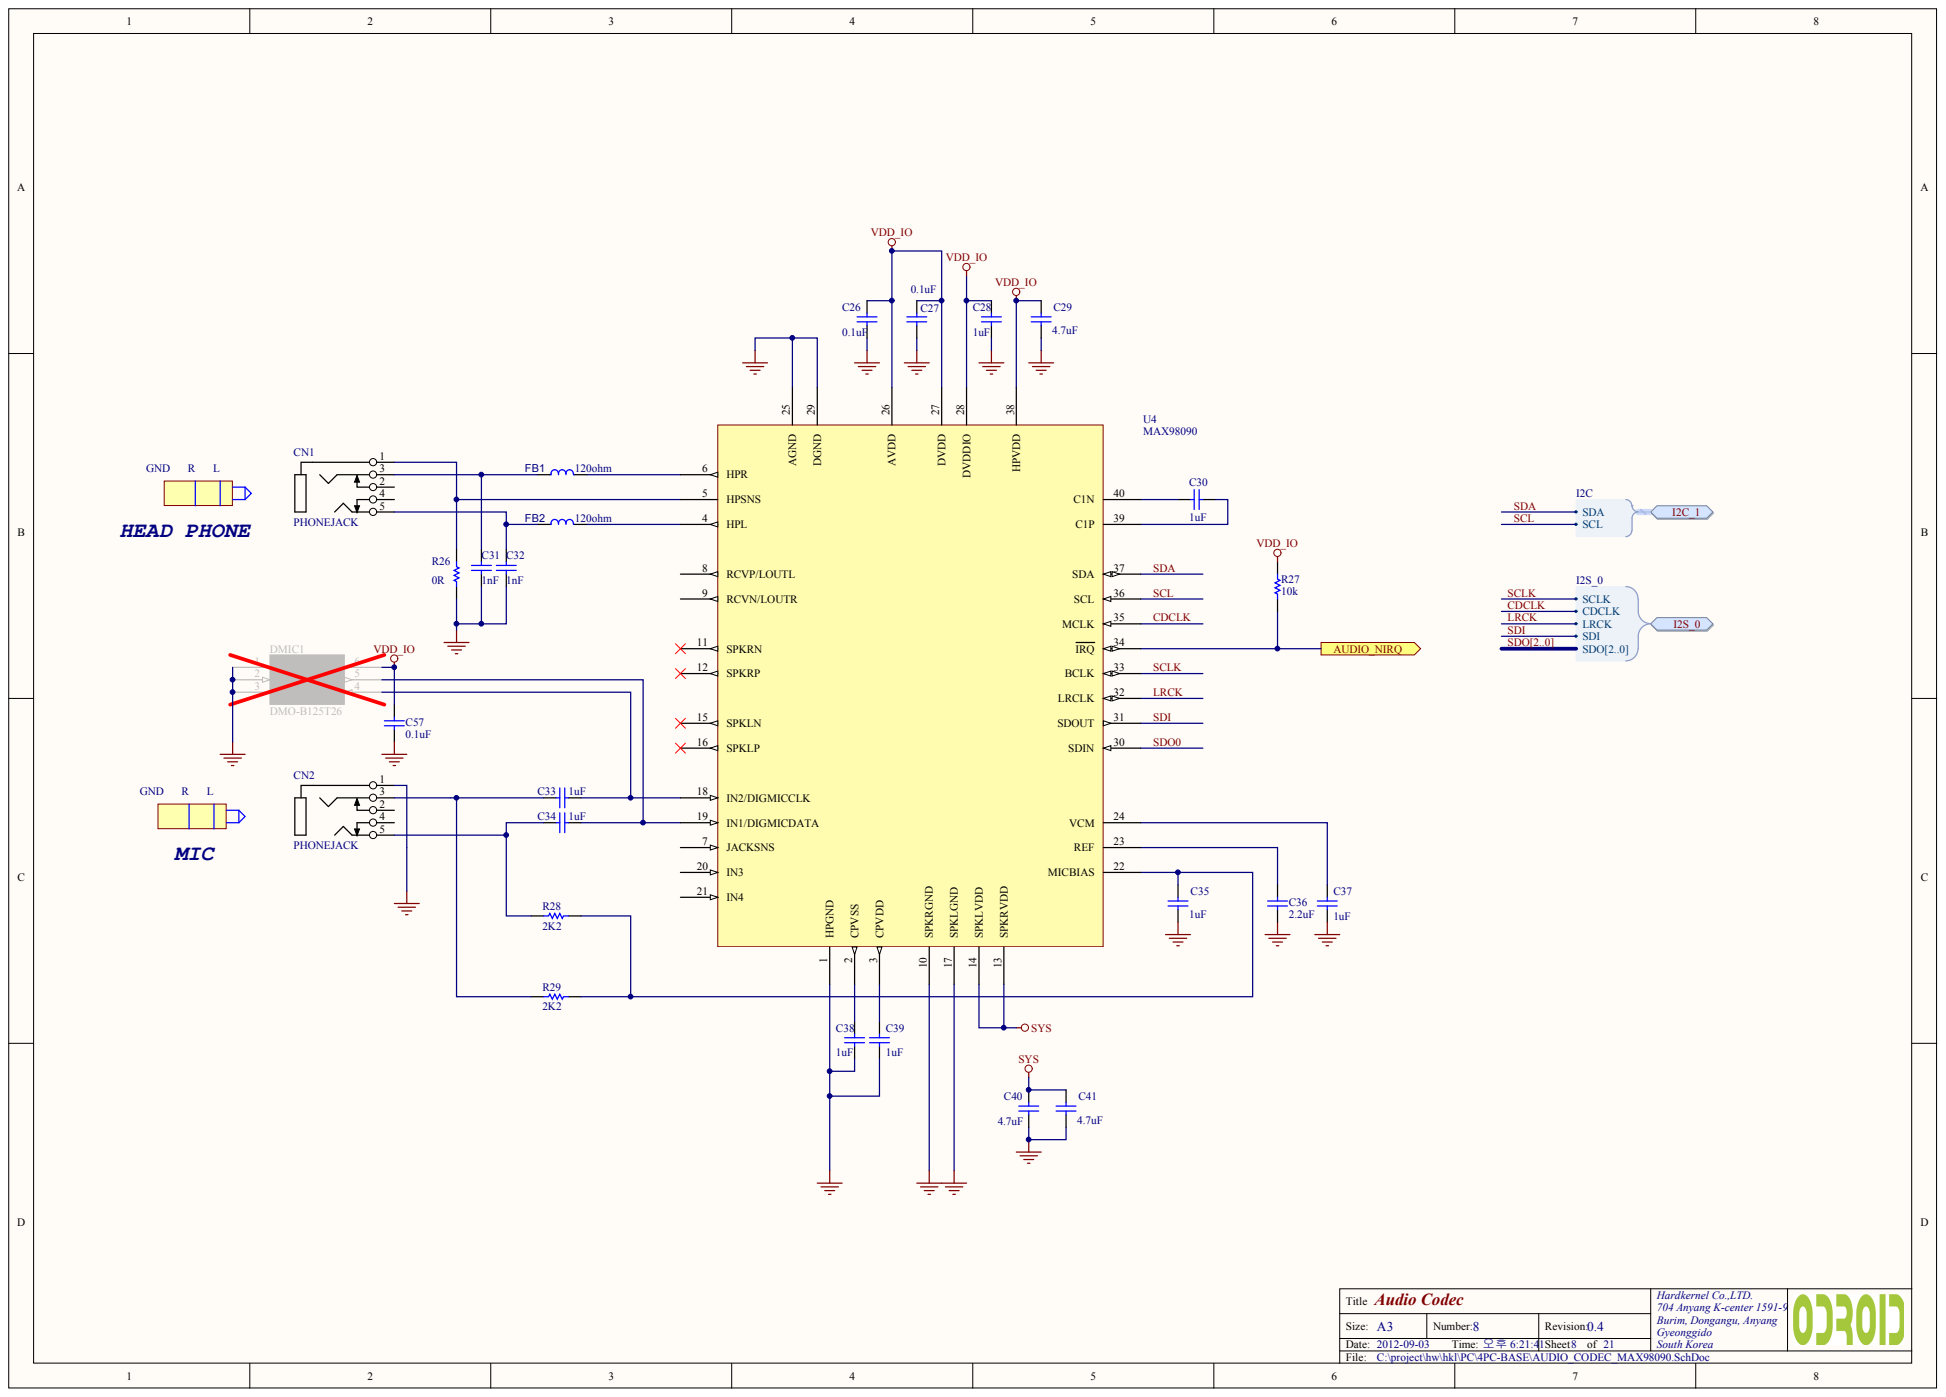
[picture p257: page 11]

Audio Codec Title | Hardkernel Co.,LTD. 704 Anyang K-center 1591-9 Burim, Dongangu, Anyang Gyeonggido

Size: A3 | Number: 8 | Revision: 0.4

C:\project\hw\hkl\PC\4PC-BASE\AUDIO_CODEC_MAX98090.SchDoc

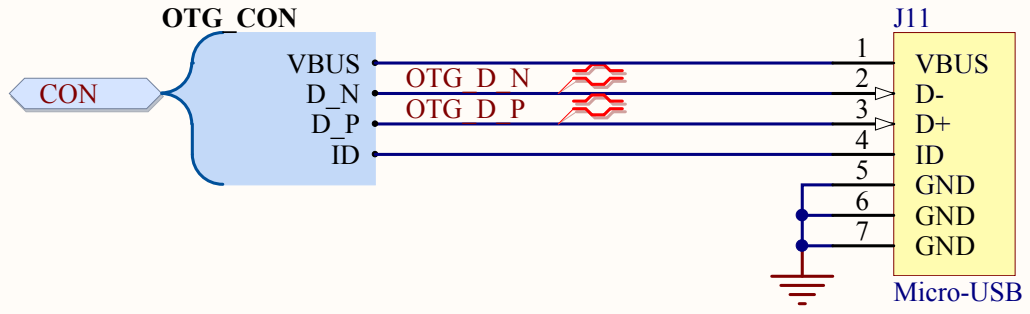
[picture p258: page 12]

Title | Hardkernel Co.,LTD. 704 Angyang K-center 1591-9 Burim, Dongangu, Anyang Kyeonggido

A4 Size: | Number: | Revision:

C:\project\hw\hkl\PC\4PC-BASE\CON_MICROUSB.SchDoc

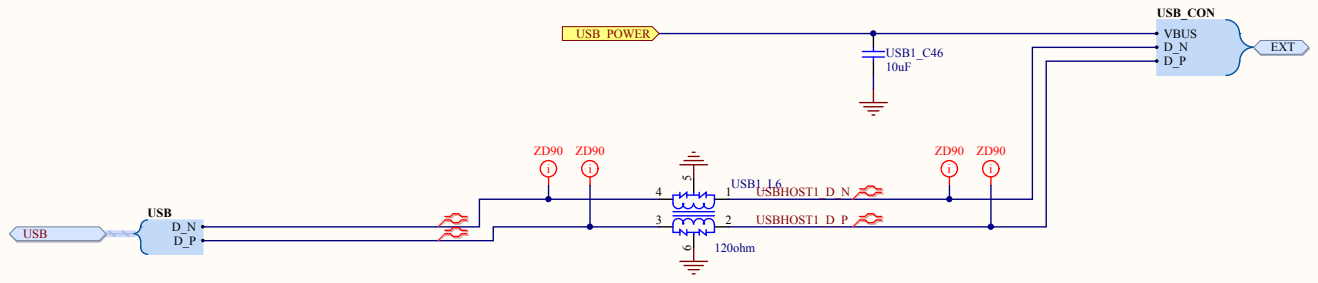
[picture p259: page 13]

* Title | Hardkernel Co.,LTD. 704 Anyang K-center 1591-9 Burim, Dongangu, Anyang Gyeonggido

A4 Size: | 10 Number: | 0.4 Revision:

C:\project\hw\hkl\PC\4PC-BASE\USB_HOST_PWR_SW.SchDoc

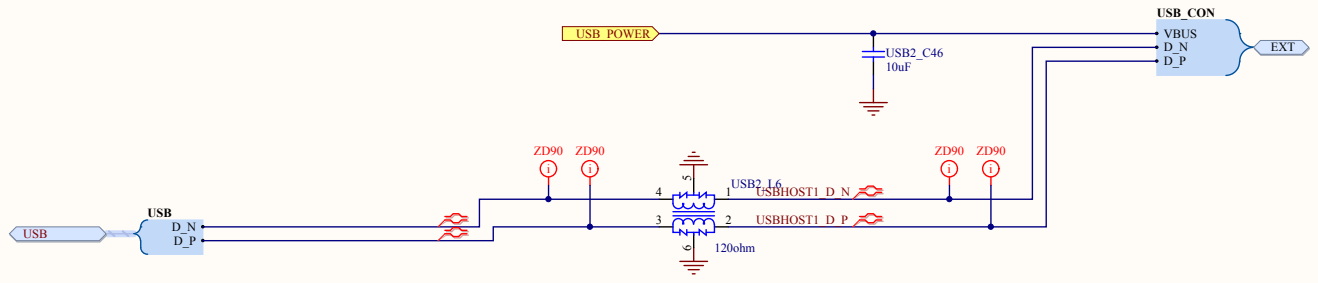
[picture p260: page 14]

* Title | Hardkernel Co.,LTD. 704 Anyang K-center 1591-9 Burim, Dongangu, Anyang Gyeonggido

A4 Size: | 10 Number: | 0.4 Revision:

C:\project\hw\hkl\PC\4PC-BASE\USB_HOST_PWR_SW.SchDoc

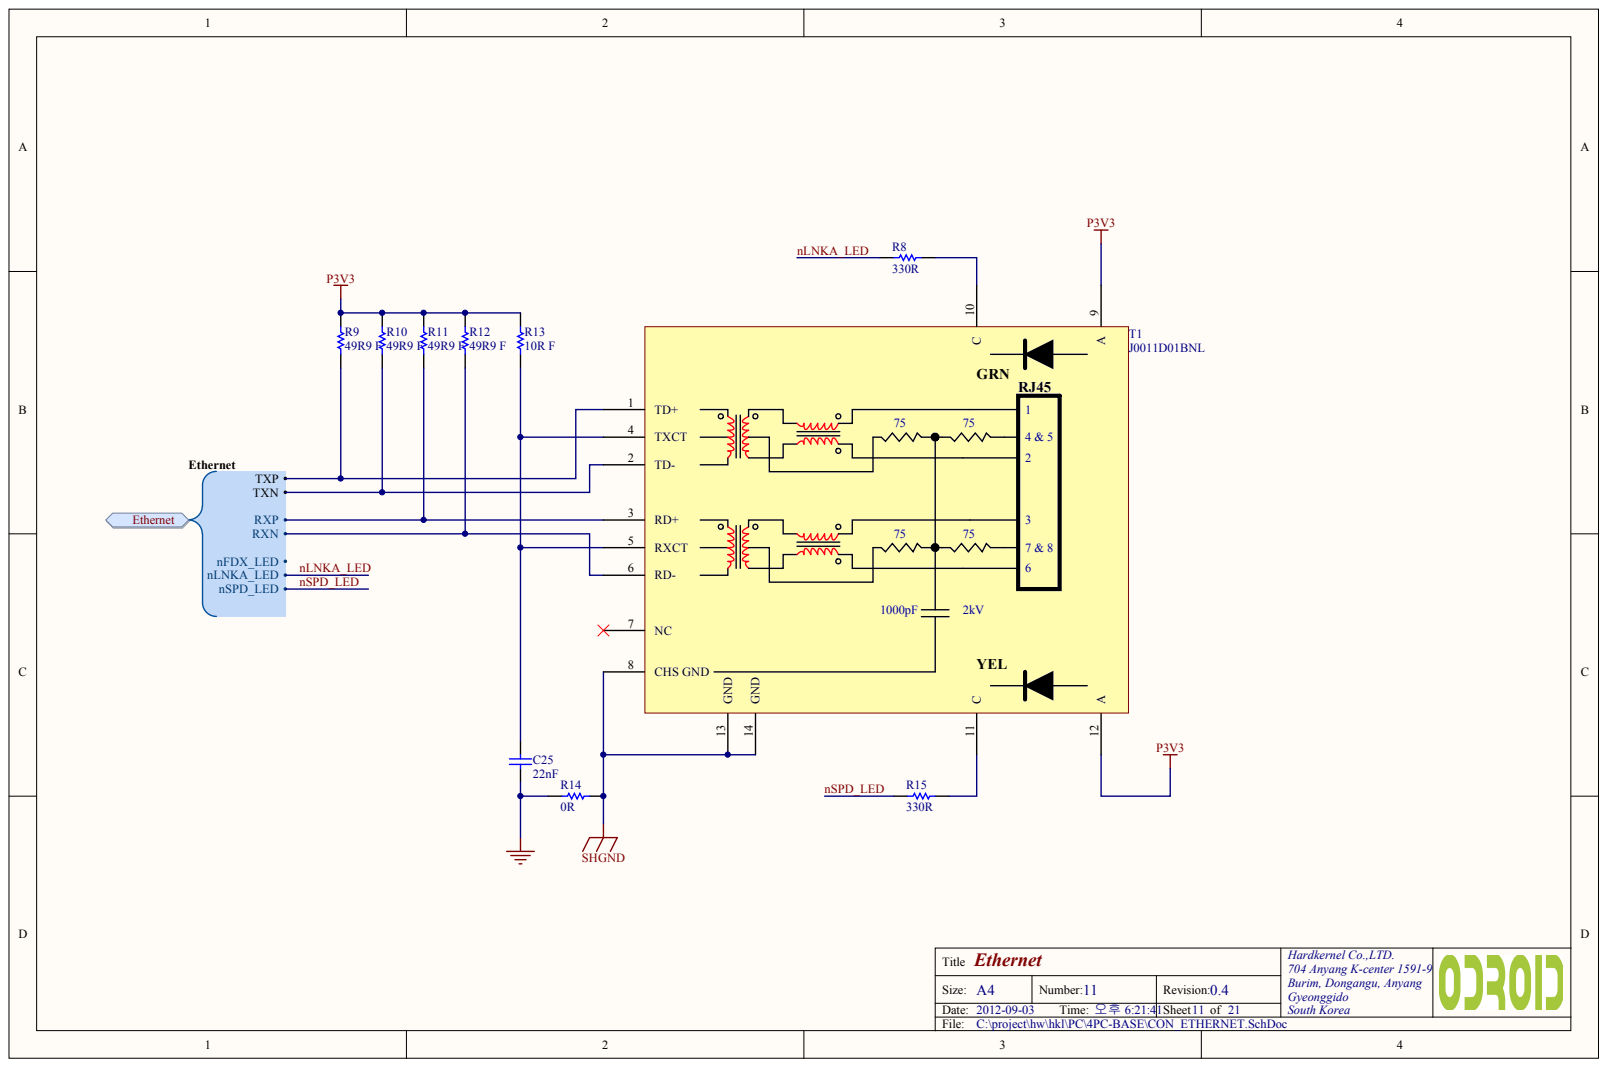
[picture p261: page 15]

TXCT 4

RXCT 5

nLNKA_LED

Ethernet Title | Hardkernel Co.,LTD. 704 Anyang K-center 1591-9 Burim, Dongangu, Anyang Gyeonggido

A4 Size: | 11 Number: | 0.4 Revision:

C:\project\hw\hkl\PC\4PC-BASE\CON_ETHERNET.SchDoc

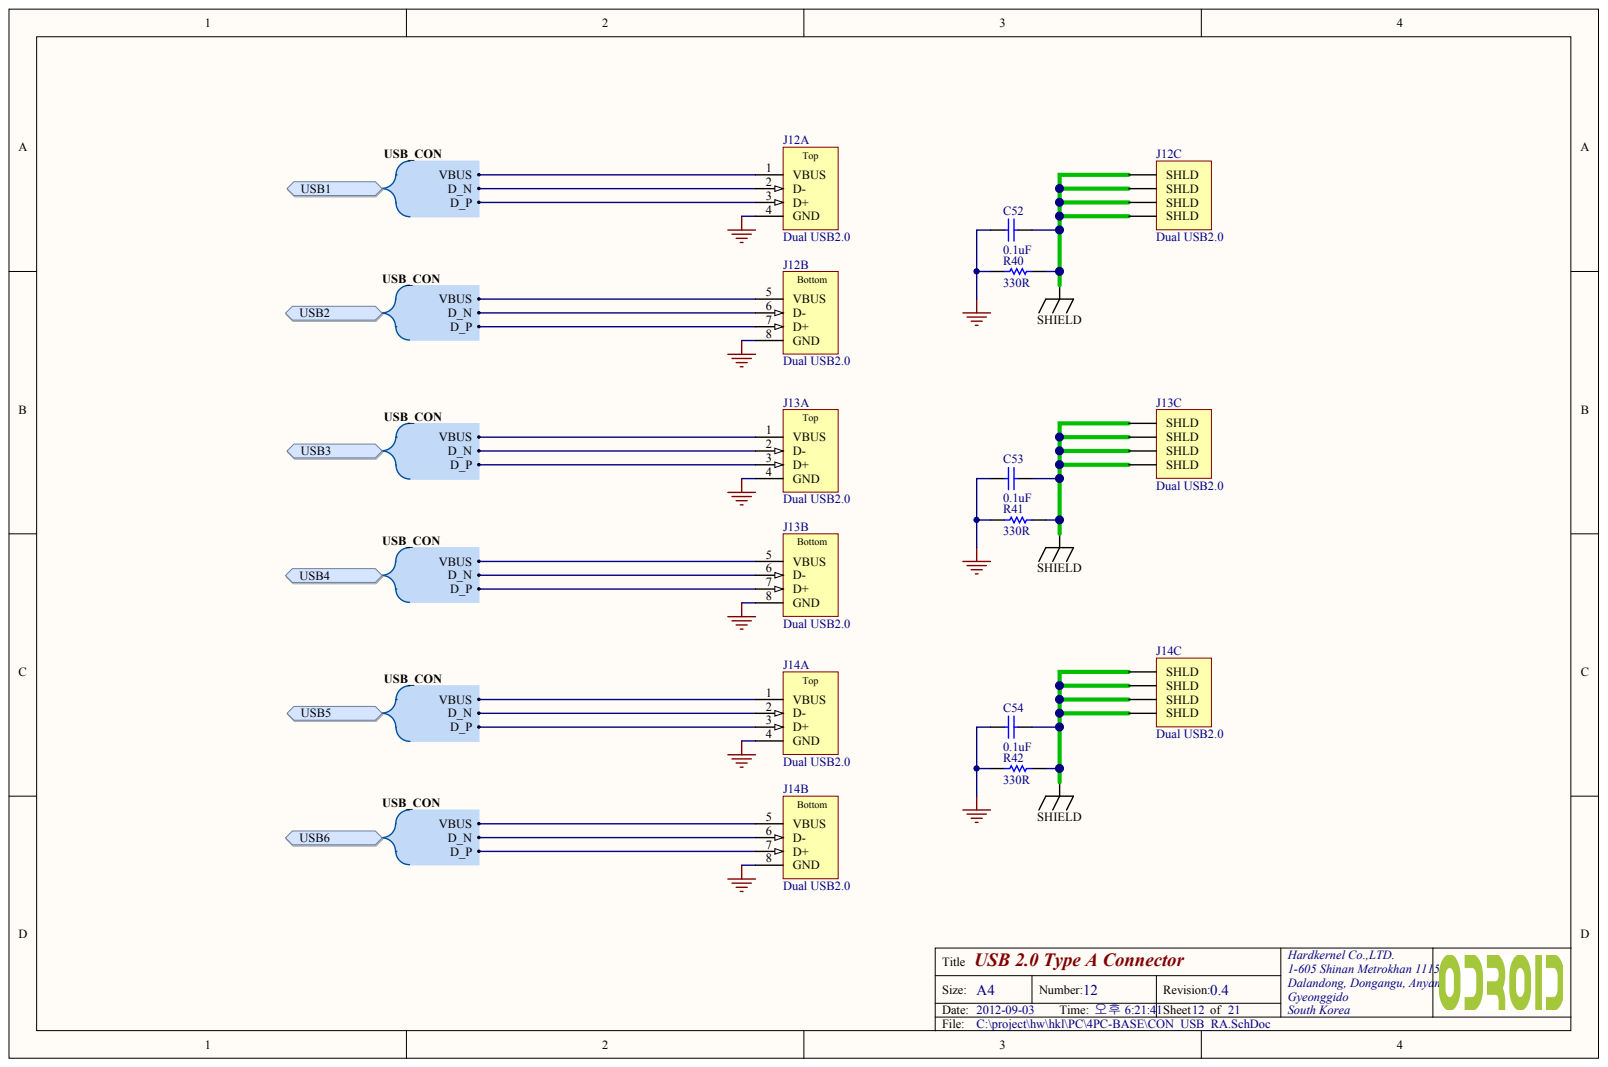
[picture p262: page 16]

USB 2.0 Type A Connector Title | Hardkernel Co.,LTD. 1-605 Shinan Metrokhan 1115 Dalandong, Dongangu, Anyang Gyeonggido

A4 Size: | 12 Number: | 0.4 Revision:

C:\project\hw\hkl\PC\4PC-BASE\CON_USB_RA.SchDoc

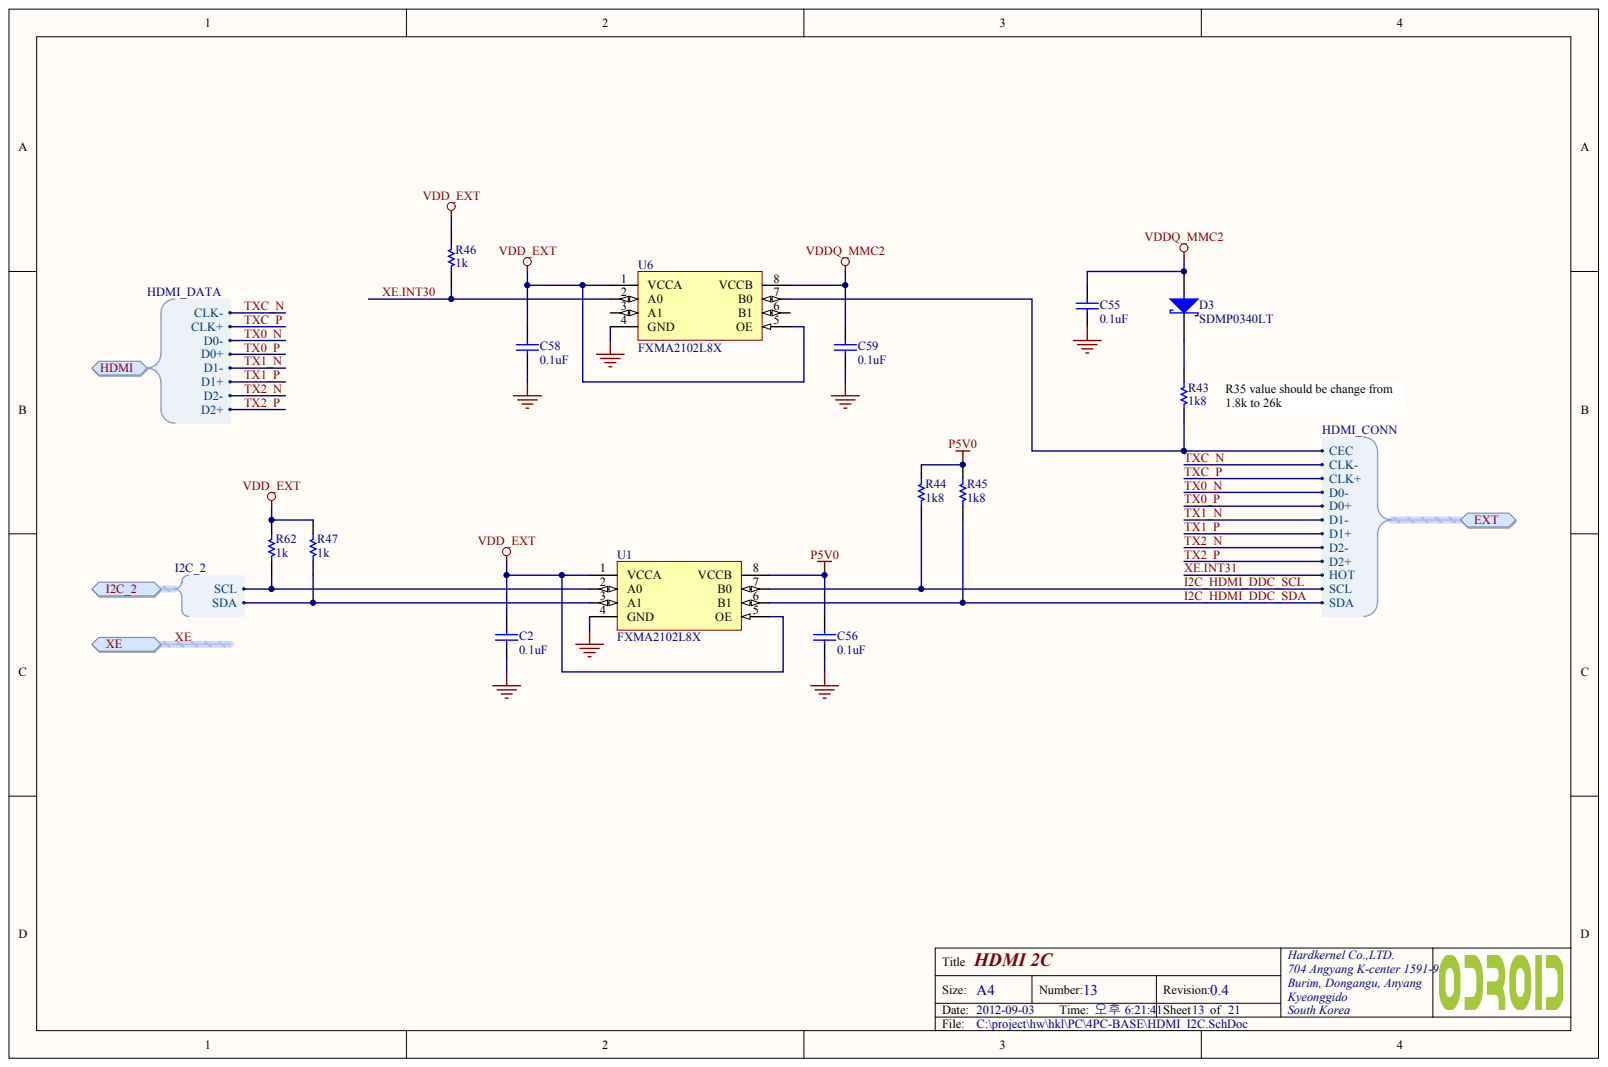
[picture p263: page 17]

4 | A0 B0 A1 3 B1 GND OE | 7

R35 value should be change from

HDMI 2C Title | Hardkernel Co.,LTD. 704 Angyang K-center 1591-9 Burim, Dongangu, Anyang Kyeonggido

A4 Size: | 13 Number: | 0.4 Revision:

C:\project\hw\hkl\PC\4PC-BASE\HDMI_I2C.SchDoc

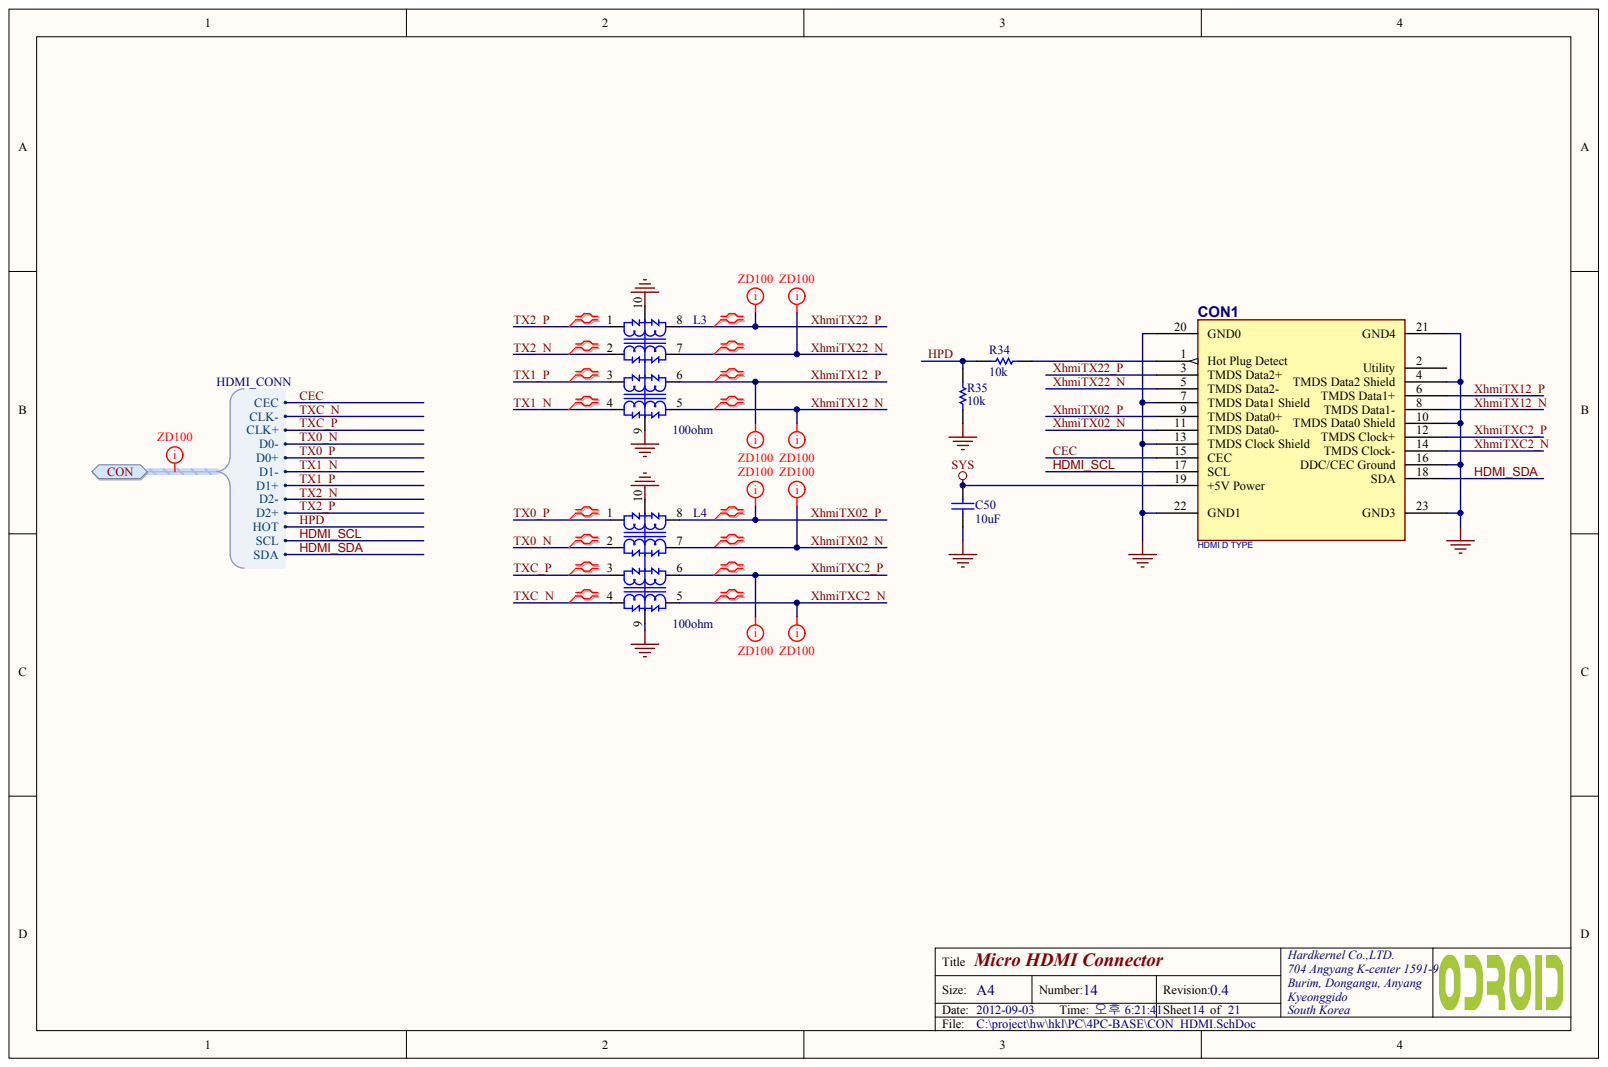
[picture p264: page 18]

Micro HDMI Connector Title | Hardkernel Co.,LTD. 704 Angyang K-center 1591-9 Burim, Dongangu, Anyang Kyeonggido

A4 Size: | 14 Number: | 0.4 Revision:

C:\project\hw\hkl\PC\4PC-BASE\CON_HDMI.SchDoc

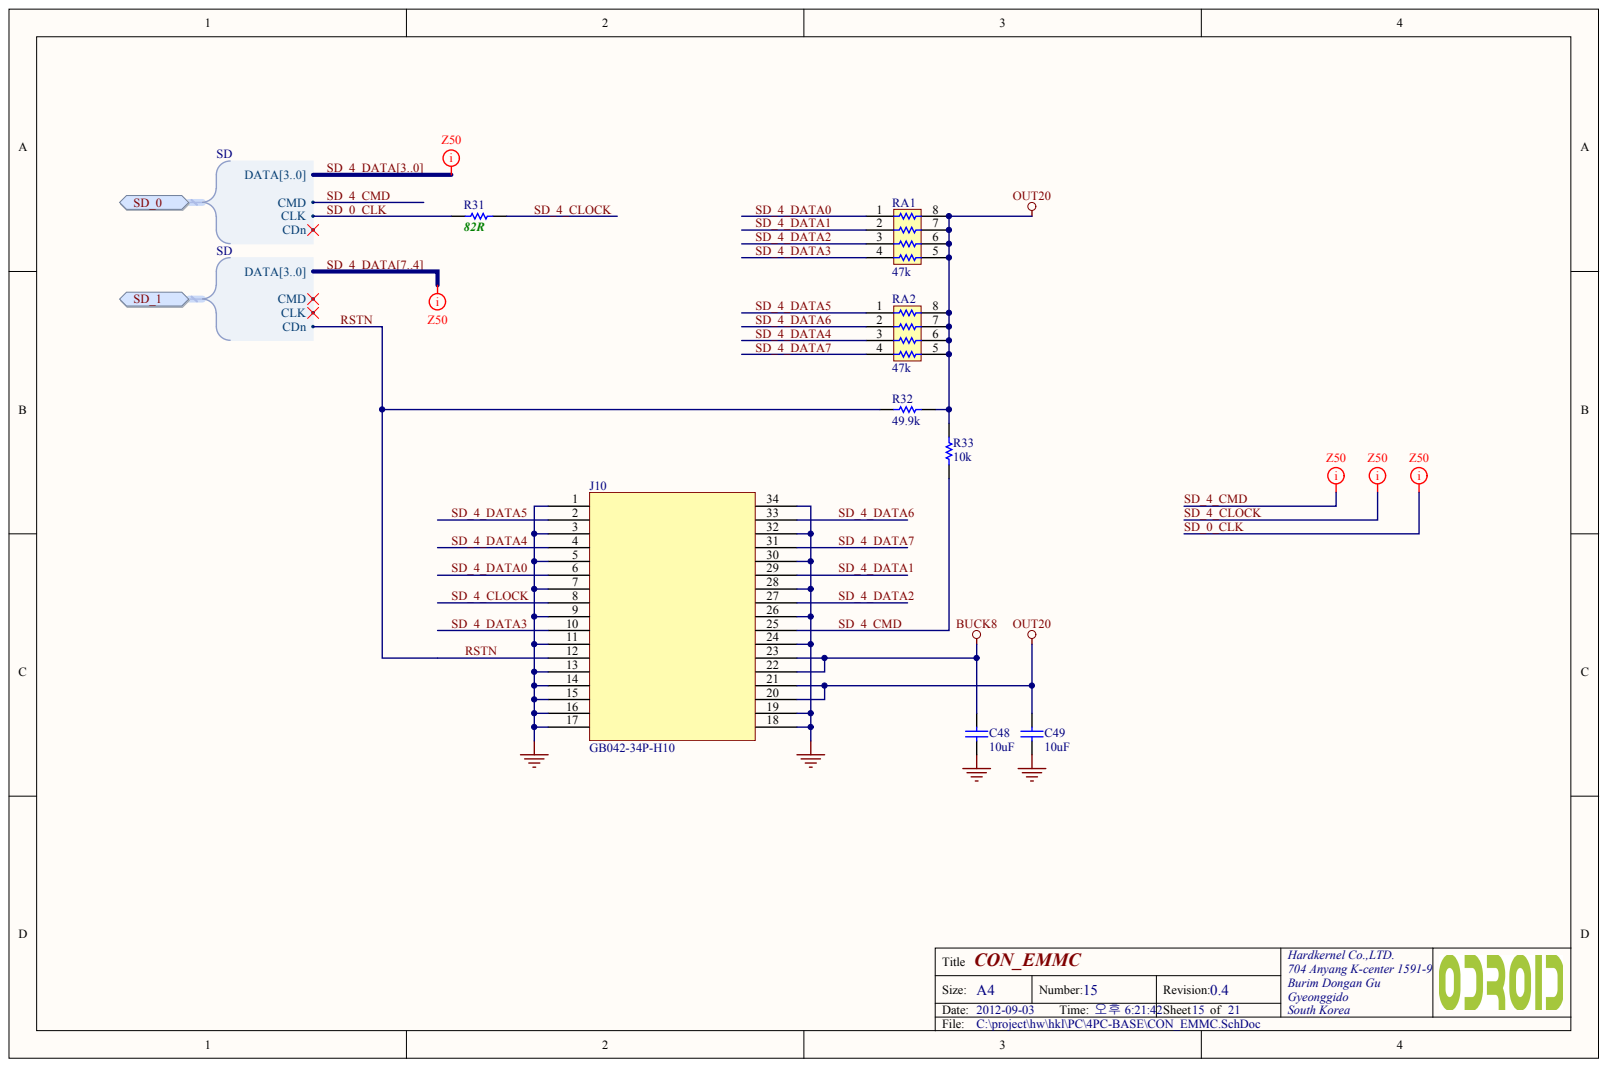
[picture p265: page 19]

SD_4_DATA0 | | 5

6 | | 29 28
8 | | 27 26
10 | | 25

RSTN | | 11 | | 24

12 | | 23
13 | | 22
14 | | 21
15 | | 20
16 | | 19
17 | | 18

CON_EMMC Title | Hardkernel Co.,LTD. 704 Anyang K-center 1591-9 Burim Dongan Gu Gyeonggido

A4 Size: | 15 Number: | 0.4 Revision:

C:\project\hw\hkl\PC\4PC-BASE\CON_EMMC.SchDoc

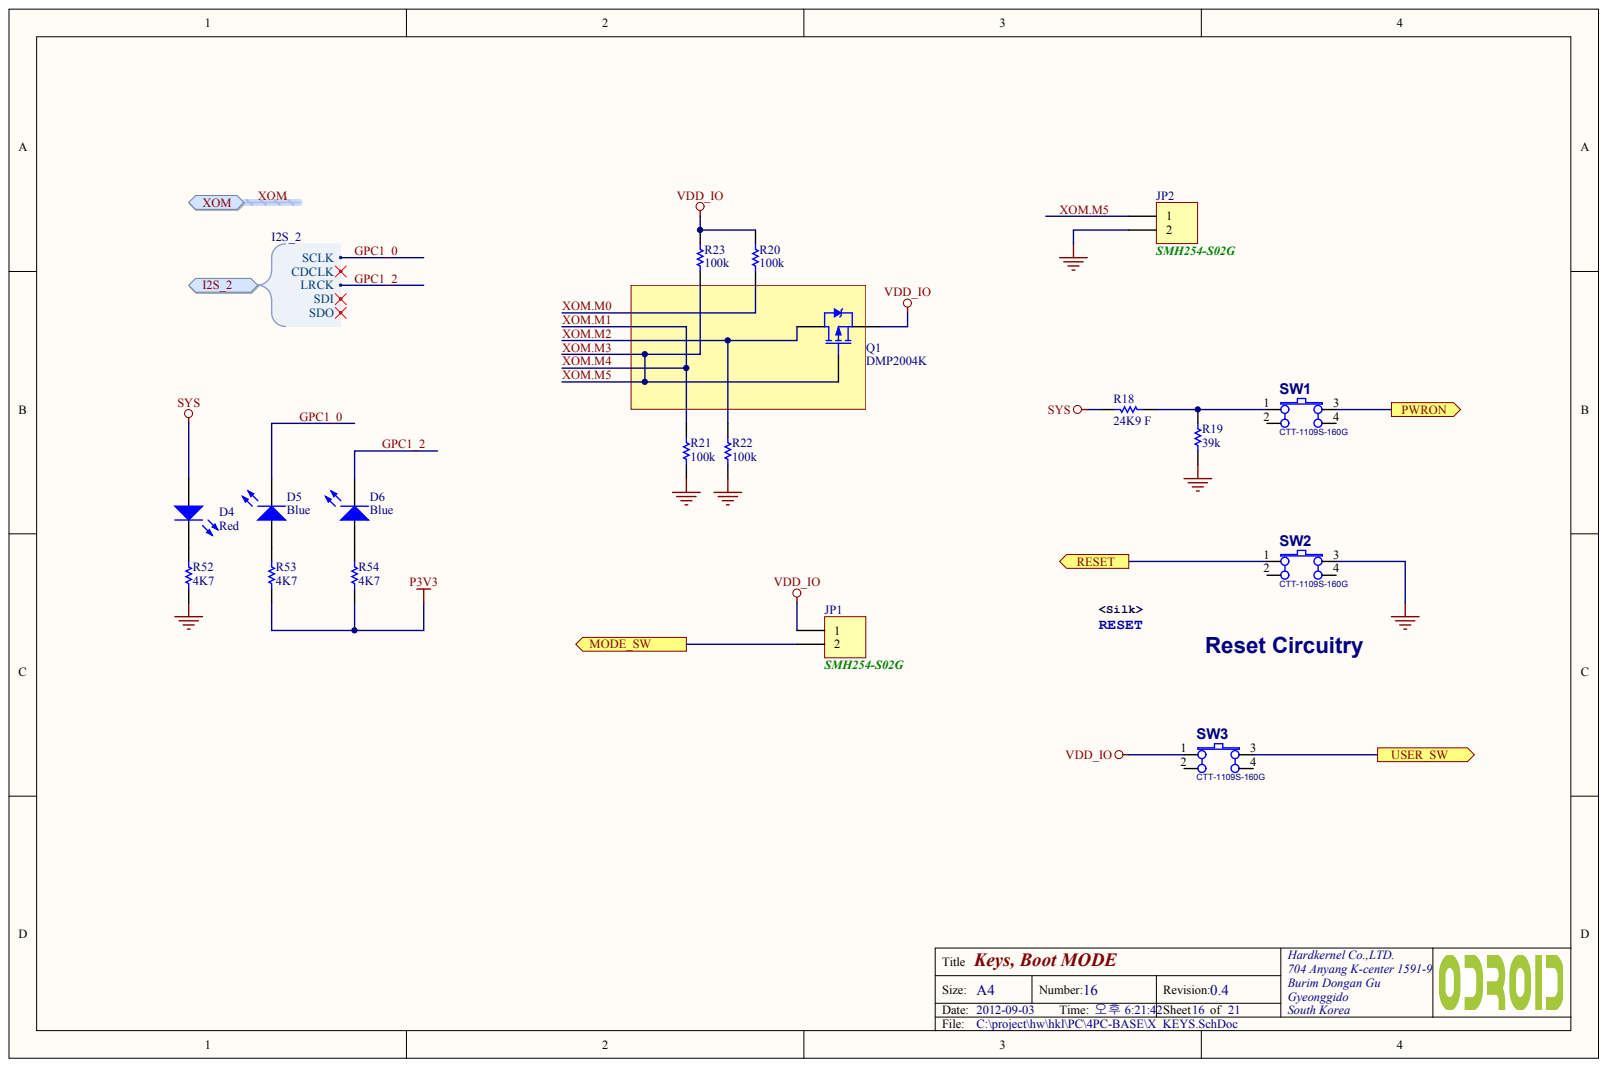
[picture p266: page 20]

XOM.M0
XOM.M1
XOM.M2
XOM.M3
XOM.M4
XOM.M5

Keys, Boot MODE Title | Hardkernel Co.,LTD. 704 Anyang K-center 1591-9 Burim Dongan Gu Gyeonggido

A4 Size: | 16 Number: | 0.4 Revision:

C:\project\hw\hkl\PC\4PC-BASE\X_KEYS.SchDoc

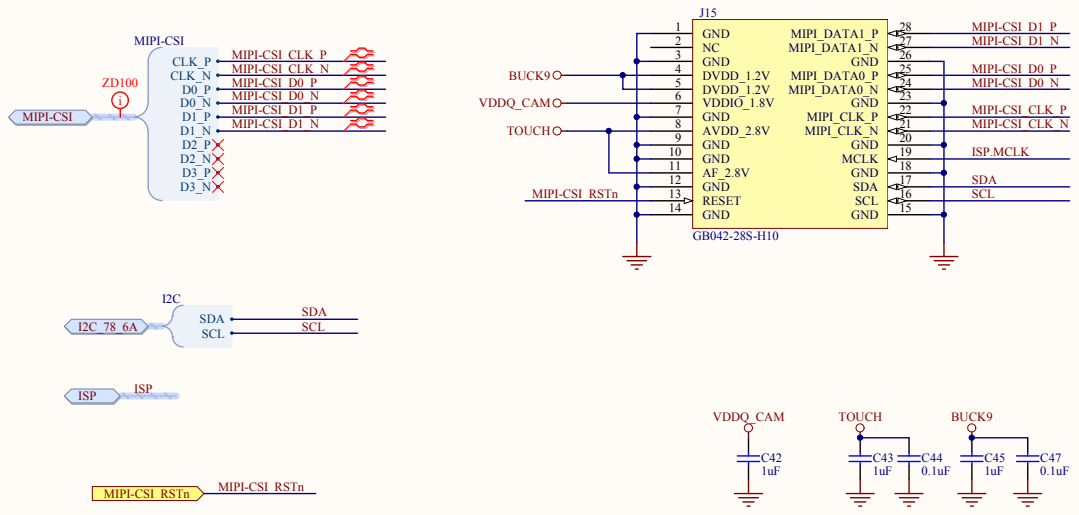
[picture p267: page 21]

AVDD_2.8V 8 GND 9

GND 10
AF_2.8V 11
GND 12
RESET 13

Con - Camera Title | Hardkernel Co.,LTD. 704 Anyang K-Center, Gwanyang, Dongan, Anyang, Gyeonggido | Cannot open file C:\Users\ydongyol\Do wnloads\Odroid-A_Lo

A4 Size: | 17 Number: | 0.4 Revision:

C:\project\hw\hkl\PC\4PC-BASE\CON_CAMERA.SchDoc

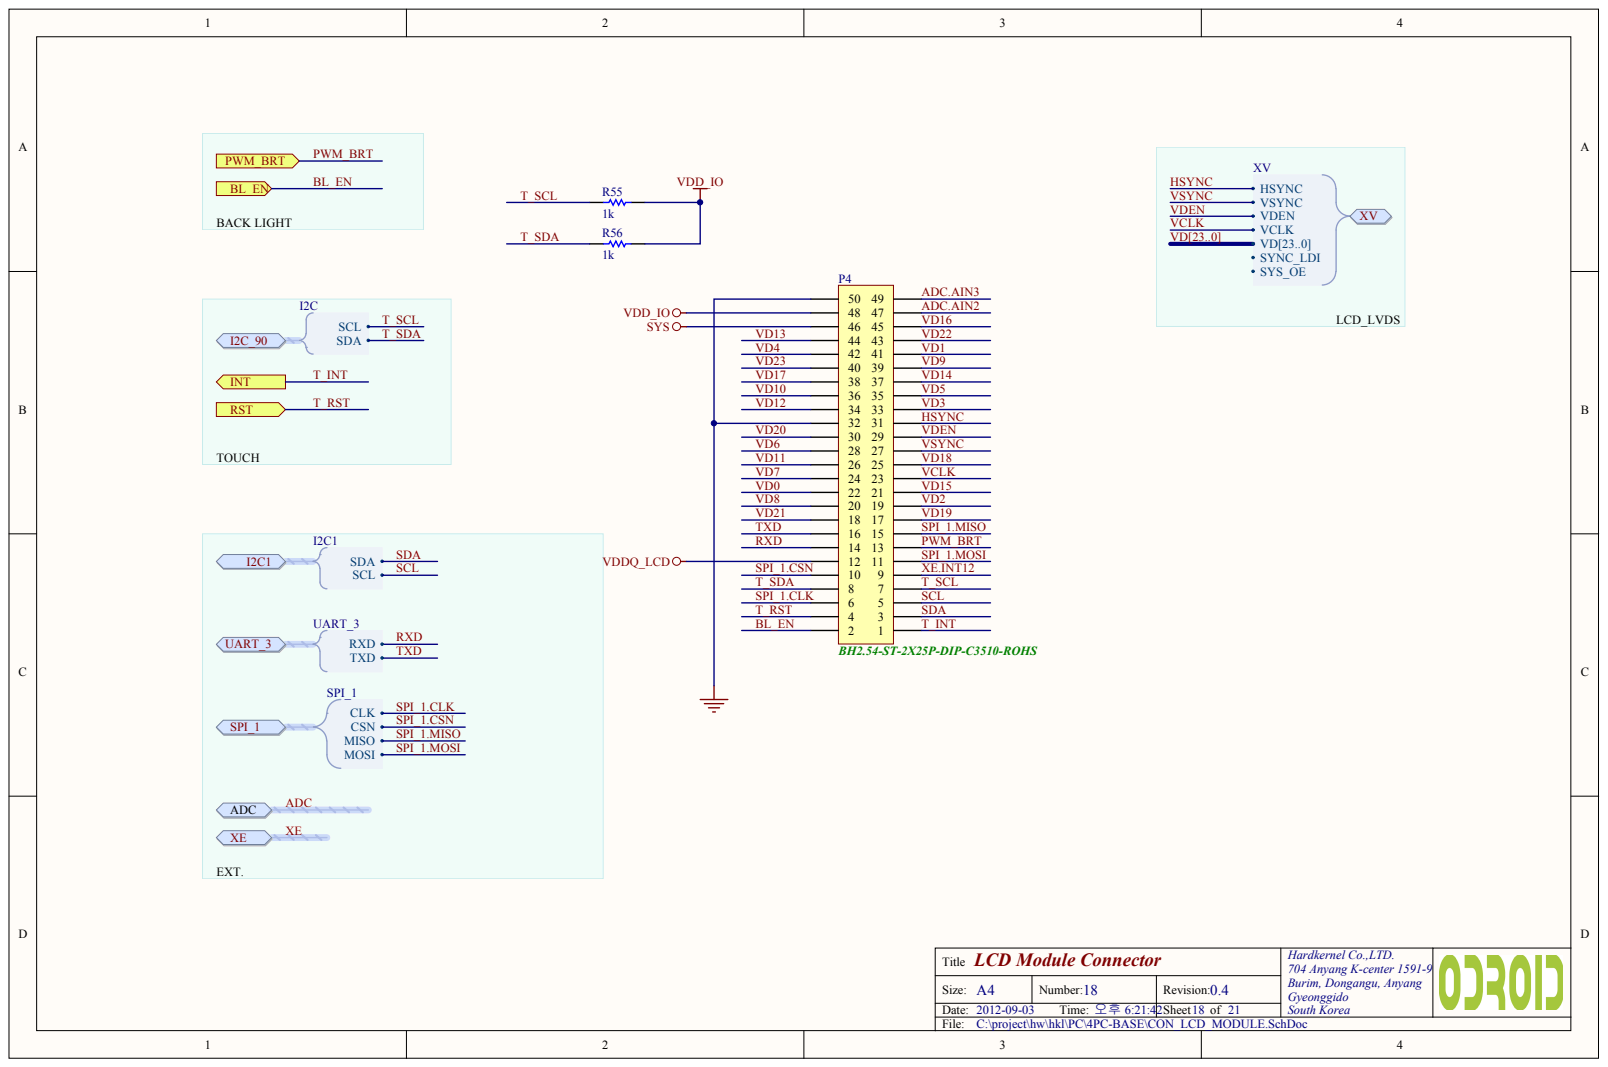
[picture p268: page 22]

LCD Module Connector Title | Hardkernel Co.,LTD. 704 Anyang K-center 1591-9 Burim, Dongangu, Anyang Gyeonggido

A4 Size: | 18 Number: | 0.4 Revision:

C:\project\hw\hkl\PC\4PC-BASE\CON_LCD_MODULE.SchDoc

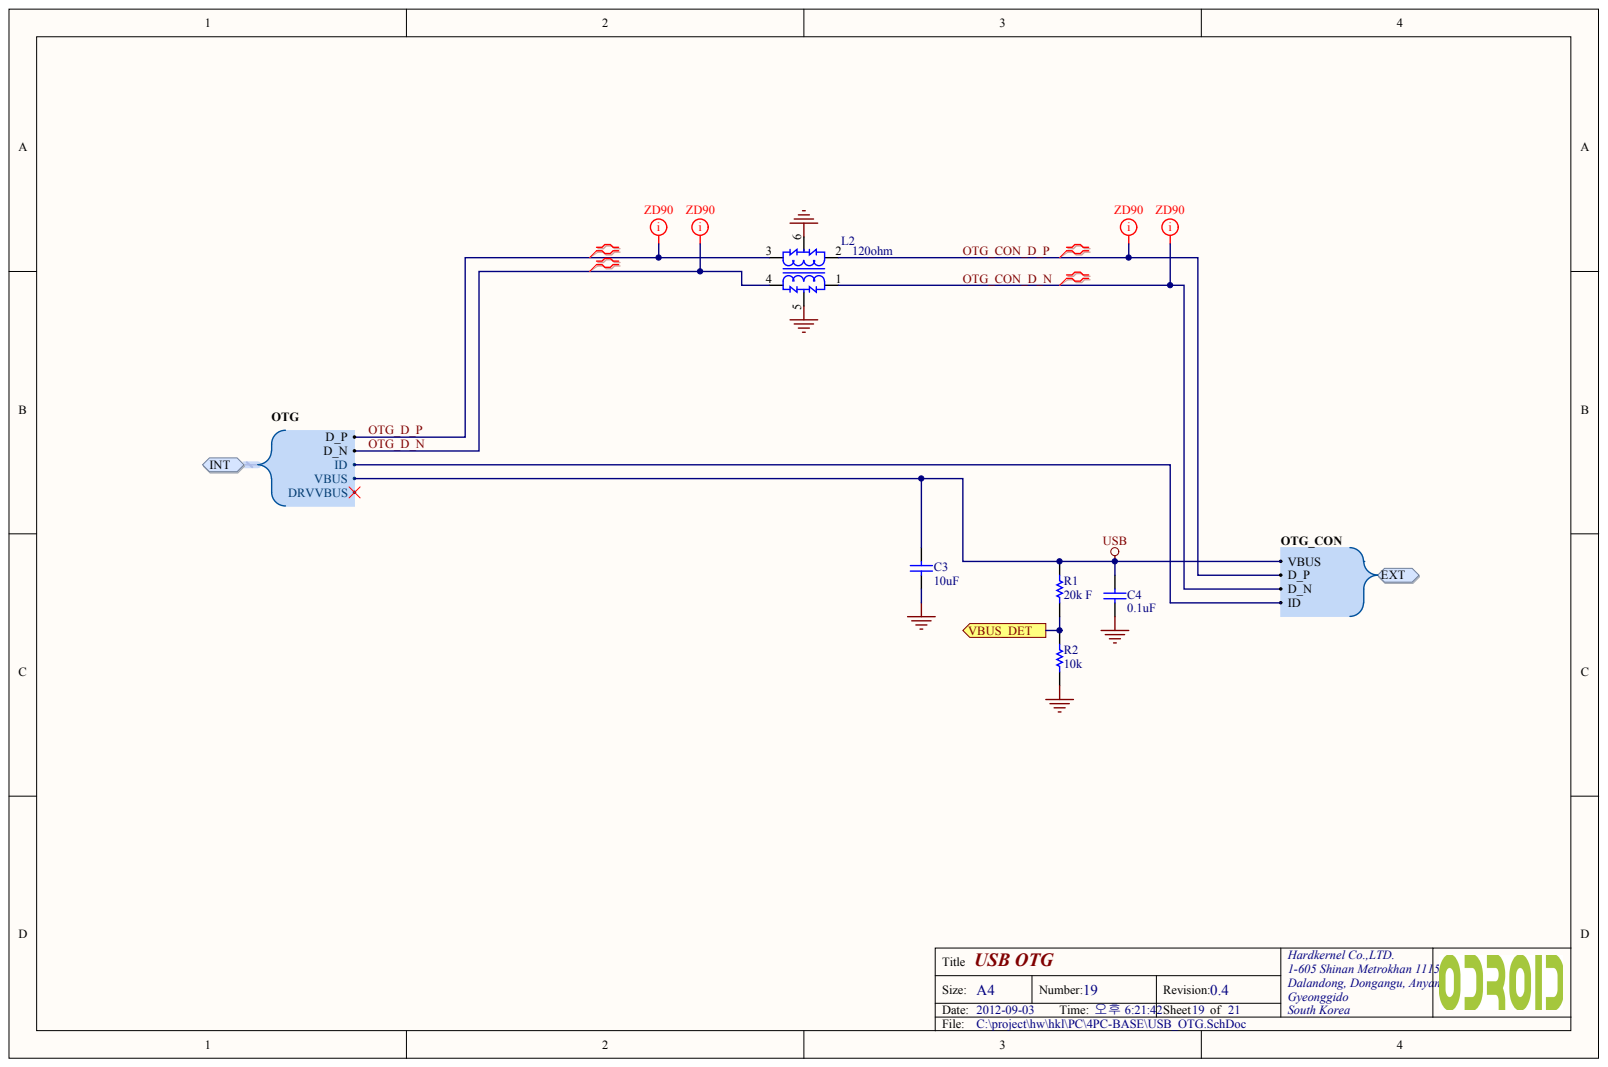
[picture p269: page 23]

USB

C3
10uF R1

USB OTG Title | Hardkernel Co.,LTD. 1-605 Shinan Metrokhan 1115 Dalandong, Dongangu, Anyang Gyeonggido

A4 Size: | 19 Number: | 0.4 Revision:

C:\project\hw\hkl\PC\4PC-BASE\USB_OTG.SchDoc

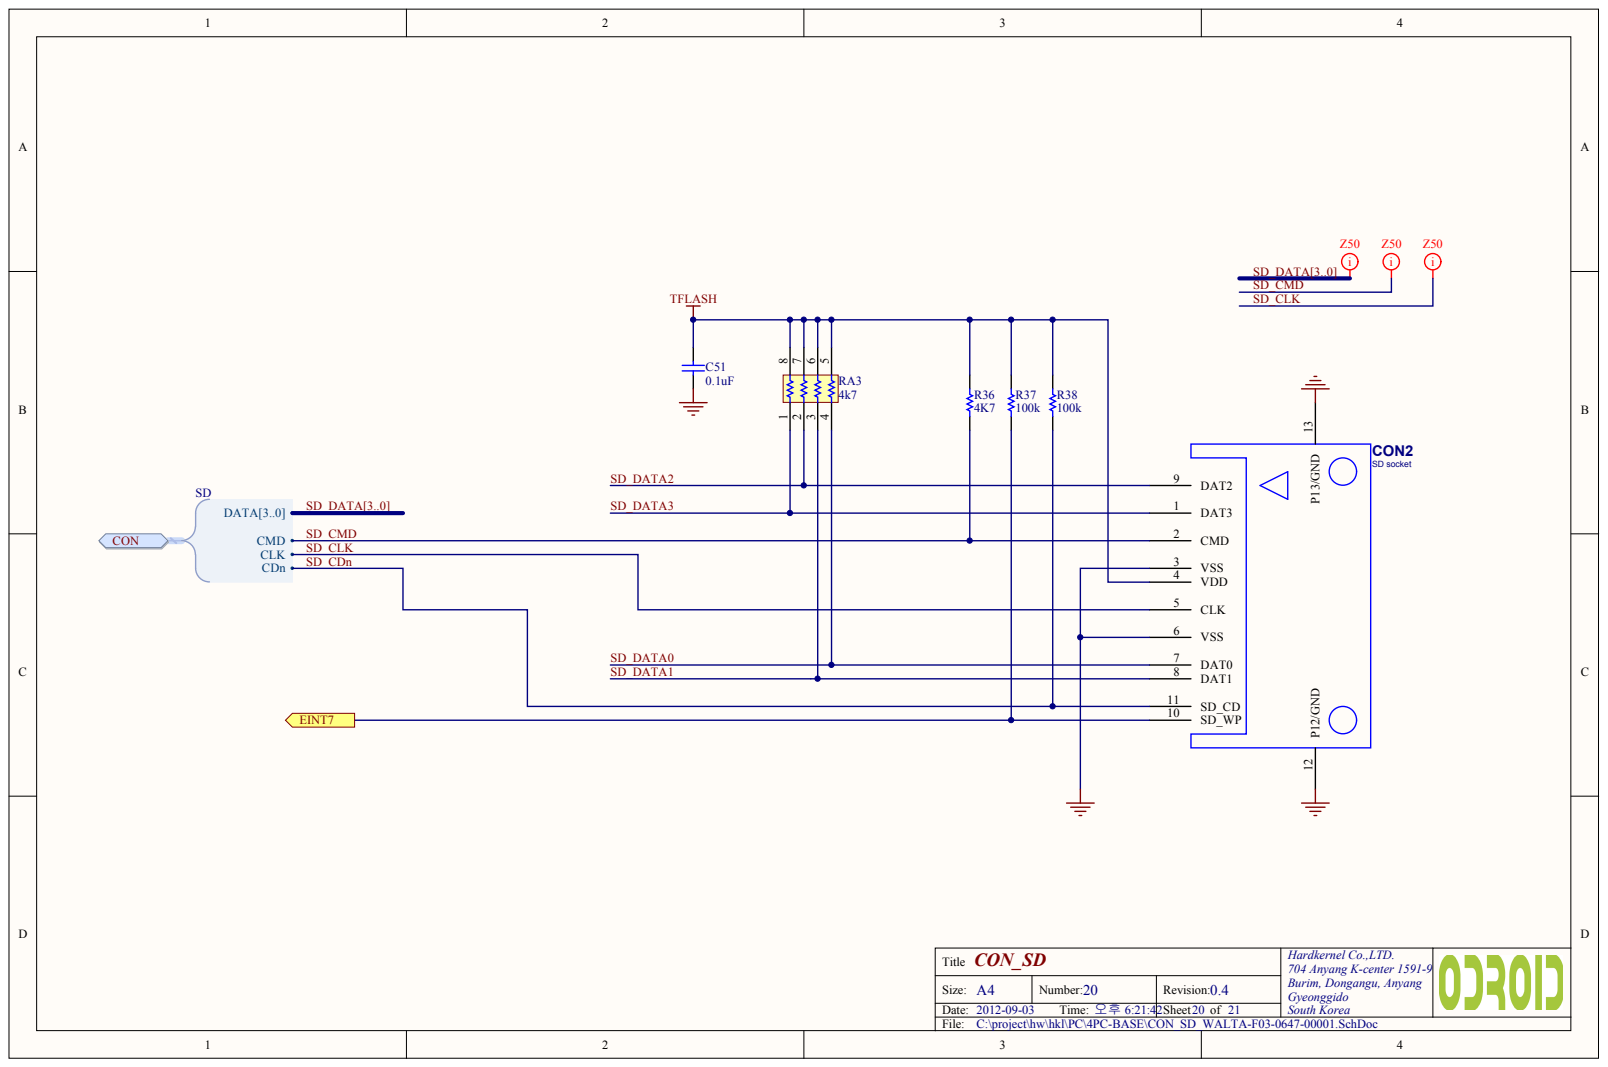
[picture p270: page 24]

SD_CDn

CON_SD Title | Hardkernel Co.,LTD. 704 Anyang K-center 1591-9 Burim, Dongangu, Anyang Gyeonggido

A4 Size: | 20 Number: | 0.4 Revision:

C:\project\hw\hkl\PC\4PC-BASE\CON_SD_WALTA-F03-0647-00001.SchDoc

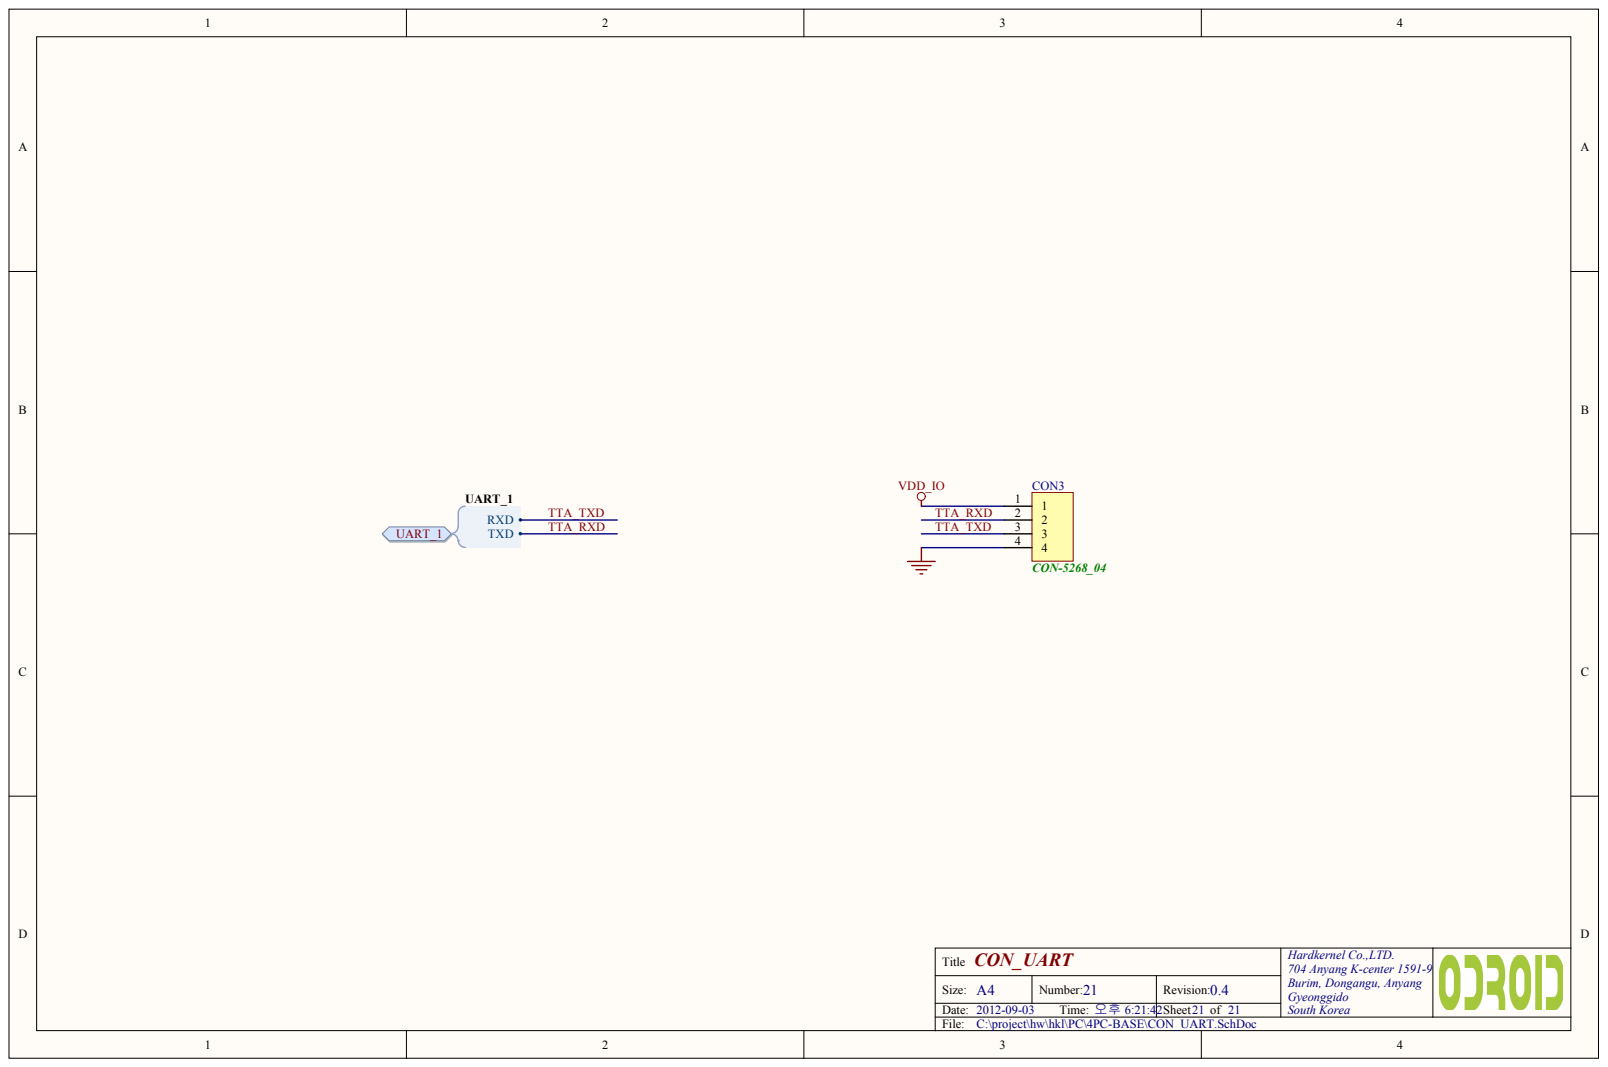
[picture p271: page 25]

CON_UART Title | Hardkernel Co.,LTD. 704 Anyang K-center 1591-9 Burim, Dongangu, Anyang Gyeonggido

A4 Size: | 21 Number: | 0.4 Revision:

C:\project\hw\hkl\PC\4PC-BASE\CON_UART.SchDoc
