MLAB-project/Modules/sensors/MMA6260/hw/cam_ama/O1.pdf

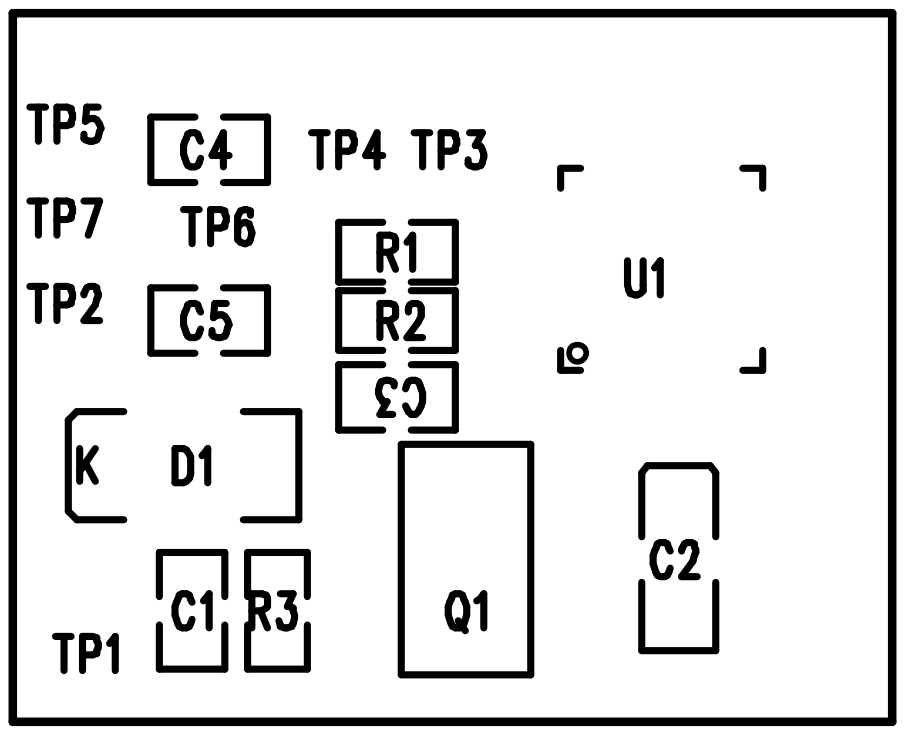
[picture p272: page 1]
