MLAB-project/Modules/comm_serial/I2CHUB01A/hw/cam_ama/V2_AMA.pdf

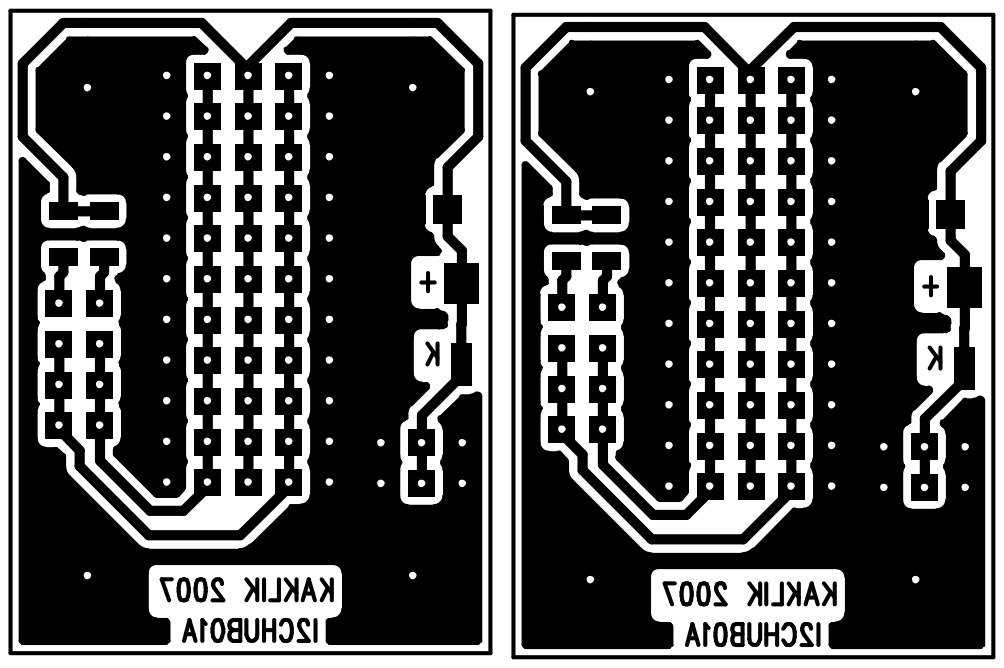
[picture p273: page 1]
