MLAB-project/Modules/human_interface/LEDROBOT/hw/cam_ama/LEDROBOT_T1_AMA.pdf

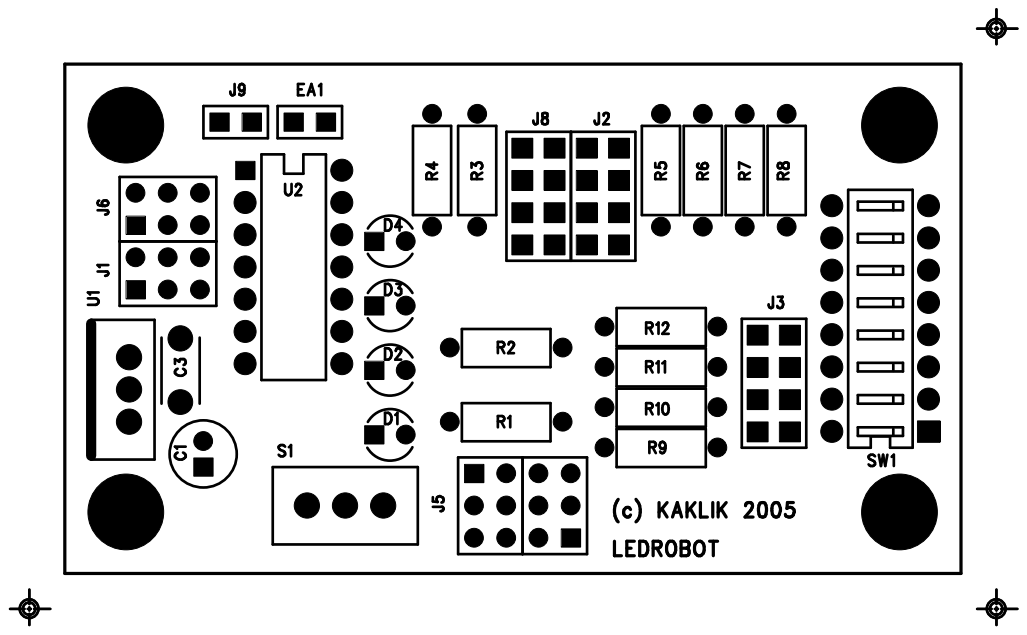
[picture p274: page 1]
