MLAB-project/Modules/human_interface/LEDROBOT/hw/cam_ama/LEDROBOT_V2_AMA.pdf

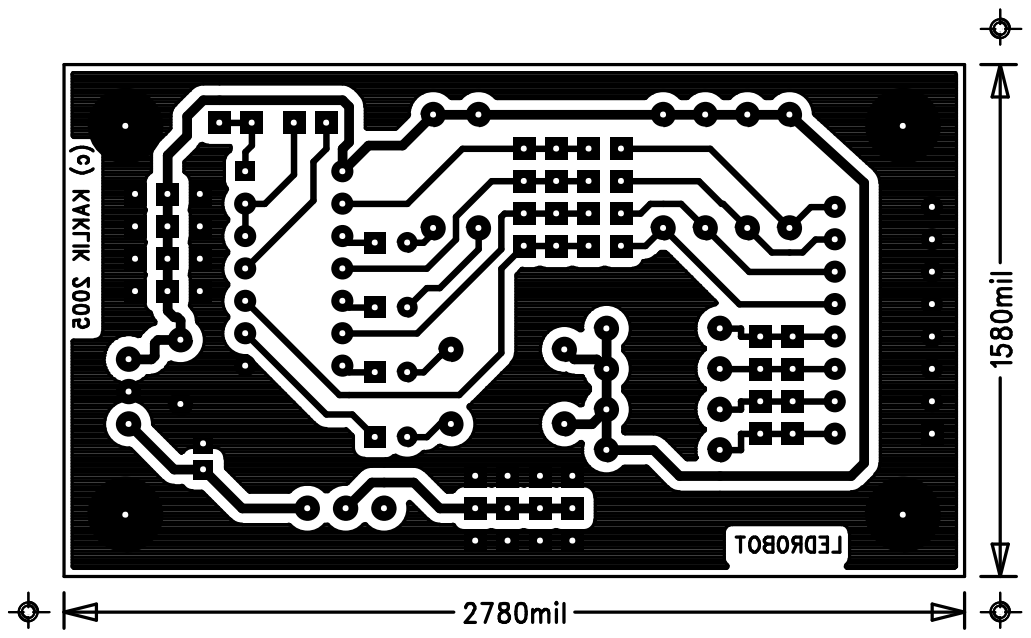
[picture p275: page 1]
