MLAB-project/Modules/human_interface/LEDROBOT/hw/cam_ama/LEDROBOT_V2_REAL.pdf

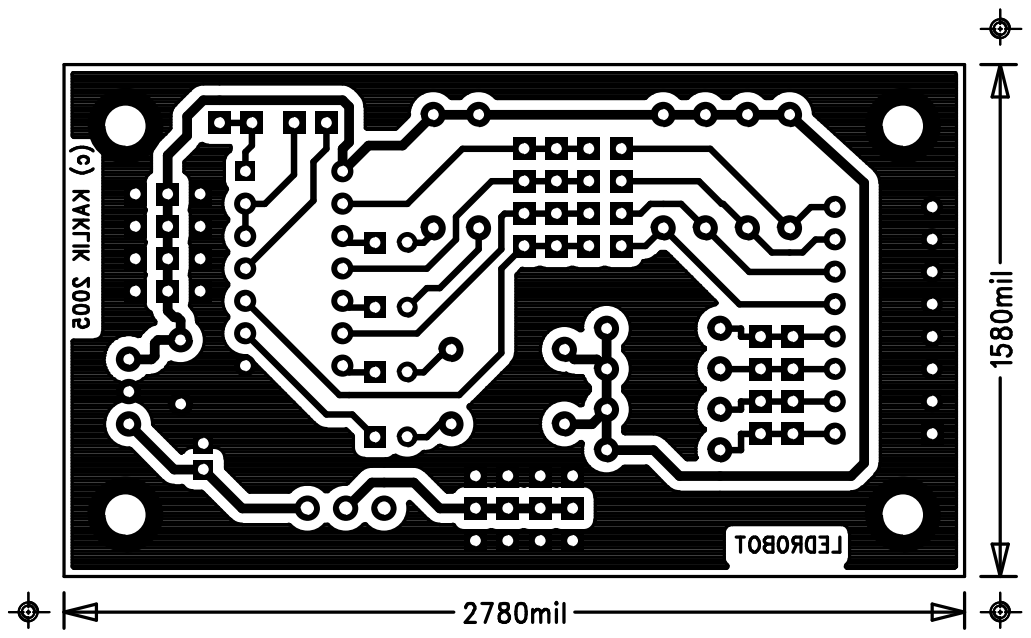
[picture p276: page 1]
